Desval27/FormantKO/panels/COM/README.md

# COM

## Status

⚠️ Untested⚠️

<!--
## Documents
-->

## Gerber To Order

⚠️ Untested⚠️

- [Default](COM_71.0x132.5mm_for_Default.zip)
- [Elecrow](COM_71.0x132.5mm_for_Elecrow.zip)
- [FusionPCB](COM_71.0x132.5mm_for_FusionPCB.zip)
- [JLCPCB](COM_71.0x132.5mm_for_JLCPCB.zip)
- [PCBWay](COM_71.0x132.5mm_for_PCBWay.zip)

## Images

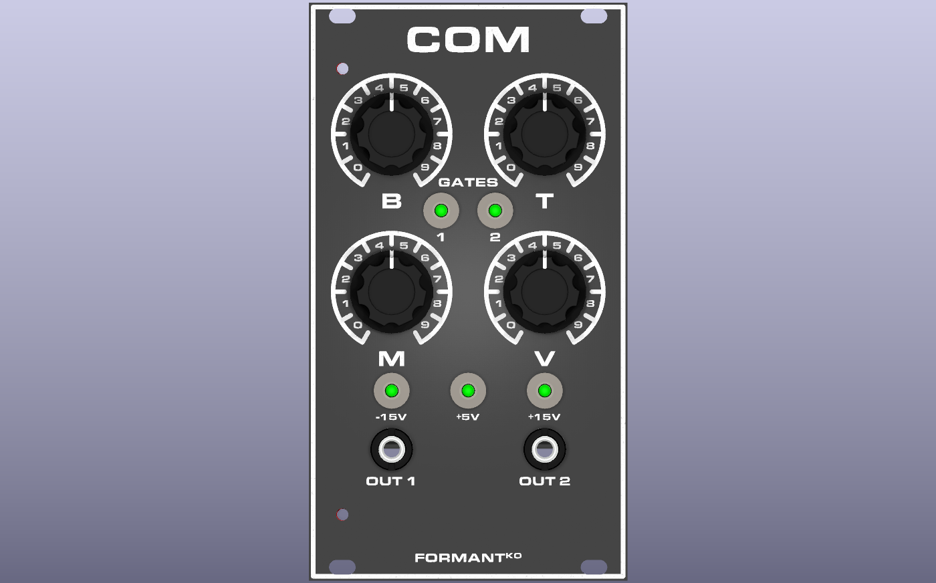
[picture p23: panels/COM/COM_front.png]
Rendered Panel Front


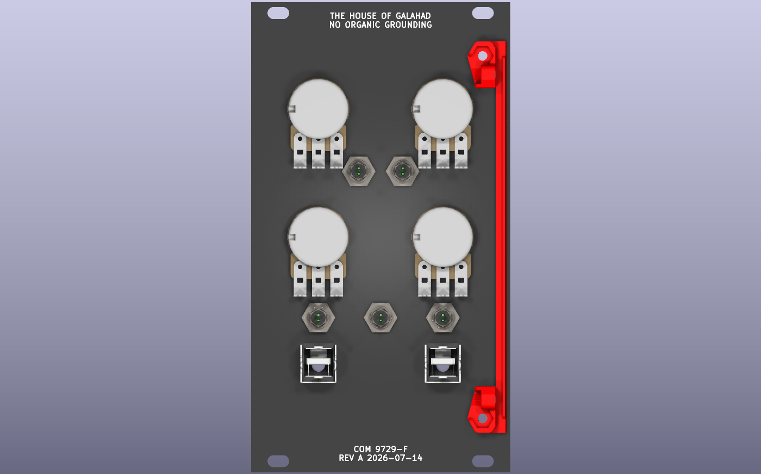
[picture p24: panels/COM/COM_back.png]
Rendered Panel Back
