Desval27/FormantKO/panels/DUAL_VCA/README.md

# DUAL-VCA

Format: 3U

## Status

⚠️ Untested⚠️

<!--
## Documents
-->

## Gerber To Order

⚠️ Untested⚠️

- [Default](gerber_to_order/DUAL_VCA_70.78x128.4mm_for_Default.zip)
- [Elecrow](gerber_to_order/DUAL_VCA_70.78x128.4mm_for_Elecrow.zip)
- [FusionPCB](gerber_to_order/DUAL_VCA_70.78x128.4mm_for_FusionPCB.zip)
- [JLCPCB](gerber_to_order/DUAL_VCA_70.78x128.4mm_for_JLCPCB.zip)
- [PCBWay](gerber_to_order/DUAL_VCA_70.78x128.4mm_for_PCBWay.zip)

## Images

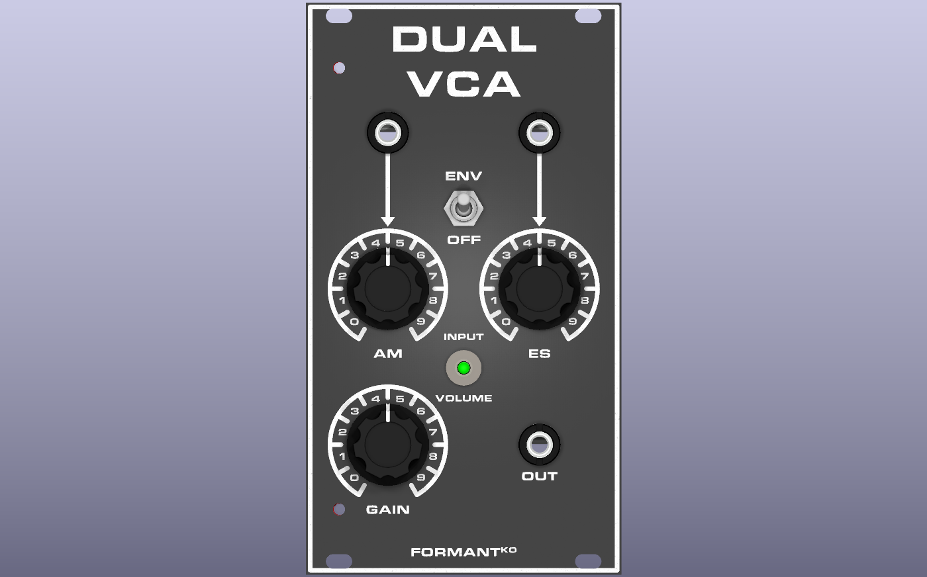
[picture p27: panels/DUAL_VCA/DUAL_VCA_front.png]
Rendered Panel Front


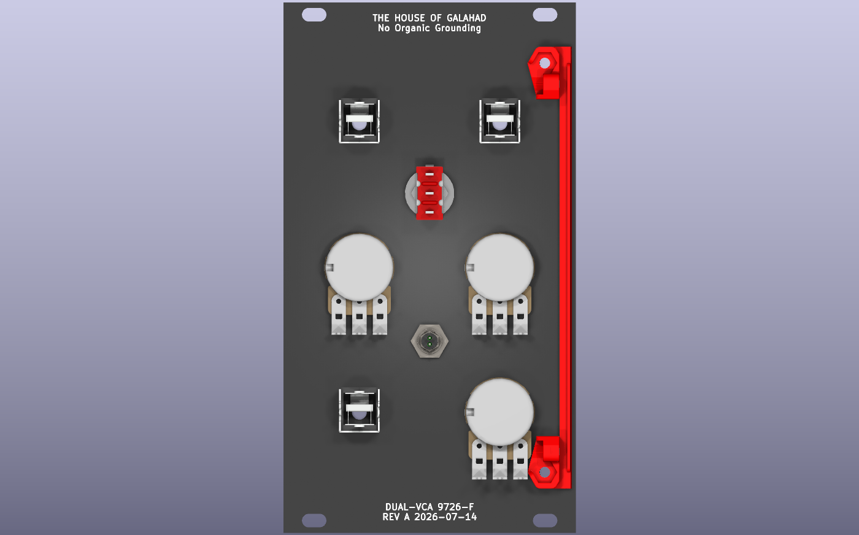
[picture p28: panels/DUAL_VCA/DUAL_VCA_back.png]
Rendered Panel Back
