Desval27/FormantKO/panels/ADSR/README.md

# ADSR

Formant: 3U

### Modifications

- Add external gate input.  This is normalized and will disconnect any existing internal gate bus assignment.

## Status

⚠️ Untested⚠️

## Gerber to Order

⚠️ Untested⚠️

- [Default](gerber_to_order/ADSR_70.78x128.4mm_for_Default.zip)
- [Elecrow](gerber_to_order/ADSR_70.78x128.4mm_for_Elecrow.zip)
- [FusionPCB](gerber_to_order/ADSR_70.78x128.4mm_for_FusionPCB.zip)
- [JLCPCB](gerber_to_order/ADSR_70.78x128.4mm_for_JLCPCB.zip)
- [PCBWay](gerber_to_order/ADSR_70.78x128.4mm_for_PCBWay.zip)

## Images

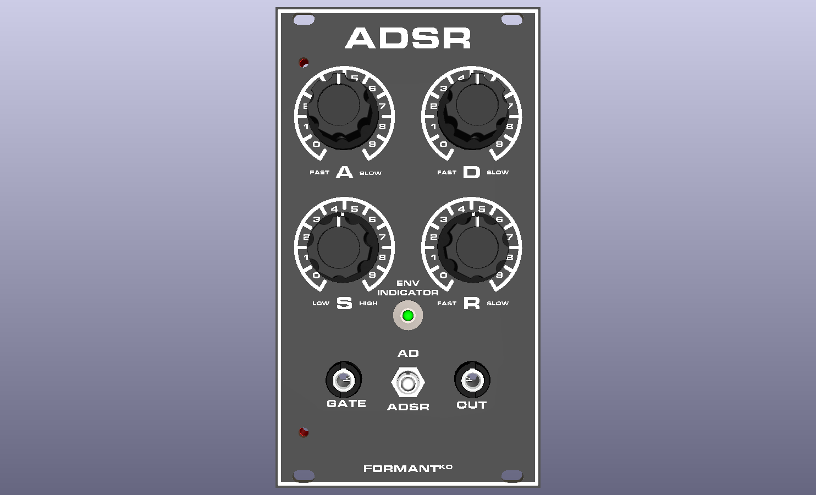
[picture p29: panels/ADSR/ADSR_front.png]
Rendered Panel Front


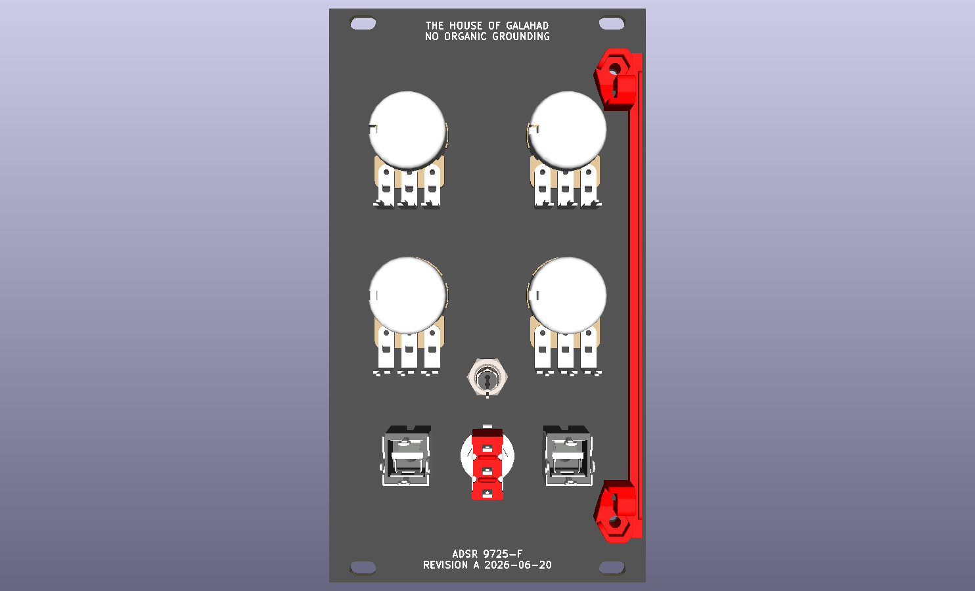
[picture p30: panels/ADSR/ADSR_back.png]
Rendered Panel Back
