Desval27/FormantKO/modules/SEQUENCER/README.md

# 256 Step Sequencer

A digital sequencer for voltage-controlled music synthesizers that can store and automatically play back up to 256 notes.

## Status

⚠️ Incomplete ⚠️

## Documents

- [English Translation](SEQUENCER_en.pdf)
- [Schematic](plots/SEQUENCER__schematic.pdf)
<!-- - [Assembly](plots/SEQUENCER__Assembly.pdf) -->
<!-- - [Interactive Bill of Materials](bom/ibom.html) -->

## Gerber to Order

⚠️ Untested ⚠️

## Images

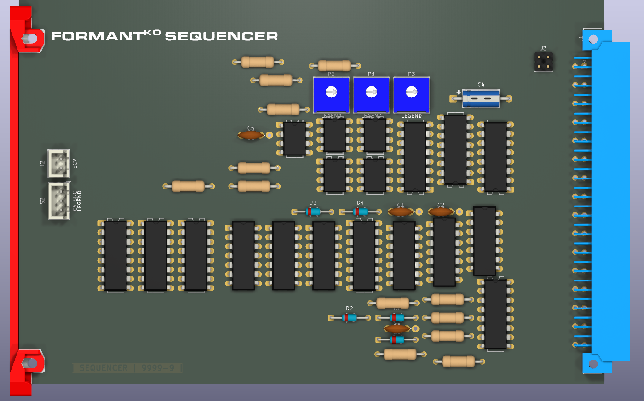
[picture p35: modules/SEQUENCER/SEQUENCER_top.png]
Rendered PCB Top


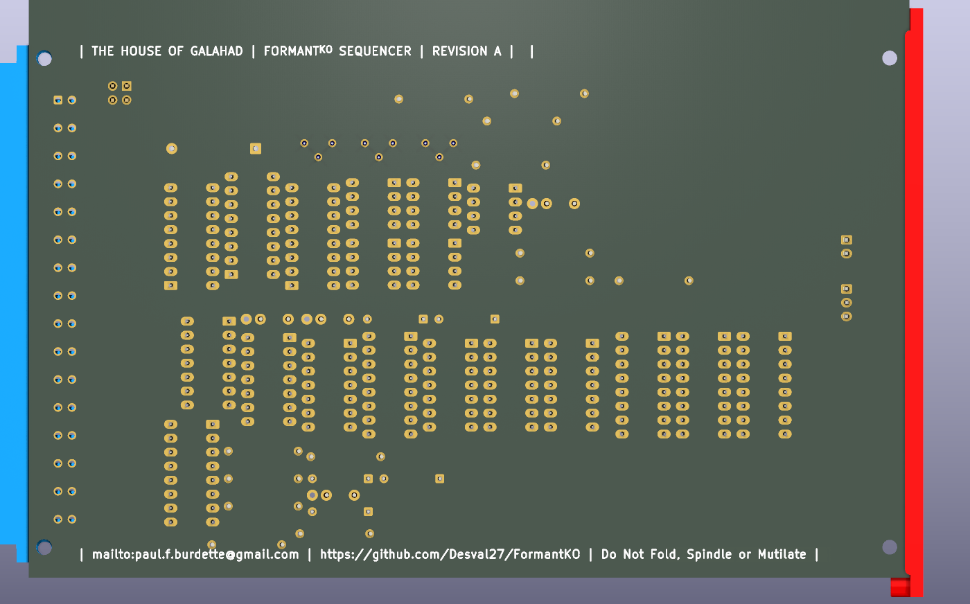
[picture p36: modules/SEQUENCER/SEQUENCER_bottom.png]
Rendered PCB Bottom
