Desval27/FormantKO/system/CARD_EXTENDER/README.md

# CARD-EXTENDER

A card extender is a simple debugging aid that plugs into the system backplane and provides a second connector into which a module is inserted. This moves the module outside of the card cage, allowing it to operate normally while all of its components and test points remain fully accessible.

For synthesizer systems such as the Formant, a card extender is invaluable during development, calibration, and troubleshooting. It allows oscilloscopes, multimeters, and logic analyzers to be connected without the module being buried inside the rack. Components can be adjusted, voltages measured, and signals traced while the module is running under normal operating conditions.

Although not required for everyday use, a card extender is one of the most useful service tools for anyone building, repairing, or modifying Formant modules.

## STATUS

⚠️ Untested⚠️

But possibly ready to get first samples...

## Documents

- [Schematic](plots/CARD_EXTENDER__schematic.pdf)
- [Assembly](plots/CARD_EXTENDER__Assembly.pdf)
- [Interactive Bill of Materials](bom/ibom.html)

## Gerber to Order

- [Default](gerber_to_order/CARD_EXTENDER_160.0x100.0mm_for_Default.zip)
- [Elecrow](gerber_to_order/CARD_EXTENDER_160.0x100.0mm_for_Elecrow.zip)
- [FusionPCB](gerber_to_order/CARD_EXTENDER_160.0x100.0mm_for_FusionPCB.zip)
- [JLCPCB](gerber_to_order/CARD_EXTENDER_160.0x100.0mm_for_JLCPCB.zip)
- [PCBWay](gerber_to_order/CARD_EXTENDER_160.0x100.0mm_for_PCBWay.zip)

## Images

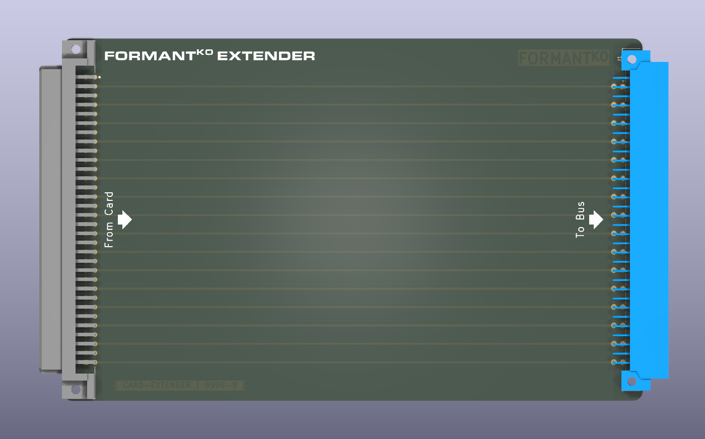
[picture p37: system/CARD_EXTENDER/CARD_EXTENDER_top.png]
Rendered PCB Top


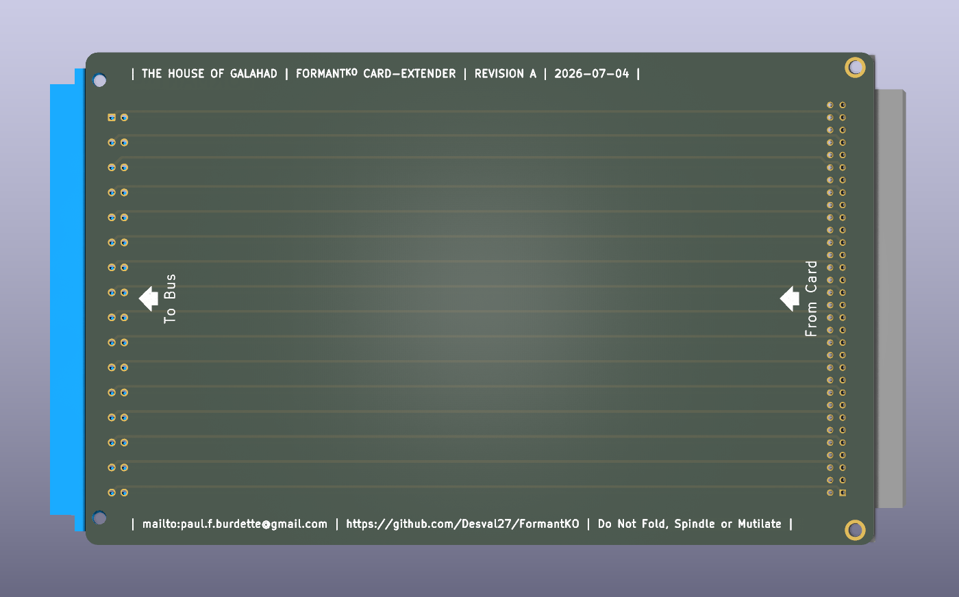
[picture p38: system/CARD_EXTENDER/CARD_EXTENDER_bottom.png]
Rendered PCB Bottom
