Desval27/FormantKO/modules/NOISE_DNG/README.md

# NOISE-DNG

## Status

⚠️ Untested ⚠️

## Documents

- [Translated Document](NOISE_DNG_translated.pdf)
- [Schematic](NOISE_DNG_schematic.pdf)
- [Assembly](plots/NOISE_DNG__Assembly.pdf)
- [Interactive Bill of Materials](bom/ibom.html)

## Gerber to Order

⚠️ Untested ⚠️

- [Default](gerber_to_order/NOISE_DNG_100.0x40.0mm_for_Default.zip)
- [Elecrow](gerber_to_order/NOISE_DNG_100.0x40.0mm_for_Elecrow.zip)
- [FusionPCB](gerber_to_order/NOISE_DNG_100.0x40.0mm_for_FusionPCB.zip)
- [JLCPCB](gerber_to_order/NOISE_DNG_100.0x40.0mm_for_JLCPCB.zip)
- [PCBWay](gerber_to_order/NOISE_DNG_100.0x40.0mm_for_PCBWay.zip)

## Images

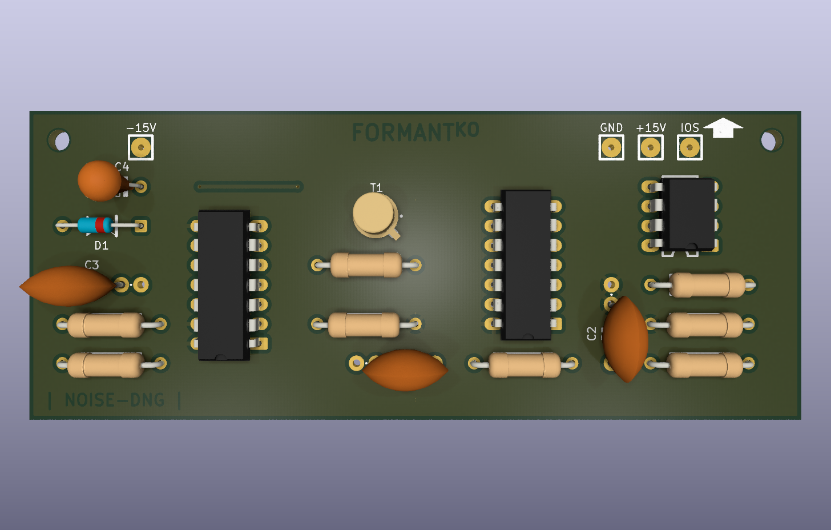
[picture p41: modules/NOISE_DNG/NOISE_DNG_top.png]
Rendered PCB Top


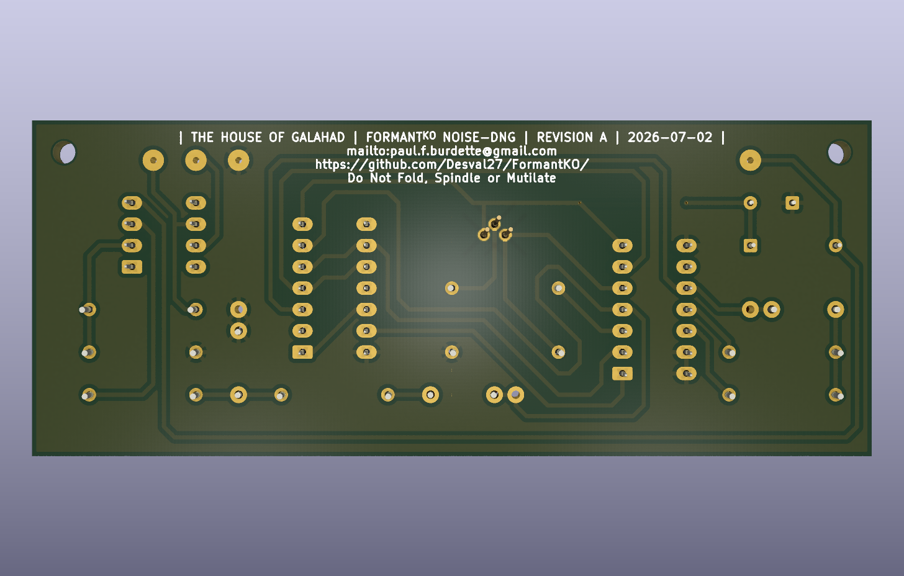
[picture p42: modules/NOISE_DNG/NOISE_DNG_bottom.png]
Rendered PCB Bottom
