Desval27/FormantKO/modules/VCF_24/README.md

# VCF 24dB

## Status

⚠️ Incomplete ⚠️

## Documents

<!--
- [Schematic](schematic.pdf)
- [Assembly](plots/VCF_24__Assembly.pdf)
- [Interactive Bill of Materials](bom/ibom.html)
-->

## Gerber to Order

⚠️ Untested ⚠️

## Images

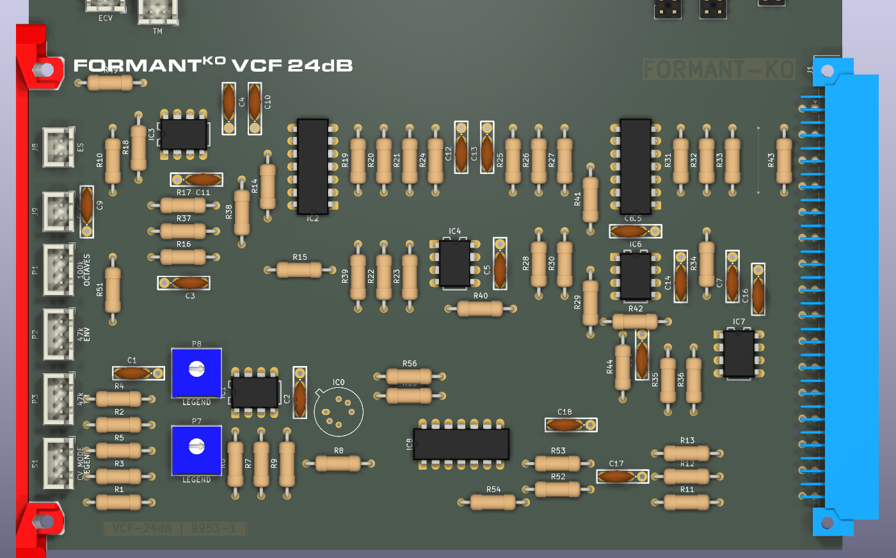
[picture p43: modules/VCF_24/VCF_24_top.png]
Rendered PCB Top


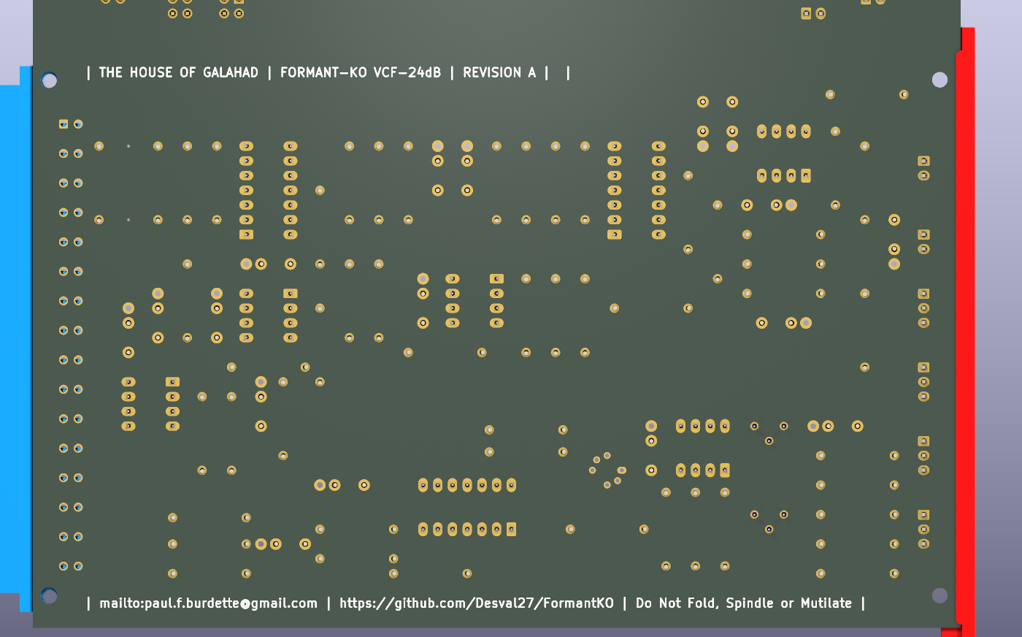
[picture p44: modules/VCF_24/VCF_24_bottom.png]
Rendered PCB Bottom
