Desval27/FormantKO/modules/VCF_12/README.md

# VCF 12dB

## Status

⚠️ Untested ⚠️

## Documents

- [Schematic](schematic.pdf)
- [Assembly](plots/VCF_12__Assembly.pdf)
- [Interactive Bill of Materials](bom/ibom.html)

## Gerber to Order

⚠️ Untested ⚠️

- [Default](gerber_to_order/VCF_12_160.0x233.35mm_for_Default.zip)
- [Elecrow](gerber_to_order/VCF_12_160.0x233.35mm_for_Elecrow.zip)
- [FusionPCB](gerber_to_order/VCF_12_160.0x233.35mm_for_FusionPCB.zip)
- [JLCPCB](gerber_to_order/VCF_12_160.0x233.35mm_for_JLCPCB.zip)
- [PCBWay](gerber_to_order/VCF_12_160.0x233.35mm_for_PCBWay.zip)

## Images

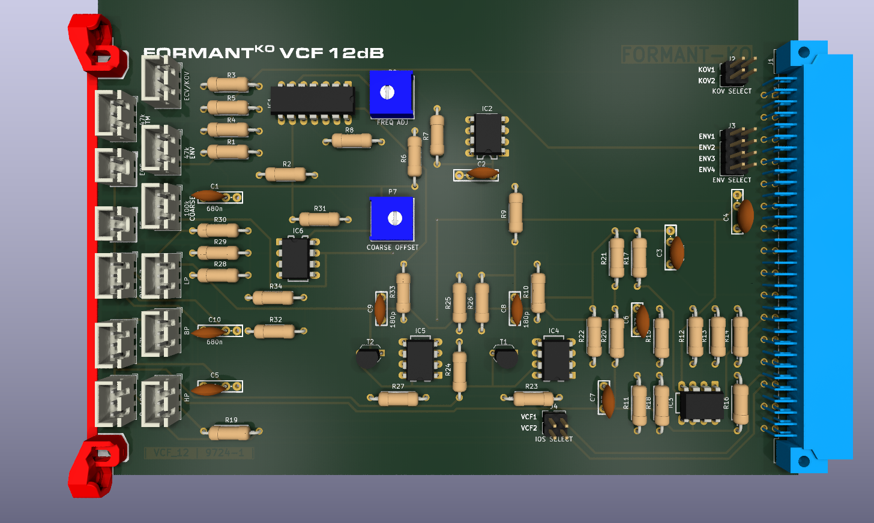
[picture p45: modules/VCF_12/VCF_12_top.png]
Rendered PCB Top


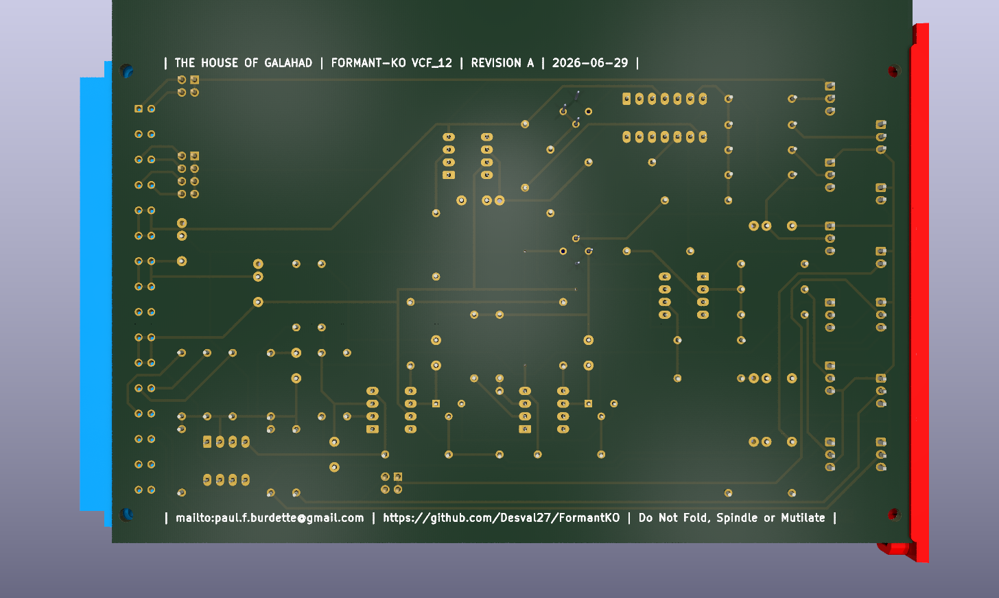
[picture p46: modules/VCF_12/VCF_12_bottom.png]
Rendered PCB Bottom
