Desval27/FormantKO/panels/MULTIPLE_JACKS_3U/README.md

# MULTIPLE-JACKS 3U

## Status

⚠️ Untested⚠️

## Documents

- [Assembly](plots/MULTIPLE_JACKS_3U__Assembly.pdf)

## Gerber To Order

- [Default](gerber_to_order/MULTIPLE_JACKS_3U_70.78x128.4mm_for_Default.zip)
- [Elecrow](gerber_to_order/MULTIPLE_JACKS_3U_70.78x128.4mm_for_Elecrow.zip)
- [FusionPCB](gerber_to_order/MULTIPLE_JACKS_3U_70.78x128.4mm_for_FusionPCB.zip)
- [JLCPCB](gerber_to_order/MULTIPLE_JACKS_3U_70.78x128.4mm_for_JLCPCB.zip)
- [PCBWay](gerber_to_order/MULTIPLE_JACKS_3U_70.78x128.4mm_for_PCBWay.zip)

## Images

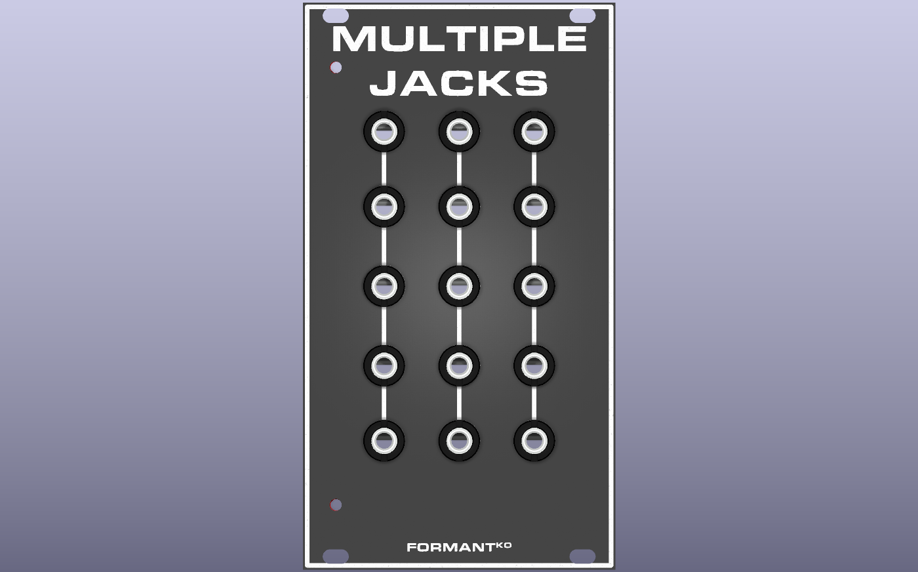
[picture p51: panels/MULTIPLE_JACKS_3U/MULTIPLE_JACKS_3U_front.png]
Rendered Front Panel

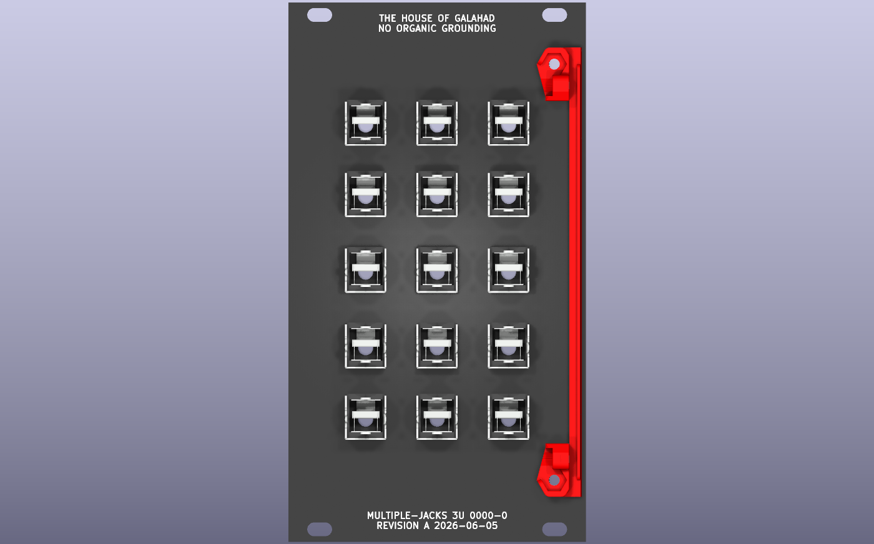
[picture p52: panels/MULTIPLE_JACKS_3U/MULTIPLE_JACKS_3U_back.png]
Rendered Back Panel
