Desval27/FormantKO/panels/MULTIPLE_JACKS_6U/README.md

# MULTIPLE-JACKS 6U

## Status

⚠️ Untested⚠️

## Documents

- [Assembly](plots/MULTIPLE_JACKS_6U__Assembly.pdf)

## Gerber To Order

- [Default](gerber_to_order/MULTIPLE_JACKS_6U_70.78x261.75mm_for_Default.zip)
- [Elecrow](gerber_to_order/MULTIPLE_JACKS_6U_70.78x261.75mm_for_Elecrow.zip)
- [FusionPCB](gerber_to_order/MULTIPLE_JACKS_6U_70.78x261.75mm_for_FusionPCB.zip)
- [JLCPCB](gerber_to_order/MULTIPLE_JACKS_6U_70.78x261.75mm_for_JLCPCB.zip)
- [PCBWay](gerber_to_order/MULTIPLE_JACKS_6U_70.78x261.75mm_for_PCBWay.zip)

## Images

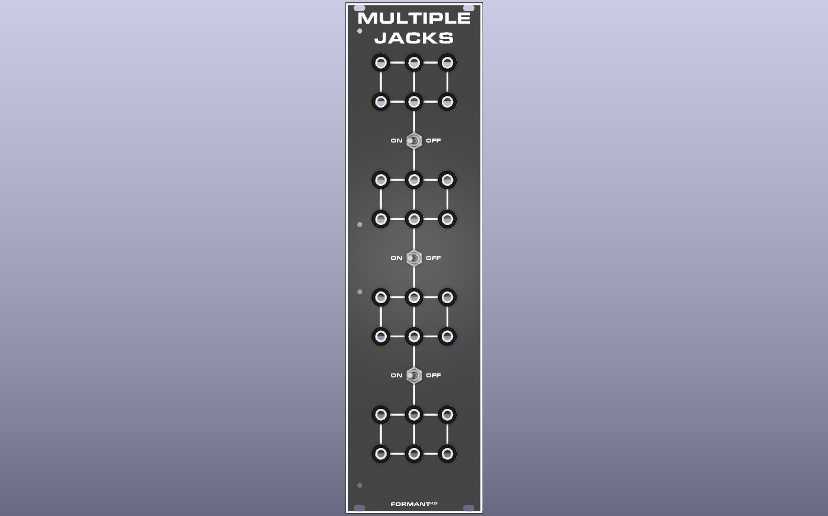
[picture p53: panels/MULTIPLE_JACKS_6U/MULTIPLE_JACKS_6U_front.png]
Rendered Front Panel

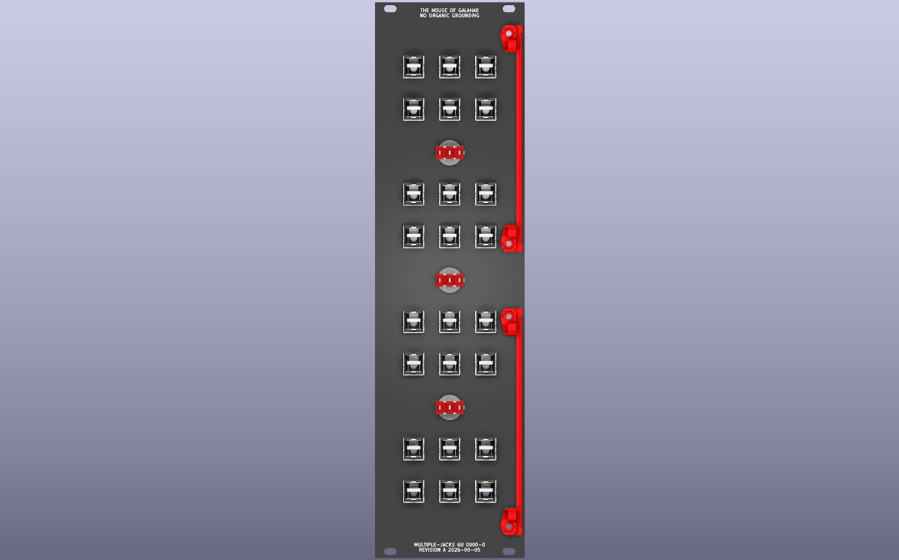
[picture p54: panels/MULTIPLE_JACKS_6U/MULTIPLE_JACKS_6U_back.png]
Rendered Back Panel
