Desval27/FormantKO/panels/PHASE_SHIFTER/README.md

# PHASE-SHIFTER

## Status

⚠️ Untested⚠️

## Documents

- [Assembly](plots/PHASE_SHIFTER__Assembly.pdf)

## Gerber To Order

- [Default](gerber_to_order/PHASE_SHIFTER_70.78x128.4mm_for_Default.zip)
- [Elecrow](gerber_to_order/PHASE_SHIFTER_70.78x128.4mm_for_Elecrow.zip)
- [FusionPCB](gerber_to_order/PHASE_SHIFTER_70.78x128.4mm_for_FusionPCB.zip)
- [JLCPCB](gerber_to_order/PHASE_SHIFTER_70.78x128.4mm_for_JLCPCB.zip)
- [PCBWay](gerber_to_order/PHASE_SHIFTER_70.78x128.4mm_for_PCBWay.zip)

## Images

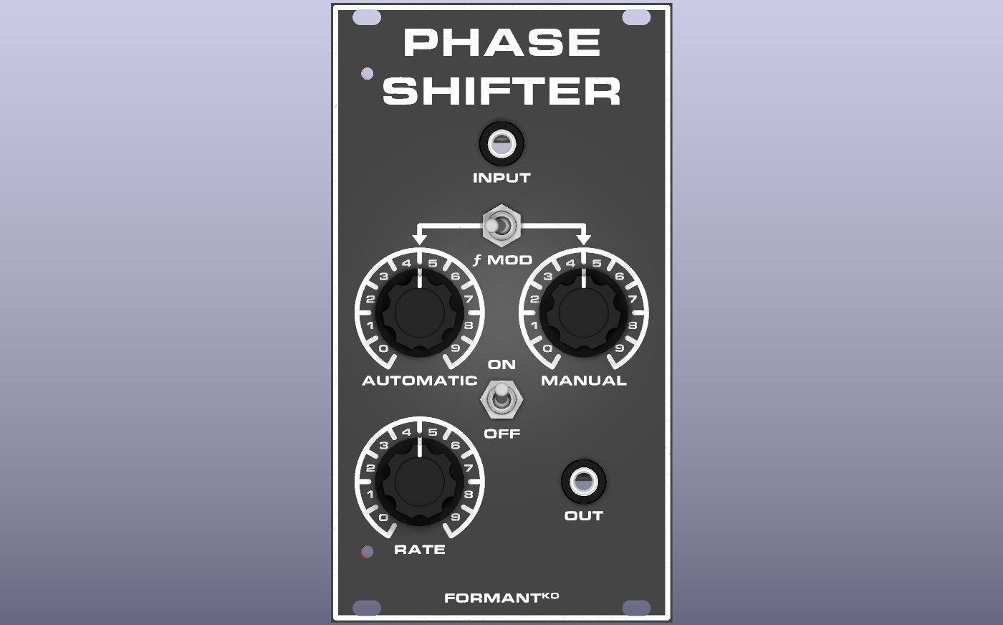
[picture p55: panels/PHASE_SHIFTER/PHASE_SHIFTER_front.png]
Rendered Front Panel

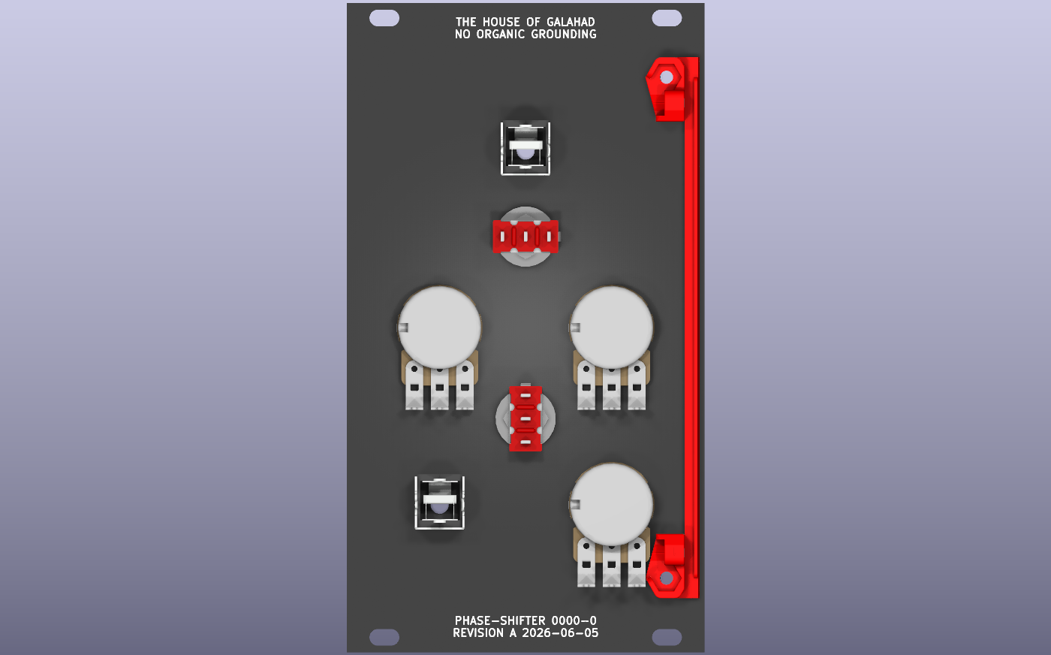
[picture p56: panels/PHASE_SHIFTER/PHASE_SHIFTER_back.png]
Rendered Back Panel
