Desval27/FormantKO/modules/RING_MODULATOR/README.md

# RING-MODULATOR

## STATUS

⚠️ Incomplete⚠️

## Documents

- [Translated Source](RING_MODULATOR_translated.pdf)
- [Schematic](RING_MODULATOR.pdf)
- [Assembly](plots/RING_MODULATOR__Assembly.pdf)
- [Interactive Bill of Materials](bom/ibom.html)

## Gerber to Order

⚠️ Untested⚠️

- [Default](gerber_to_order/RING_MODULATOR_160.0x100.0mm_for_Default.zip)
- [Elecrow](gerber_to_order/RING_MODULATOR_160.0x100.0mm_for_Elecrow.zip)
- [FusionPCB](gerber_to_order/RING_MODULATOR_160.0x100.0mm_for_FusionPCB.zip)
- [JLCPCB](gerber_to_order/RING_MODULATOR_160.0x100.0mm_for_JLCPCB.zip)
- [PCBWay](gerber_to_order/RING_MODULATOR_160.0x100.0mm_for_PCBWay.zip)

## Images

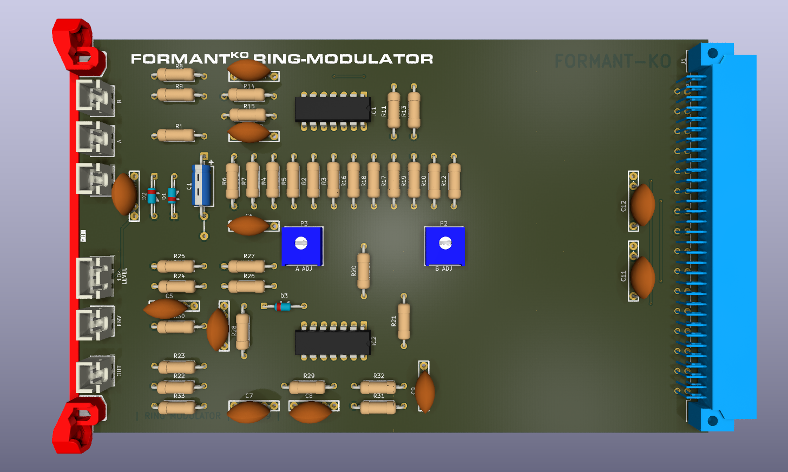
[picture p57: modules/RING_MODULATOR/RING_MODULATOR_top.png]
Rendered PCB Top

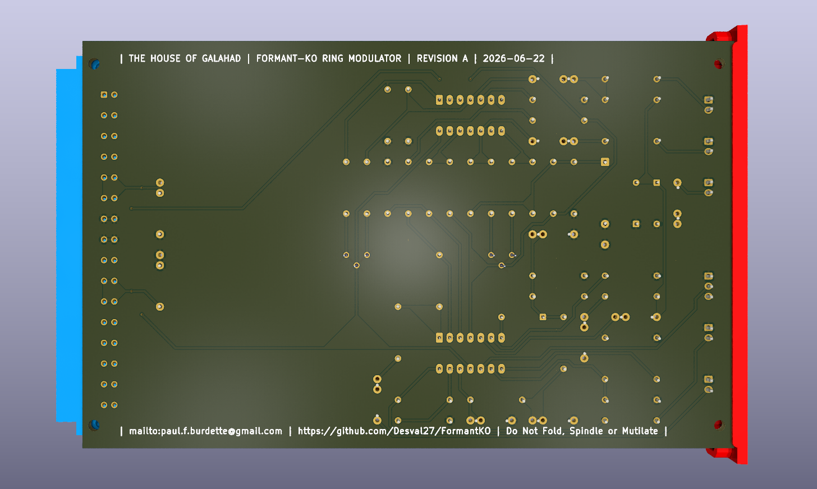
[picture p58: modules/RING_MODULATOR/RING_MODULATOR_bottom.png]
Rendered PCB Bottom
