Desval27/FormantKO/panels/RING_MODULATOR/README.md

# RING-MODULATOR

## Status

⚠️Incomplete⚠️

## Documents

- [Assembly](plots/RING_MODULATOR__Assembly.pdf)

## Gerber To Order

- [Default](gerber_to_order/RING_MODULATOR_70.78x128.4mm_for_Default.zip)
- [Elecrow](gerber_to_order/RING_MODULATOR_70.78x128.4mm_for_Elecrow.zip)
- [FusionPCB](gerber_to_order/RING_MODULATOR_70.78x128.4mm_for_FusionPCB.zip)
- [JLCPCB](gerber_to_order/RING_MODULATOR_70.78x128.4mm_for_JLCPCB.zip)
- [PCBWay](gerber_to_order/RING_MODULATOR_70.78x128.4mm_for_PCBWay.zip)

⚠️Untested⚠️

## Images

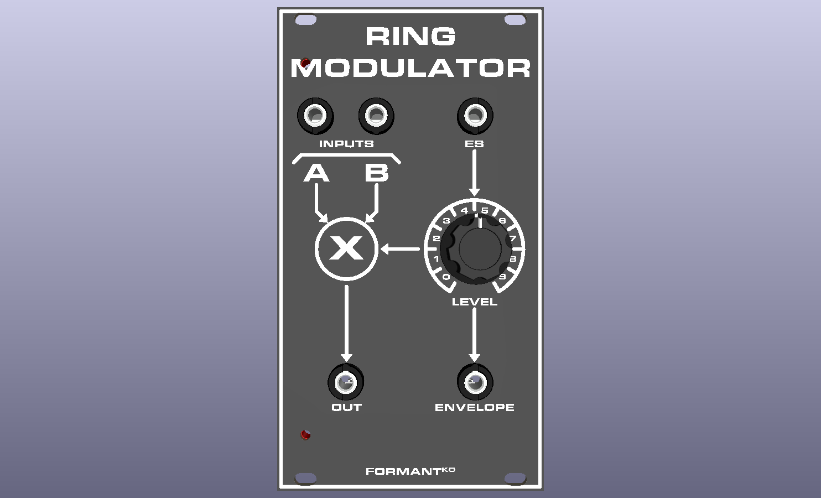
[picture p59: panels/RING_MODULATOR/RING_MODULATOR_front.png]
Rendered Front Panel

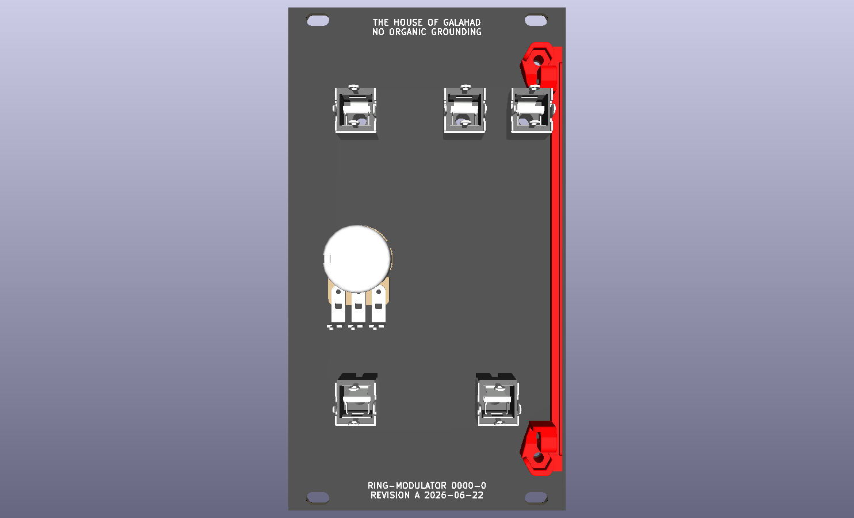
[picture p60: panels/RING_MODULATOR/RING_MODULATOR_back.png]
Rendered Back Panel
