Desval27/FormantKO/modules/NOISE_CNC/README.md

# NOISE EXTENSION - COLOURED NOISE CONTROL

## Status

⚠️ Incomplete⚠️

## Documents

- [Translated Source](NOISE_CNC_translated.pdf)
- [Schematic](NOISE_CNC.pdf)
- [Assembly](plots/NOISE_CNC__Assembly.pdf)
- [Interactive Bill of Materials](bom/ibom.html)

## Gerber to Order

⚠️ Untested⚠️

- [Default](gerber_to_order/NOISE_CNC_100.0x38.0mm_for_Default.zip)
- [Elecrow](gerber_to_order/NOISE_CNC_100.0x38.0mm_for_Elecrow.zip)
- [FusionPCB](gerber_to_order/NOISE_CNC_100.0x38.0mm_for_FusionPCB.zip)
- [JLCPCB](gerber_to_order/NOISE_CNC_100.0x38.0mm_for_JLCPCB.zip)
- [PCBWay](gerber_to_order/NOISE_CNC_100.0x38.0mm_for_PCBWay.zip)

## Images

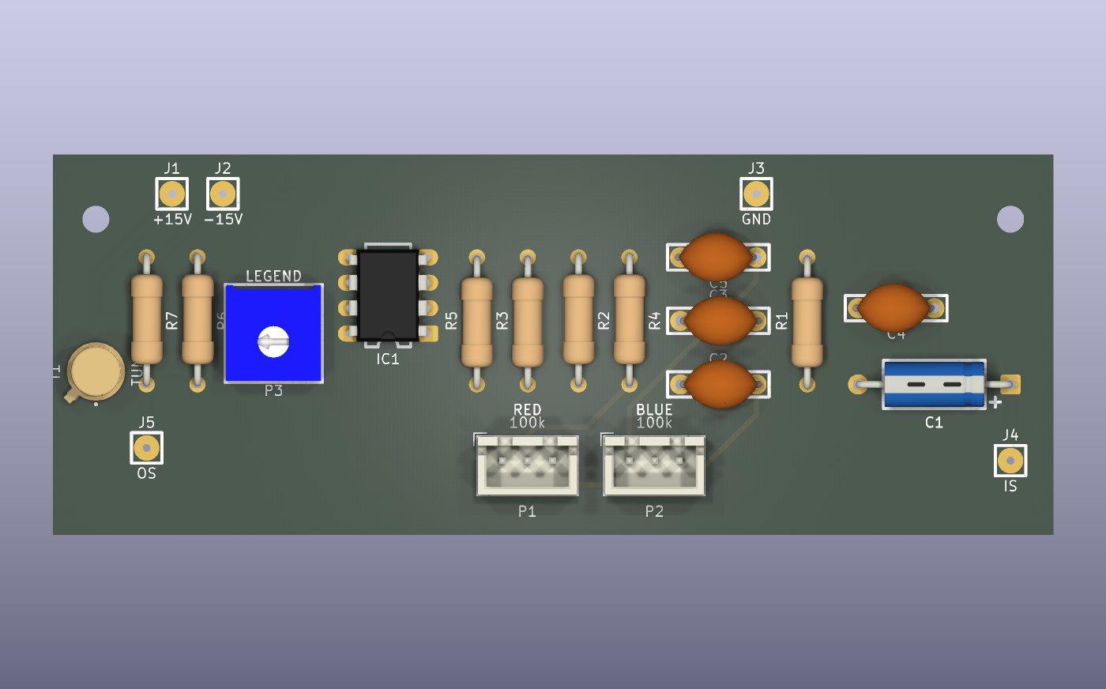
[picture p61: modules/NOISE_CNC/NOISE_CNC_top.png]
Rendered PCB Top


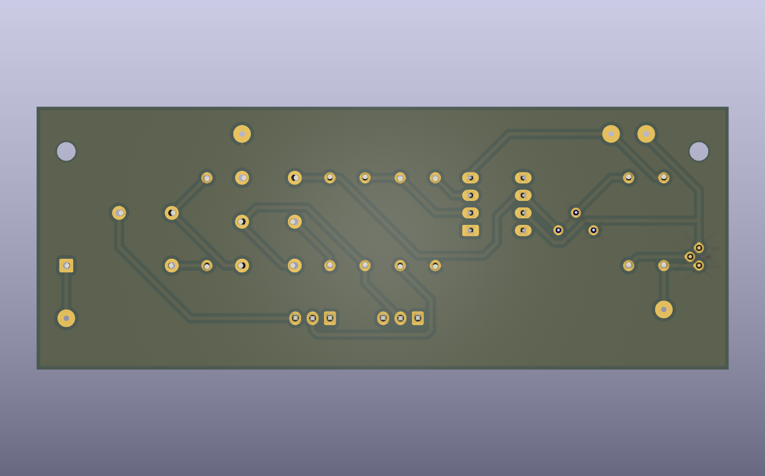
[picture p62: modules/NOISE_CNC/NOISE_CNC_bottom.png]
Rendered PCB Bottom
