Desval27/FormantKO/system/KB_DIV/README.md

# KEYBOARD DIVIDER

## Status

⚠️ Incomplete⚠️

## Documents

- [Schematic](KB_DIV.pdf)
- [Assembly](plots/KB_DIV__Assembly.pdf)
- [Interactive Bill of Materials](bom/ibom.html)

## Gerber to Order

⚠️ Untested⚠️

- [Default](gerber_to_order/KB_DIV_171.45x33.02mm_for_Default.zip)
- [Elecrow](gerber_to_order/KB_DIV_171.45x33.02mm_for_Elecrow.zip)
- [FusionPCB](gerber_to_order/KB_DIV_171.45x33.02mm_for_FusionPCB.zip)
- [JLCPCB](gerber_to_order/KB_DIV_171.45x33.02mm_for_JLCPCB.zip)
- [PCBWay](gerber_to_order/KB_DIV_171.45x33.02mm_for_PCBWay.zip)

## Images

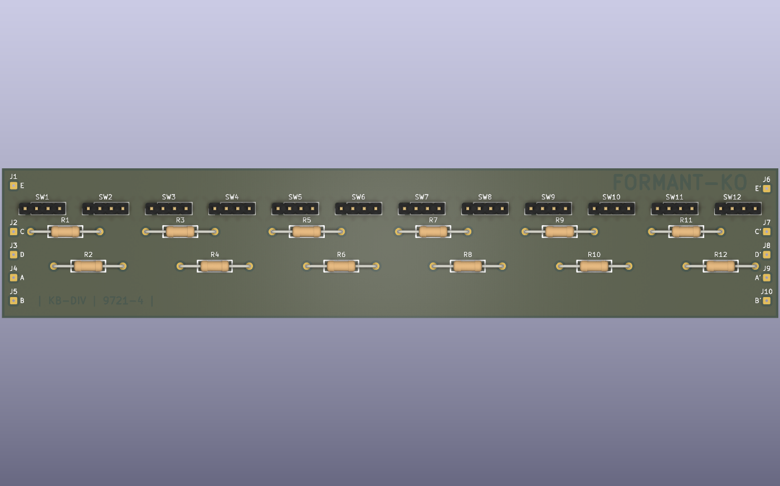
[picture p63: system/KB_DIV/KB_DIV_top.png]
Rendered PCB Top


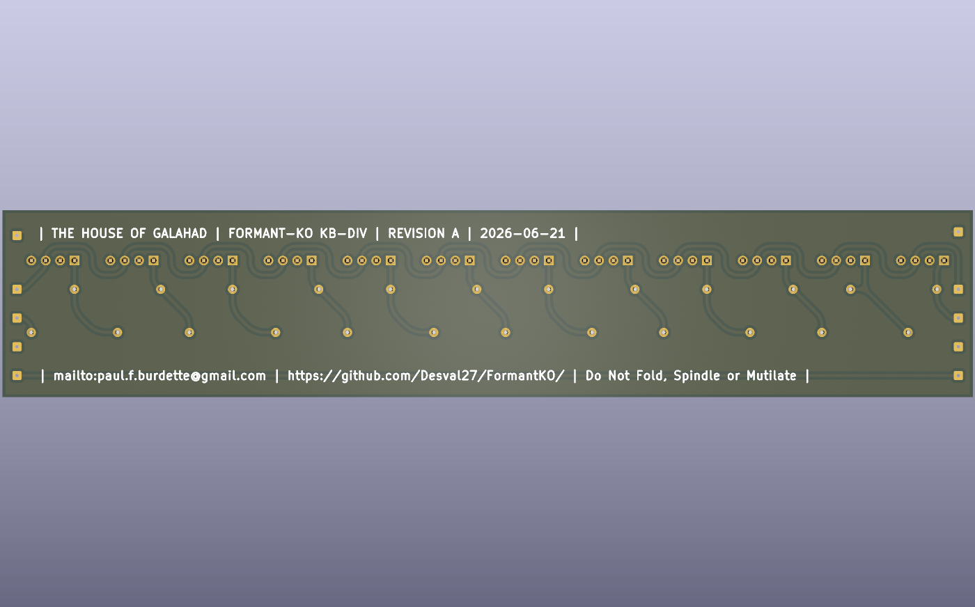
[picture p64: system/KB_DIV/KB_DIV_bottom.png]
Rendered PCB Bottom
