Desval27/FormantKO/modules/COM_EXT/README.md

# COM EXTENSIONS

## Status

0% Complete

- [ ] Schematic
- [ ] Schematic Additions
- [ ] Schematic Review
- [ ] PCB Placement
- [ ] PCB Routing
- [ ] PCB Review
- [ ] Sample
- [ ] Build
- [ ] Calibrated
- [ ] Tested

## Documents

[Translated Source](COM_EXT.pdf)

## Interactive Bill of Materials

## Gerber to Order

## Images

<!-- ![Rendered PCB](TEMPLATE.png "Rendered PCB") -->
<!-- ![Rendered PCB](TEMPLATE.png "Rendered PCB") -->
