Desval27/FormantKO/modules/01_KBI/README.md

# KBI

Keyboard Interface

## Status

⚠️ Incomplete⚠️

## Documents

## Interactive Bill of Materials

## Gerber to Order

## Images
