Desval27/FormantKO/modules/02_KB_DIV/README.md

# KEYBOARD DIVIDER

## Status

⚠️ Incomplete⚠️

## Documents

## Interactive Bill of Materials

## Gerber to Order

## Images
