Desval27/FormantKO/modules/03_INTF_RCVR/README.md

# INTERFACE RECEIVER

## Status

⚠️ Incomplete⚠️

50% Complete

- [x] Schematic
- [ ] Schematic Additions
- [x] Schematic Review
- [x] PCB Placement
- [x] PCB Routing
- [x] PCB Review
- [ ] Sample
- [ ] Build
- [ ] Calibrated
- [ ] Tested

## Documents

## Interactive Bill of Materials

## Gerber to Order

## Images

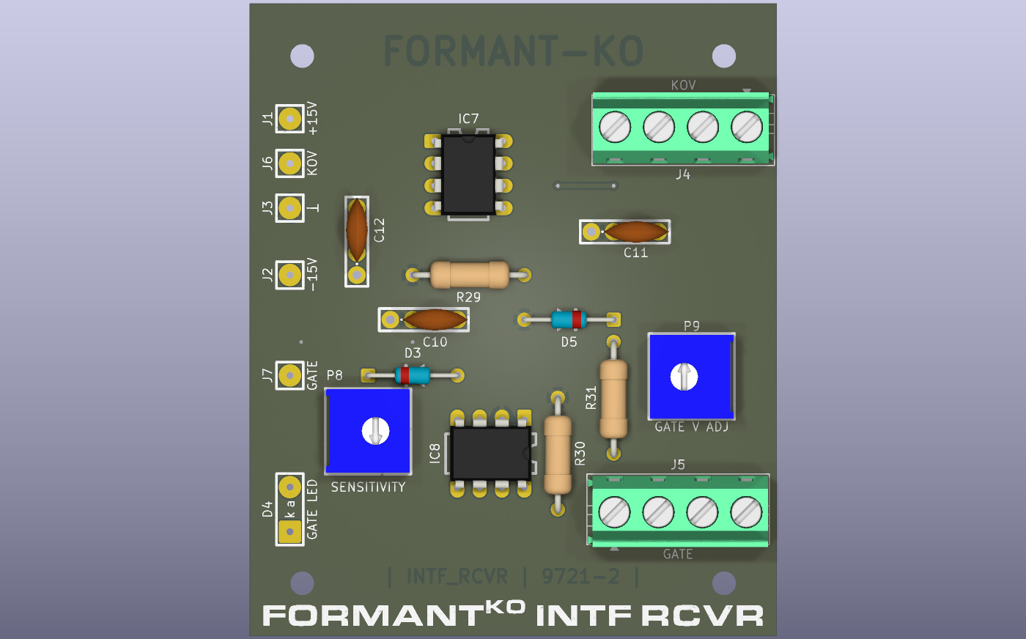
[picture p65: modules/03_INTF_RCVR/INTF_RCVR_top.png]
Rendered PCB Top


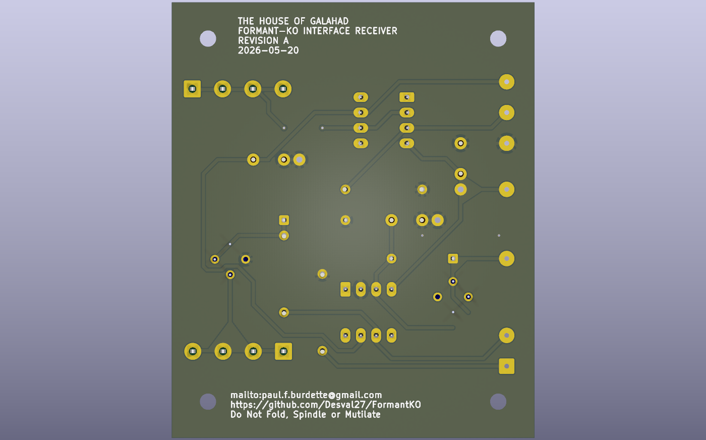
[picture p66: modules/03_INTF_RCVR/INTF_RCVR_bottom.png]
Rendered PCB Bottom
