Desval27/FormantKO/modules/05_VCO/README.md

# VCO

## Status

⚠️ Incomplete⚠️

0% Complete

- [ ] Schematic
- [ ] Schematic Additions
- [ ] Schematic Review
- [ ] PCB Placement
- [ ] PCB Routing
- [ ] PCB Review
- [ ] Sample
- [ ] Build
- [ ] Calibrated
- [ ] Tested

## Documents

## Interactive Bill of Materials

## Gerber to Order

## Images

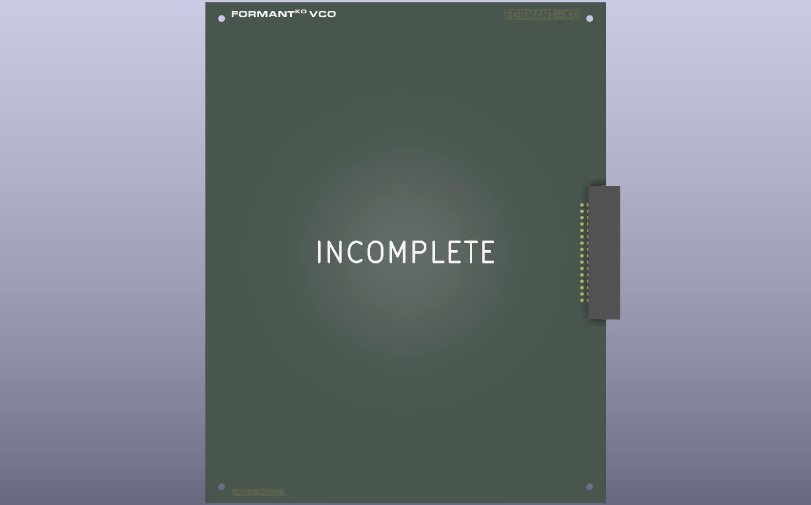
[picture p67: modules/05_VCO/VCO_top.png]
Rendered PCB Top


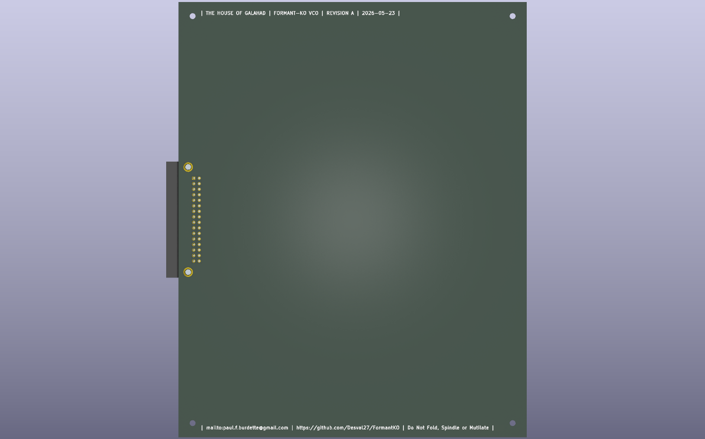
[picture p68: modules/05_VCO/VCO_bottom.png]
Rendered PCB Bottom
