Desval27/FormantKO/modules/06_VCF_12/README.md

# VCF 12dB

## Status

⚠️ Incomplete⚠️

0% Complete

- [ ] Schematic
- [ ] Schematic Additions
- [ ] Schematic Review
- [ ] PCB Placement
- [ ] PCB Routing
- [ ] PCB Review
- [ ] Sample
- [ ] Build
- [ ] Calibrated
- [ ] Tested

## Documents

## Interactive Bill of Materials

## Gerber to Order

## Images

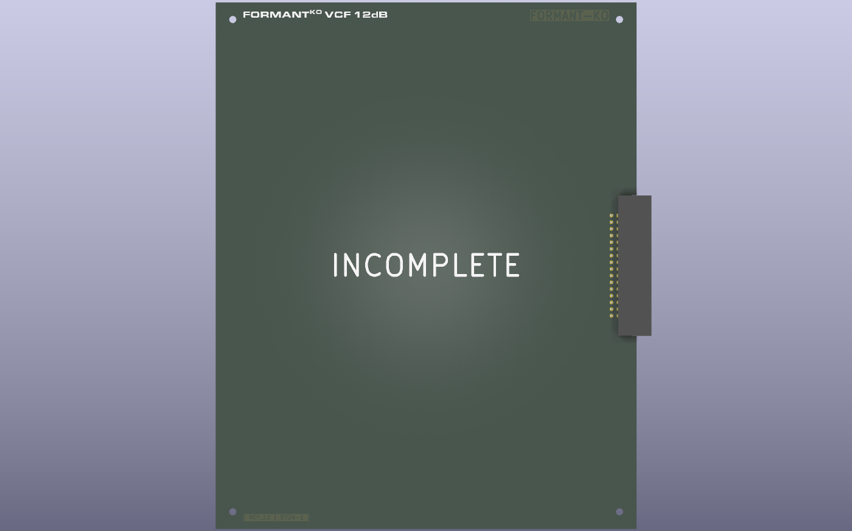
[picture p69: modules/06_VCF_12/VCF_12_top.png]
Rendered PCB Top


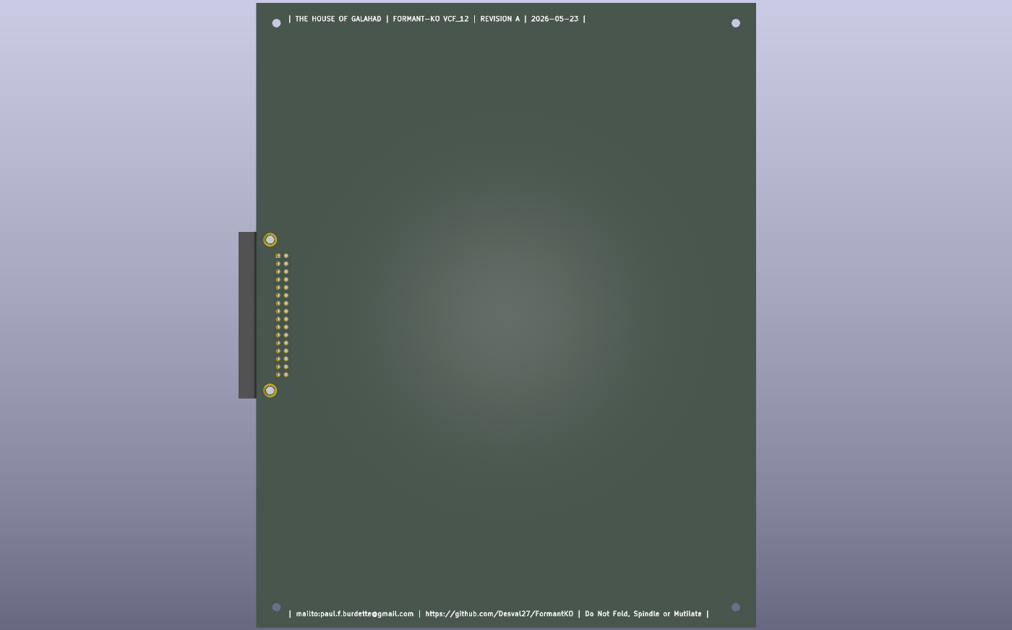
[picture p70: modules/06_VCF_12/VCF_12_bottom.png]
Rendered PCB Bottom
