Desval27/FormantKO/panels/PSU_B/README.md

# PSU-B

## Status

Incomplete

## Documents

- [Assembly](plots/PSU_B__Assembly.pdf)

## Gerber To Order

⚠️ Untested⚠️

- [Default](PSU_B_71.0x132.5mm_for_Default.zip)
- [Elecrow](PSU_B_71.0x132.5mm_for_Elecrow.zip)
- [FusionPCB](PSU_B_71.0x132.5mm_for_FusionPCB.zip)
- [JLCPCB](PSU_B_71.0x132.5mm_for_JLCPCB.zip)
- [PCBWay](PSU_B_71.0x132.5mm_for_PCBWay.zip)

## Images

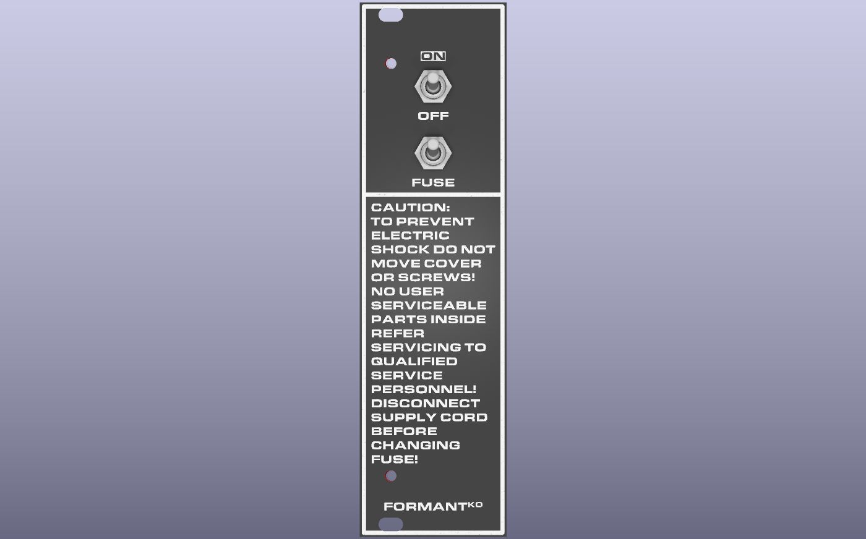
[picture p71: panels/PSU_B/PSU_B_front.png]
Rendered Panel Front


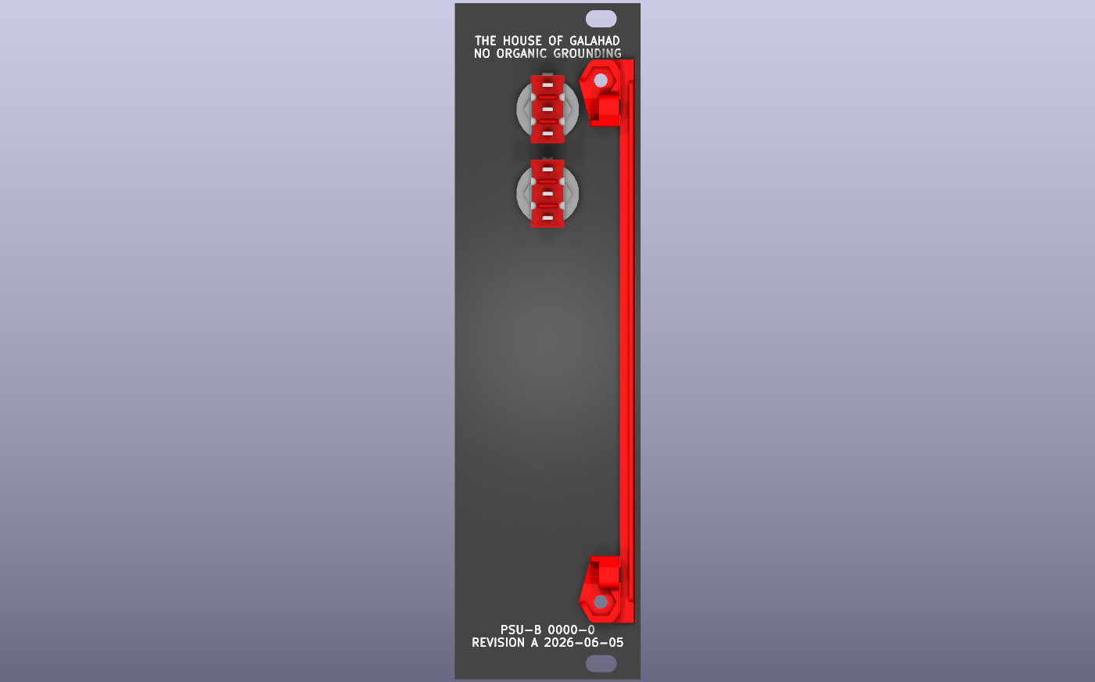
[picture p72: panels/PSU_B/PSU_B_back.png]
Rendered Panel Back
