Desval27/FormantKO/panels/KBI/README.md

# KEYBOARD-INTERFACE

## Status

Incomplete

## Documents

- [Assembly](plots/KBI__Assembly.pdf)

## Gerber To Order

⚠️ Untested⚠️

- [Default](KBI_71.0x132.5mm_for_Default.zip)
- [Elecrow](KBI_71.0x132.5mm_for_Elecrow.zip)
- [FusionPCB](KBI_71.0x132.5mm_for_FusionPCB.zip)
- [JLCPCB](KBI_71.0x132.5mm_for_JLCPCB.zip)
- [PCBWay](KBI_71.0x132.5mm_for_PCBWay.zip)

## Images

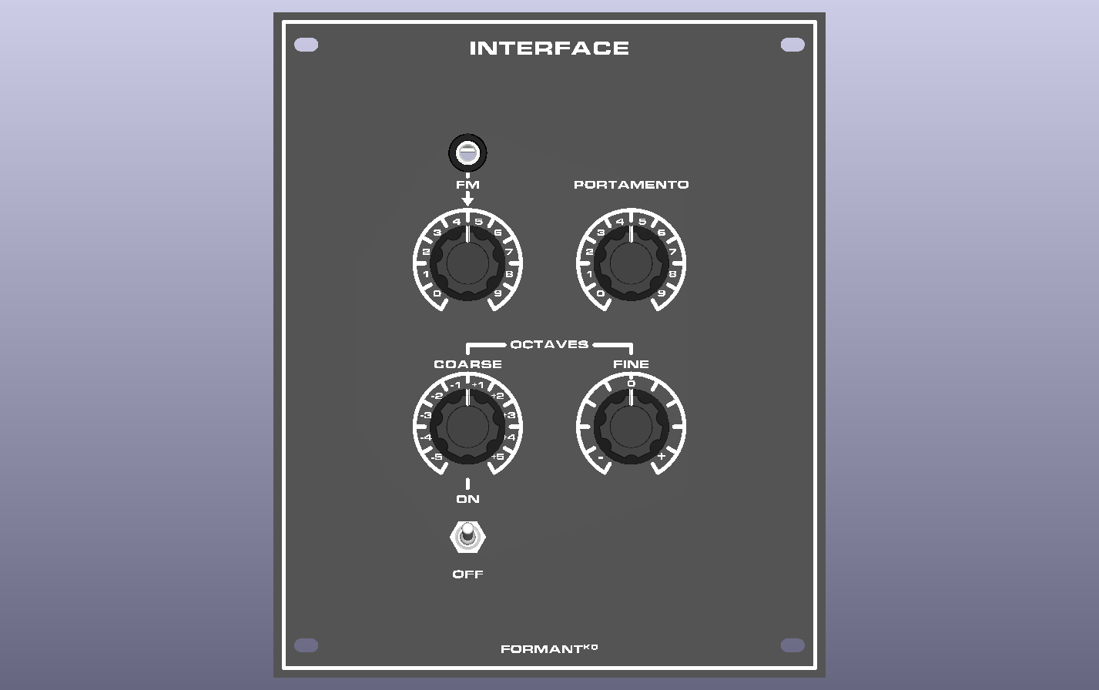
[picture p73: panels/KBI/KBI_front.png]
Rendered Panel Front


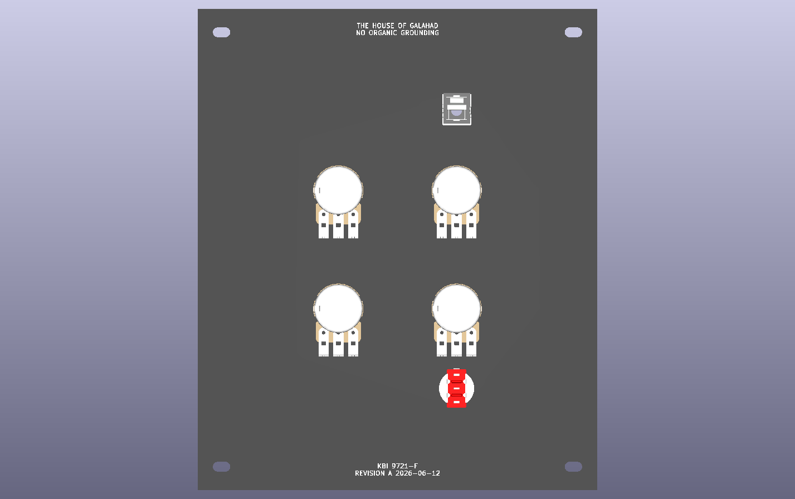
[picture p74: panels/KBI/KBI_back.png]
Rendered Panel Back
