Desval27/FormantKO/panels/KBI_EXT/README.md

# EXTENDED KEYBOARD INTERFACE

## Status

Incomplete

## Documents

- [Assembly](plots/KBI_EXT__Assembly.pdf)

## Gerber To Order

⚠️ Untested⚠️

- [Default](KBI_EXT_71.0x132.5mm_for_Default.zip)
- [Elecrow](KBI_EXT_71.0x132.5mm_for_Elecrow.zip)
- [FusionPCB](KBI_EXT_71.0x132.5mm_for_FusionPCB.zip)
- [JLCPCB](KBI_EXT_71.0x132.5mm_for_JLCPCB.zip)
- [PCBWay](KBI_EXT_71.0x132.5mm_for_PCBWay.zip)

## Images

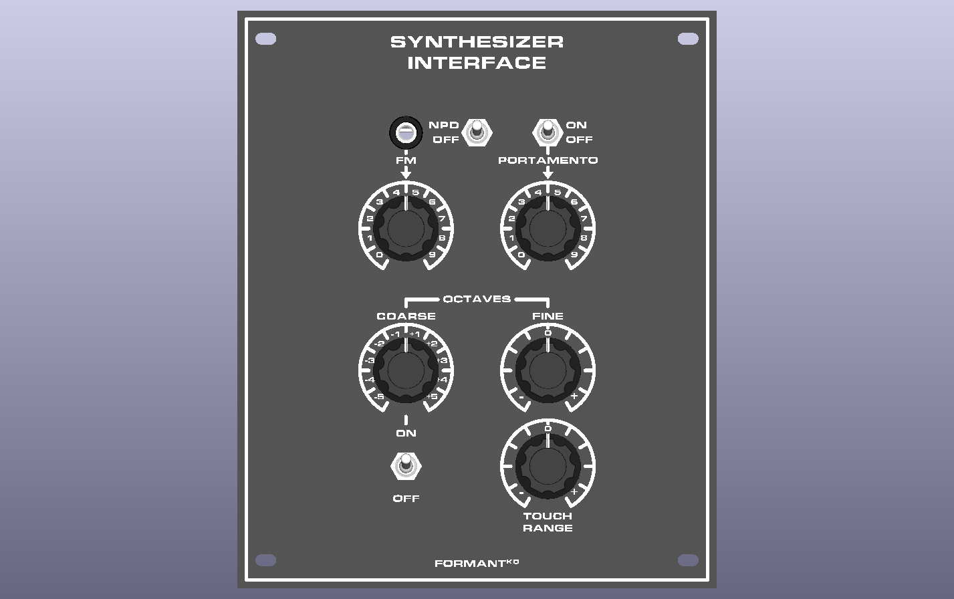
[picture p75: panels/KBI_EXT/KBI_EXT_front.png]
Rendered Panel Front


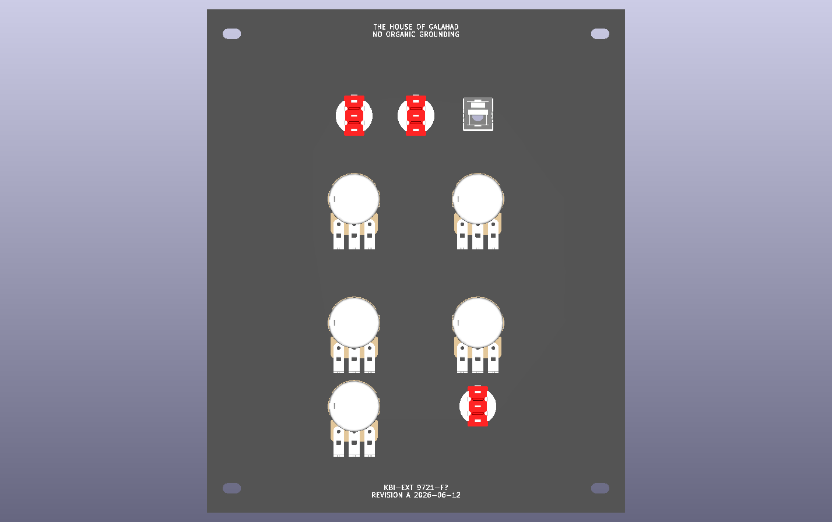
[picture p76: panels/KBI_EXT/KBI_EXT_back.png]
Rendered Panel Back
