Desval27/FormantKO/panels/LFOs/README.md

# LFOs

## Status

Incomplete

## Documents

- [Assembly](plots/LFOs__Assembly.pdf)

## Gerber To Order

⚠️ Untested⚠️

- [Default](LFOs_71.0x132.5mm_for_Default.zip)
- [Elecrow](LFOs_71.0x132.5mm_for_Elecrow.zip)
- [FusionPCB](LFOs_71.0x132.5mm_for_FusionPCB.zip)
- [JLCPCB](LFOs_71.0x132.5mm_for_JLCPCB.zip)
- [PCBWay](LFOs_71.0x132.5mm_for_PCBWay.zip)

## Images

Rendered Panel Front

Rendered Panel Back
