Desval27/FormantKO/panels/VCF_12/README.md

# VCF-12

## Status

Incomplete

## Documents

- [Assembly](plots/VCF_12__Assembly.pdf)

## Gerber To Order

⚠️ Untested⚠️

- [Default](VCF_12_71.0x132.5mm_for_Default.zip)
- [Elecrow](VCF_12_71.0x132.5mm_for_Elecrow.zip)
- [FusionPCB](VCF_12_71.0x132.5mm_for_FusionPCB.zip)
- [JLCPCB](VCF_12_71.0x132.5mm_for_JLCPCB.zip)
- [PCBWay](VCF_12_71.0x132.5mm_for_PCBWay.zip)

## Images

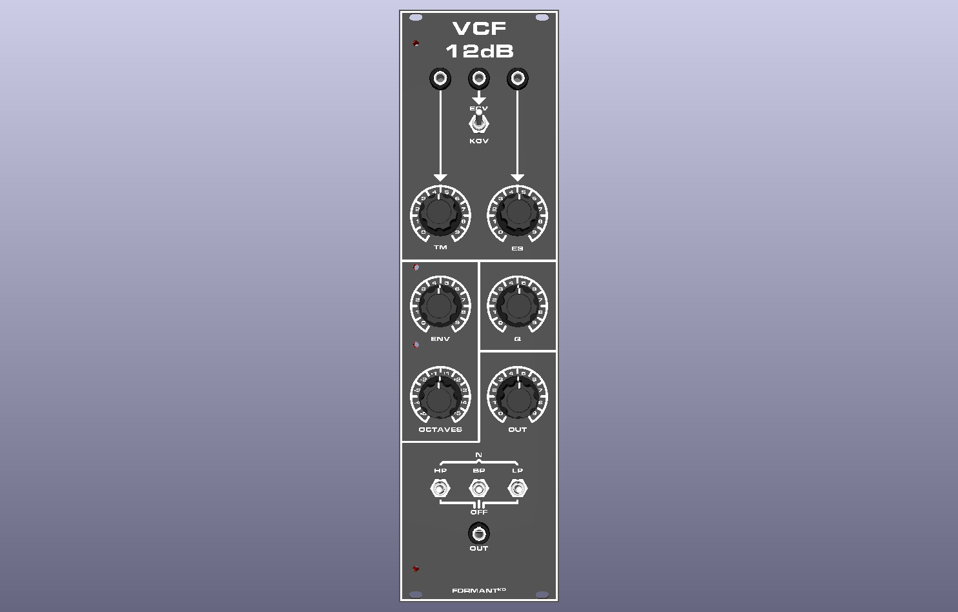
[picture p79: panels/VCF_12/VCF_12_front.png]
Rendered Panel Front


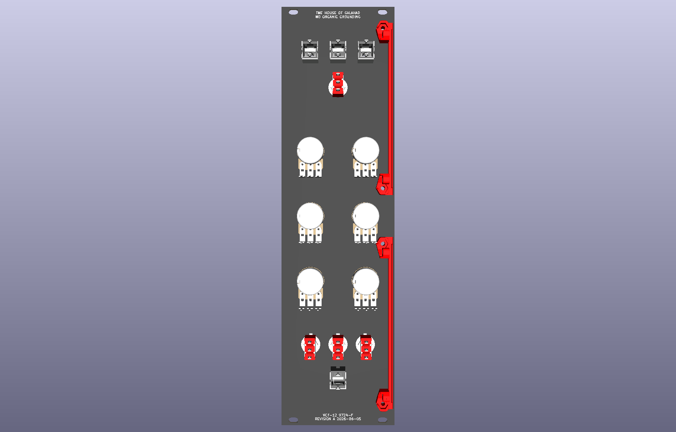
[picture p80: panels/VCF_12/VCF_12_back.png]
Rendered Panel Back
