Desval27/FormantKO/panels/VCF_24/README.md

# VCF-24

## Status

Incomplete

## Documents

- [Assembly](plots/VCF_24__Assembly.pdf)

## Gerber To Order

⚠️ Untested⚠️

- [Default](VCF_24_71.0x132.5mm_for_Default.zip)
- [Elecrow](VCF_24_71.0x132.5mm_for_Elecrow.zip)
- [FusionPCB](VCF_24_71.0x132.5mm_for_FusionPCB.zip)
- [JLCPCB](VCF_24_71.0x132.5mm_for_JLCPCB.zip)
- [PCBWay](VCF_24_71.0x132.5mm_for_PCBWay.zip)

## Images

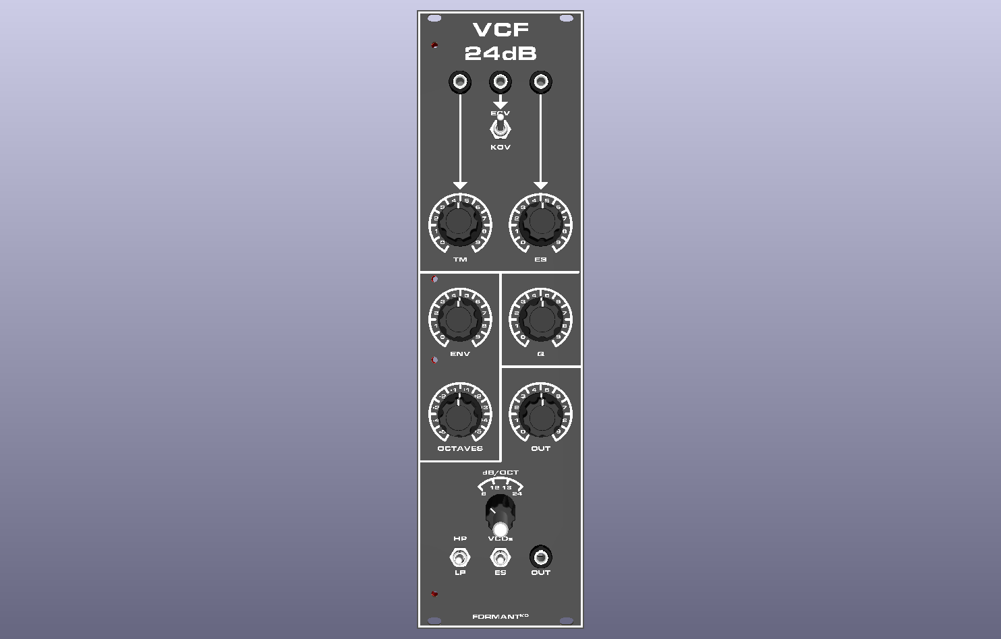
[picture p81: panels/VCF_24/VCF_24_front.png]
Rendered Panel Front


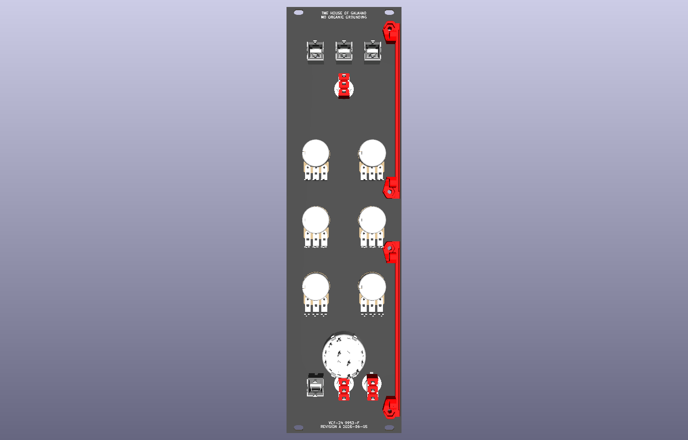
[picture p82: panels/VCF_24/VCF_24_back.png]
Rendered Panel Back
