Desval27/FormantKO/panels/RFM/README.md

# RFM

## Status

Incomplete

## Documents

- [Assembly](plots/RFM__Assembly.pdf)

## Gerber To Order

⚠️ Untested⚠️

- [Default](RFM_71.0x132.5mm_for_Default.zip)
- [Elecrow](RFM_71.0x132.5mm_for_Elecrow.zip)
- [FusionPCB](RFM_71.0x132.5mm_for_FusionPCB.zip)
- [JLCPCB](RFM_71.0x132.5mm_for_JLCPCB.zip)
- [PCBWay](RFM_71.0x132.5mm_for_PCBWay.zip)

## Images

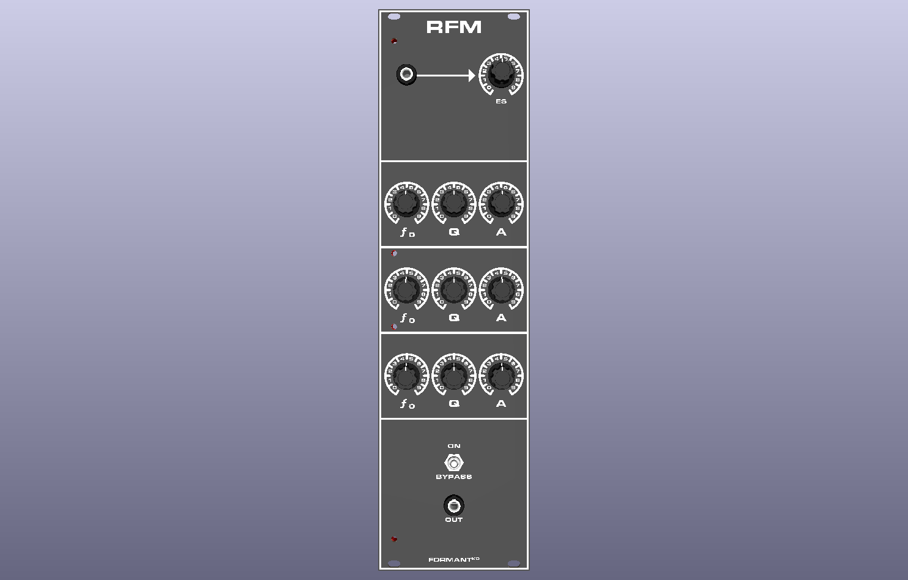
[picture p83: panels/RFM/RFM_front.png]
Rendered Panel Front


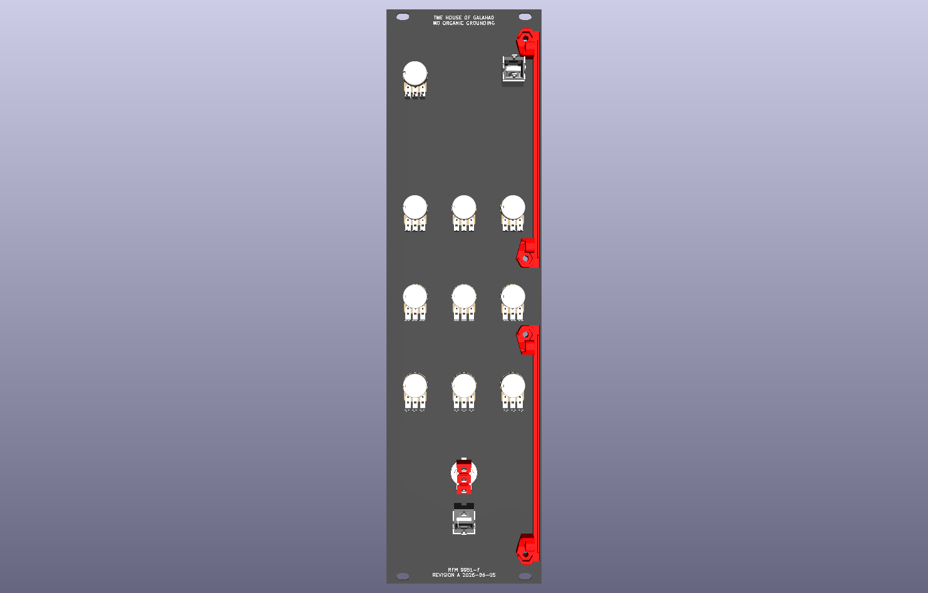
[picture p84: panels/RFM/RFM_back.png]
Rendered Panel Back
