Desval27/FormantKO/panels/VCO/README.md

# VCO

## Status

Incomplete

## Documents

- [Assembly](plots/VCO__Assembly.pdf)

## Gerber To Order

⚠️ Untested⚠️

- [Default](VCO_71.0x132.5mm_for_Default.zip)
- [Elecrow](VCO_71.0x132.5mm_for_Elecrow.zip)
- [FusionPCB](VCO_71.0x132.5mm_for_FusionPCB.zip)
- [JLCPCB](VCO_71.0x132.5mm_for_JLCPCB.zip)
- [PCBWay](VCO_71.0x132.5mm_for_PCBWay.zip)

## Images

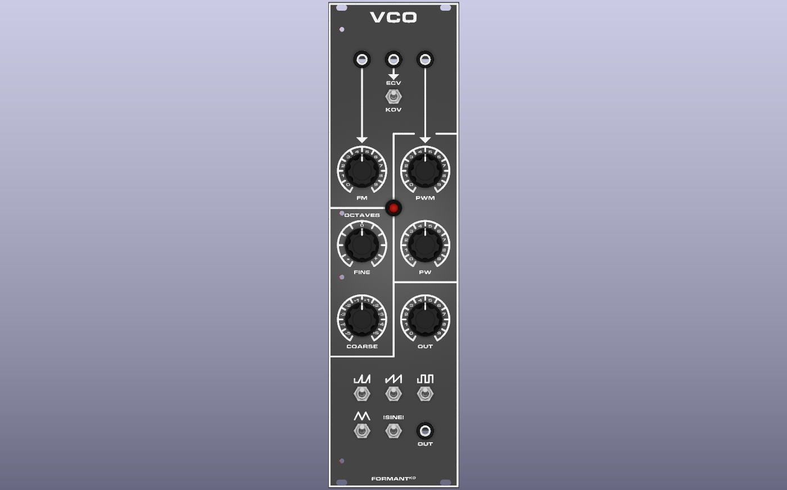
[picture p85: panels/VCO/VCO_front.png]
Rendered Panel Front


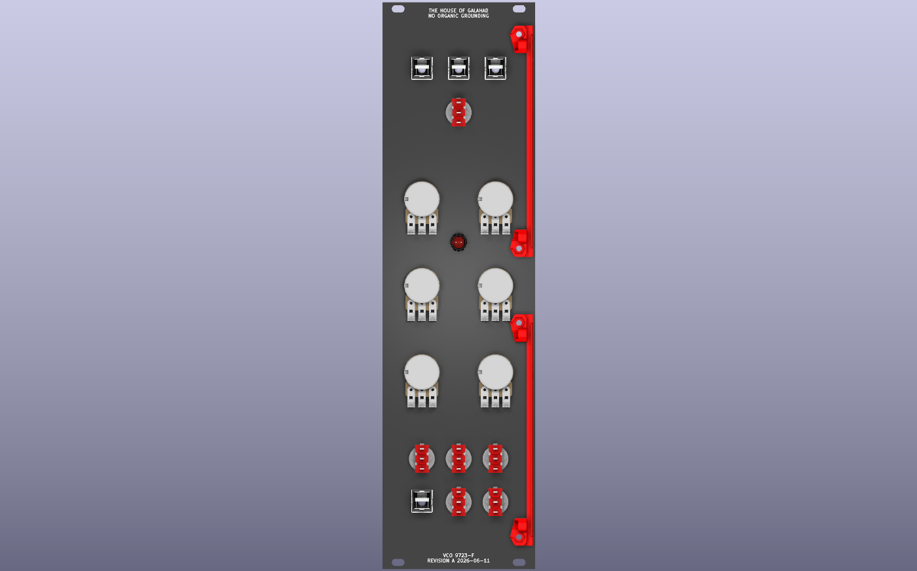
[picture p86: panels/VCO/VCO_back.png]
Rendered Panel Back
