Desval27/FormantKO/modules/35_WAVEFORM_PROCESSOR/README.md

# WAVEFORM-PROCESSOR

## Status

60% Complete

- [x] Schematic
- [x] Schematic Additions
- [x] Schematic Review
- [x] PCB Placement
- [x] PCB Routing
- [x] PCB Review
- [ ] Sample
- [ ] Build
- [ ] Calibrated
- [ ] Tested

## Documents

- [Translated Document](WAVEFORM_PROCESSOR.pdf)
- [Assembly](plots/WAVEFORM_PROCESSOR__Assembly.pdf)
- [Interactive Bill of Materials](bom/ibom.html)

## Gerber to Order

!Untested!

- [Default](gerber_to_order/WAVEFORM_PROCESSOR_160.0x100.0mm_for_Default.zip)
- [Elecrow](gerber_to_order/WAVEFORM_PROCESSOR_160.0x100.0mm_for_Elecrow.zip)
- [FusionPCB](gerber_to_order/WAVEFORM_PROCESSOR_160.0x100.0mm_for_FusionPCB.zip)
- [JLCPCB](gerber_to_order/WAVEFORM_PROCESSOR_160.0x100.0mm_for_JLCPCB.zip)
- [PCBWay](gerber_to_order/WAVEFORM_PROCESSOR_160.0x100.0mm_for_PCBWay.zip)

## Images

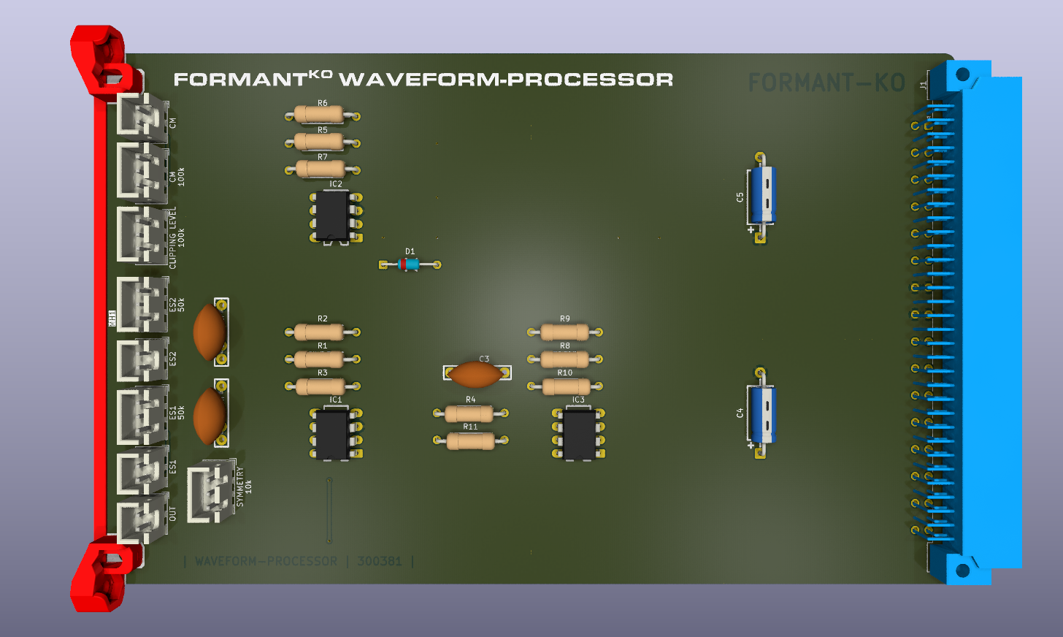
[picture p89: modules/35_WAVEFORM_PROCESSOR/WAVEFORM_PROCESSOR_top.png]
Rendered PCB Top


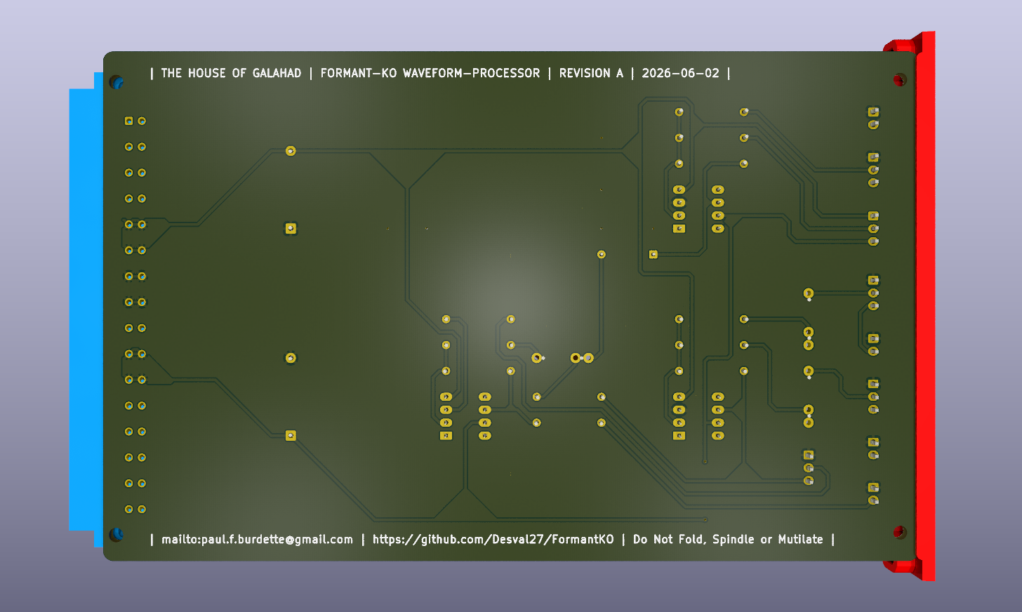
[picture p90: modules/35_WAVEFORM_PROCESSOR/WAVEFORM_PROCESSOR_bottom.png]
Rendered PCB Bottom
