Desval27/FormantKO/modules/07_VCF_24/README.md

# VCF 24dB

## Status

0% Complete

- [ ] Schematic
- [ ] Schematic Additions
- [ ] Schematic Review
- [ ] PCB Placement
- [ ] PCB Routing
- [ ] PCB Review
- [ ] Sample
- [ ] Build
- [ ] Calibrated
- [ ] Tested

## Documents

## Interactive Bill of Materials

## Gerber to Order

## Images

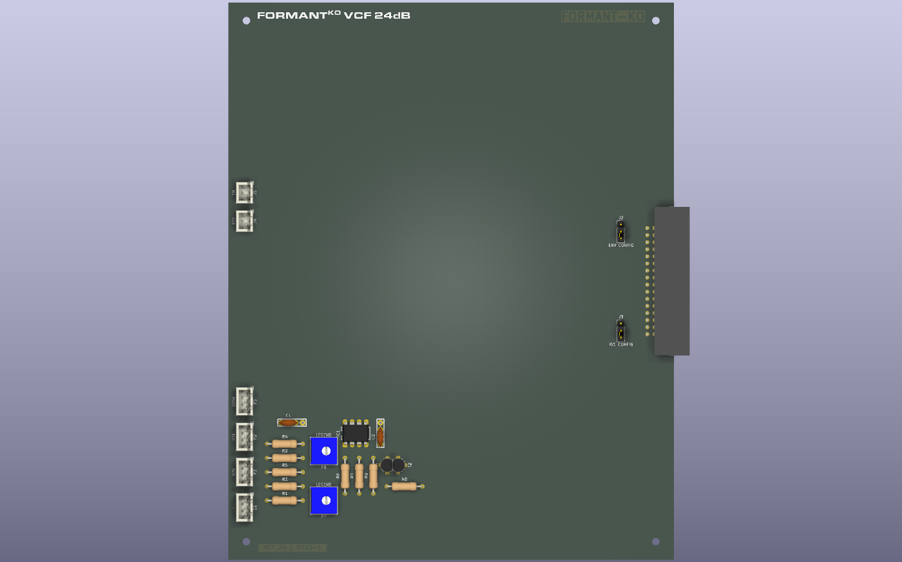
[picture p91: modules/07_VCF_24/VCF_24_top.png]
Rendered PCB Top


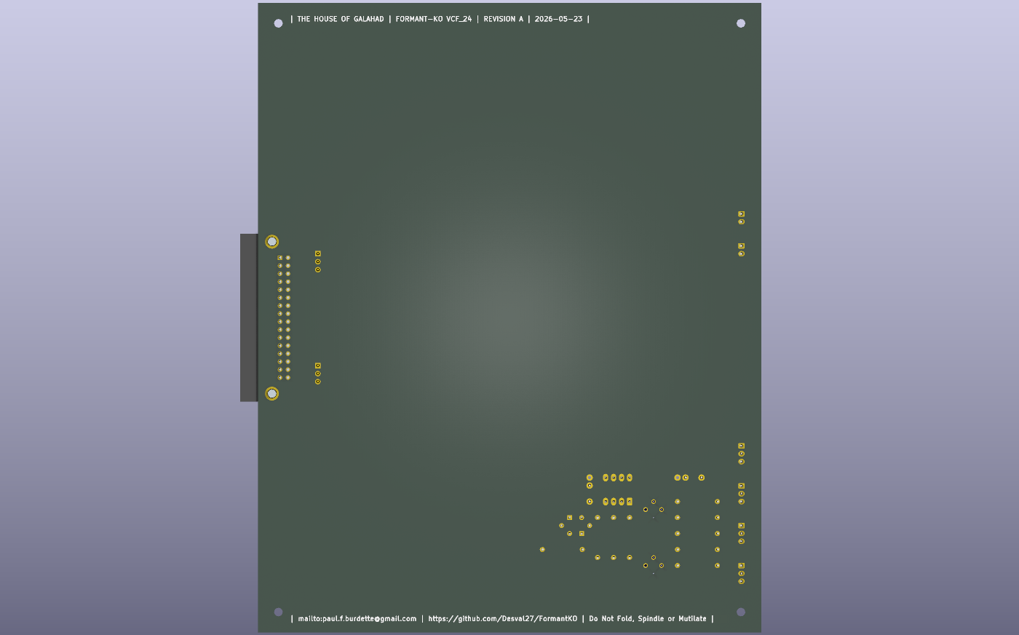
[picture p92: modules/07_VCF_24/VCF_24_bottom.png]
Rendered PCB Bottom
