Desval27/FormantKO/modules/08_RFM/README.md

# RFM

## Status

0% Complete

- [ ] Schematic
- [ ] Schematic Additions
- [ ] Schematic Review
- [ ] PCB Placement
- [ ] PCB Routing
- [ ] PCB Review
- [ ] Sample
- [ ] Build
- [ ] Calibrated
- [ ] Tested

## Documents

## Interactive Bill of Materials

## Gerber to Order

## Images

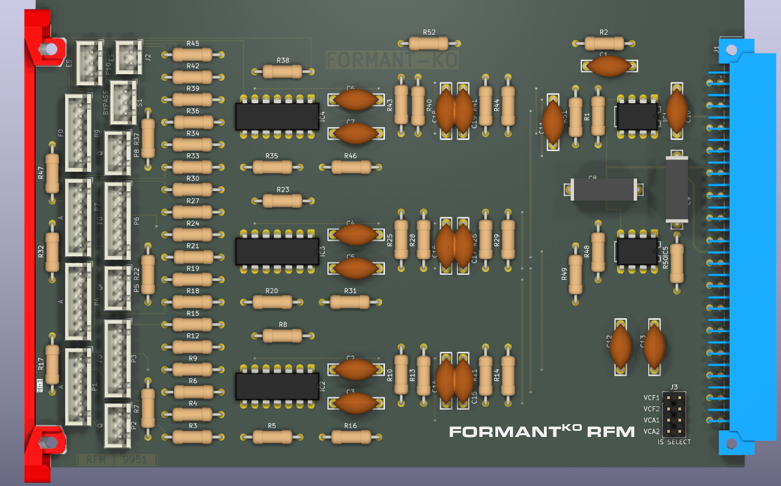
[picture p93: modules/08_RFM/RFM_top.png]
Rendered PCB Top


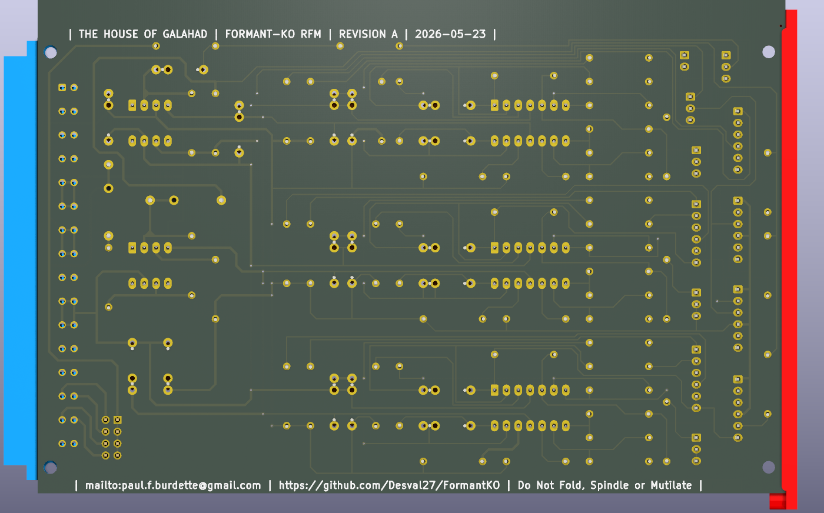
[picture p94: modules/08_RFM/RFM_bottom.png]
Rendered PCB Bottom
