Desval27/FormantKO/modules/11_LFOs/README.md

# LFOs

## Status

20% Complete

- [x] Schematic
- [x] Schematic Additions
- [ ] Schematic Review
- [ ] PCB Placement
- [ ] PCB Routing
- [ ] PCB Review
- [ ] Sample
- [ ] Build
- [ ] Calibrated
- [ ] Tested

## Documents

## Interactive Bill of Materials

## Gerber to Order

## Images

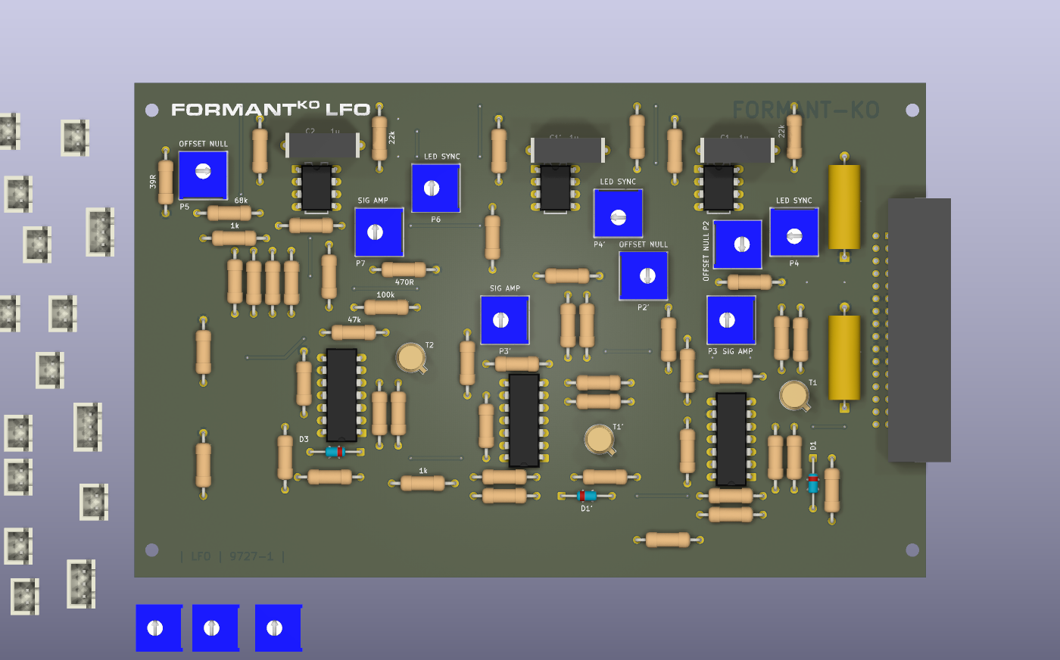
[picture p95: modules/11_LFOs/LFOs_top.png]
Rendered PCB Top
