Desval27/FormantKO/modules/12_NOISE/README.md

# NOISE

## Status

20% Complete

- [x] Schematic
- [ ] Schematic Additions
- [ ] Schematic Review
- [x] PCB Placement
- [ ] PCB Routing
- [ ] PCB Review
- [ ] Sample
- [ ] Build
- [ ] Calibrated
- [ ] Tested

## Documents

## Interactive Bill of Materials

## Gerber to Order

## Images

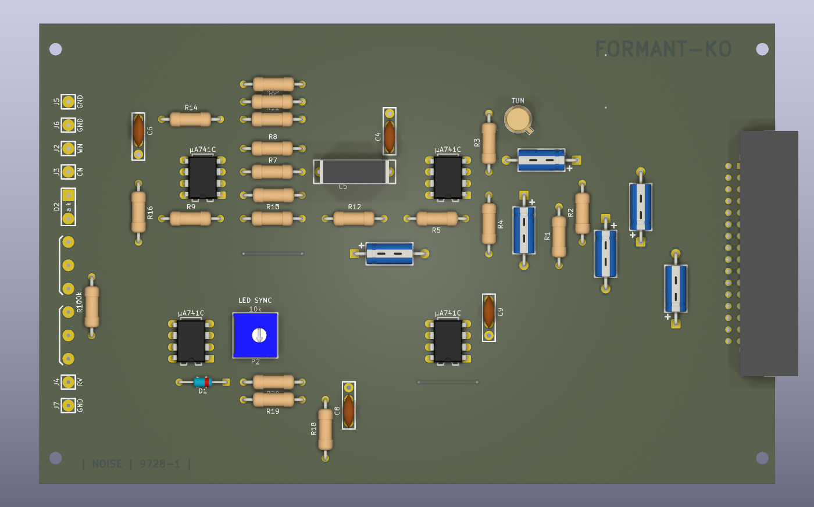
[picture p96: modules/12_NOISE/NOISE_top.png]
Rendered PCB Top
