Desval27/FormantKO/system/KBI/README.md

# STATUS

0% Complete

- [ ] Schematic
- [ ] Schematic Additions
- [ ] Schematic Review
- [ ] PCB Placement
- [ ] PCB Routing
- [ ] PCB Review
- [ ] Sample
- [ ] Build
- [ ] Calibrated
- [ ] Tested

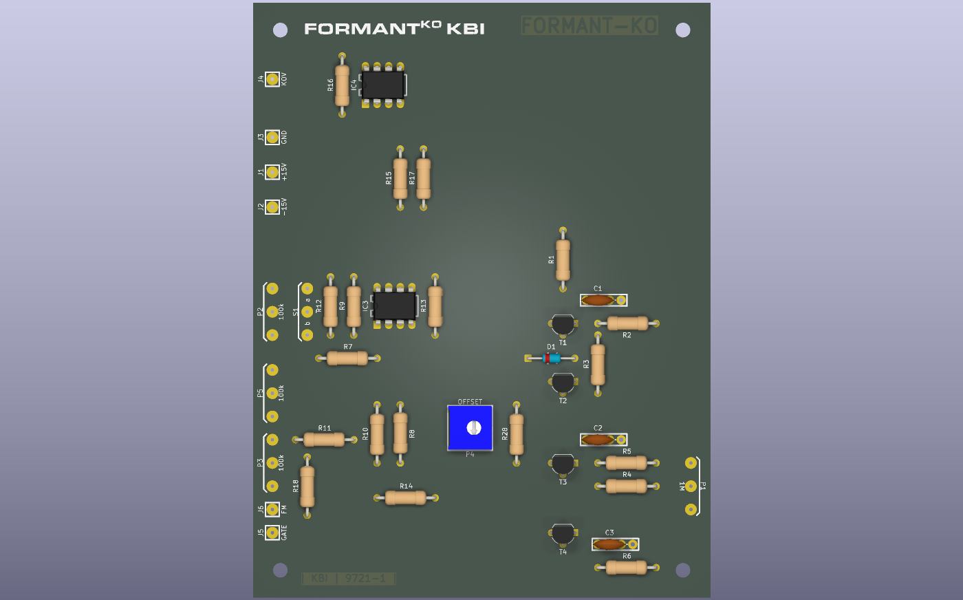
[picture p97: system/KBI/KBI_top.png]
Rendered PCB Top


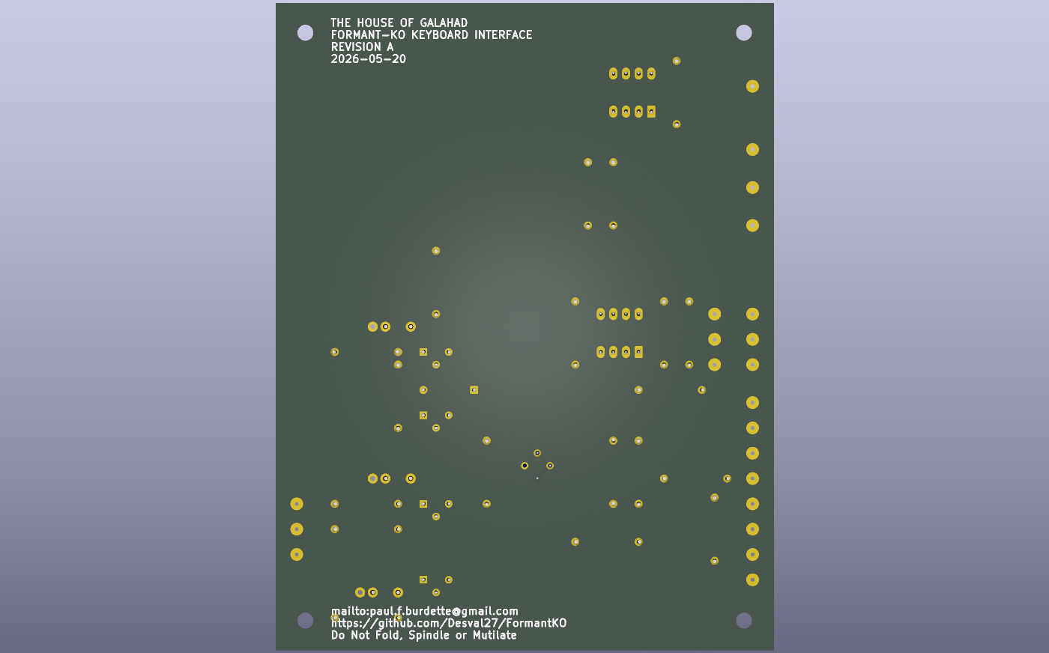
[picture p98: system/KBI/KBI_bottom.png]
Rendered PCB Bottom
