Desval27/FormantKO/MFOS/modules/GATE/README.md

# TEMPLATE-3U

Format: 3U

## Status

⚠️ Incomplete⚠️

## Documents

<!--
- [Schematic](plots/TEMPLATE__Schematic.pdf)
- [Assembly](plots/TEMPLATE__Assembly.pdf)
-->

## Gerber to Order

⚠️ Untested⚠️

## Images

Rendered Panel Front

Rendered Panel Back
