Desval27/FormantKO/MFOS/panels/GATE/README.md

# GATE

GATE-16

Format: 6U

## Status

⚠️ Incomplete⚠️

## Documents

## Gerber to Order

⚠️ Untested⚠️

## Images

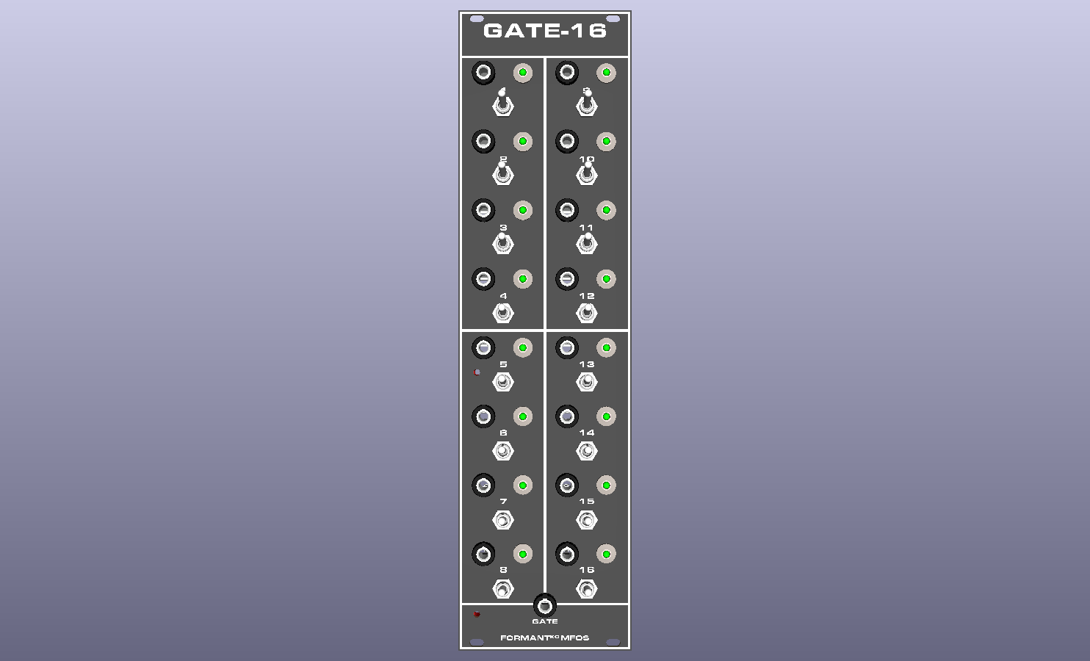
[picture p99: MFOS/panels/GATE/GATE_front.png]
Rendered Panel Front


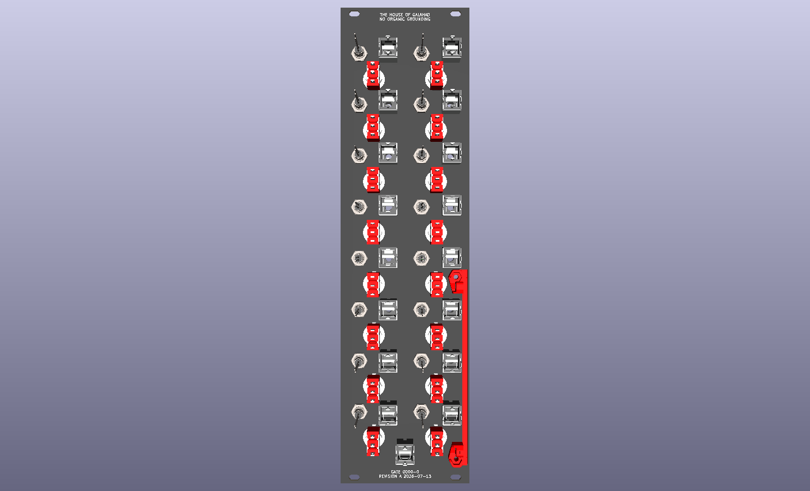
[picture p100: MFOS/panels/GATE/GATE_back.png]
Rendered Panel Back
