Desval27/FormantKO/MFOS/modules/ANALOG/README.md

# ANALOG

Format: Single Height 160mm x 100mm

## Status

⚠️ Incomplete⚠️

## Documents

- [Schematic](plots/ANALOG__schematic.pdf)
<!--
- [Assembly](plots/CLOCK__Assembly.pdf)
- [Interactive Bill of Materials](bom/ibom.html)
-->

## Gerber to Order

⚠️ Untested⚠️

## Images

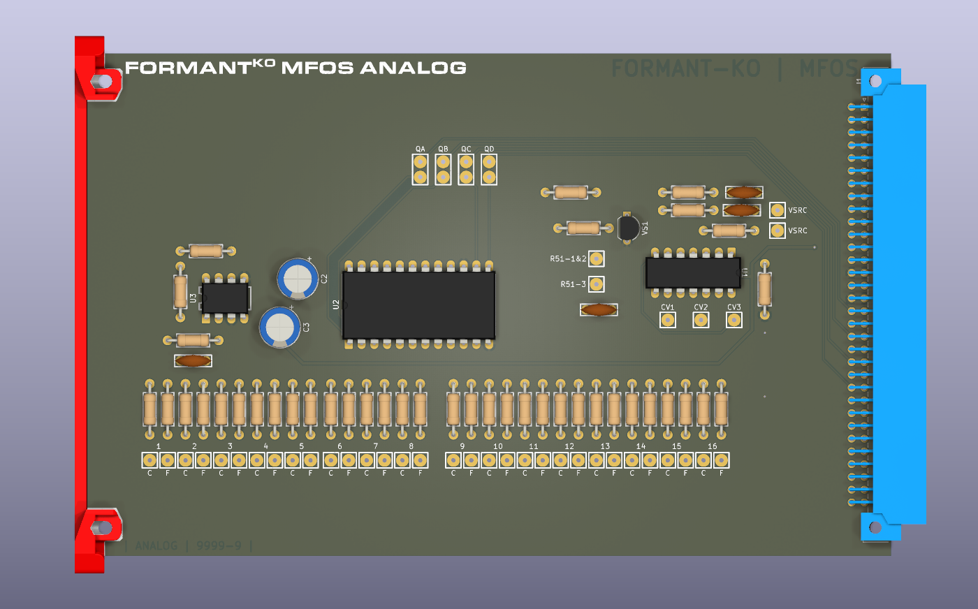
[picture p103: MFOS/modules/ANALOG/ANALOG_top.png]
Rendered PCB Top


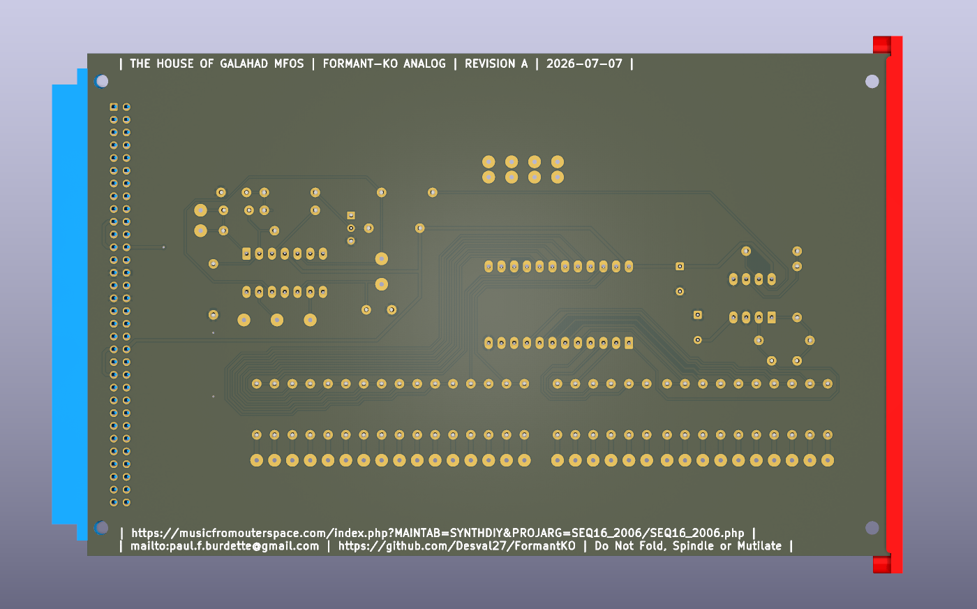
[picture p104: MFOS/modules/ANALOG/ANALOG_bottom.png]
Rendered PCB Bottom
