Desval27/FormantKO/MFOS/modules/CLOCK/README.md

# CLOCK

Format: Single Height 160mm x 100mm

## Status

⚠️ Incomplete⚠️

## Documents

<!--
- [Schematic](CLOCK.pdf)
- [Assembly](plots/CLOCK__Assembly.pdf)
- [Interactive Bill of Materials](bom/ibom.html)
-->

## Gerber to Order

⚠️ Untested⚠️

## Images

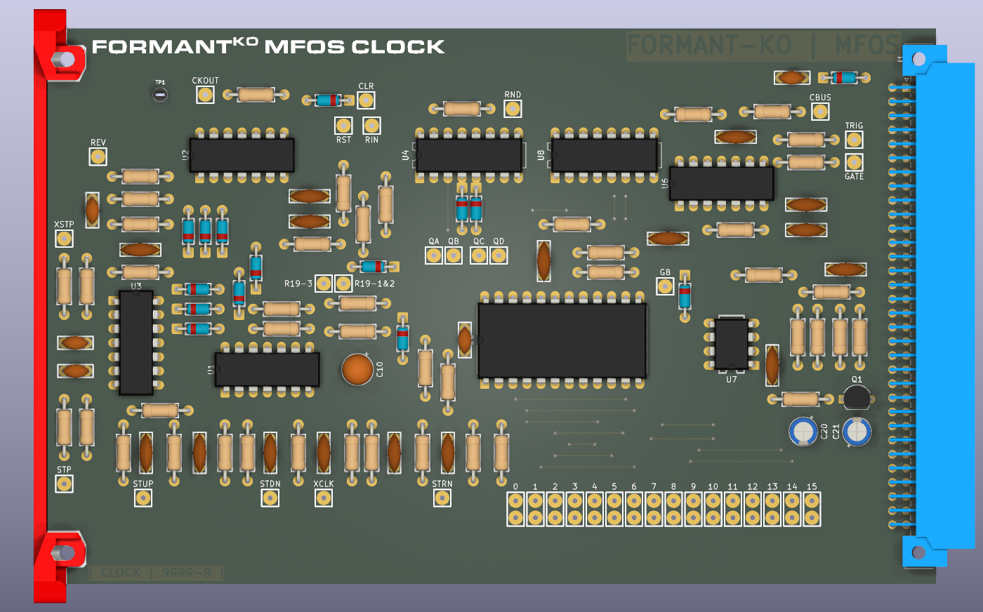
[picture p105: MFOS/modules/CLOCK/CLOCK_top.png]
Rendered PCB Top


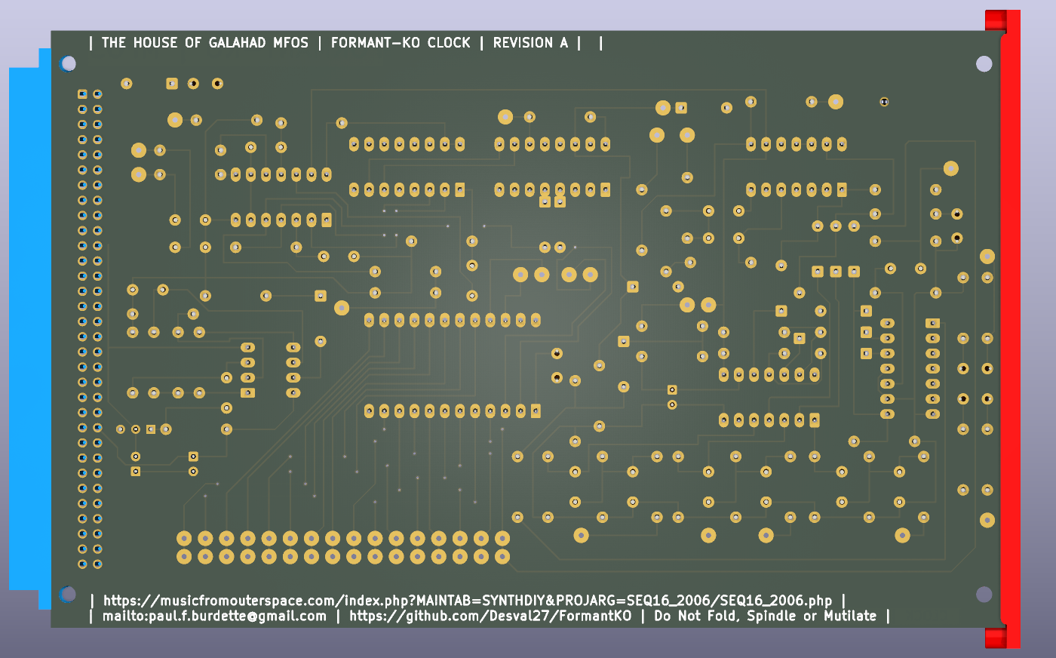
[picture p106: MFOS/modules/CLOCK/CLOCK_bottom.png]
Rendered PCB Bottom
