Desval27/FormantKO/MFOS/panels/CLOCK/README.md

# CLOCK

Format 3U

## Status

⚠️ Incomplete⚠️

## Documents

## Gerber to Order

⚠️ Untested⚠️

## Images

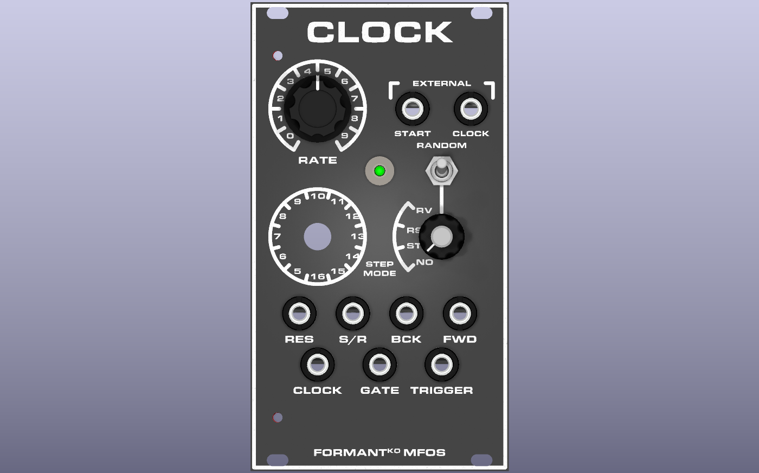
[picture p107: MFOS/panels/CLOCK/CLOCK_front.png]
Rendered Panel Front


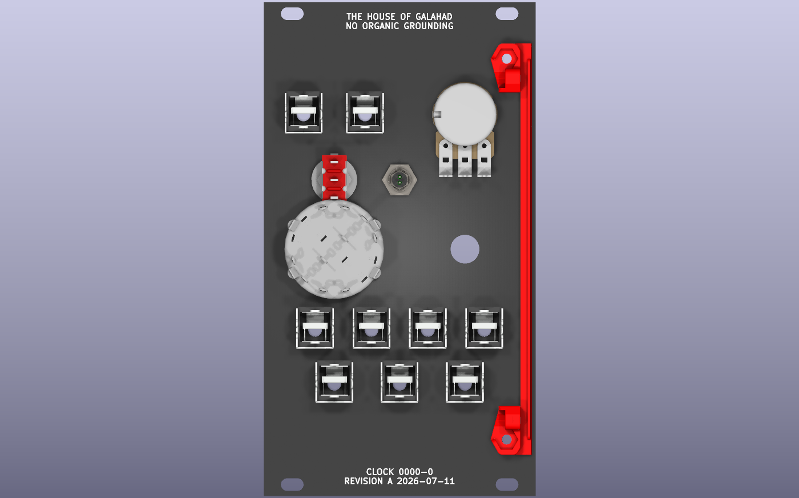
[picture p108: MFOS/panels/CLOCK/CLOCK_back.png]
Rendered Panel Back
