Desval27/FormantKO/system/PSU/PSU_PT/README.md

# POWER SUPPLY - POWER TRANSISTORS

## Status

⚠️ Incomplete⚠️

0% Complete

- [x] Schematic
- [ ] Schematic Additions
- [x] Schematic Review
- [x] PCB Placement
- [x] PCB Routing
- [ ] PCB Review
- [ ] Sample
- [ ] Build
- [ ] Calibrated
- [ ] Tested

## Documents

## Interactive Bill of Materials

## Gerber to Order

## Images

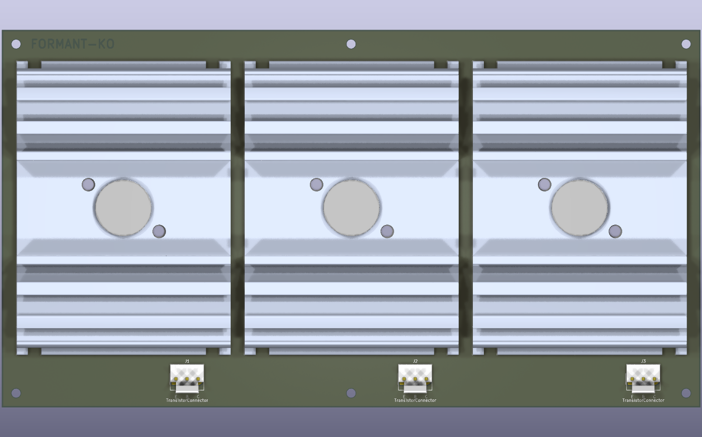
[picture p109: system/PSU/PSU_PT/PSU_PT_top.png]
Rendered PCB Top


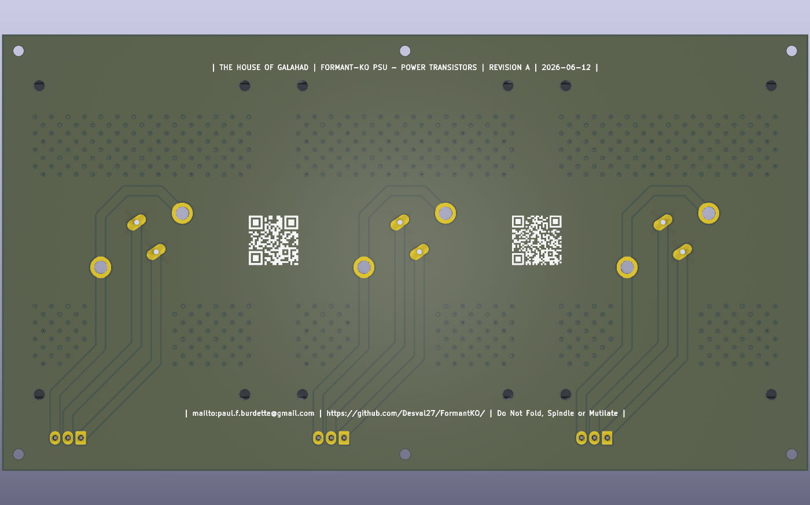
[picture p110: system/PSU/PSU_PT/PSU_PT_bottom.png]
Rendered PCB Bottom
