Desval27/FormantKO/MFOS/panels/EXPANDER/README.md

# TEMPLATE 3U

## Status

0% Complete

- [ ] PCB Placement
- [ ] PCB Review
- [ ] Sample
- [ ] Build
- [ ] Tested

## Documents

<!-- 
- [Assembly](plots/TEMPLATE_3U__Assembly.pdf)
-->

## Gerber To Order

⚠️ Untested⚠️

<!--
- [Default](TEMPLATE_3U_71.0x132.5mm_for_Default.zip)
- [Elecrow](TEMPLATE_3U_71.0x132.5mm_for_Elecrow.zip)
- [FusionPCB](TEMPLATE_3U_71.0x132.5mm_for_FusionPCB.zip)
- [JLCPCB](TEMPLATE_3U_71.0x132.5mm_for_JLCPCB.zip)
- [PCBWay](TEMPLATE_3U_71.0x132.5mm_for_PCBWay.zip)
-->

## Images

<!--
![Rendered Panel](TEMPLATE_3U.png "Rendered Panel")
-->
