Desval27/FormantKO/modules/09_ADSR/ADSR.png

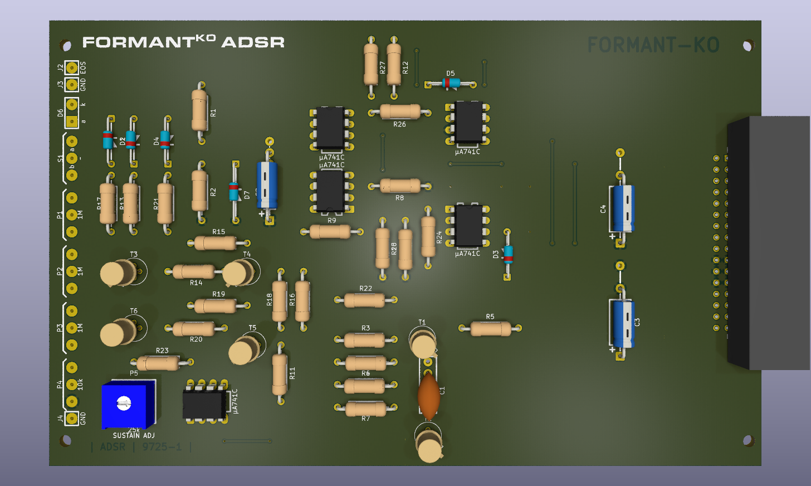
modules/09_ADSR/ADSR.png
