Desval27/FormantKO/system/BACKPLANE_A/BACKPLANE_A_bottom.png

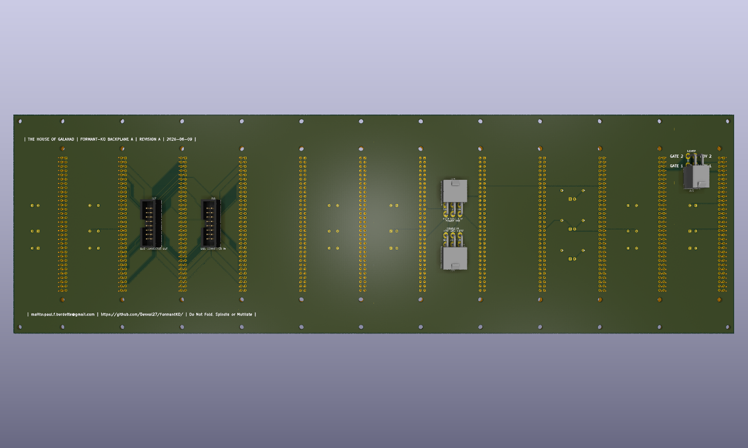
system/BACKPLANE_A/BACKPLANE_A_bottom.png
