Desval27/FormantKO/system/BACKPLANE_A/BACKPLANE_A_top.png

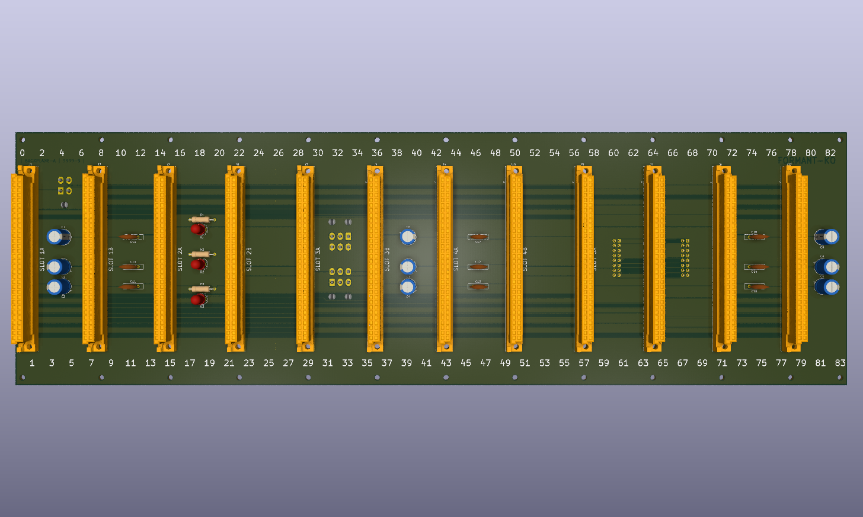
system/BACKPLANE_A/BACKPLANE_A_top.png
