Desval27/FormantKO/modules/COM/plots/COM__Schematic.pdf

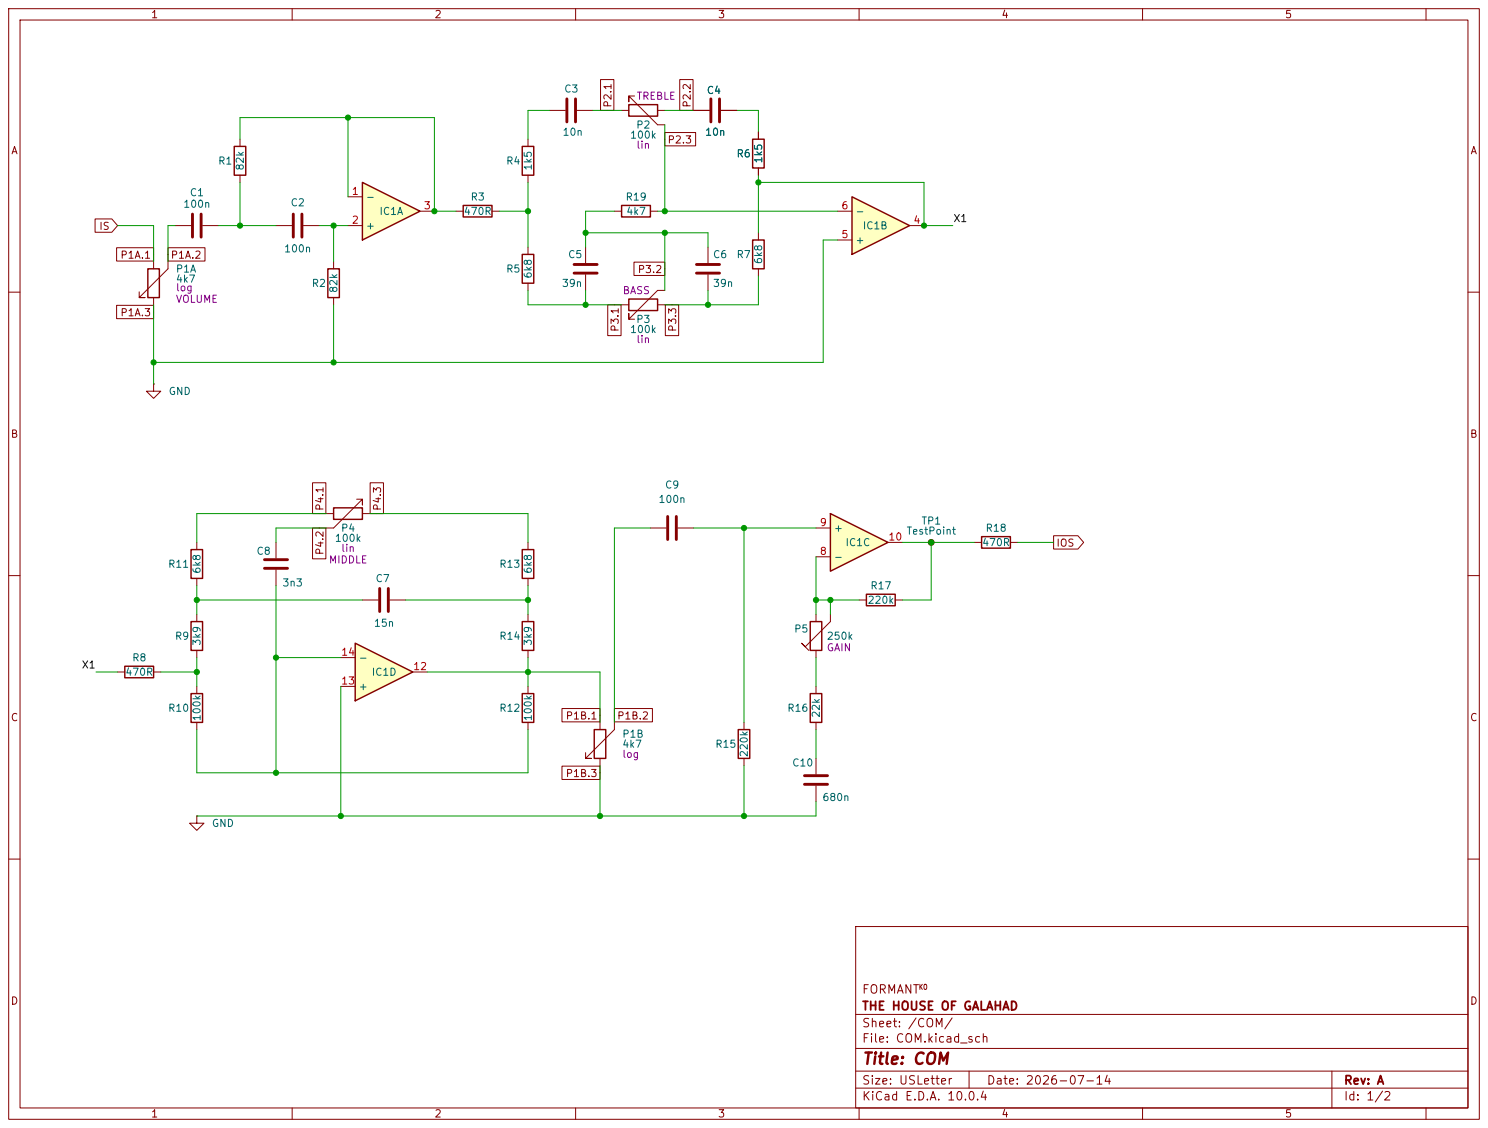
[picture p227: page 1]

THE HOUSE OF GALAHAD
Sheet: /COM/
File: COM.kicad_sch
Title: COM

Size: USLetter | Rev: A
KiCad E.D.A. 10.0.4 | Id: 1/2

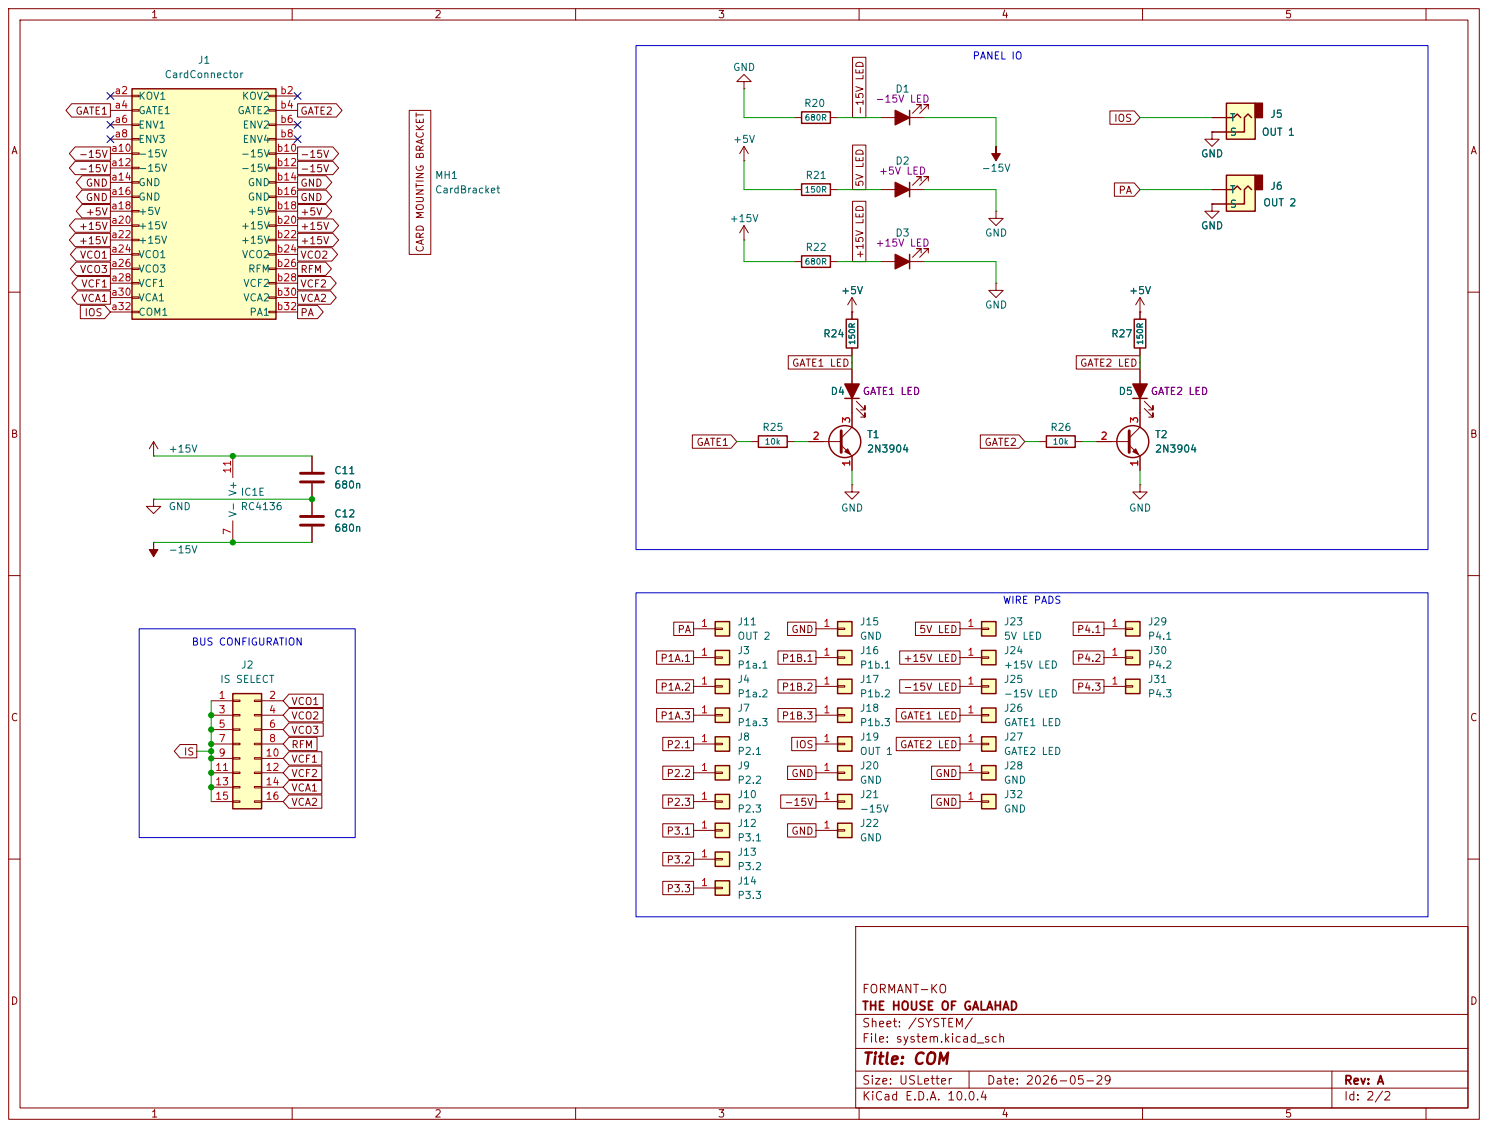
[picture p228: page 2]

FORMANT-KO
THE HOUSE OF GALAHAD
Sheet: /SYSTEM/
File: system.kicad_sch
Title: COM

Size: USLetter | Rev: A
KiCad E.D.A. 10.0.4 | Id: 2/2
