Desval27/FormantKO/modules/ADSR_CONTROLLER/plots/ADSR_CONTROLLER__Assembly.pdf

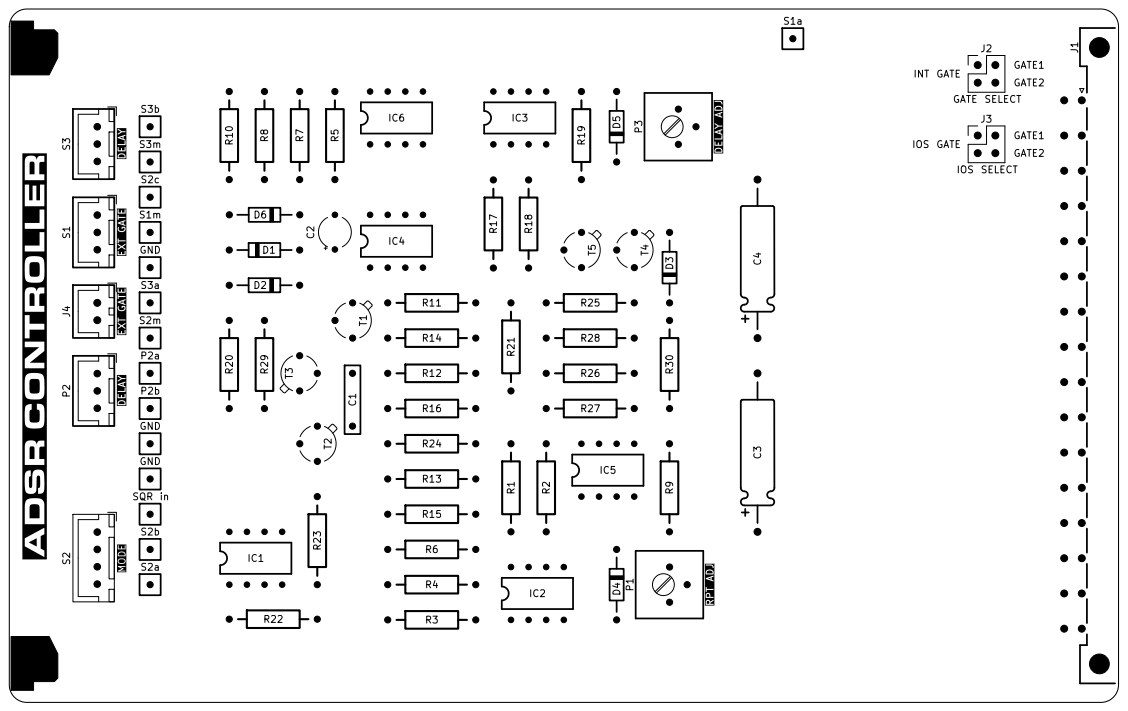
[picture p229: page 1]

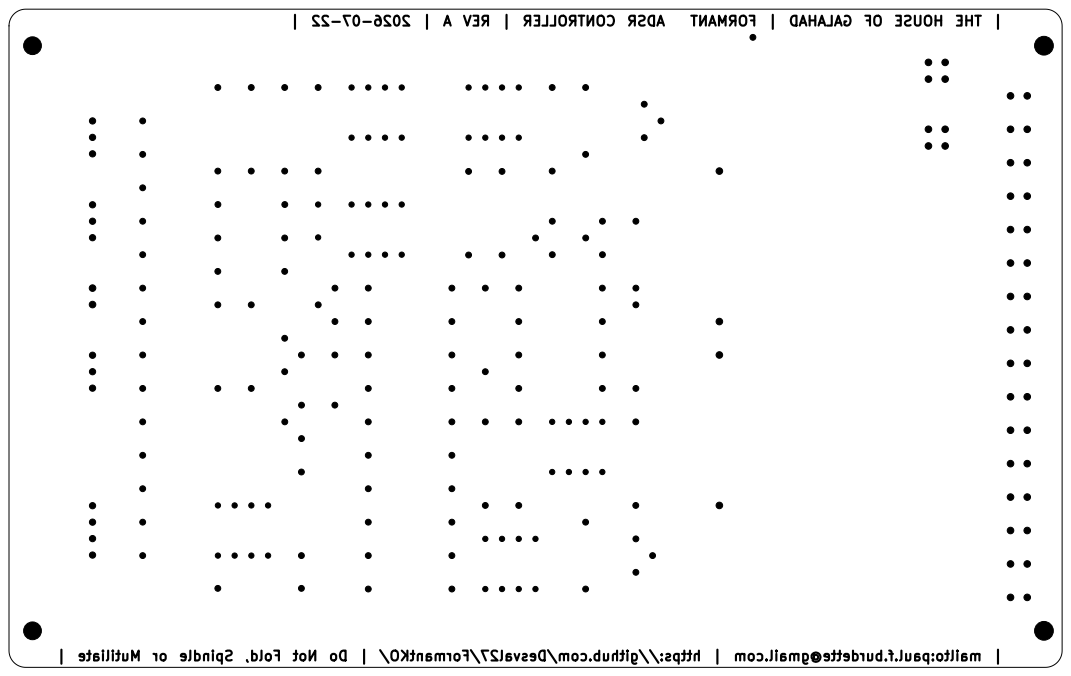
[picture p230: page 2]

KO | 2026-07-22 | A REV | CONTROLLER ADSR

FORMANT | GALAHAD OF HOUSE THE

Mutiliate or Spindle Fold, Not Do | https://github.com/Desval27/FormantKO/ | mailto:paul.f.burdette@gmail.com

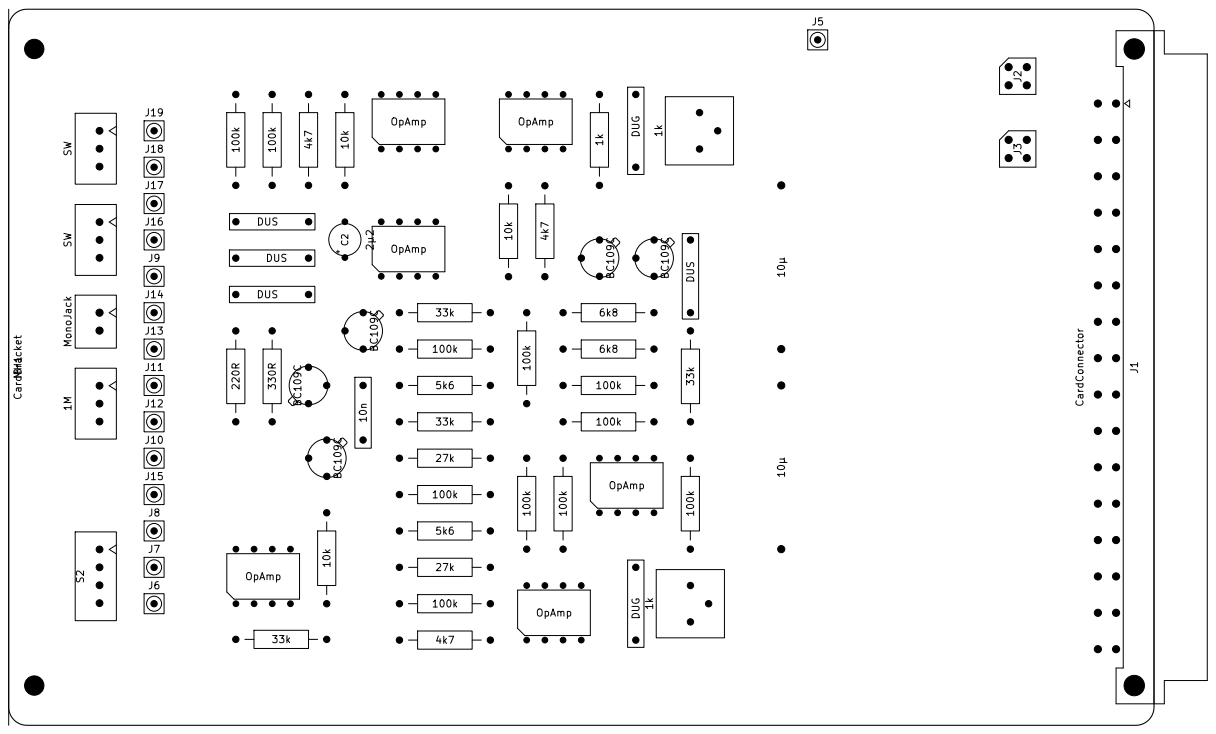
[picture p231: page 3]

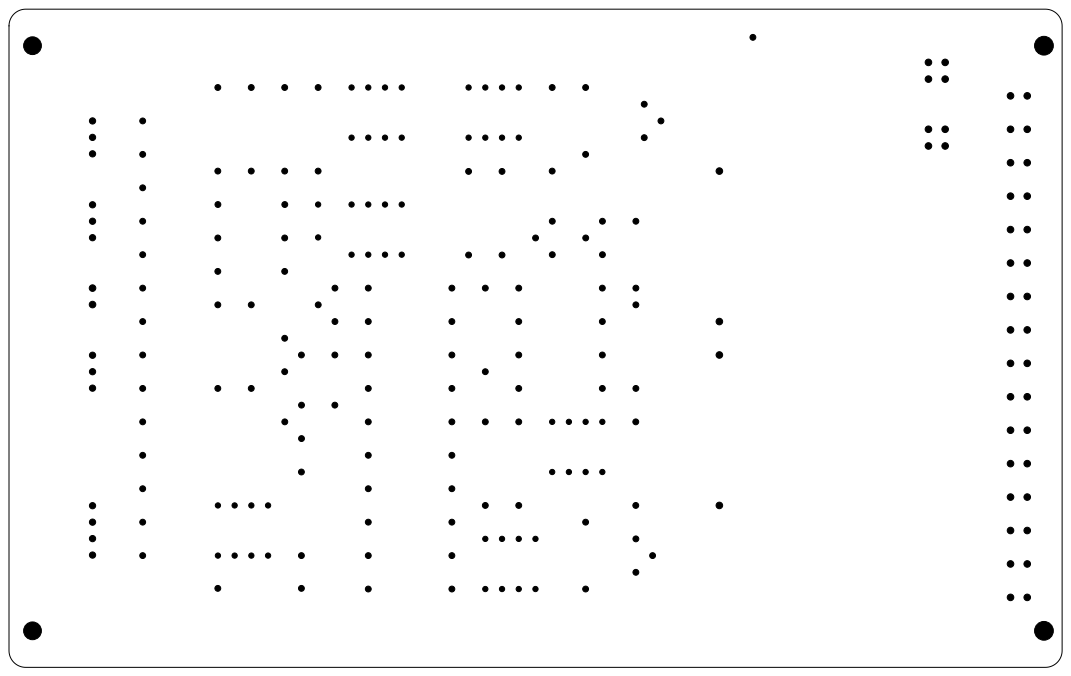
[picture p232: page 4]
