Desval27/FormantKO/modules/ADSR_CONTROLLER/plots/ADSR_CONTROLLER__Schematic.pdf

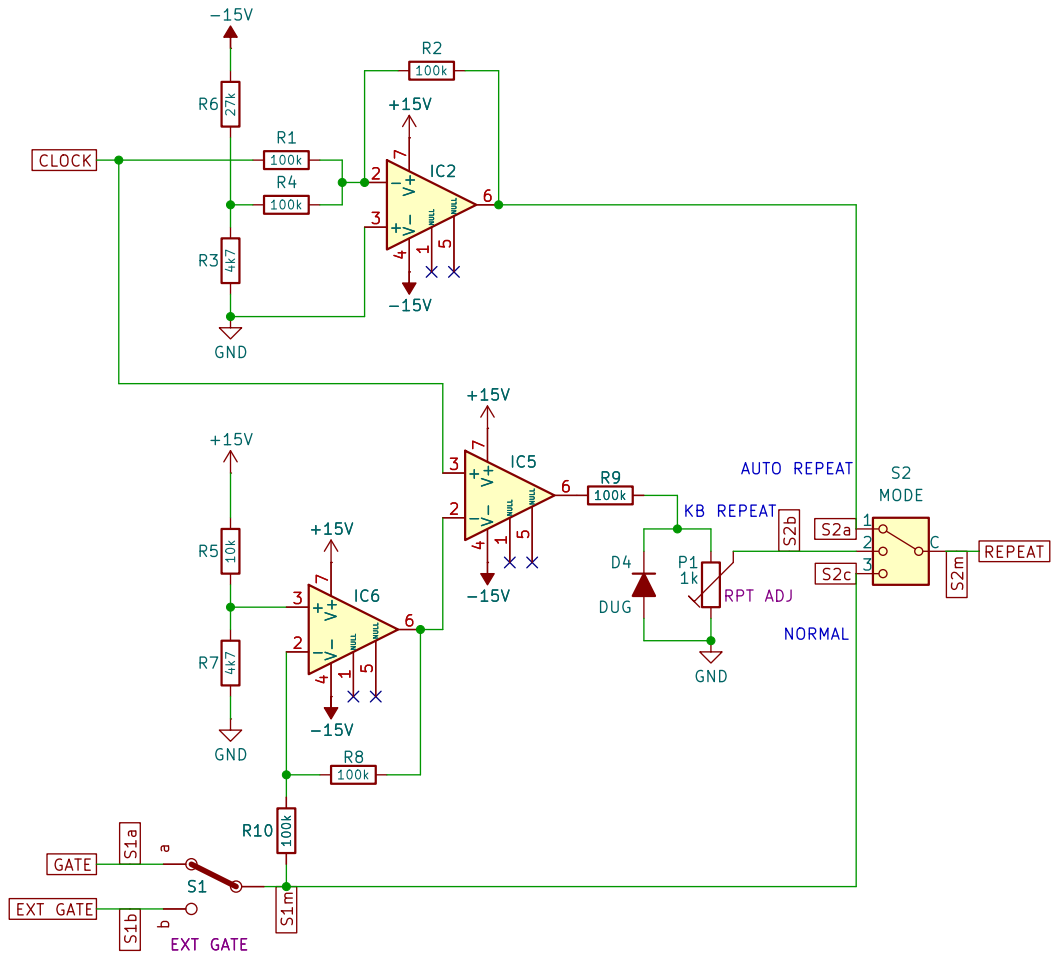
[picture p233: page 1]

AUTO REPEAT KB REPEAT NORMAL

FORMANT KO
THE HOUSE OF GALAHAD
Sheet: /ADSR_CONTROLLER/
File: ADSR_CONTROLLER.kicad_sch
Title: ADSR CONTROLLER

Size: USLetter | Rev: A
KiCad E.D.A. 10.0.3 | Id: 1/3

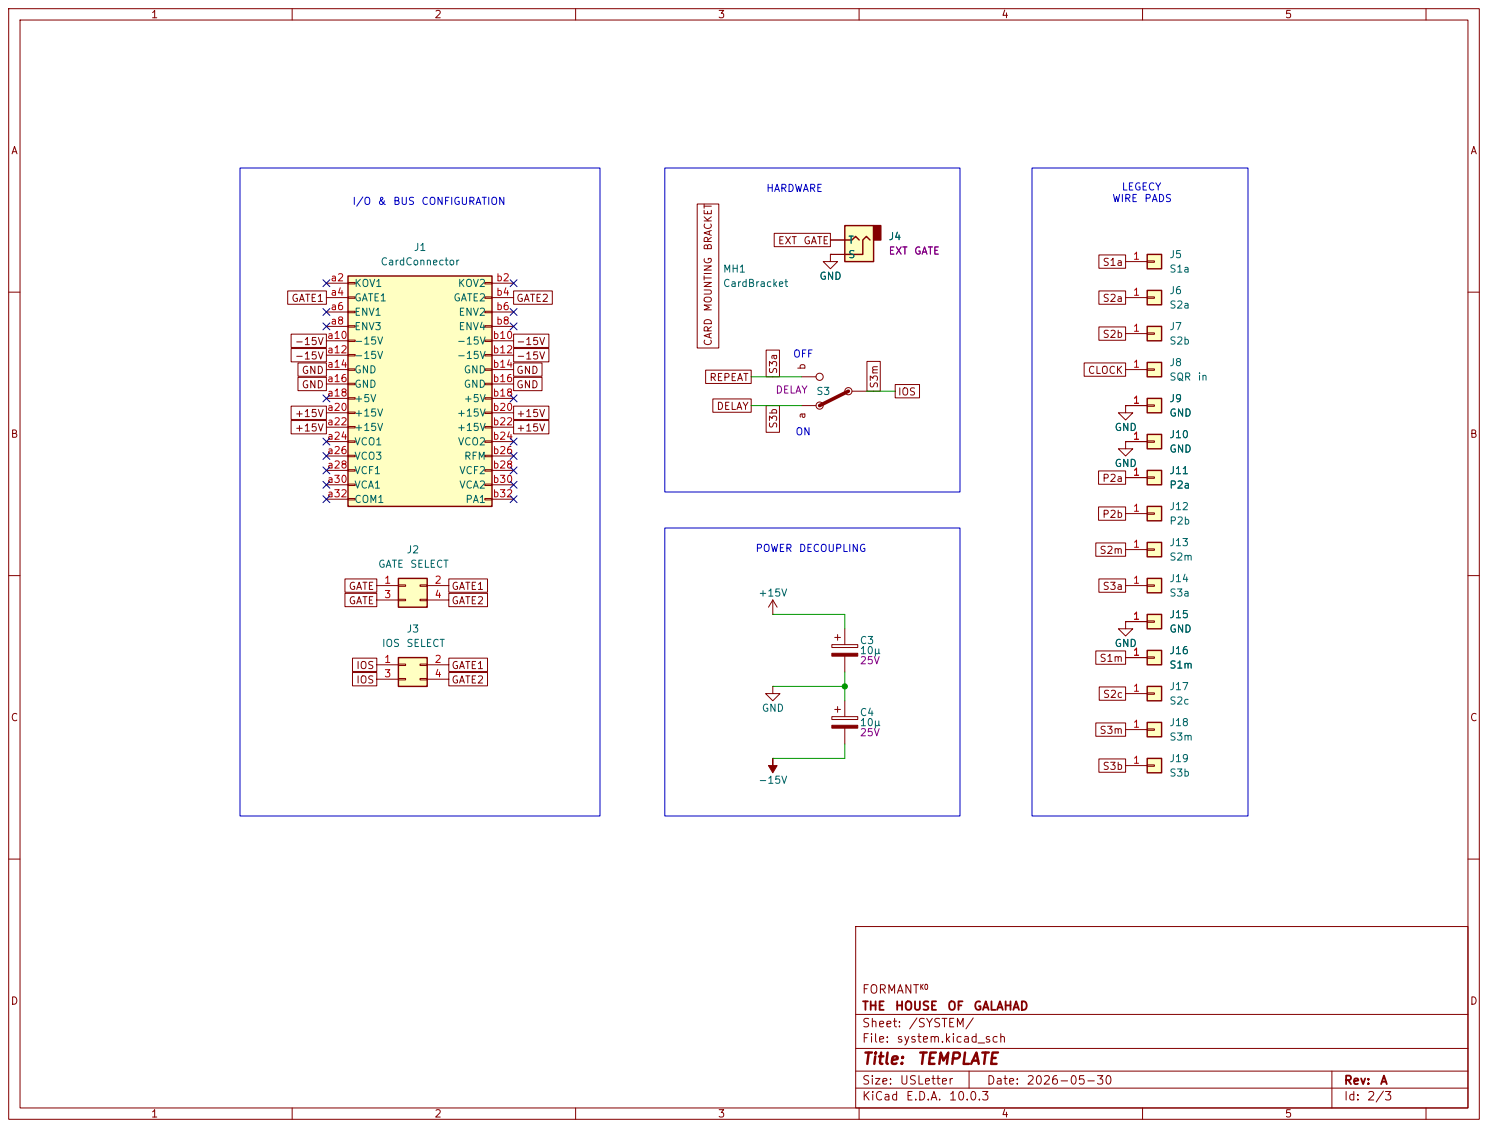
[picture p234: page 2]

LEGECY WIRE PADS ON
HARDWARE

EXT GATE ST GND

THE HOUSE OF GALAHAD
Sheet: /SYSTEM/
File: system.kicad_sch
Title: TEMPLATE

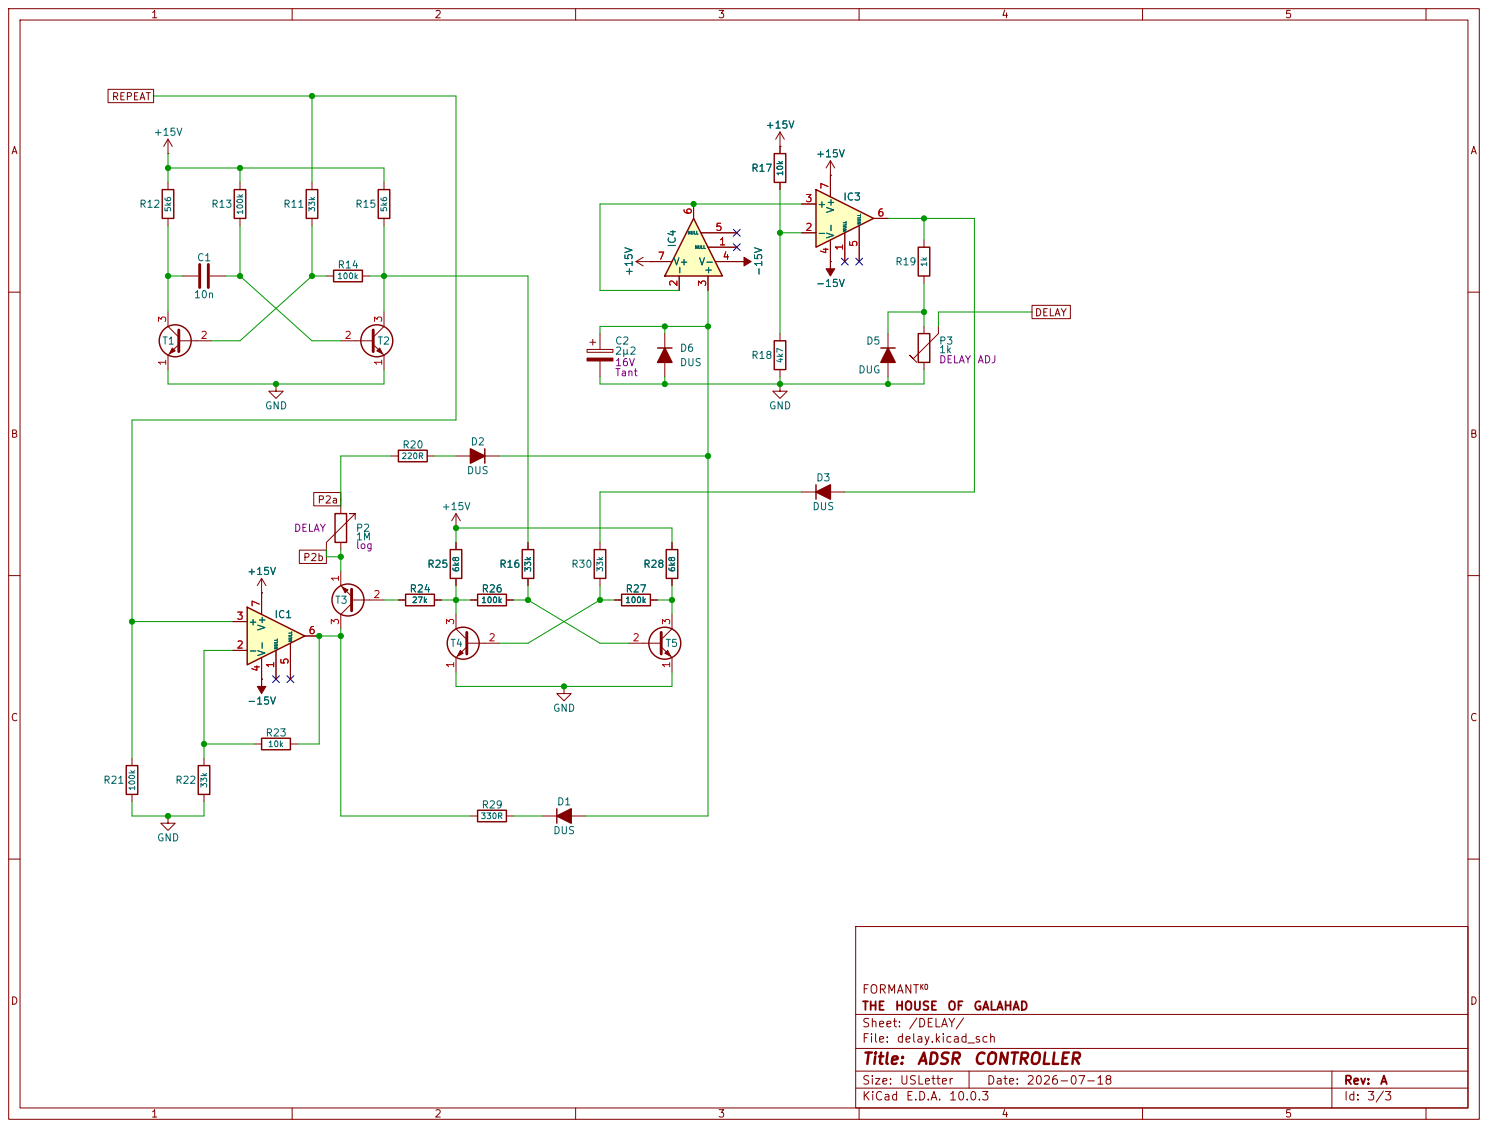
[picture p235: page 3]

FORMANT KO
THE HOUSE OF GALAHAD
Sheet: /DELAY/
File: delay.kicad_sch
Title: ADSR CONTROLLER
