Desval27/FormantKO/modules/ENVELOPE_FOLLOWER/plots/ENVELOPE_FOLLOWER__Assembly.pdf

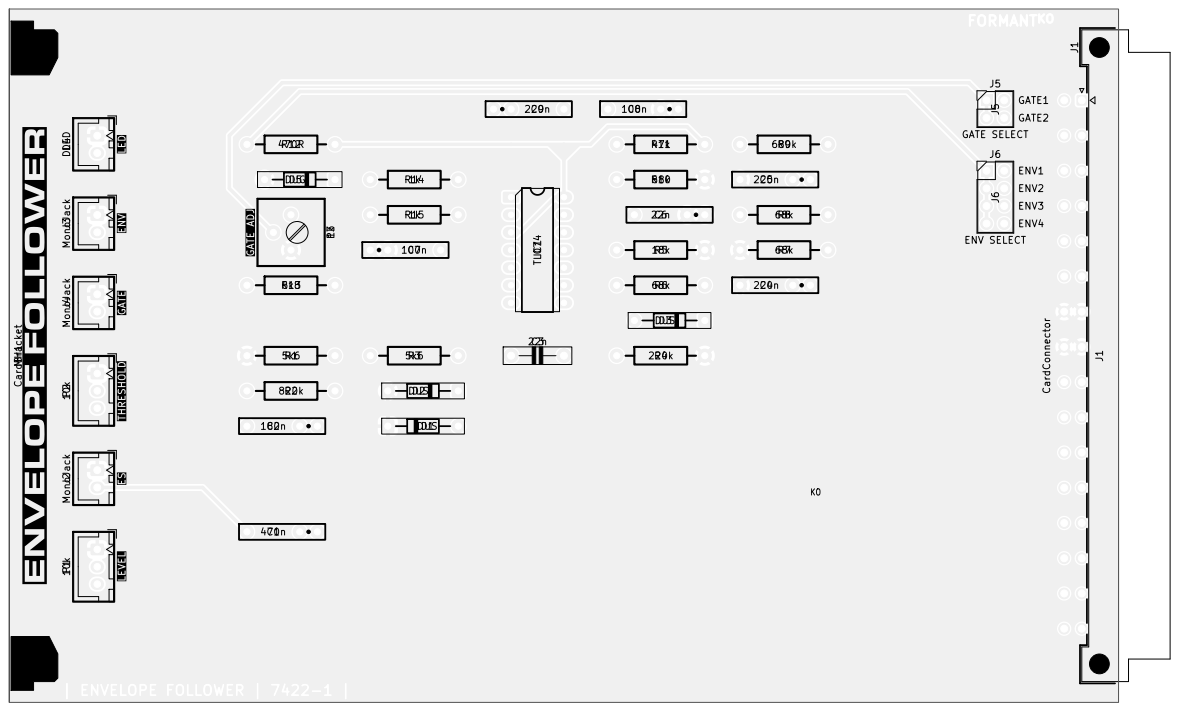
[picture p236: page 1]

Board2Pdf: Black And White TOP - Page 1/2 J6 J5

KO mailto:paul.f.burdette@gmail.com

https://github.com/Desval27/FormantKO/

FORMANT
THE HOUSE OF GALAHAD
Sheet: Black And White TOP
File: ENVELOPE_FOLLOWER.kicad_pcb
Title: ENVELOPE FOLLOWER
KiCad E.D.A. 10.0.4

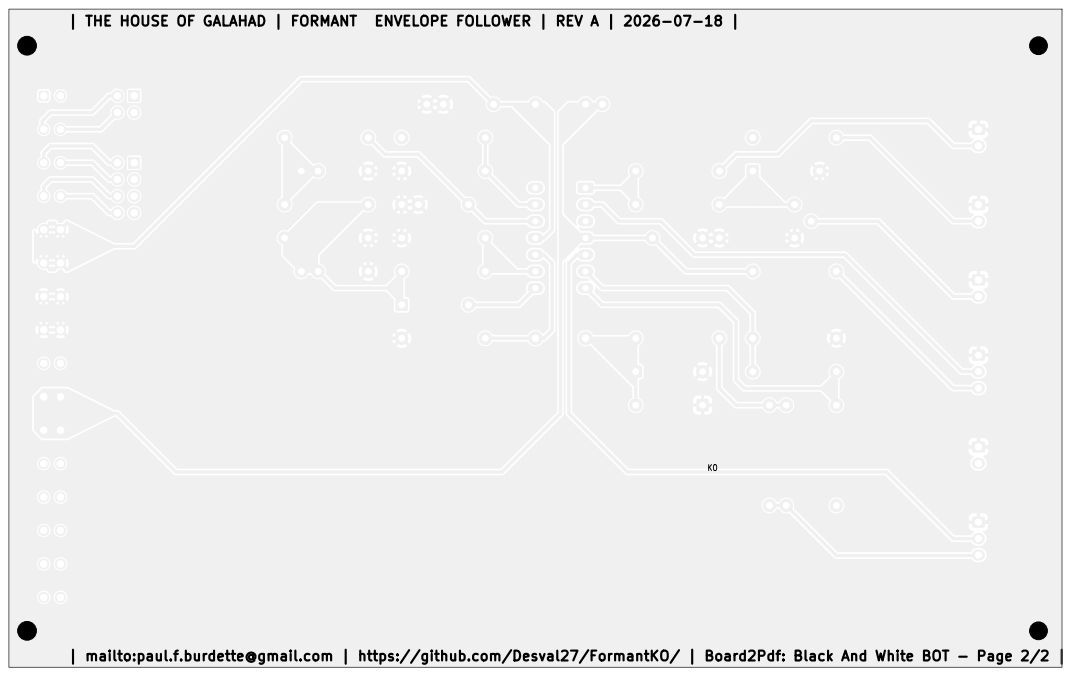
[picture p237: page 2]
D Date: 2026-07-18; Size: USLetter; Rev: A

KO ENVELOPE FOLLOWER | REV A | 2026-07-18

THE HOUSE OF GALAHAD | FORMANT

KO mailto:paul.f.burdette@gmail.com

mailto:paul.f.burdette@gmail.com | https://github.com/Desval27/FormantKO/ | Board2Pdf: Black And White BOT - Page 2/2

Board2Pdf: Black And White BOT - Page 2/2
https://github.com/Desval27/FormantKO/

FORMANT
THE HOUSE OF GALAHAD
Sheet: Black And White BOT
File: ENVELOPE_FOLLOWER.kicad_pcb
Title: ENVELOPE FOLLOWER
KiCad E.D.A. 10.0.4
