Desval27/FormantKO/modules/ENVELOPE_FOLLOWER/plots/ENVELOPE_FOLLOWER__Schematic.pdf

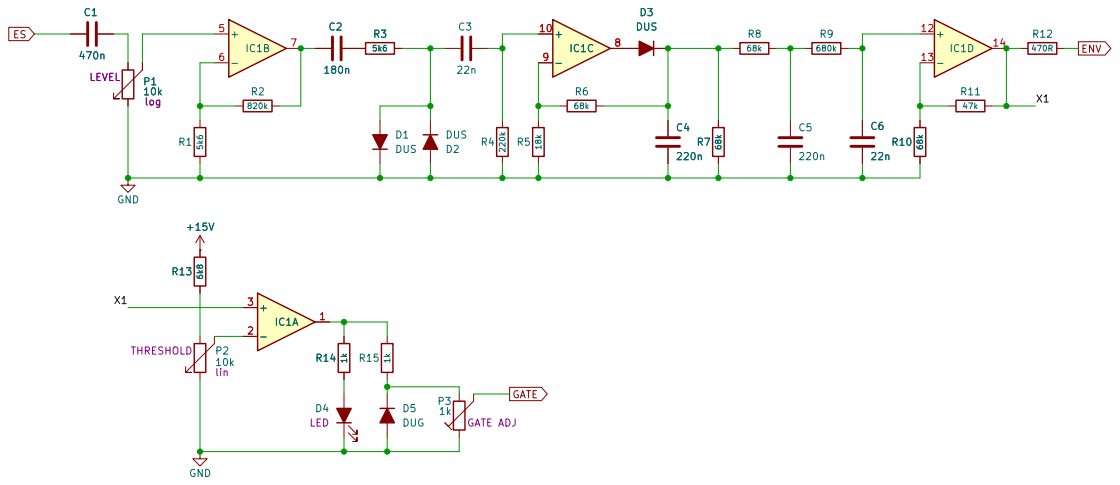
[picture p238: page 1]

FORMANTKO
THE HOUSE OF GALAHAD
Sheet: /ENVELOPE_FOLLOWER/
File: ENVELOPE_FOLLOWER.kicad_sch
Title: ENVELOPE FOLLOWER

Size: USLetter | Rev: A
KiCad E.D.A. 10.0.4 | Id: 1/2

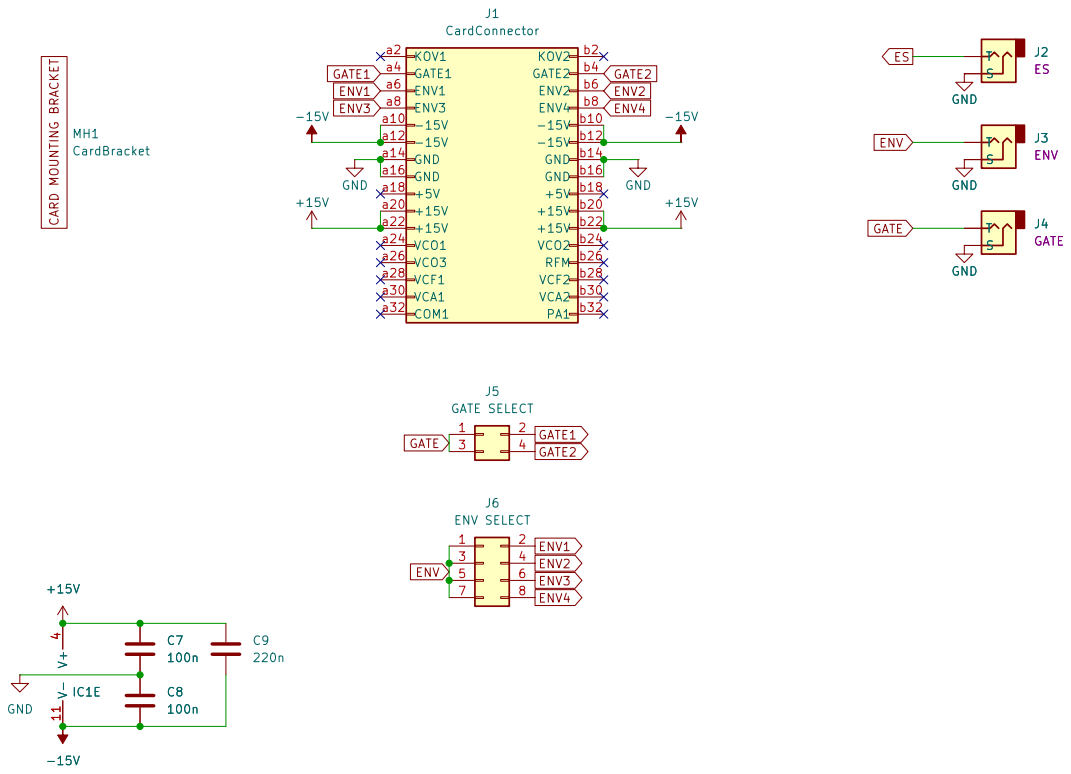
[picture p239: page 2]

THE HOUSE OF GALAHAD
Sheet: /SYSTEM/
File: system.kicad_sch
Title: TEMPLATE

Size: USLetter | Rev: A
KiCad E.D.A. 10.0.4 | Id: 2/2
