Desval27/FormantKO/modules/VC_LFOs/plots/VC_LFOs__Assembly.pdf

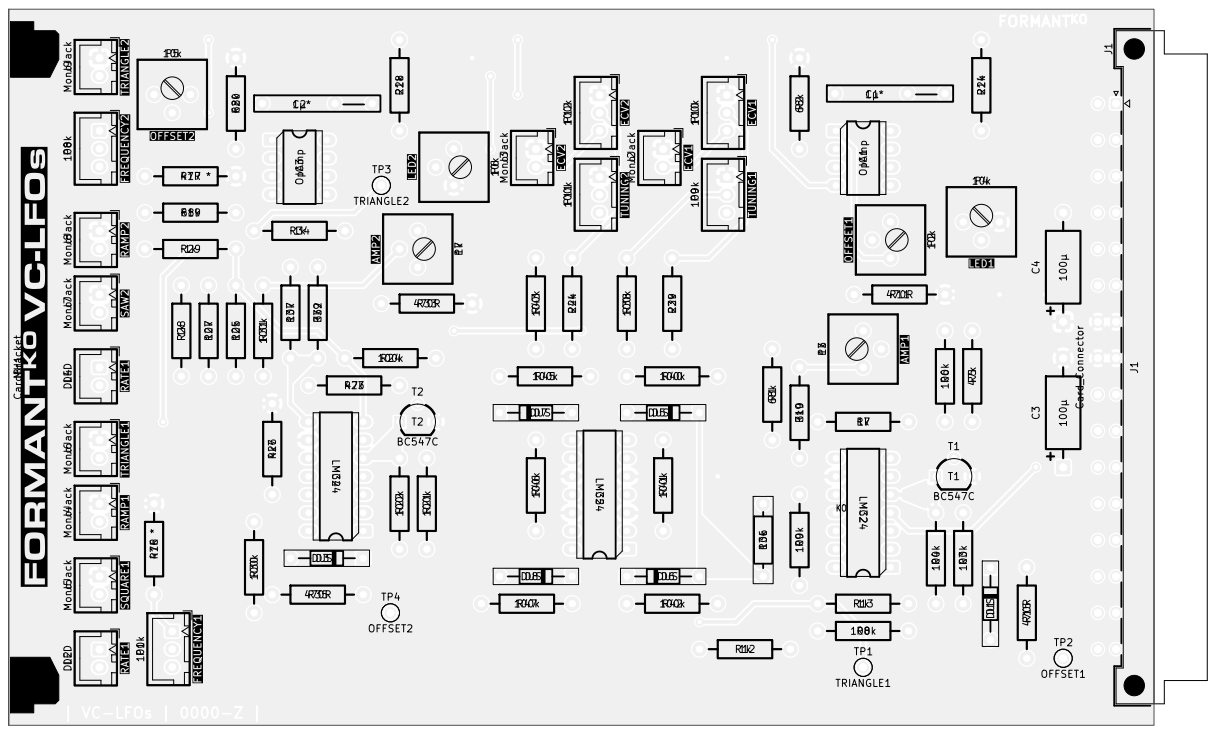
[picture p240: page 1]

KO mailto:paul.f.burdette@gmail.com

https://github.com/Desval27/FormantKO/

FORMANT
THE HOUSE OF GALAHAD
Sheet: Black And White TOP
File: VC_LFOs.kicad_pcb
Title: VC-LFOs
KiCad E.D.A. 10.0.4

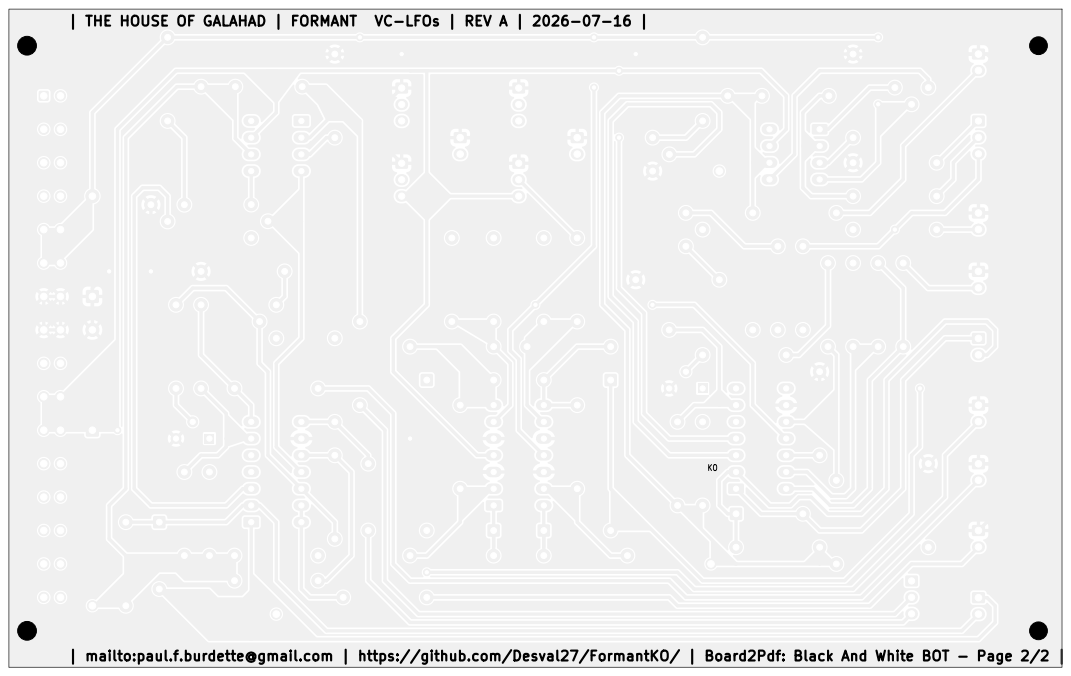
[picture p241: page 2]
D Date: 2026-07-16; Size: USLetter; Rev: A

KO VC-LFOs | REV A | 2026-07-16

THE HOUSE OF GALAHAD | FORMANT

KO mailto:paul.f.burdette@gmail.com

mailto:paul.f.burdette@gmail.com | https://github.com/Desval27/FormantKO/ | Board2Pdf: Black And White BOT - Page 2/2

Board2Pdf: Black And White BOT - Page 2/2
https://github.com/Desval27/FormantKO/

FORMANT
THE HOUSE OF GALAHAD
Sheet: Black And White BOT
File: VC_LFOs.kicad_pcb
Title: VC-LFOs
KiCad E.D.A. 10.0.4
