Desval27/FormantKO/modules/VC_LFOs/plots/VC_LFOs__Schematic.pdf

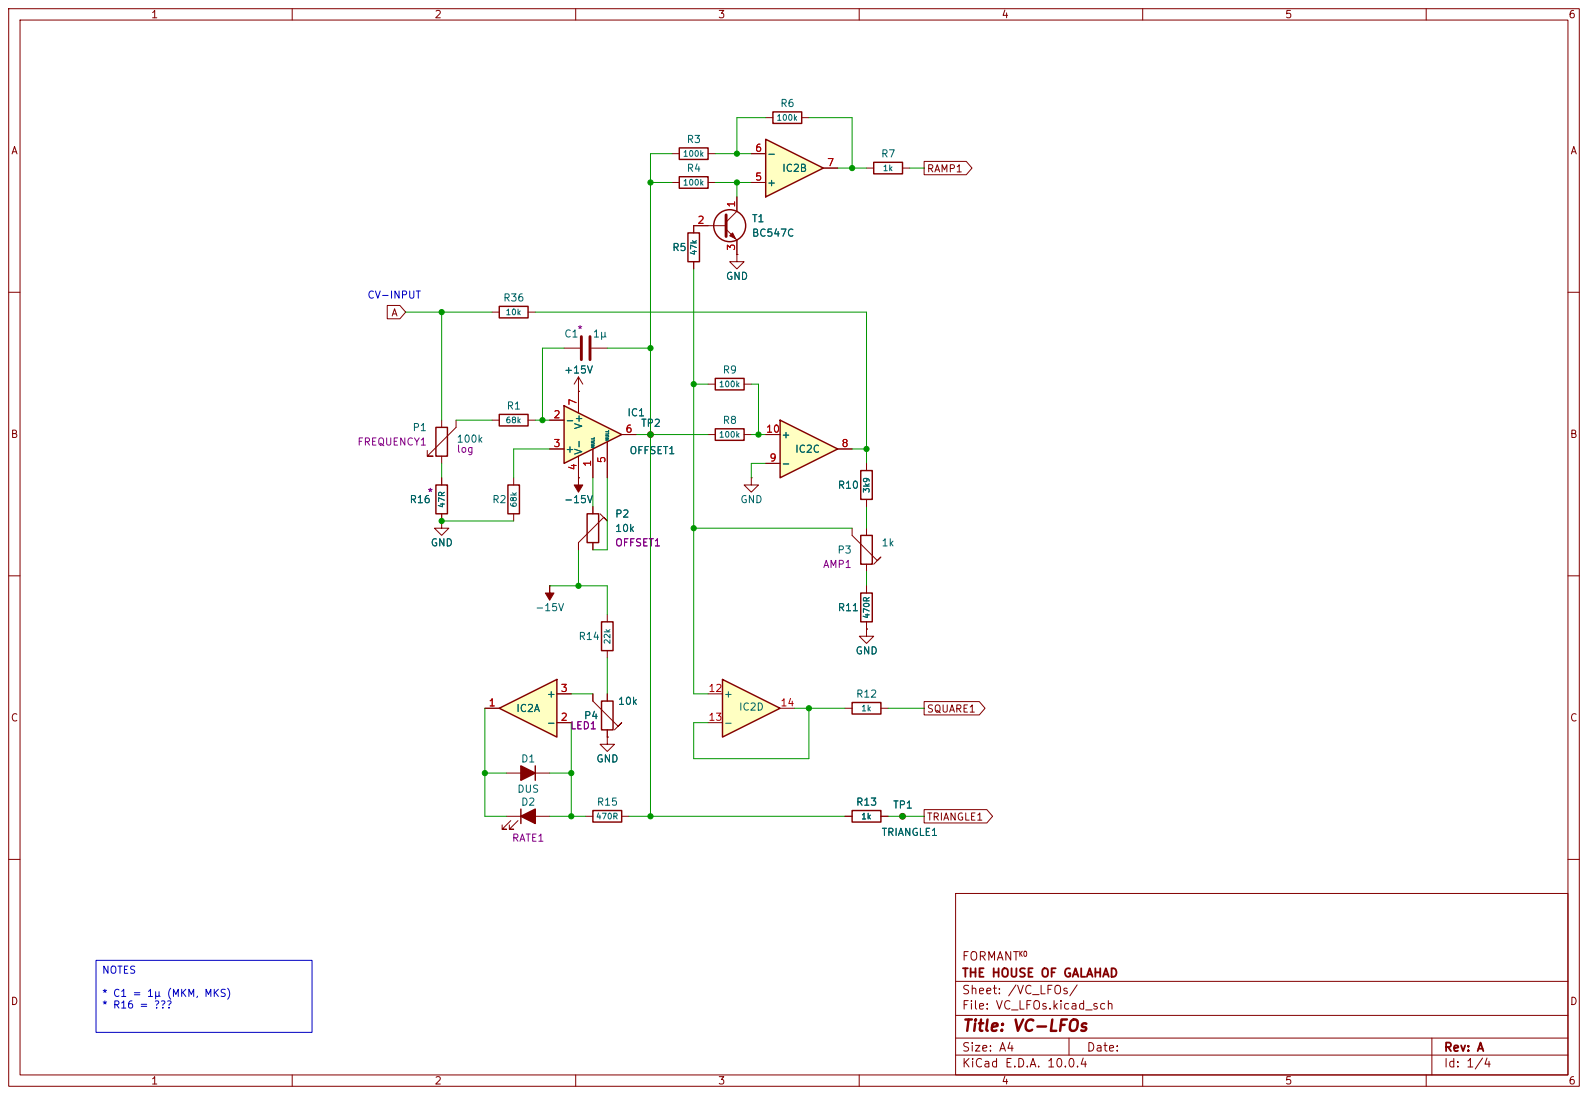
[picture p242: page 1]

FORMANTKO
THE HOUSE OF GALAHAD
Sheet: /VC_LFOs/
File: VC_LFOs.kicad_sch
Title: VC-LFOs

Size: A4 | Rev: A
KiCad E.D.A. 10.0.4 | Id: 1/4

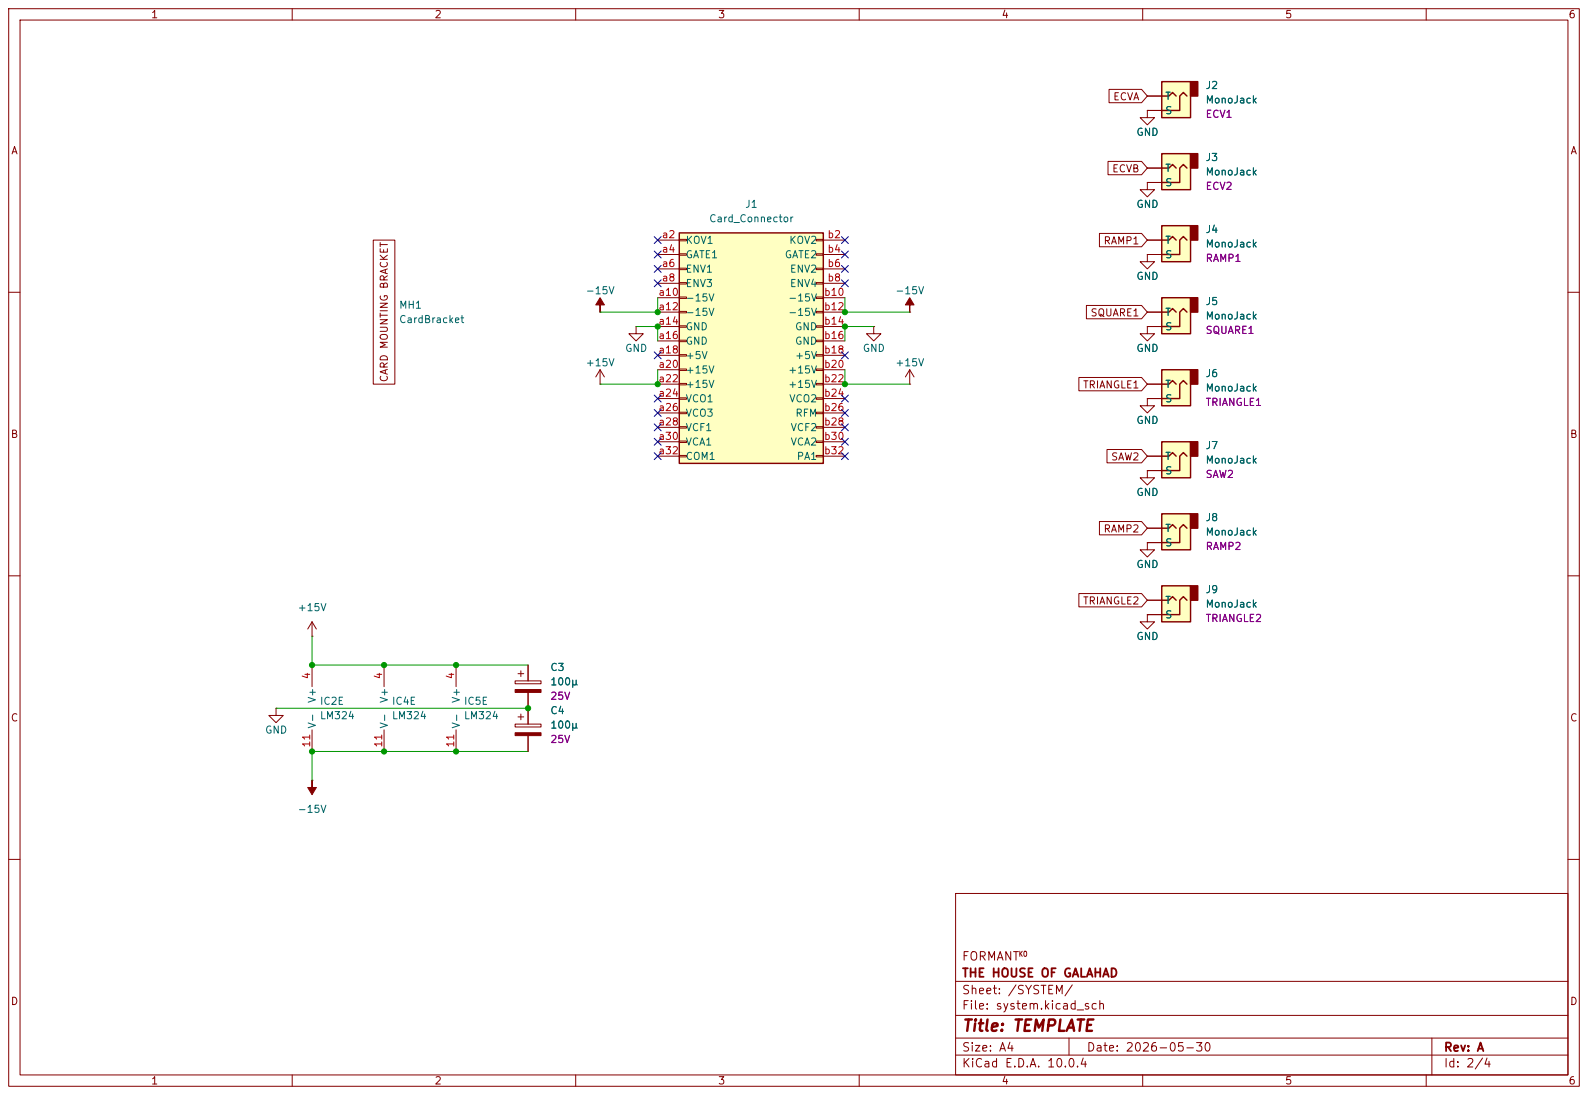
[picture p243: page 2]

THE HOUSE OF GALAHAD
Sheet: /SYSTEM/
File: system.kicad_sch
Title: TEMPLATE

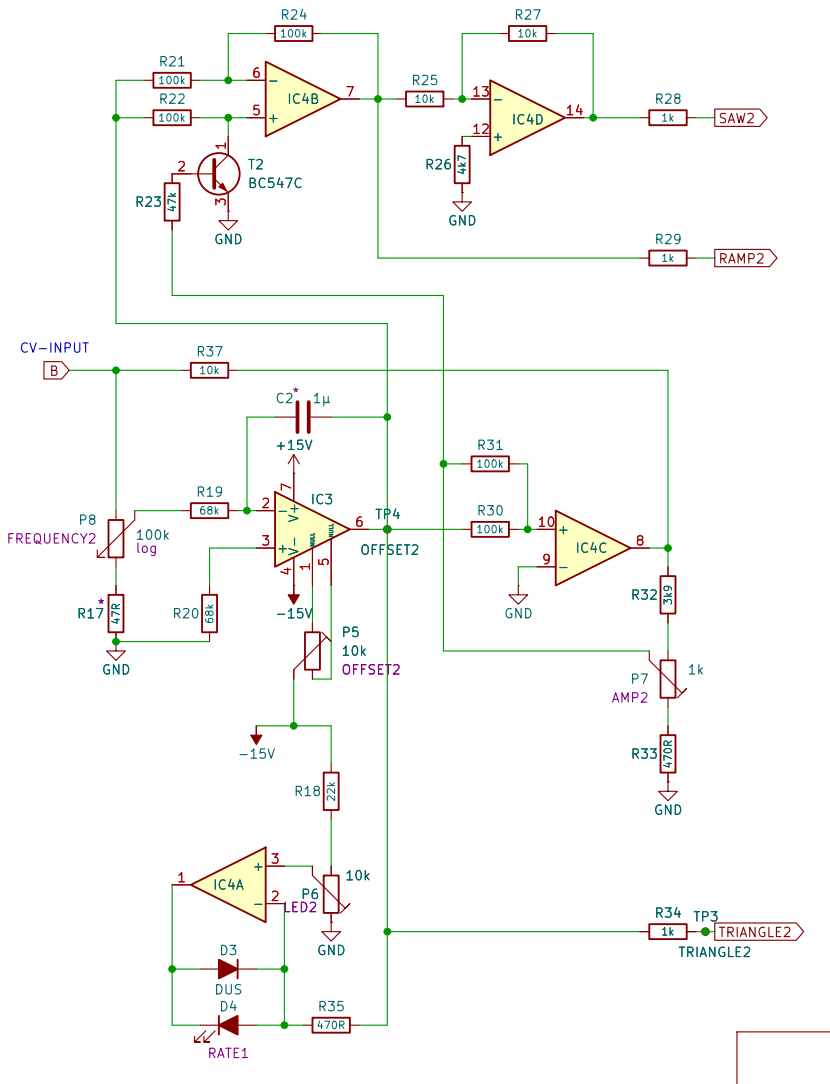
[picture p244: page 3]

THE HOUSE OF GALAHAD
Sheet: /B/
File: b.kicad_sch
Title: VC-LFOs

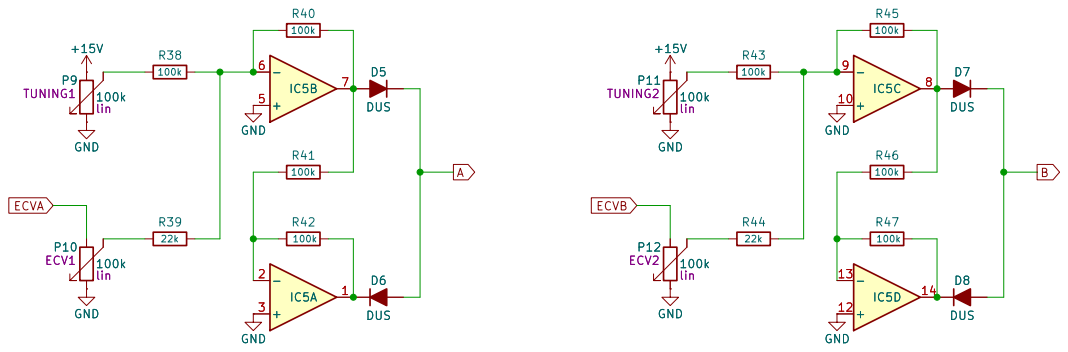
[picture p245: page 4]

THE HOUSE OF GALAHAD
Sheet: /C/
File: c.kicad_sch
Title: VC-LFOs
