Desval27/FormantKO/modules/DUAL_VCA/plots/DUAL_VCA__Assembly.pdf

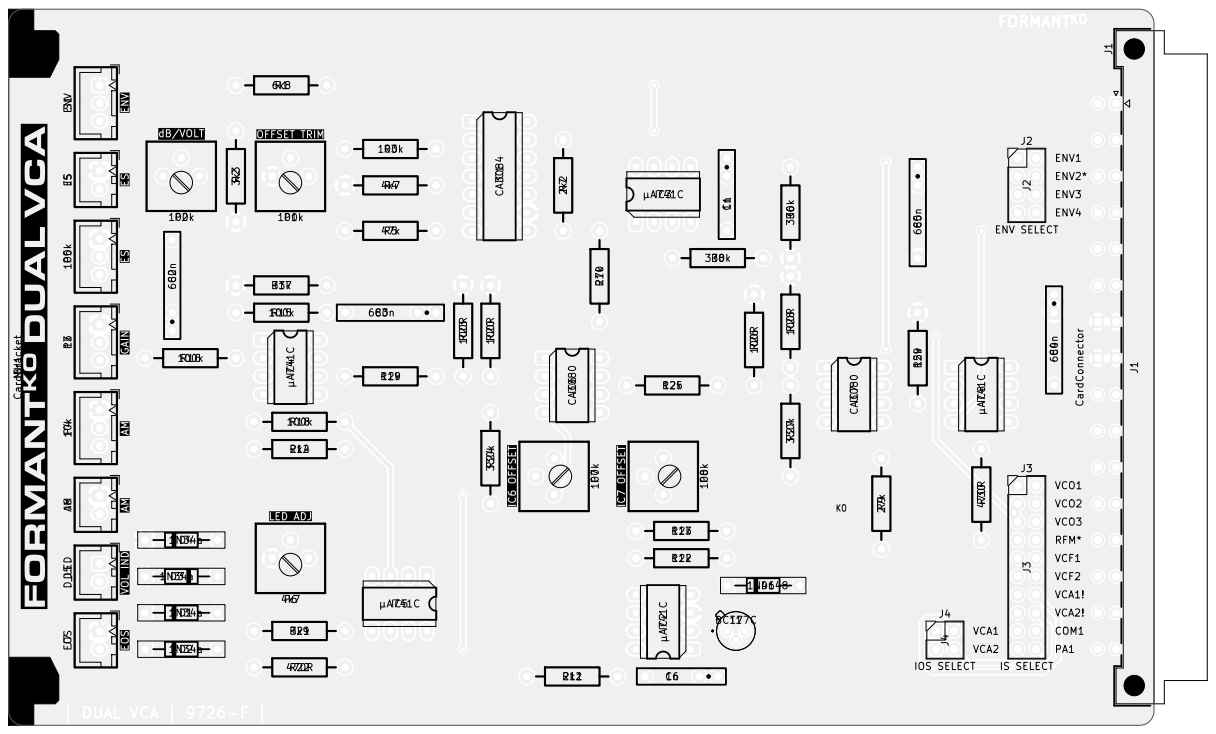
[picture p246: page 1]

KO mailto:paul.f.burdette@gmail.com

https://github.com/Desval27/FormantKO/

FORMANT
THE HOUSE OF GALAHAD
Sheet: Black And White TOP
File: DUAL_VCA.kicad_pcb
Title: DUAL VCA
KiCad E.D.A. 10.0.4

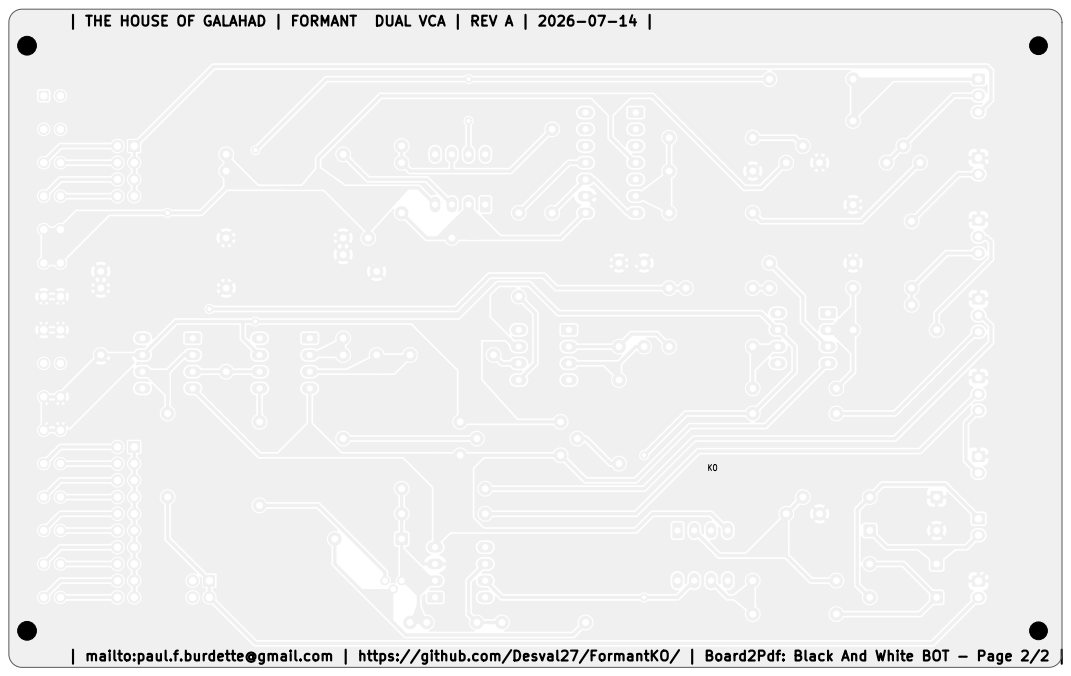
[picture p247: page 2]
D Date: 2026-07-14; Size: USLetter; Rev: A

KO DUAL VCA | REV A | 2026-07-14

THE HOUSE OF GALAHAD | FORMANT

KO mailto:paul.f.burdette@gmail.com

mailto:paul.f.burdette@gmail.com | https://github.com/Desval27/FormantKO/ | Board2Pdf: Black And White BOT - Page 2/2

Board2Pdf: Black And White BOT - Page 2/2
https://github.com/Desval27/FormantKO/

FORMANT
THE HOUSE OF GALAHAD
Sheet: Black And White BOT
File: DUAL_VCA.kicad_pcb
Title: DUAL VCA
KiCad E.D.A. 10.0.4
