Desval27/FormantKO/modules/DUAL_VCA/plots/DUAL_VCA__Schematic.pdf

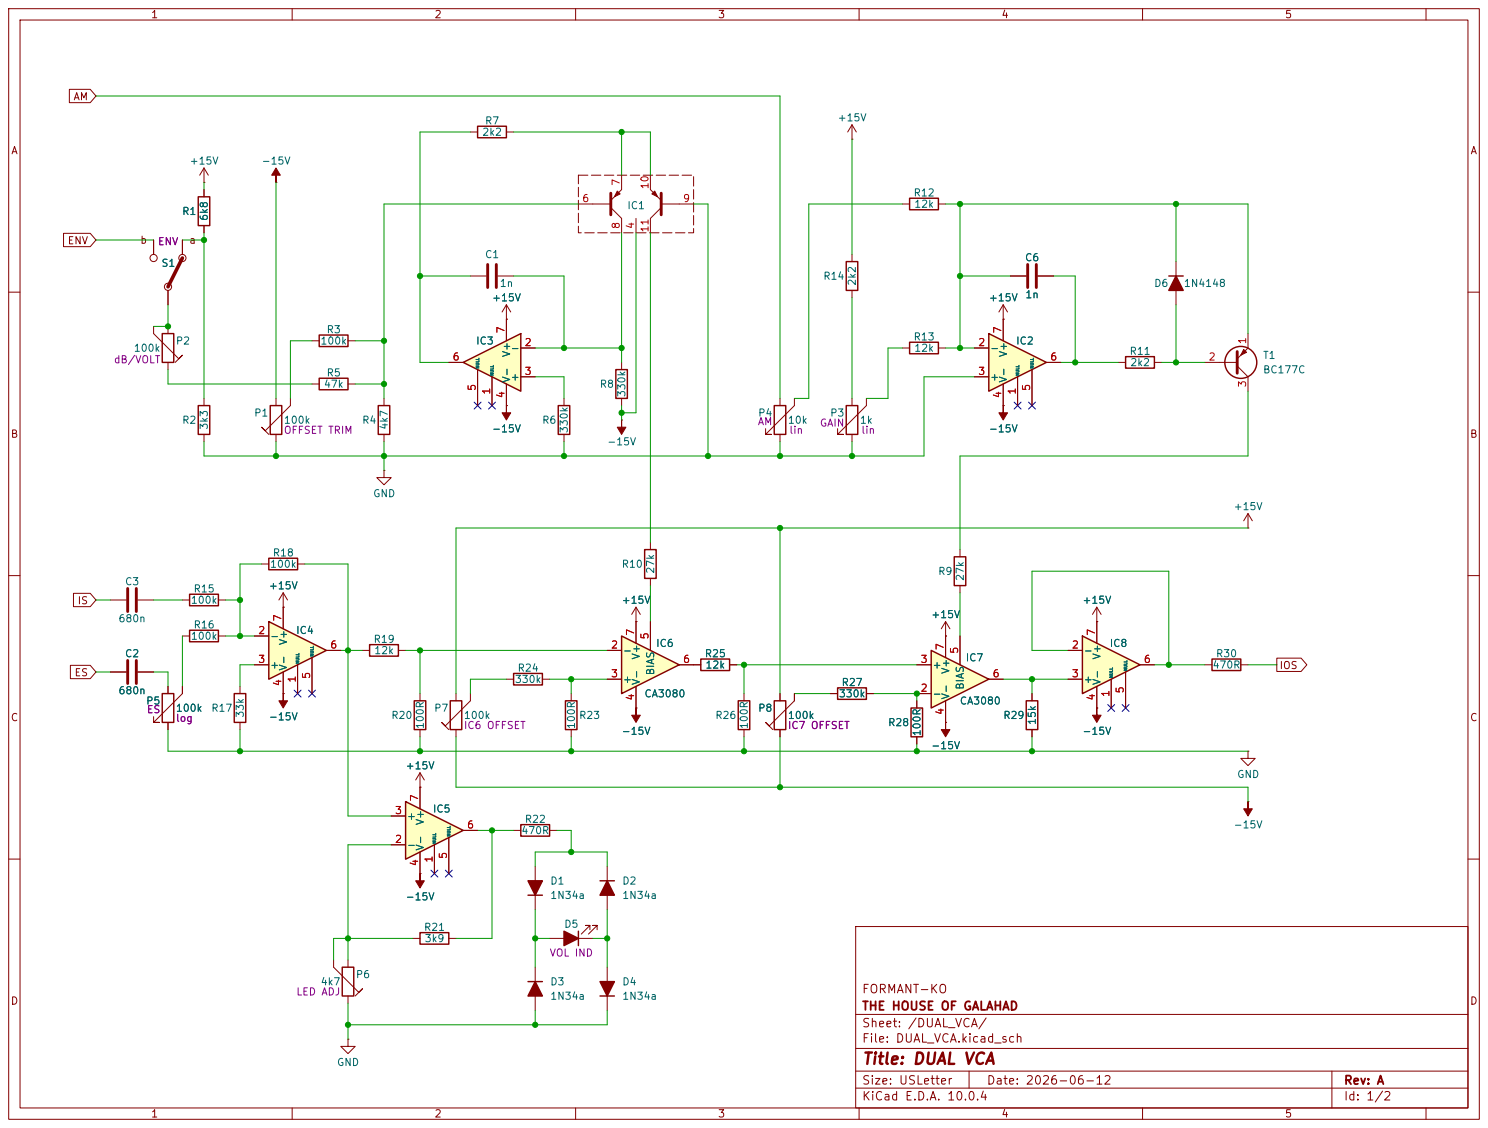
[picture p248: page 1]

FORMANT-KO
THE HOUSE OF GALAHAD
Sheet: /DUAL_VCA/
File: DUAL_VCA.kicad_sch
Title: DUAL VCA

Size: USLetter | Rev: A
KiCad E.D.A. 10.0.4 | Id: 1/2

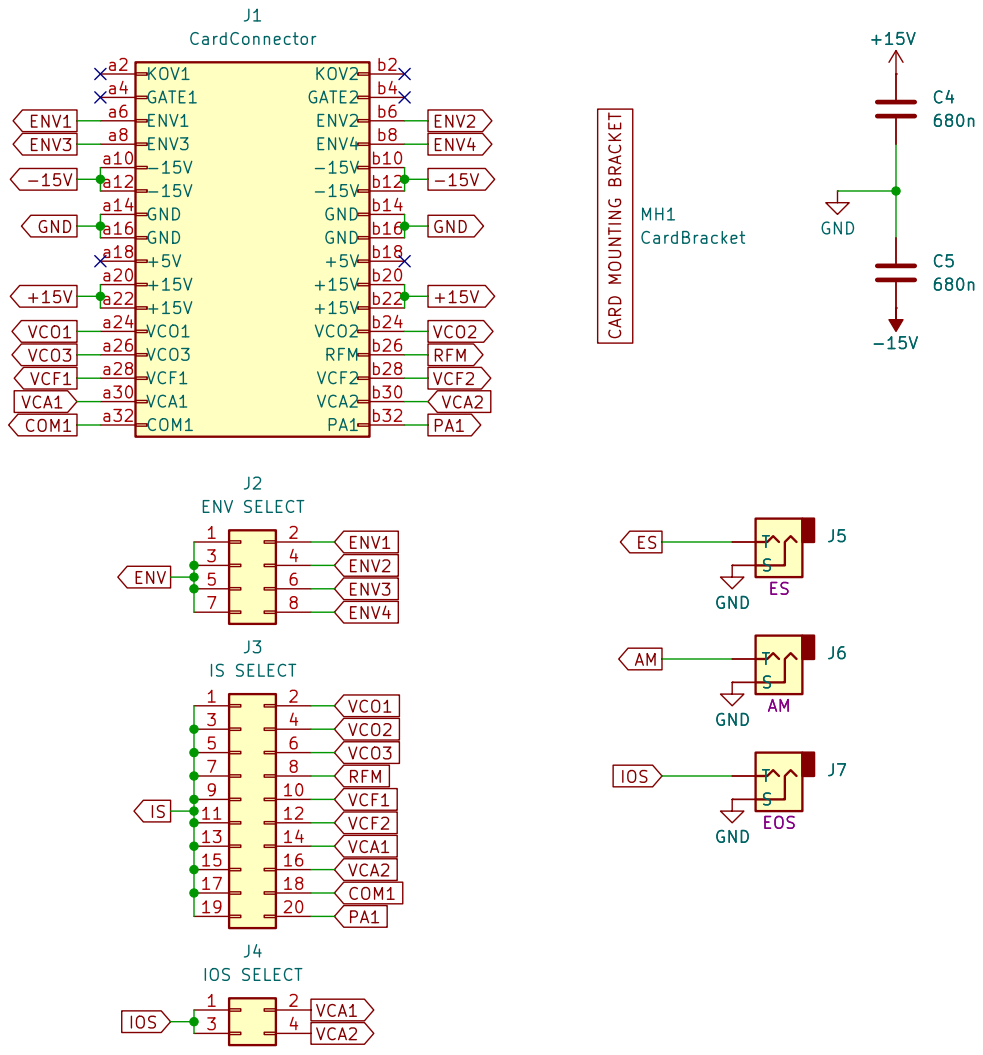
[picture p249: page 2]

FORMANT-KO
THE HOUSE OF GALAHAD
Sheet: /SYSTEM/
File: system.kicad_sch
Title: DUAL VCA

Size: USLetter | Rev: A
KiCad E.D.A. 10.0.4 | Id: 2/2
