Desval27/FormantKO/system/PSU/plots/PSU__Schematic.pdf

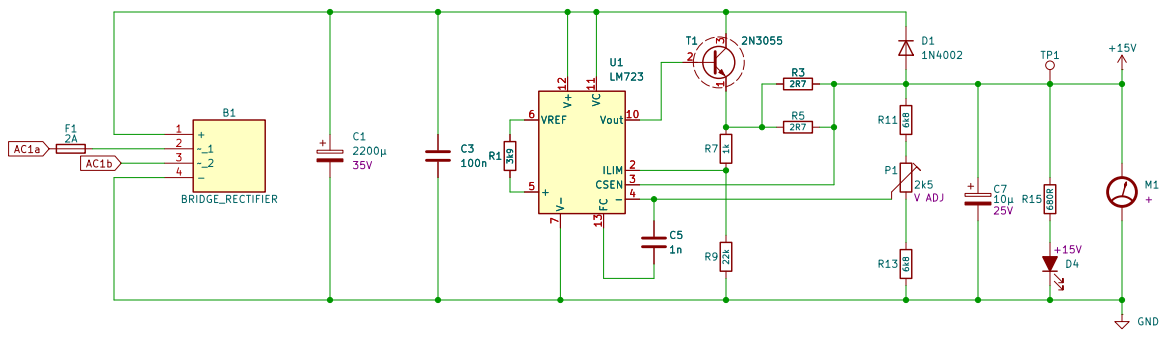
[picture p250: page 1]

FORMANT-KO
THE HOUSE OF GALAHAD
Sheet: /+15V/
File: PSU.kicad_sch
Title: PSU

Size: USLetter | Rev: A
KiCad E.D.A. 10.0.4 | Id: 1/4

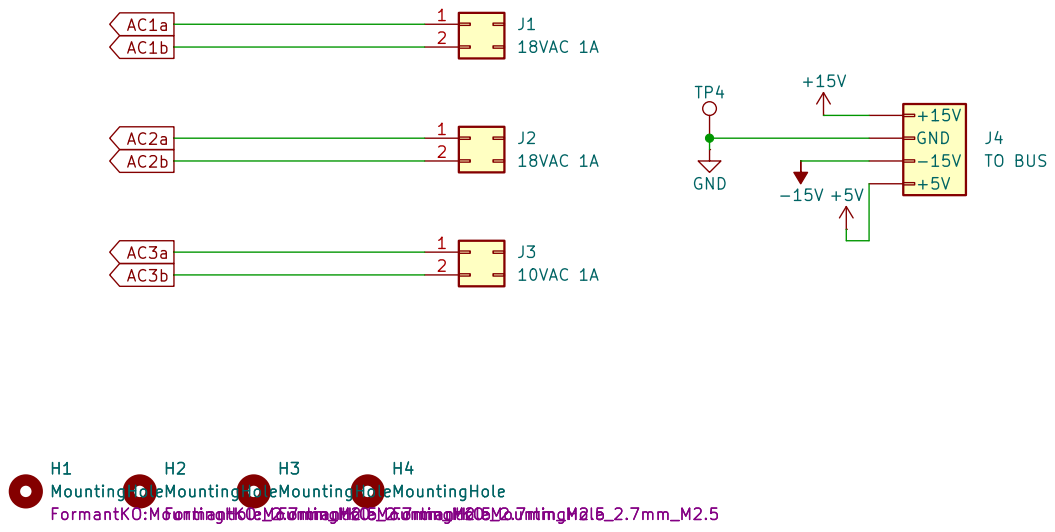
[picture p251: page 2]

THE HOUSE OF GALAHAD
Sheet: /SYSTEM/
File: system.kicad_sch
Title: PSU

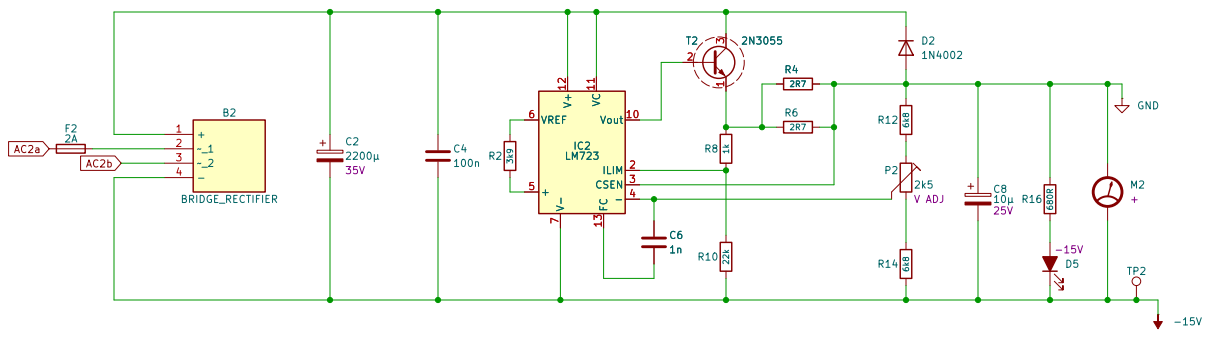
[picture p252: page 3]

FORMANT-KO
THE HOUSE OF GALAHAD
Sheet: /-15V/
File: -15v.kicad_sch
Title: PSU

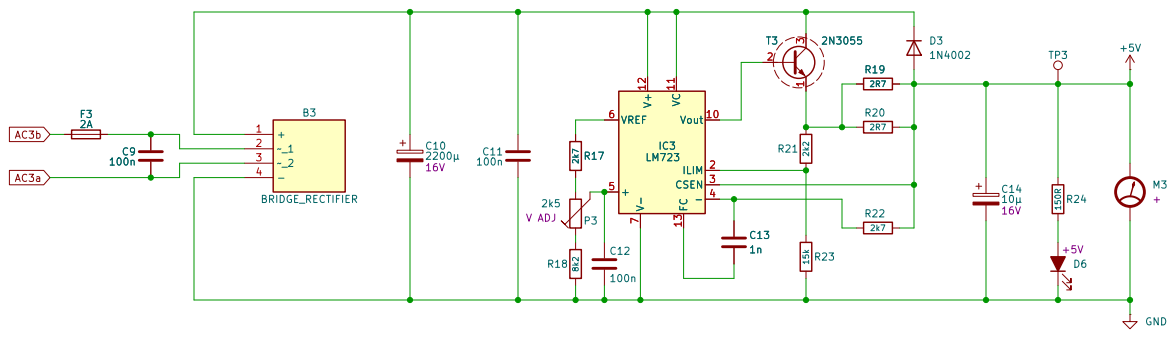
[picture p253: page 4]
