Desval27/FormantKO/modules/SAMPLE_AND_HOLD/plots/SAMPLE_AND_HOLD__Assembly.pdf

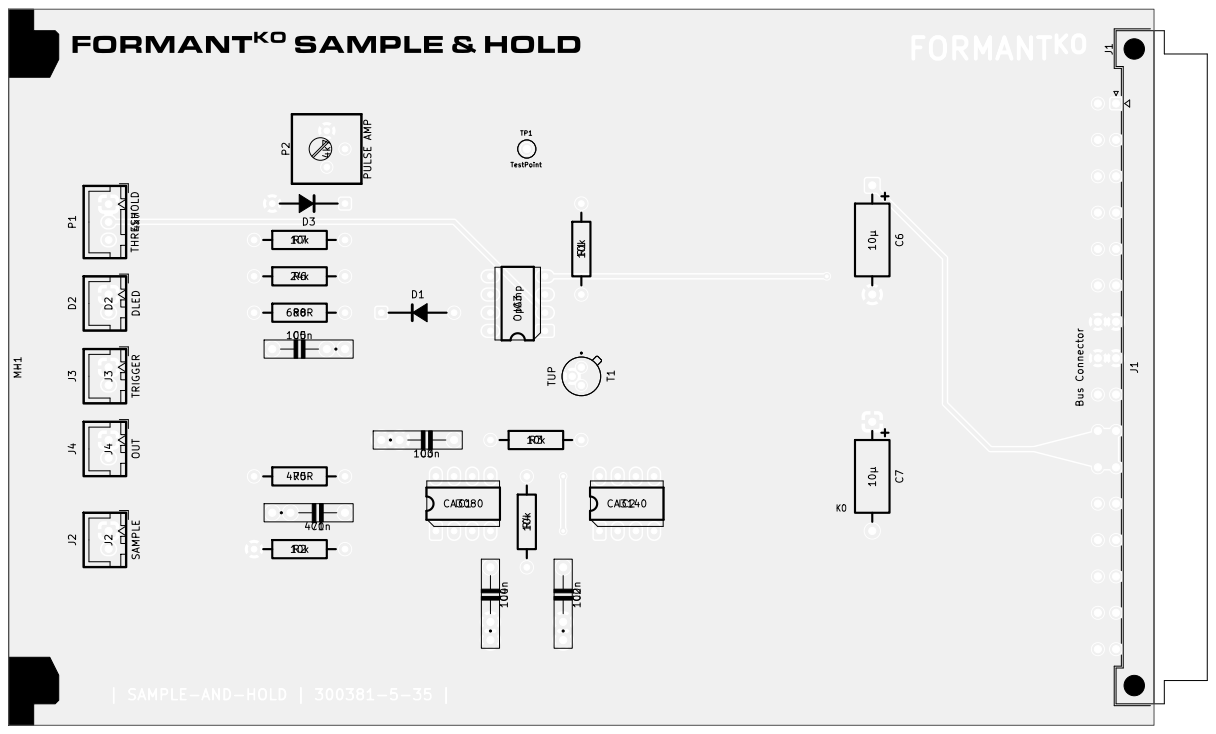
[picture p254: page 1]

P1 THRESHOLD P2 PULSE AMP IC3 J3 TRIGGER

FORMANT
THE HOUSE OF GALAHAD
Sheet: Black And White TOP
File: SAMPLE_AND_HOLD.kicad_pcb
Title: SAMPLE-AND-HOLD
KiCad E.D.A. 10.0.4

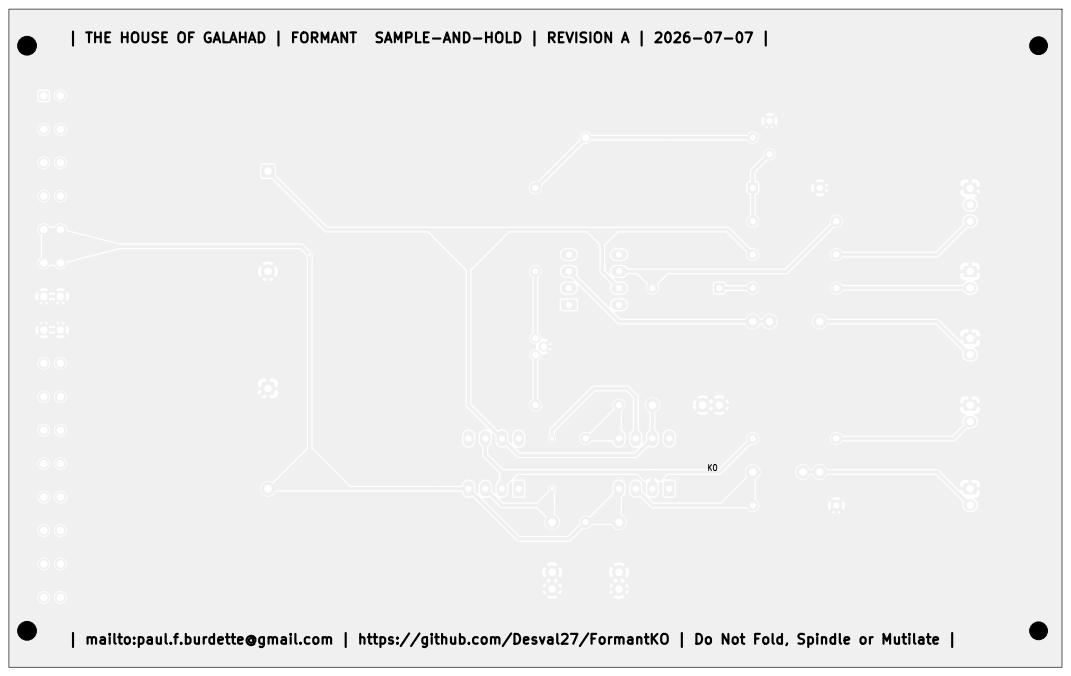
[picture p255: page 2]
D Date: 2026-07-07; Size: USLetter; Rev: A

KO SAMPLE-AND-HOLD | REVISION A | 2026-07-07

THE HOUSE OF GALAHAD | FORMANT

KO Board2Pdf: Black And White BOT - Page 2/2

mailto:paul.f.burdette@gmail.com | https://github.com/Desval27/FormantKO | Do Not Fold, Spindle or Mutilate

FORMANT
THE HOUSE OF GALAHAD
Sheet: Black And White BOT
File: SAMPLE_AND_HOLD.kicad_pcb
Title: SAMPLE-AND-HOLD
KiCad E.D.A. 10.0.4
