Desval27/FormantKO/modules/SAMPLE_AND_HOLD/plots/SAMPLE_AND_HOLD__schematic.pdf

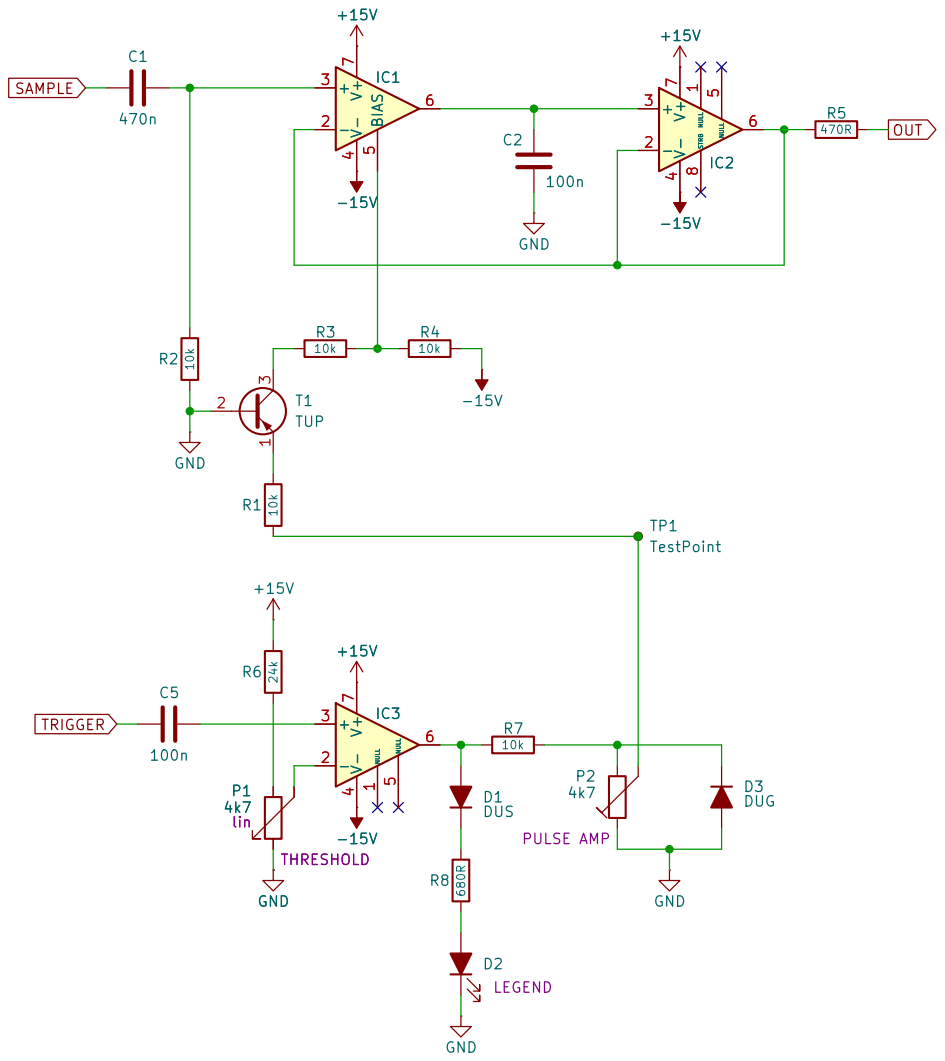
[picture p256: page 1]

THE HOUSE OF GALAHAD
Sheet: /SAMPLE_AND_HOLD/
File: SAMPLE_AND_HOLD.kicad_sch
Title: SAMPLE-AND-HOLD

Size: USLetter | Rev: A
KiCad E.D.A. 10.0.4 | Id: 1/2

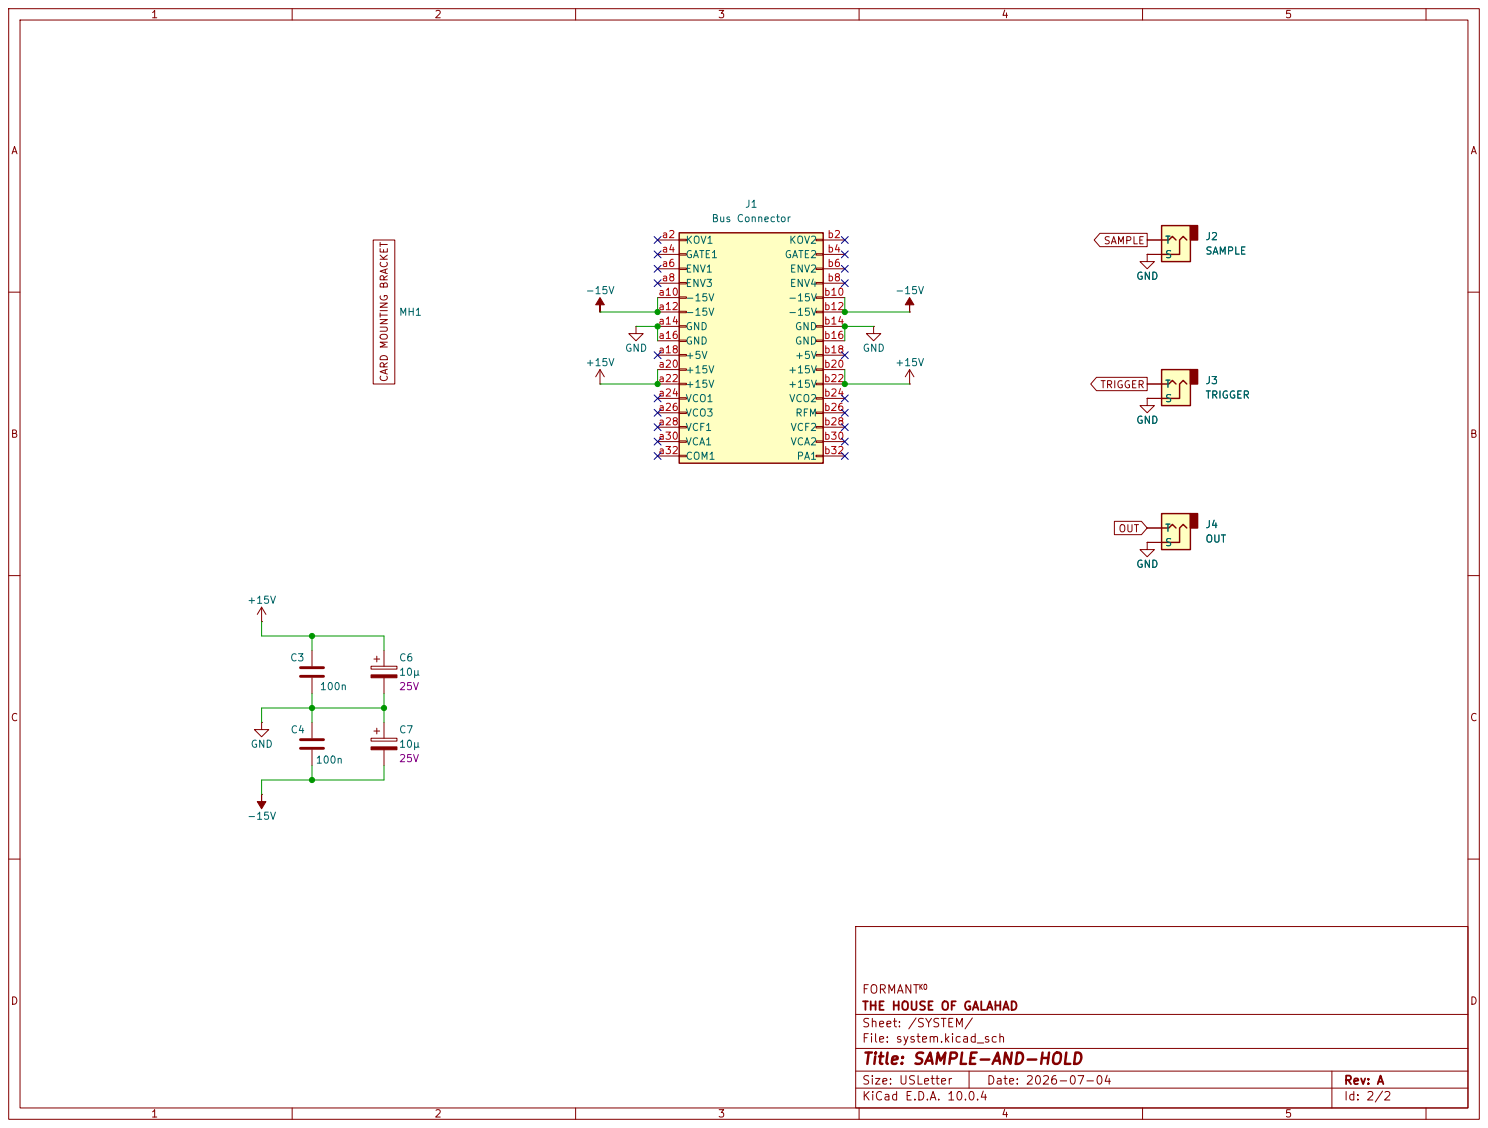
[picture p257: page 2]

FORMANTKO
THE HOUSE OF GALAHAD
Sheet: /SYSTEM/
File: system.kicad_sch
Title: SAMPLE-AND-HOLD

Size: USLetter | Rev: A
KiCad E.D.A. 10.0.4 | Id: 2/2
