Desval27/FormantKO/modules/SEQUENCER/plots/SEQUENCER__schematic.pdf

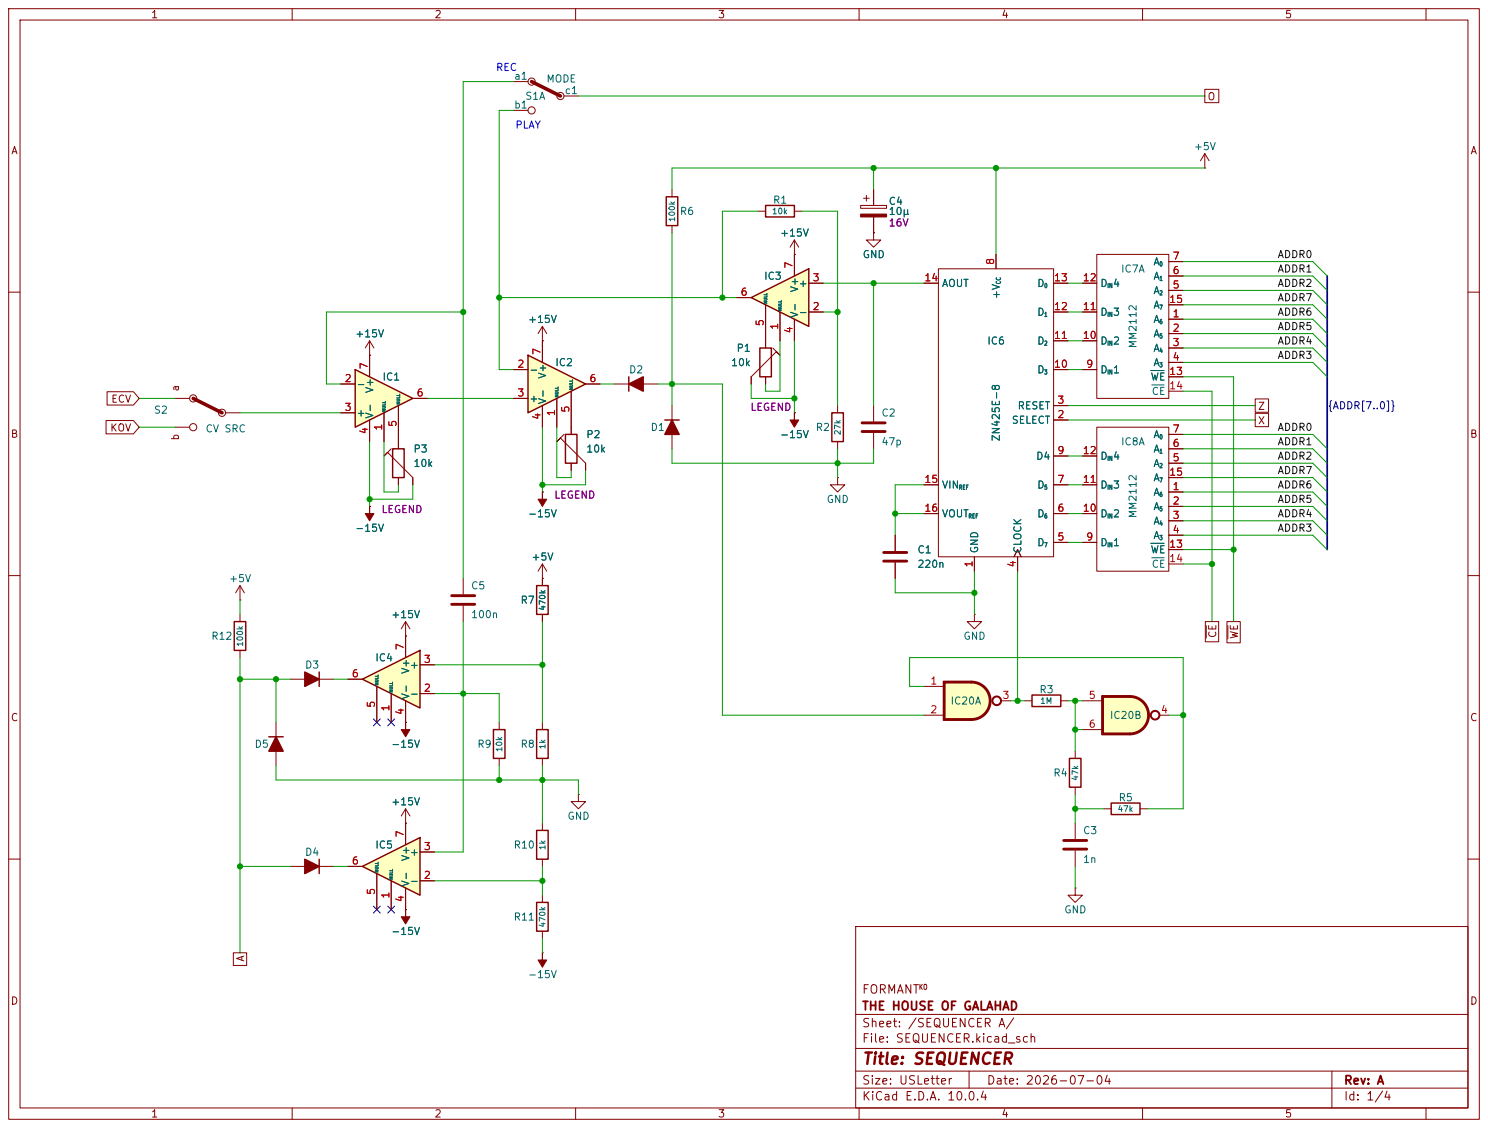
[picture p258: page 1]

THE HOUSE OF GALAHAD
Sheet: /SEQUENCER A/
File: SEQUENCER.kicad_sch
Title: SEQUENCER

Size: USLetter | Rev: A
KiCad E.D.A. 10.0.4 | Id: 1/4

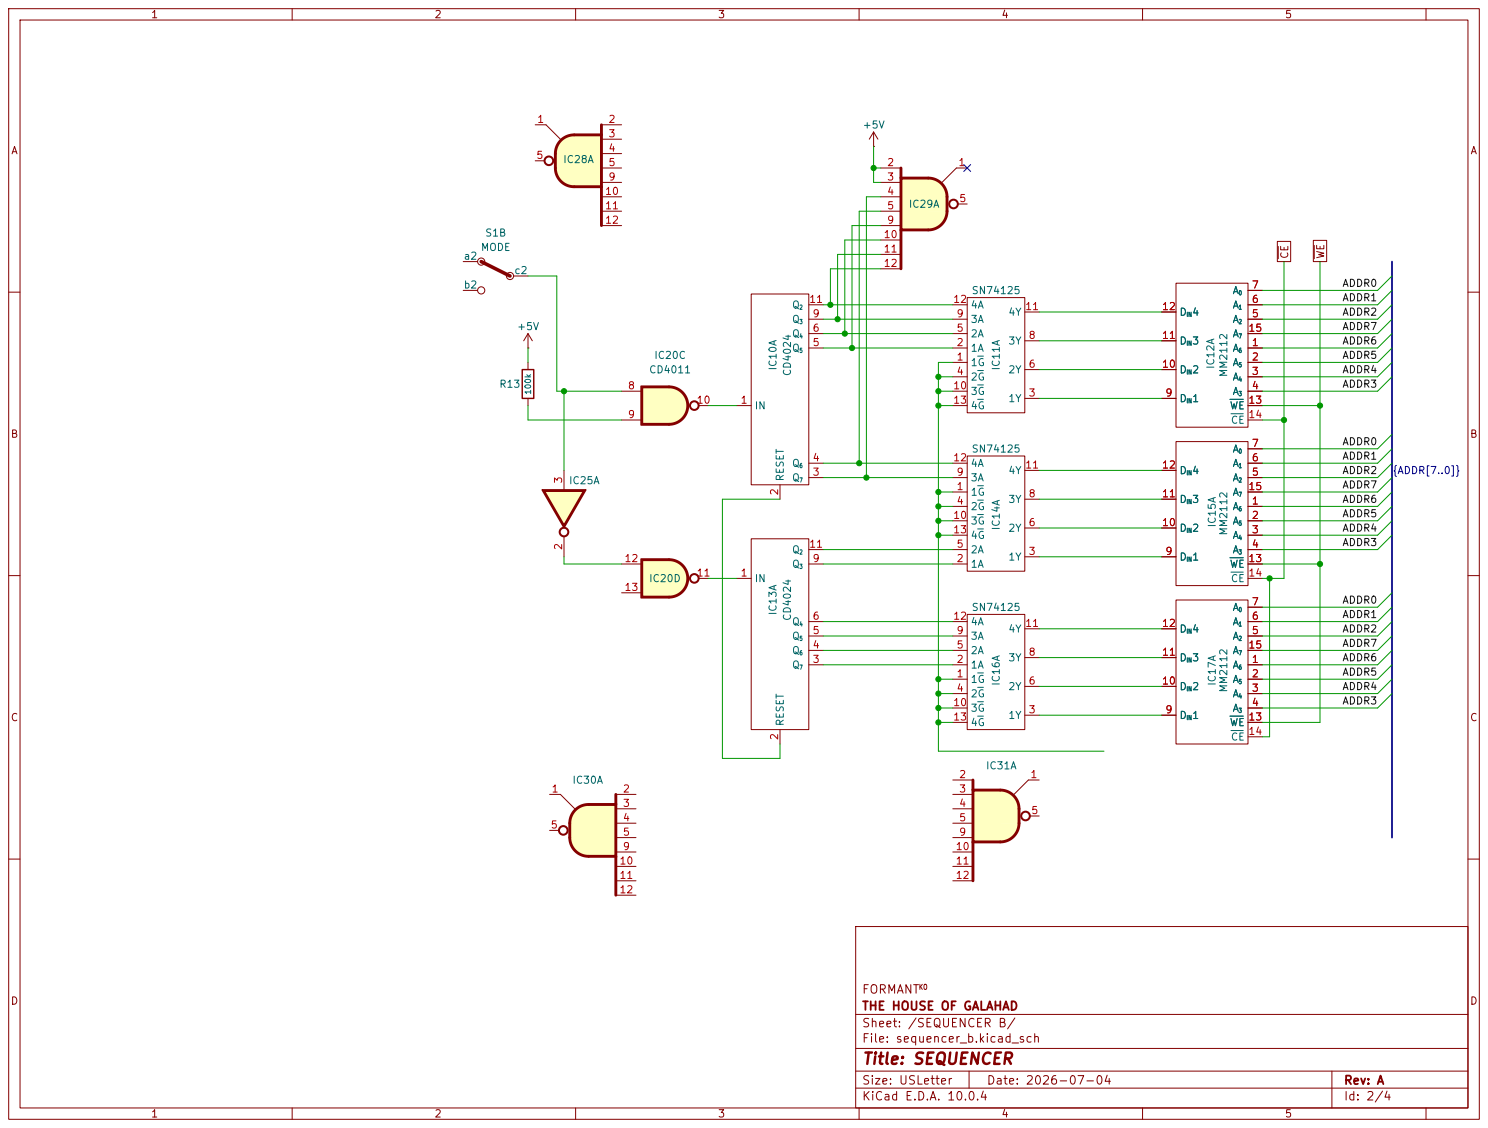
[picture p259: page 2]

FORMANTKO
THE HOUSE OF GALAHAD
Sheet: /SEQUENCER B/
File: sequencer_b.kicad_sch
Title: SEQUENCER

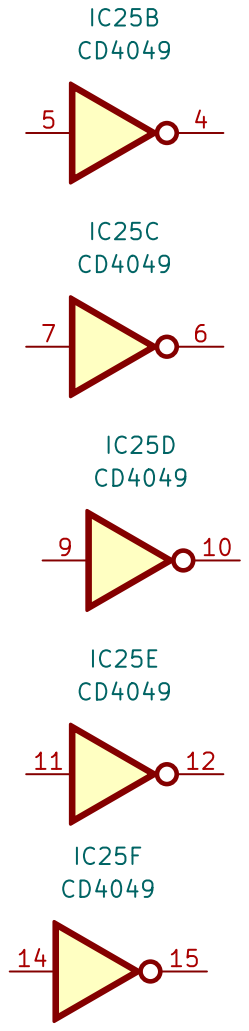
[picture p260: page 3]

THE HOUSE OF GALAHAD
Sheet: /SEQUENCER C/
File: sequencer_c.kicad_sch
Title: SEQUENCER

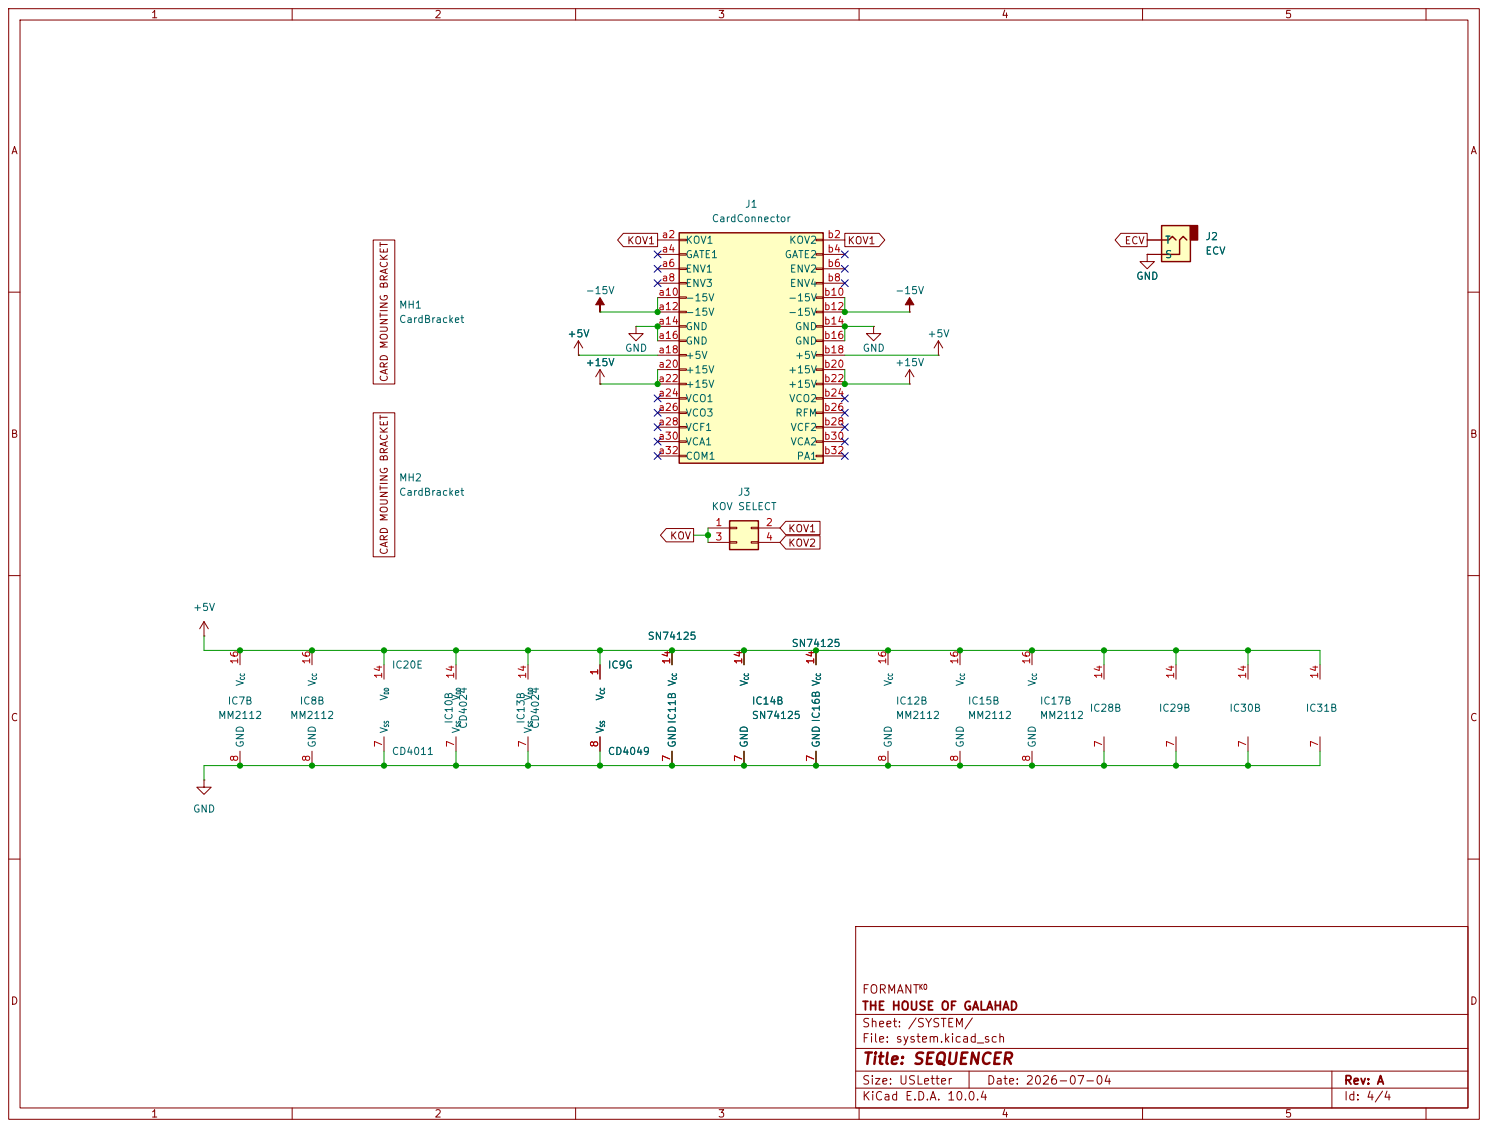
[picture p261: page 4]

THE HOUSE OF GALAHAD
Sheet: /SYSTEM/
File: system.kicad_sch
Title: SEQUENCER
