Desval27/FormantKO/system/CARD_EXTENDER/plots/CARD_EXTENDER__Assembly.pdf

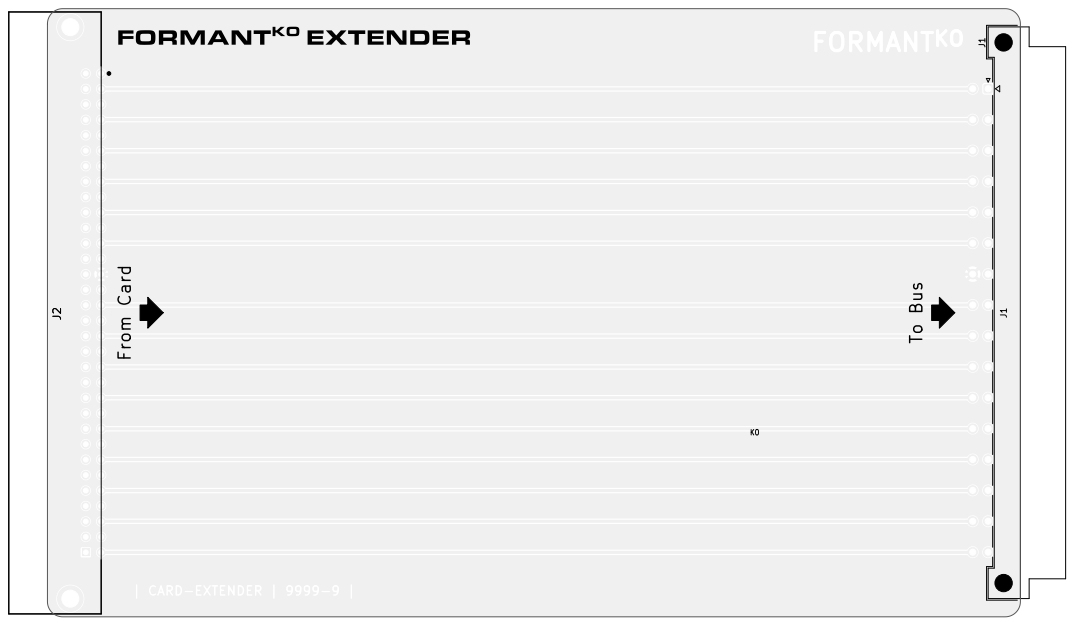
[picture p262: page 1]
D Date: 2026-07-04; Size: USLetter; Rev: A; KO Board2Pdf: Black And White TOP - Page 1/2 J2

J2 From Card J1 To Bus

FORMANT
THE HOUSE OF GALAHAD
Sheet: Black And White TOP
File: CARD_EXTENDER.kicad_pcb
Title: CARD-EXTENDER
KiCad E.D.A. 10.0.4

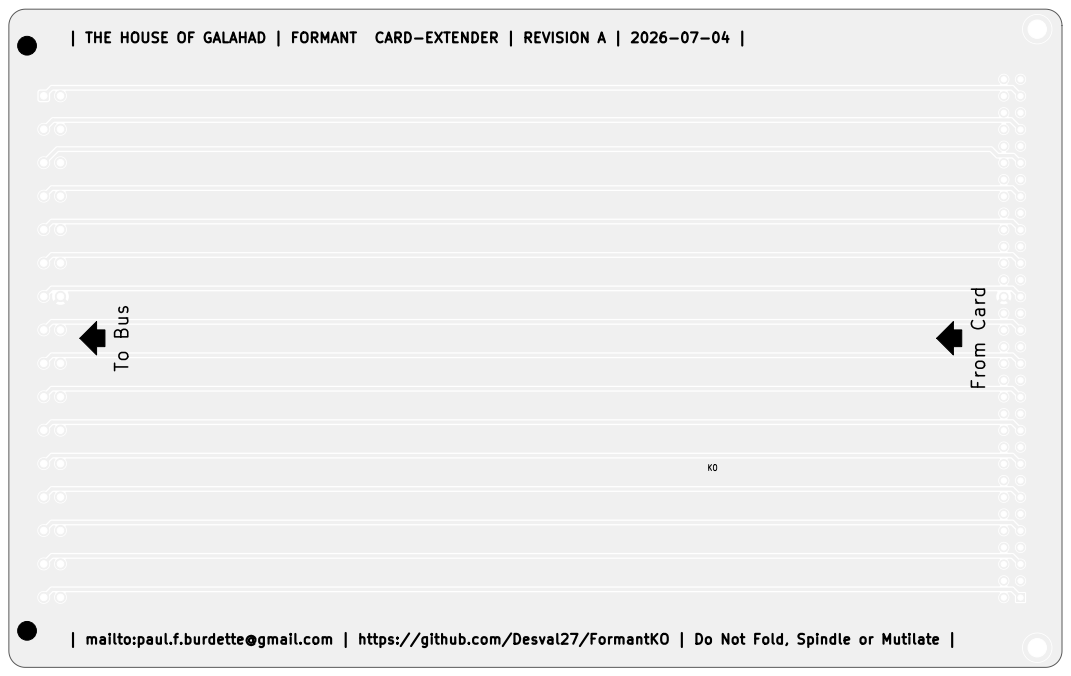
[picture p263: page 2]
D Date: 2026-07-04; Size: USLetter; Rev: A

KO CARD-EXTENDER | REVISION A | 2026-07-04

THE HOUSE OF GALAHAD | FORMANT

From Card To Bus

KO Board2Pdf: Black And White BOT - Page 2/2

mailto:paul.f.burdette@gmail.com | https://github.com/Desval27/FormantKO | Do Not Fold, Spindle or Mutilate

FORMANT
THE HOUSE OF GALAHAD
Sheet: Black And White BOT
File: CARD_EXTENDER.kicad_pcb
Title: CARD-EXTENDER
KiCad E.D.A. 10.0.4
