Desval27/FormantKO/system/CARD_EXTENDER/plots/CARD_EXTENDER__schematic.pdf

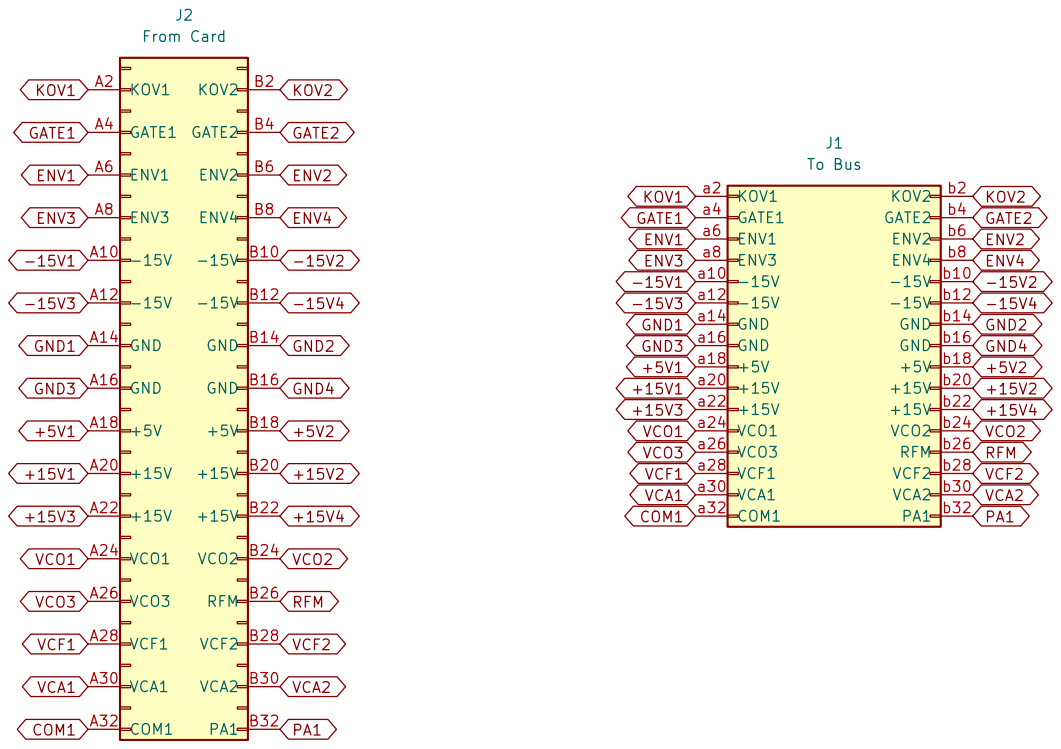
[picture p264: page 1]

FORMANTKO
THE HOUSE OF GALAHAD
Sheet: /
File: system.kicad_sch
Title: CARD-EXTENDER

Size: USLetter | Rev: A
KiCad E.D.A. 10.0.4 | Id: 2/1
