Desval27/FormantKO/modules/LFO_SINE/plots/LFO_SINE__Assembly.pdf

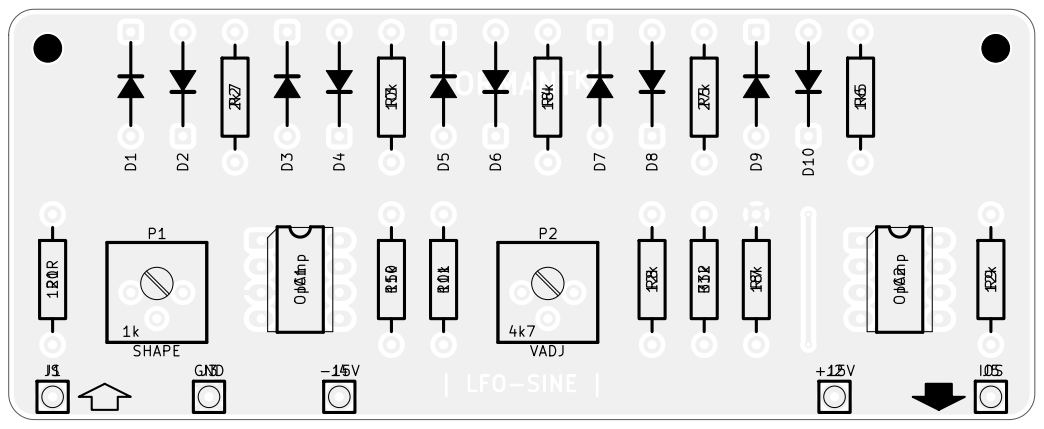
[picture p265: page 1]

FORMANT-KO
THE HOUSE OF GALAHAD
Sheet: Black And White TOP
File: LFO_SINE.kicad_pcb
Title: LFO-SINE
KiCad E.D.A. 10.0.3

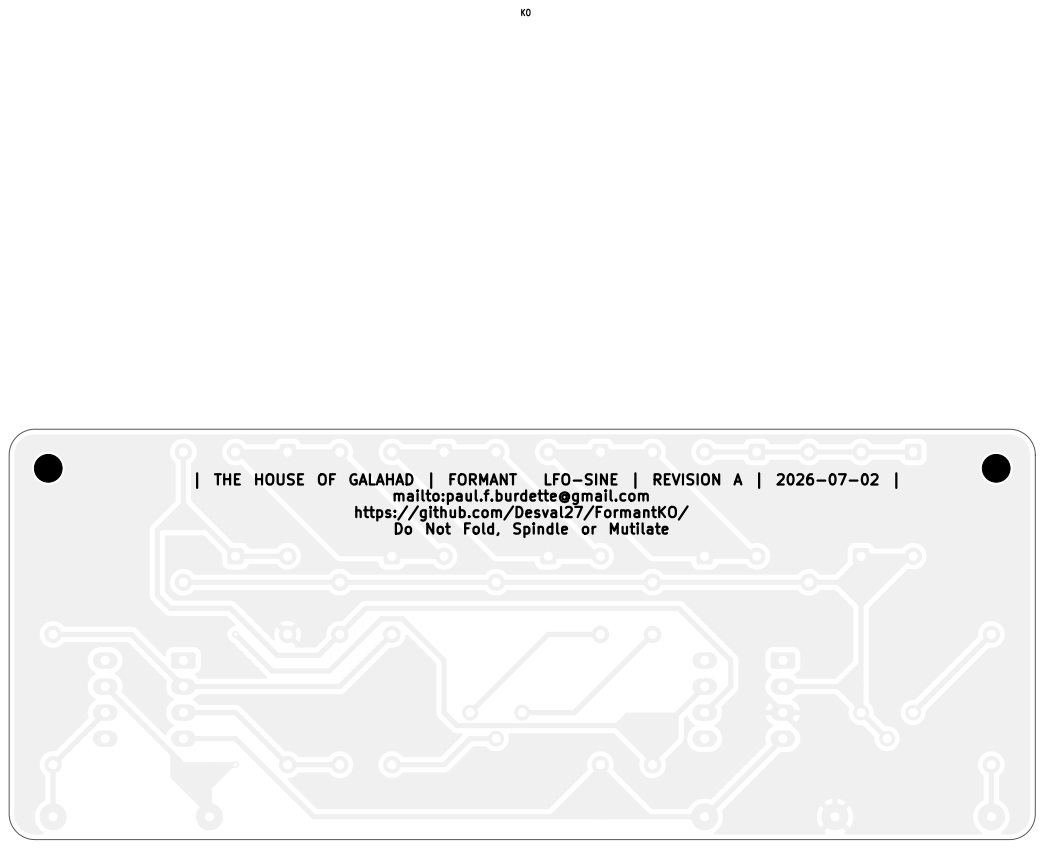
[picture p266: page 2]
| THE HOUSE OF; GALAHAD | FORMANT; KO LFO-SINE |; REVISION A | 2026-07-02 | mailto:paul.f.burdette@gmail.com; Do Not Fold, Spindle or Mutilate 1; D Date: 2026-07-02; Size: USLetter; Rev: A

https://github.com/Desval27/FormantKO/

Board2Pdf: Black And White BOT - Page 2/2

FORMANT-KO
THE HOUSE OF GALAHAD
Sheet: Black And White BOT
File: LFO_SINE.kicad_pcb
Title: LFO-SINE
KiCad E.D.A. 10.0.3
