Desval27/FormantKO/modules/NOISE_DNG/plots/NOISE_DNG__Assembly.pdf

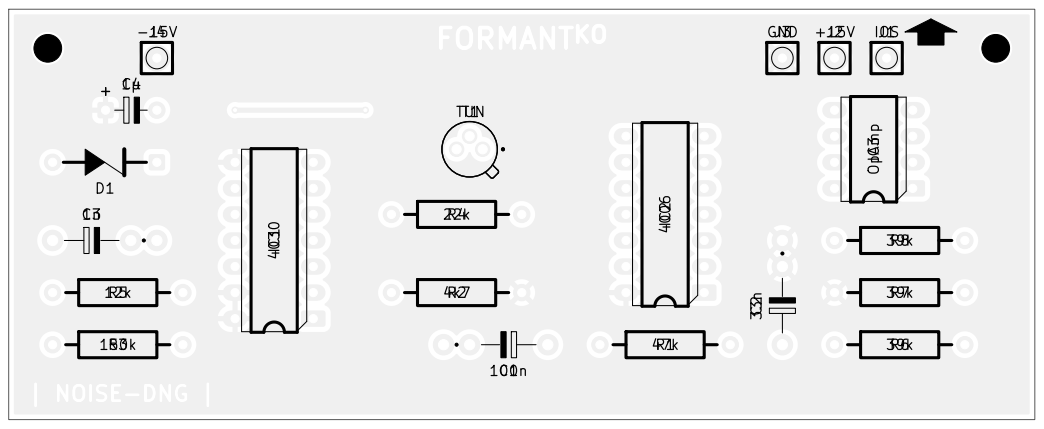
[picture p267: page 1]

Board2Pdf: Black And White TOP - Page 1/2

FORMANT-KO
THE HOUSE OF GALAHAD
Sheet: Black And White TOP
File: NOISE_DNG.kicad_pcb
Title: NOISE-DNG
KiCad E.D.A. 10.0.3

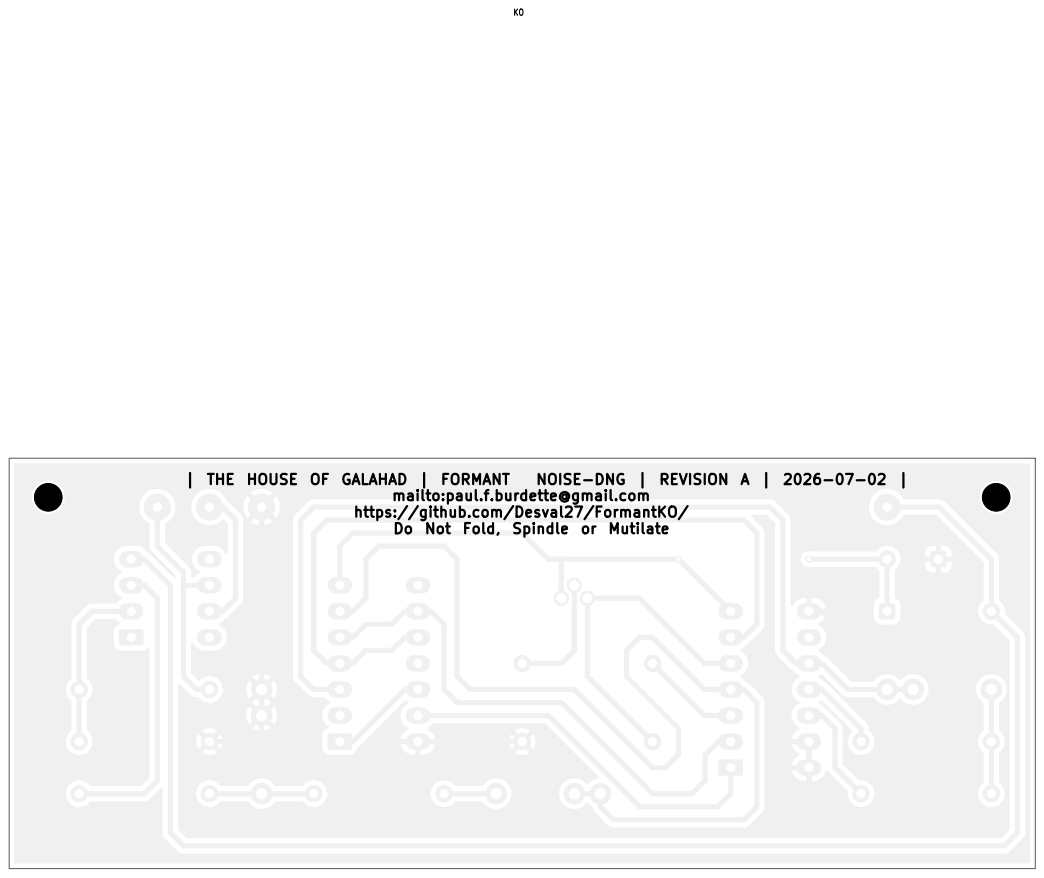
[picture p268: page 2]
Do Not Fold, Spindle or Mutilate 1; D Date: 2026-07-02; Size: USLetter; Rev: A

KO NOISE-DNG | REVISION A | 2026-07-02 | mailto:paul.f.burdette@gmail.com

THE HOUSE OF GALAHAD | FORMANT

https://github.com/Desval27/FormantKO/

Board2Pdf: Black And White BOT - Page 2/2

FORMANT-KO
THE HOUSE OF GALAHAD
Sheet: Black And White BOT
File: NOISE_DNG.kicad_pcb
Title: NOISE-DNG
KiCad E.D.A. 10.0.3
