Desval27/FormantKO/modules/VCF_12/plots/VCF_12__Assembly.pdf

1 | 2 | 3 | 4

AB

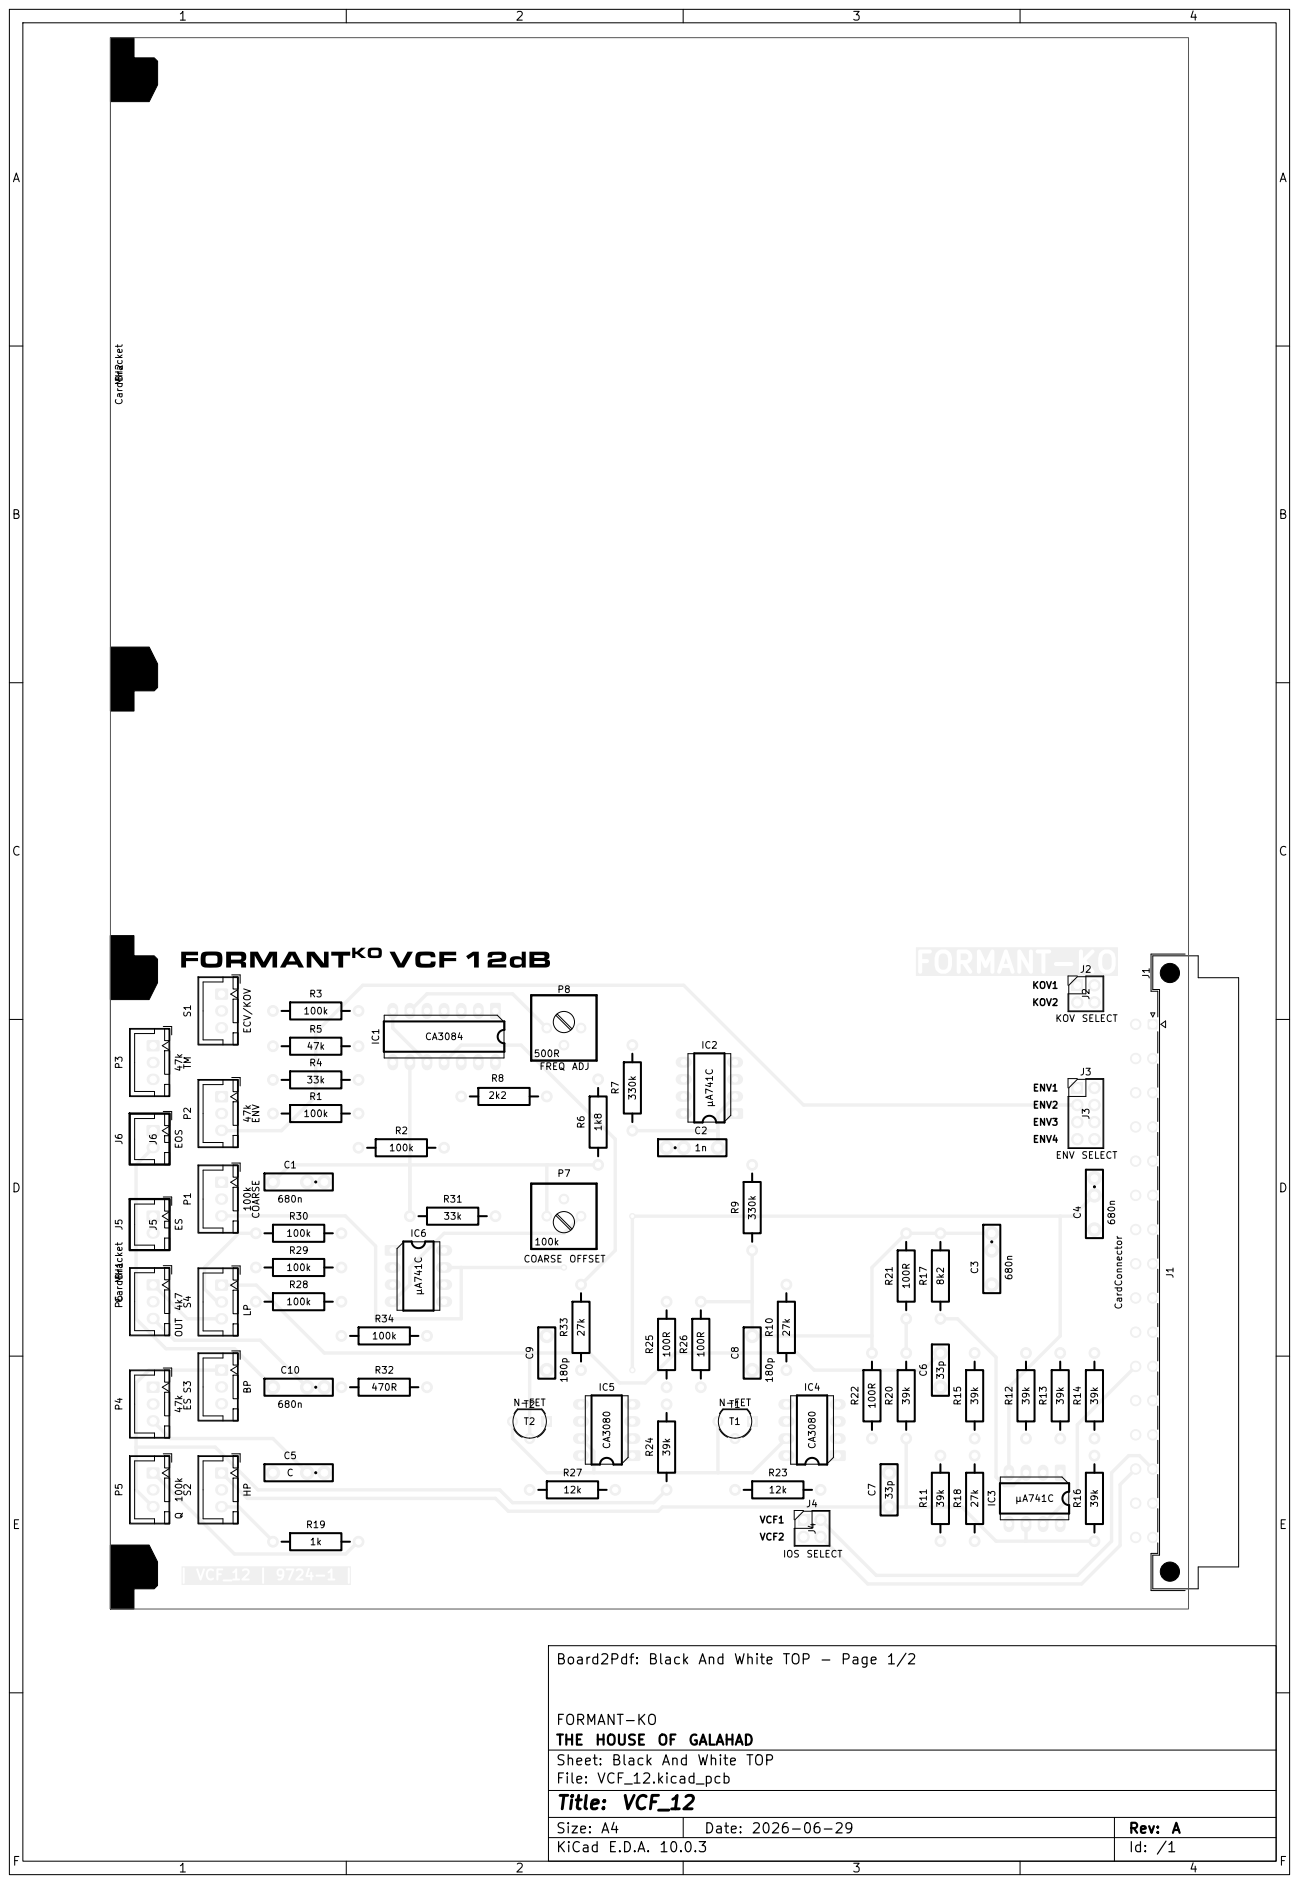
[picture p269: page 1]

FORMANT-KO
THE HOUSE OF GALAHAD
Sheet: Black And White TOP
File: VCF_12.kicad_pcb
Title: VCF_12
KiCad E.D.A. 10.0.3

1 | 2 | 3 | 4

AB

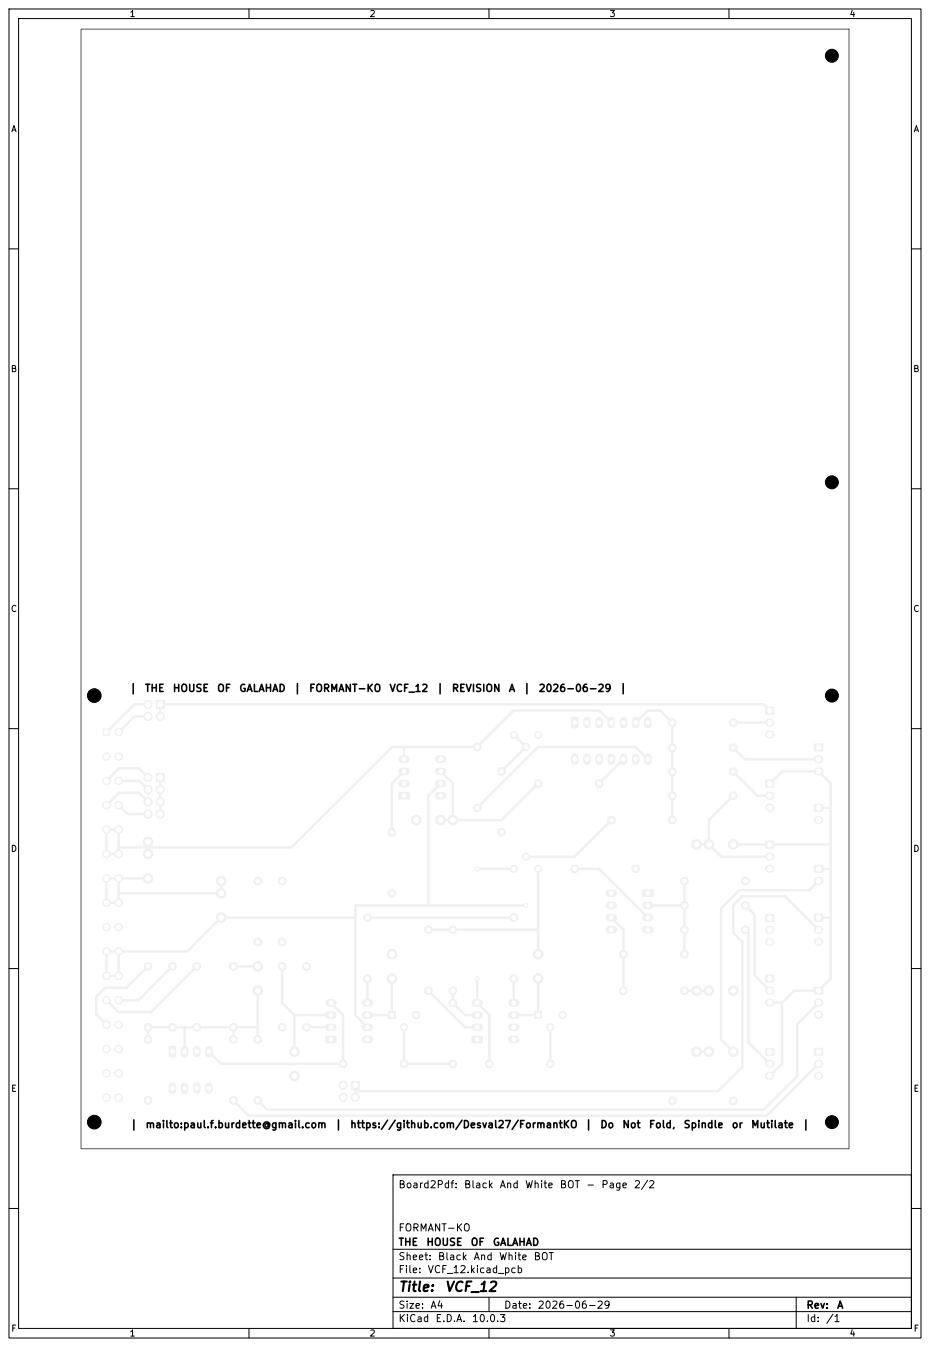
[picture p270: page 2]
F Date: 2026-06-29; Size: A4; Rev: A

THE HOUSE OF GALAHAD | FORMANT-KO VCF_12 | REVISION A | 2026-06-29

mailto:paul.f.burdette@gmail.com | https://github.com/Desval27/FormantKO | Do Not Fold, Spindle or Mutilate

Board2Pdf: Black And White BOT - Page 2/2

FORMANT-KO
THE HOUSE OF GALAHAD
Sheet: Black And White BOT
File: VCF_12.kicad_pcb
Title: VCF_12
KiCad E.D.A. 10.0.3
