Desval27/FormantKO/system/VALIDATOR_JIG/plots/VALIDATOR_JIG__Assembly.pdf

+15V | GND | -15V

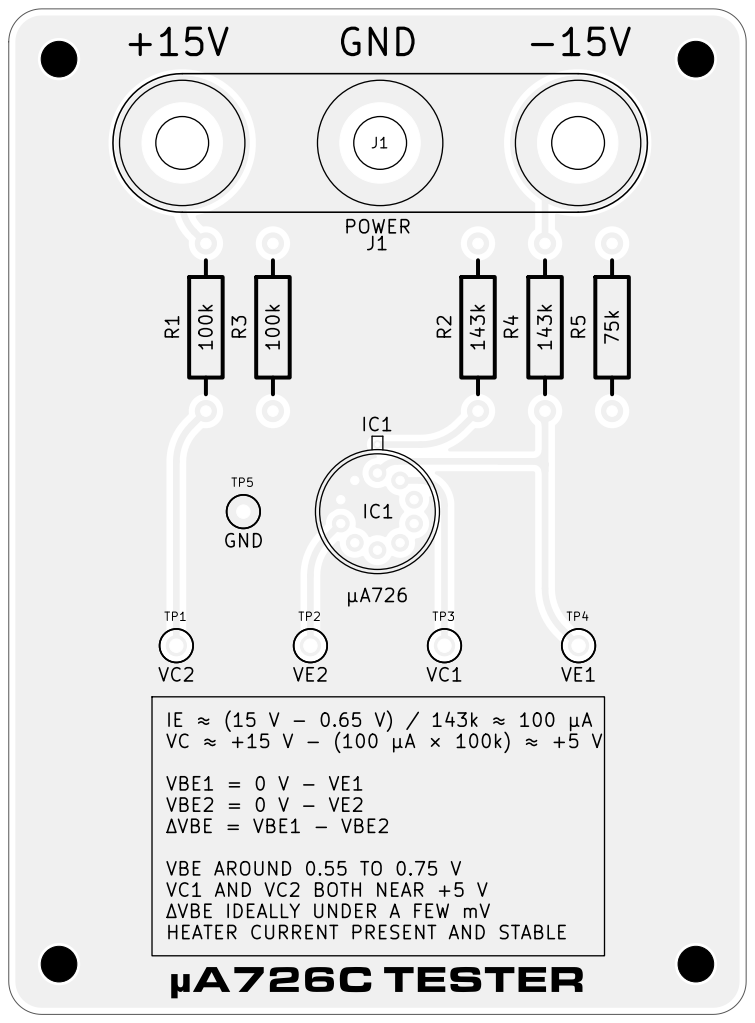
[picture p271: page 1]

VBE AROUND 0.55 TO 0.75 V
VC1 AND VC2 BOTH NEAR +5 V
ΔVBE IDEALLY UNDER A FEW mV HEATER CURRENT PRESENT AND STABLE

Board2Pdf: Black And White TOP - Page 1/2
https://github.com/Desval27/FormantKO/
mailto:paul.f.burdette@gmail.com
FORMANT-KO
THE HOUSE OF GALAHAD
Sheet: Black And White TOP
File: VALIDATOR_JIG.kicad_pcb
Title: µA726C TESTER
KiCad E.D.A. 10.0.3

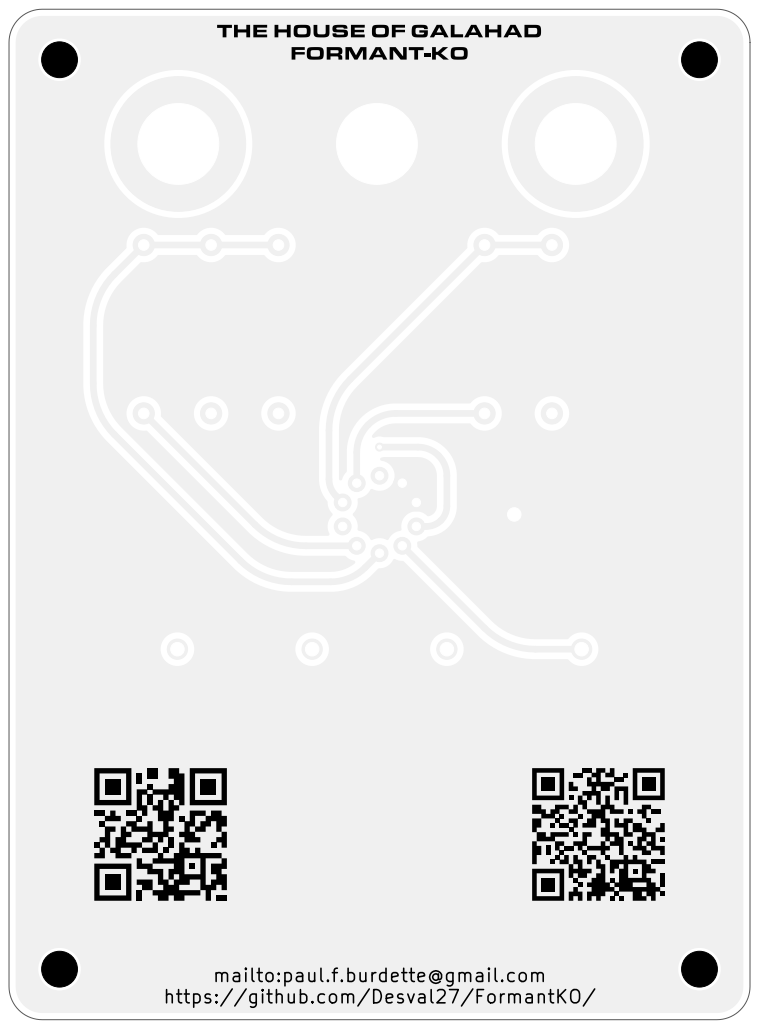
[picture p272: page 2]
D Date: 2026-06-29; Size: USLetter; Rev: A

mailto:paul.f.burdette@gmail.com
https://github.com/Desval27/FormantKO/

Board2Pdf: Black And White BOT - Page 2/2
FORMANT-KO
THE HOUSE OF GALAHAD
Sheet: Black And White BOT
File: VALIDATOR_JIG.kicad_pcb
Title: µA726C TESTER
KiCad E.D.A. 10.0.3
