Desval27/FormantKO/modules/VCO/plots/VCO__Assembly.pdf

T5 | IC1 | 7413
1k | R21 | 33k R19

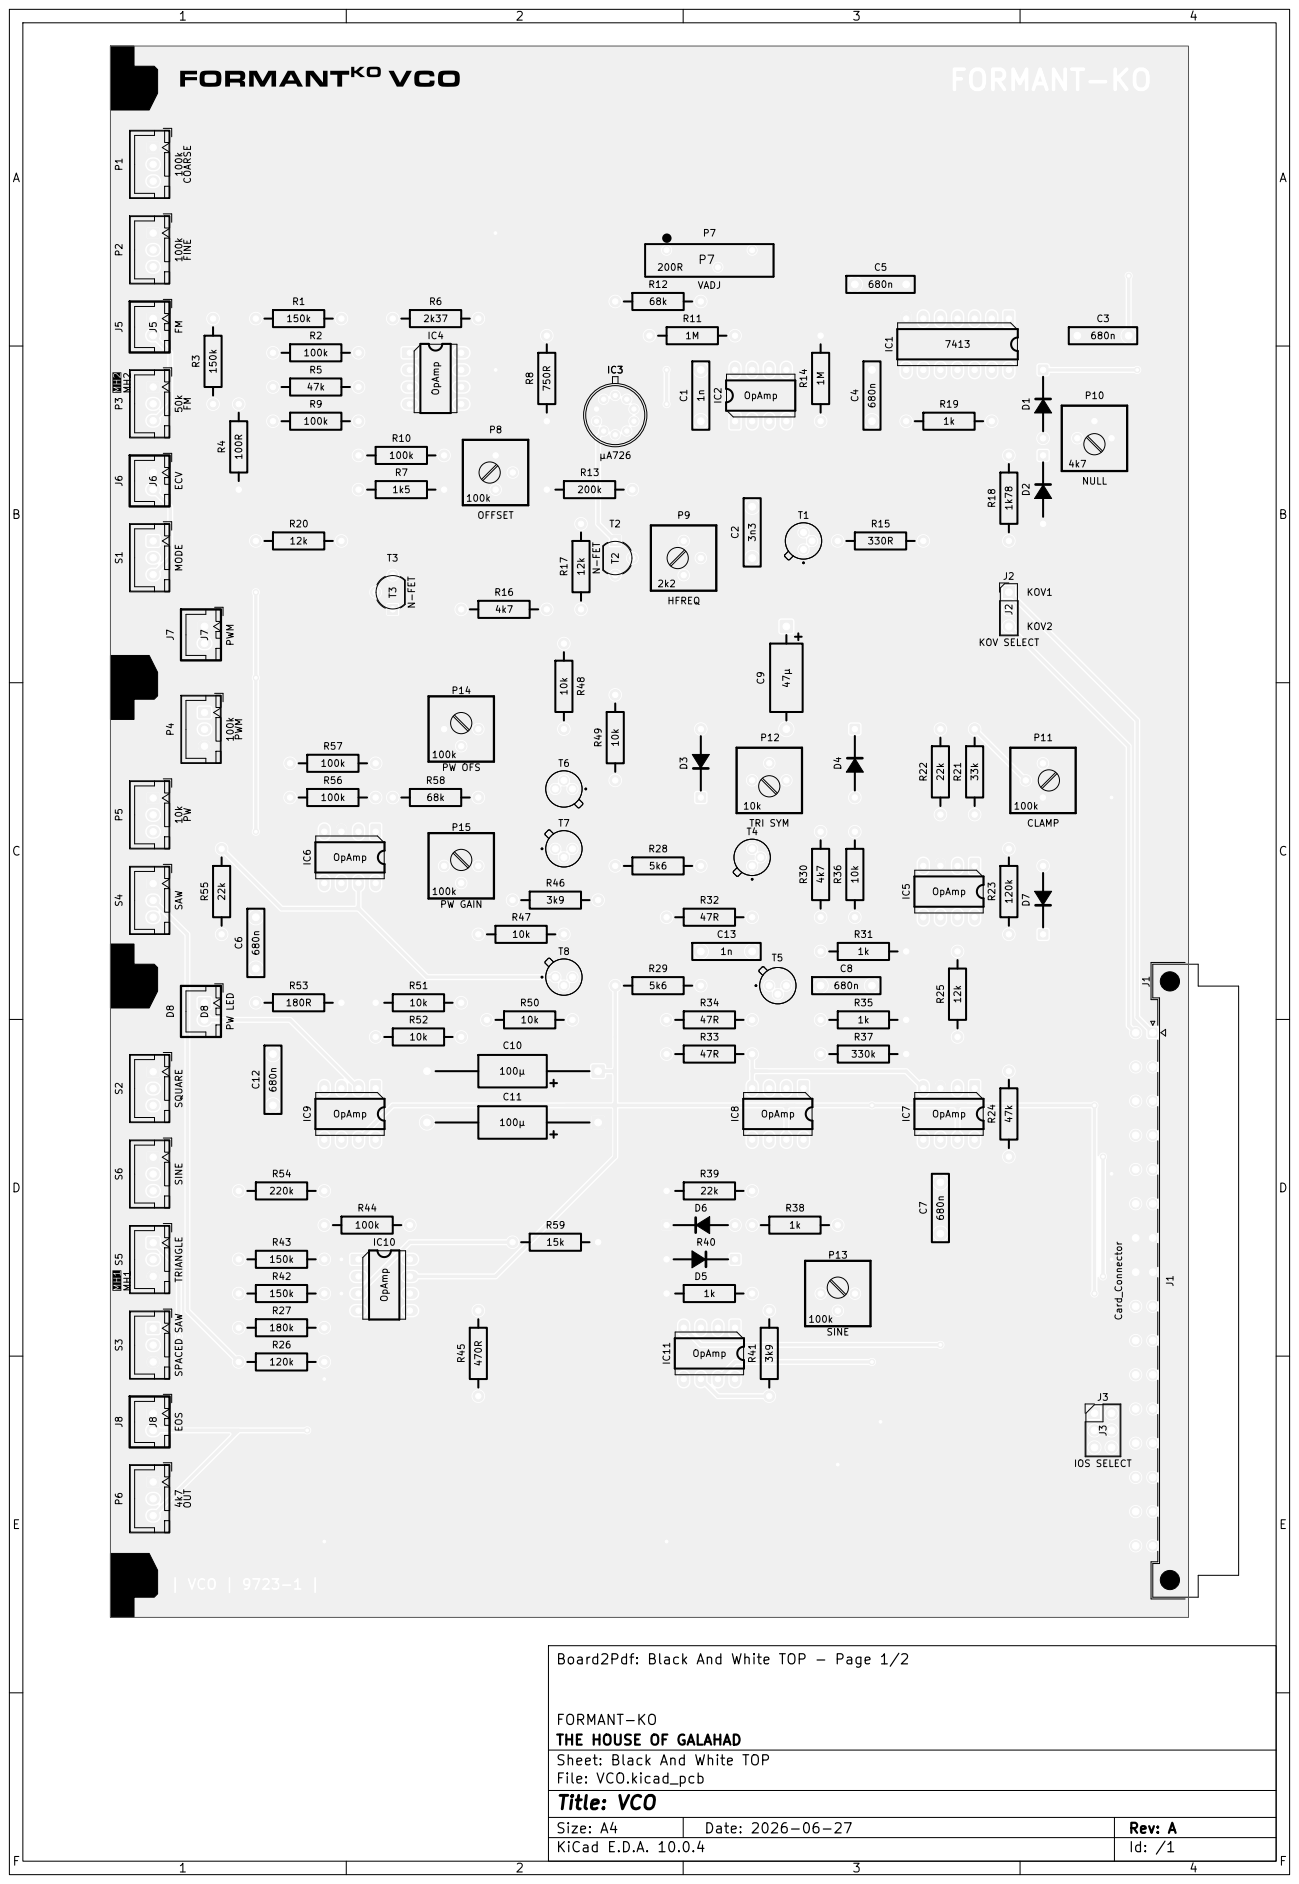
[picture p273: page 1]

Board2Pdf: Black And White TOP - Page 1/2 D8 J8

FORMANT-KO
THE HOUSE OF GALAHAD
Sheet: Black And White TOP
File: VCO.kicad_pcb
Title: VCO
KiCad E.D.A. 10.0.4

## | THE HOUSE OF GALAHAD | FORMANT-KO VCO | REVISION A | 2026-06-27 |

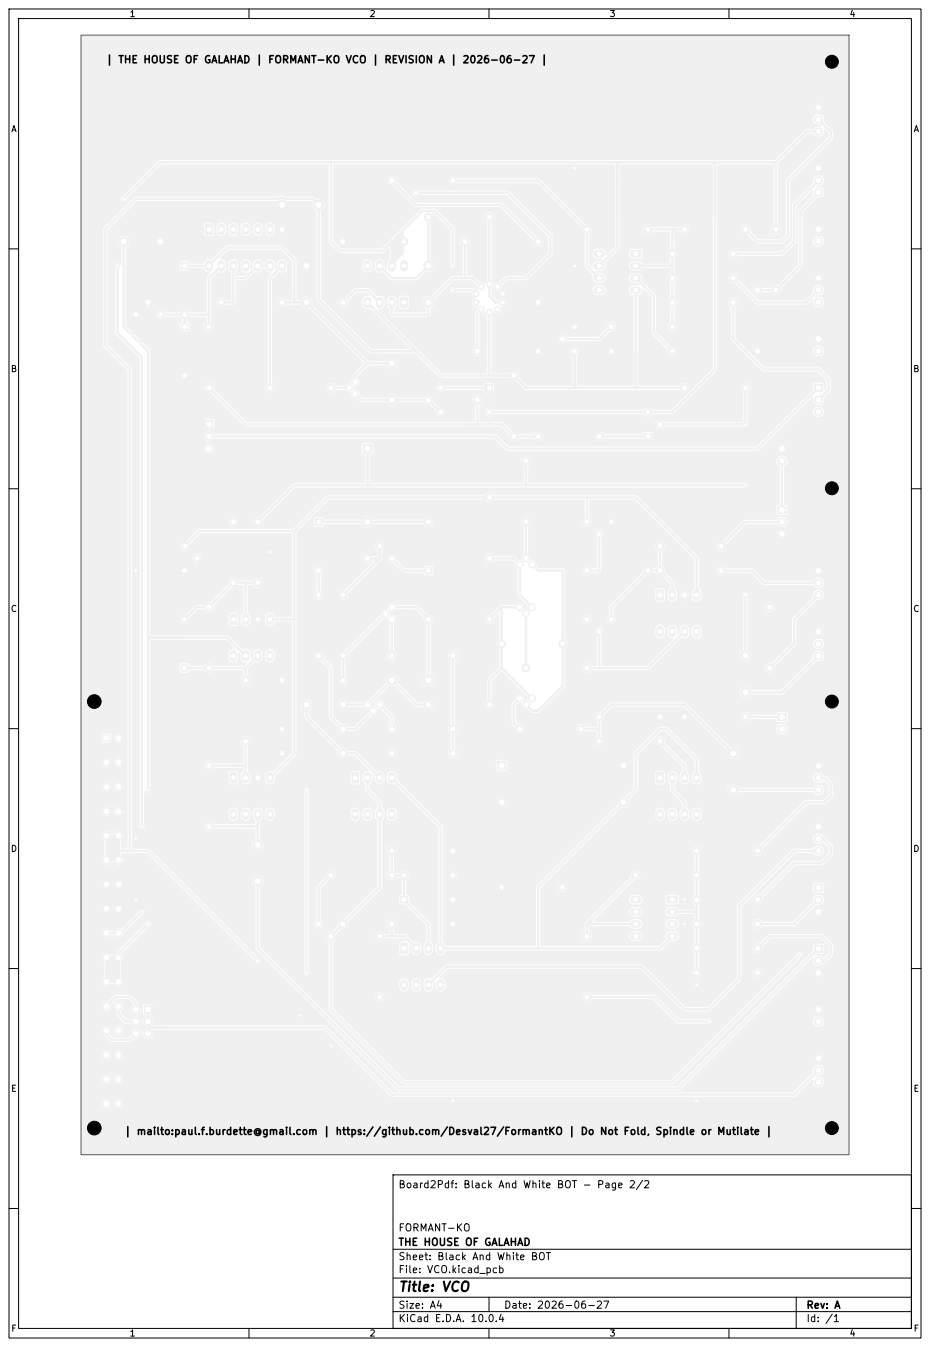
[picture p274: page 2]
F Date: 2026-06-27; Size: A4; Rev: A

mailto:paul.f.burdette@gmail.com | https://github.com/Desval27/FormantKO | Do Not Fold, Spindle or Mutilate

Board2Pdf: Black And White BOT - Page 2/2

FORMANT-KO
THE HOUSE OF GALAHAD
Sheet: Black And White BOT
File: VCO.kicad_pcb
Title: VCO
KiCad E.D.A. 10.0.4
