Desval27/FormantKO/modules/PHASE_SHIFTER/plots/PHASE_SHIFTER__Assembly.pdf

470n R26

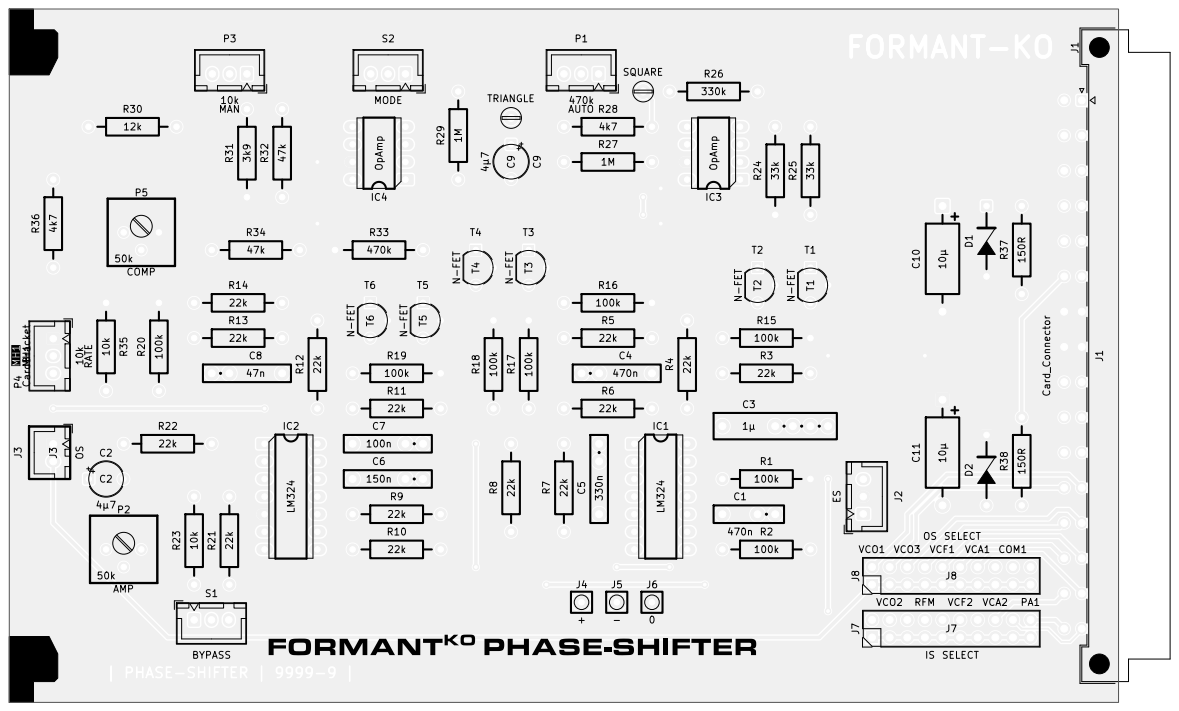
[picture p275: page 1]

FORMANT-KO
THE HOUSE OF GALAHAD
Sheet: Black And White TOP
File: PHASE_SHIFTER.kicad_pcb
Title: PHASE-SHIFTER
KiCad E.D.A. 10.0.3

## | THE HOUSE OF GALAHAD | FORMANT-KO PHASE-SHIFTER | REVISION A | 2026-06-25 |

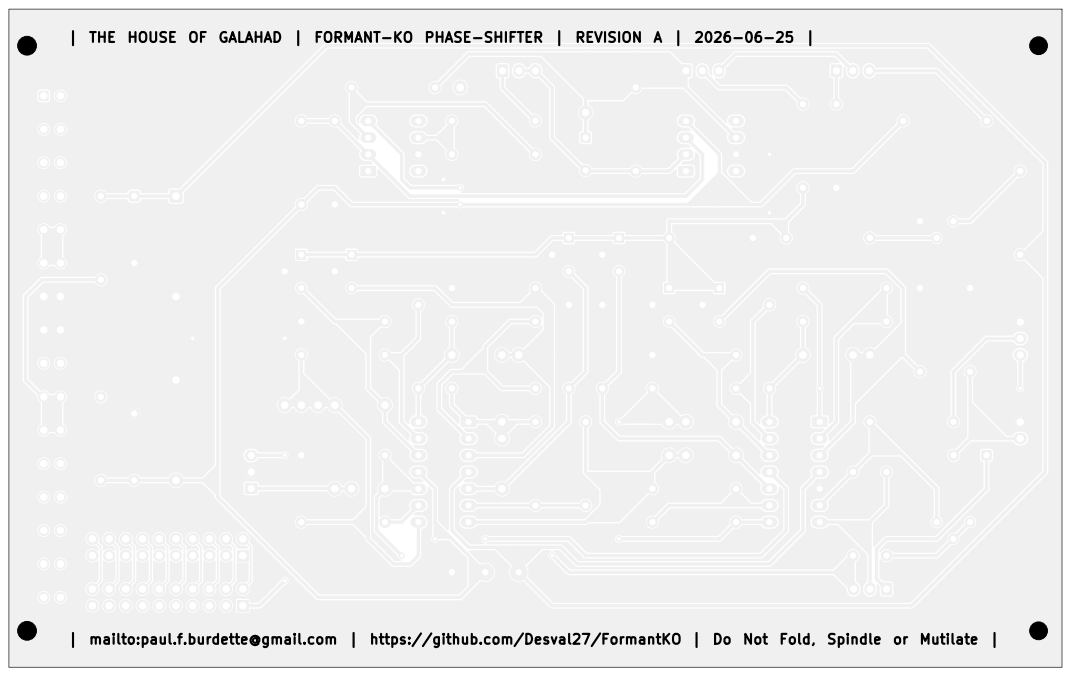
[picture p276: page 2]
D Date: 2026-06-25; Size: USLetter; Rev: A

mailto:paul.f.burdette@gmail.com | https://github.com/Desval27/FormantKO | Do Not Fold, Spindle or Mutilate

Board2Pdf: Black And White BOT - Page 2/2

FORMANT-KO
THE HOUSE OF GALAHAD
Sheet: Black And White BOT
File: PHASE_SHIFTER.kicad_pcb
Title: PHASE-SHIFTER
KiCad E.D.A. 10.0.3
