Desval27/FormantKO/panels/TUNING/plots/TUNING__Assembly.pdf

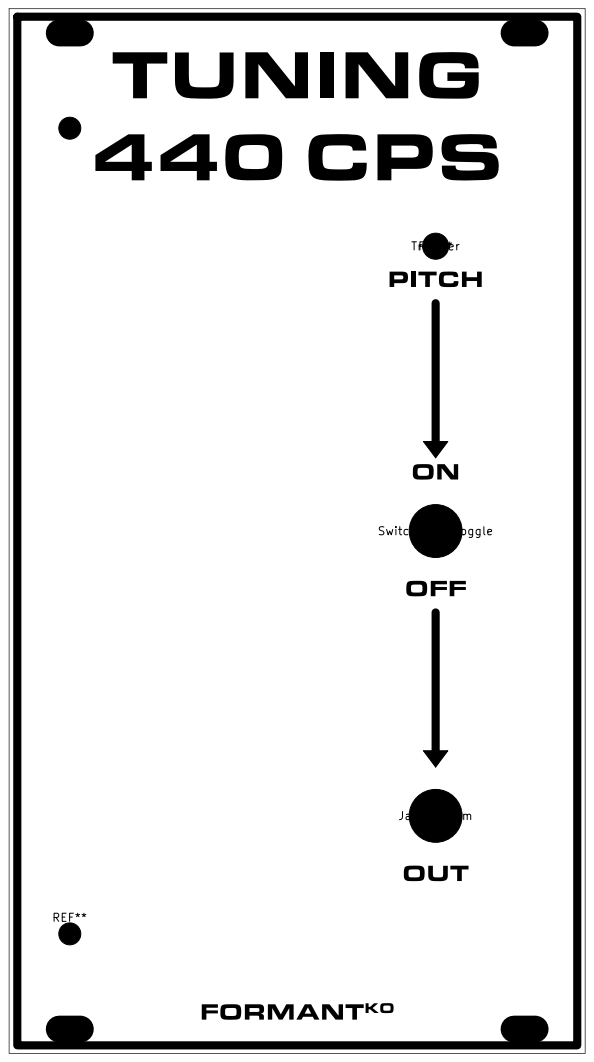
[picture p277: page 1]
D Date: 2026-06-23; Size: USLetter; Rev: A; Jack_3.5mm REF** Switch_Mini_Toggle REF**; Trimmer REF** H3; H4 REF**

Board2Pdf: Black And White TOP - Page 1/2

FORMANT-KO
THE HOUSE OF GALAHAD
Sheet: Black And White TOP
File: TUNING.kicad_pcb
Title: TUNING
KiCad E.D.A. 10.0.3

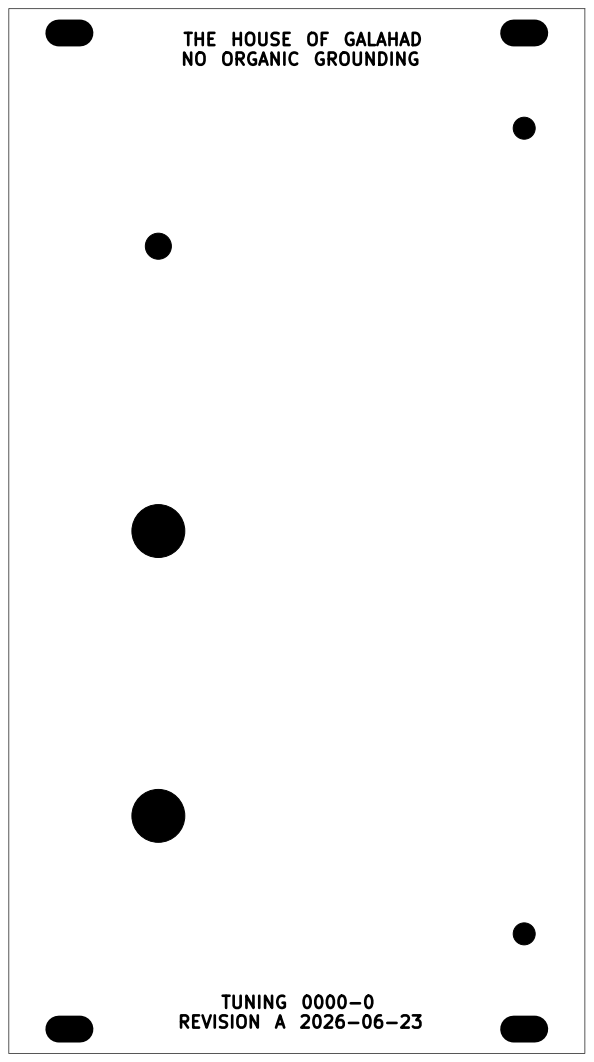
[picture p278: page 2]
TUNING 0000-0 REVISION A 2026-06-23; D Date: 2026-06-23; Size: USLetter; Rev: A

THE HOUSE OF GALAHAD
NO ORGANIC GROUNDING

Board2Pdf: Black And White BOT - Page 2/2

FORMANT-KO
Sheet: Black And White BOT
File: TUNING.kicad_pcb
Title: TUNING
KiCad E.D.A. 10.0.3
