Desval27/FormantKO/panels/MULTIPLE_JACKS_3U/plots/MULTIPLE_JACKS_3U__Assembly.pdf

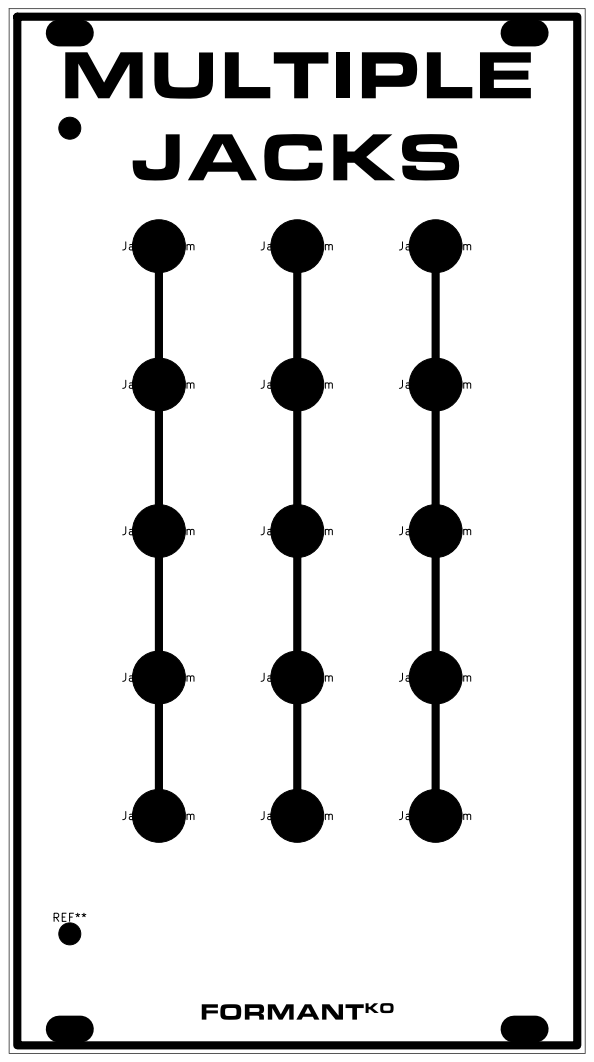
[picture p279: page 1]
D Date: 2026-06-05; Size: USLetter; Rev: A; Jack_3.5mm REF**; Jack_3.5mm REF** H3; H4 REF**

Board2Pdf: Black And White TOP - Page 1/2

FORMANT-KO
THE HOUSE OF GALAHAD
Sheet: Black And White TOP
File: MULTIPLE_JACKS_3U.kicad_pcb
Title: MULTIPLE-JACKS 3U
KiCad E.D.A. 10.0.3

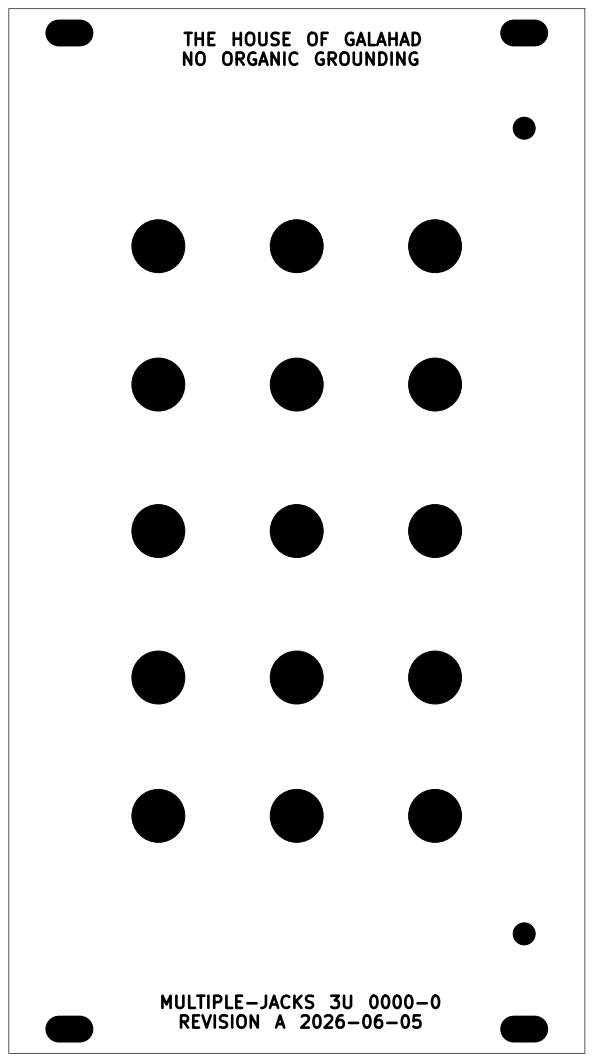
[picture p280: page 2]
MULTIPLE-JACKS 3U 0000-0 REVISION A 2026-06-05; D Date: 2026-06-05; Size: USLetter; Rev: A

THE HOUSE OF GALAHAD
NO ORGANIC GROUNDING

Board2Pdf: Black And White BOT - Page 2/2

FORMANT-KO
Sheet: Black And White BOT
File: MULTIPLE_JACKS_3U.kicad_pcb
Title: MULTIPLE-JACKS 3U
KiCad E.D.A. 10.0.3
