Desval27/FormantKO/panels/MULTIPLE_JACKS_6U/plots/MULTIPLE_JACKS_6U__Assembly.pdf

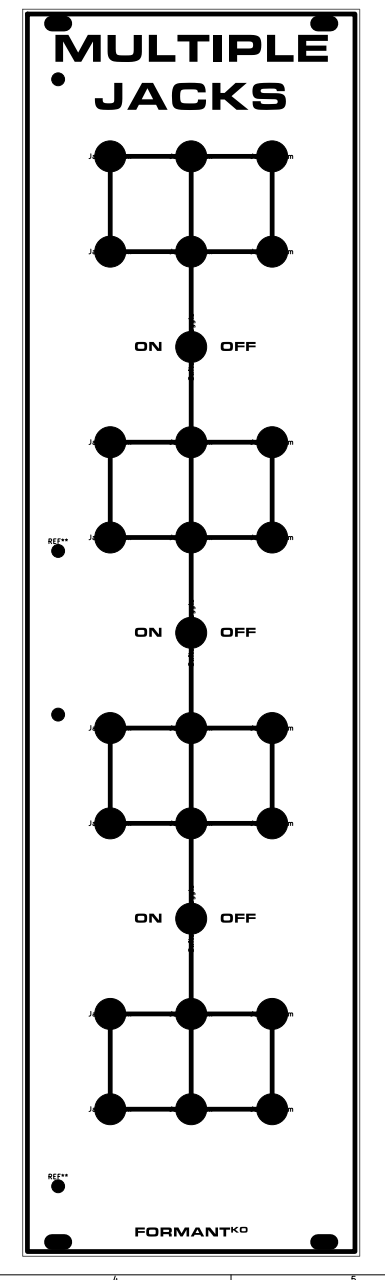
[picture p281: page 1]
8 ABCDEF; ABCDEF Date: 2026-06-05; Size: A3; Rev: A; Jack_3.5mm REF**; H3 REF**; REF**

Board2Pdf: Black And White TOP - Page 1/2 Switch_Mini_Toggle REF** Switch_Mini_Toggle REF** Switch_Mini_Toggle REF**

FORMANT-KO
THE HOUSE OF GALAHAD
Sheet: Black And White TOP
File: MULTIPLE_JACKS_6U.kicad_pcb
Title: MULTIPLE-JACKS 6U
KiCad E.D.A. 10.0.3

## THE HOUSE OF GALAHAD NO ORGANIC GROUNDING

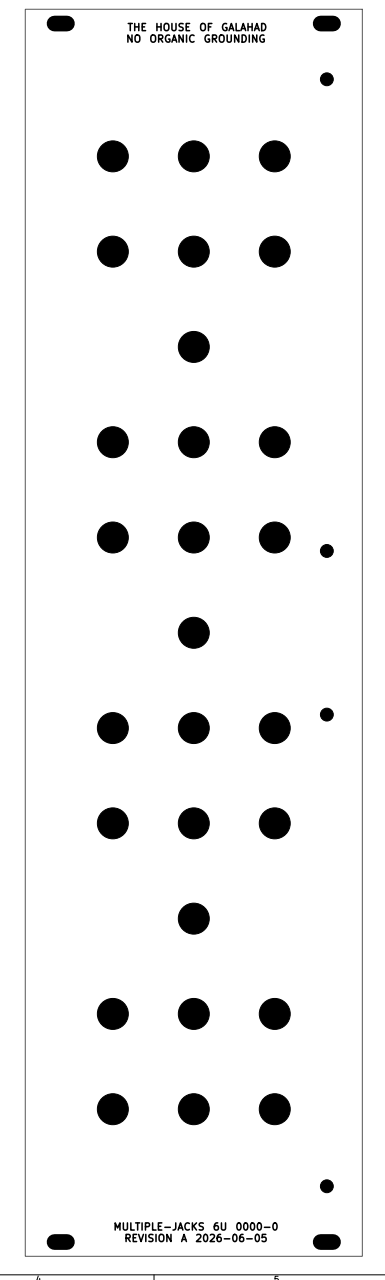
[picture p282: page 2]
MULTIPLE-JACKS 6U 0000-0 REVISION A 2026-06-05; F Date: 2026-06-05; Size: A3; Rev: A

Board2Pdf: Black And White BOT - Page 2/2

FORMANT-KO
THE HOUSE OF GALAHAD
Sheet: Black And White BOT
File: MULTIPLE_JACKS_6U.kicad_pcb
Title: MULTIPLE-JACKS 6U
KiCad E.D.A. 10.0.3
