Desval27/FormantKO/panels/PHASE_SHIFTER/plots/PHASE_SHIFTER__Assembly.pdf

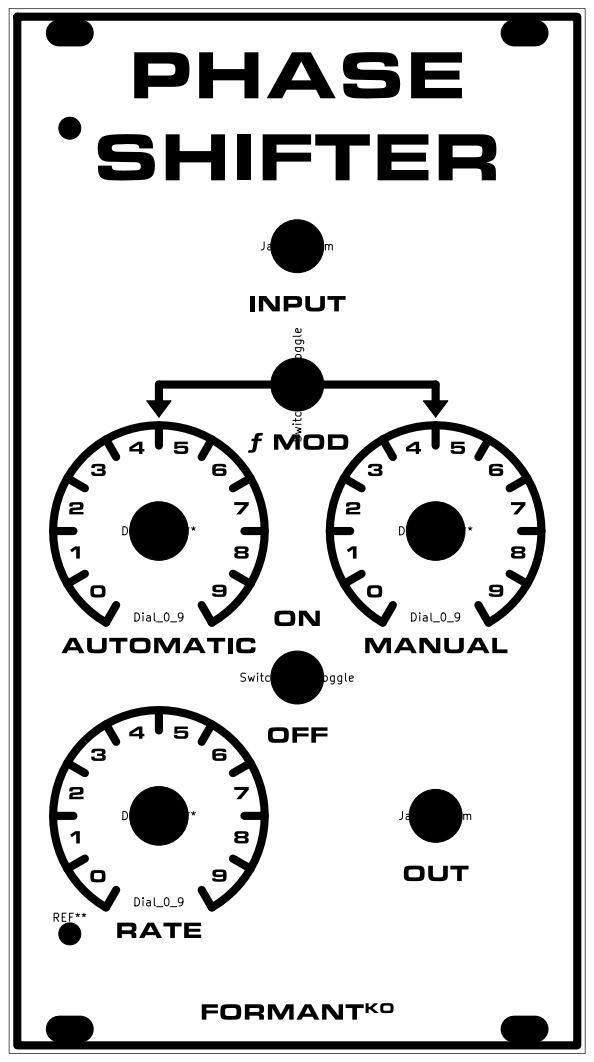
[picture p283: page 1]
D Date: 2026-06-05; Size: USLetter; Rev: A; Switch_Mini_Toggle REF**Switch_Mini_Toggle REF**; Jack_3.5mm REF** Dial_Scale**; Jack_3.5mm REF** Dial_0_9; Dial_Scale** Dial_0_9 Dial_Scale** Dial_0_9 H3; H4 REF**

Board2Pdf: Black And White TOP - Page 1/2

FORMANT-KO
THE HOUSE OF GALAHAD
Sheet: Black And White TOP
File: PHASE_SHIFTER.kicad_pcb
Title: PHASE-SHIFTER
KiCad E.D.A. 10.0.3

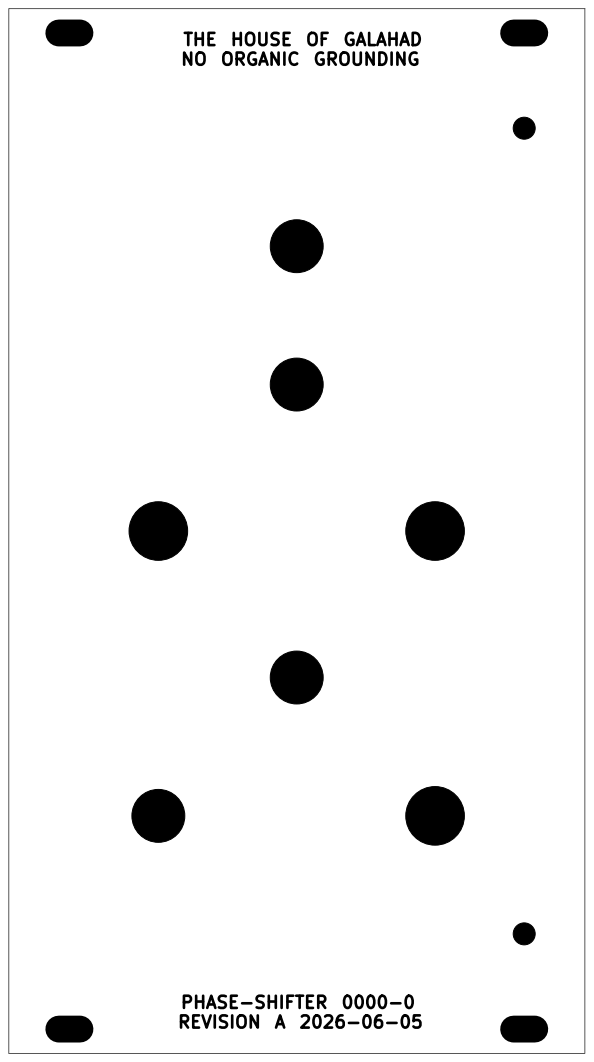
[picture p284: page 2]
PHASE-SHIFTER 0000-0 REVISION A 2026-06-05; D Date: 2026-06-05; Size: USLetter; Rev: A

THE HOUSE OF GALAHAD
NO ORGANIC GROUNDING

Board2Pdf: Black And White BOT - Page 2/2

FORMANT-KO
Sheet: Black And White BOT
File: PHASE_SHIFTER.kicad_pcb
Title: PHASE-SHIFTER
KiCad E.D.A. 10.0.3
