Desval27/FormantKO/modules/RING_MODULATOR/plots/RING_MODULATOR__Assembly.pdf

27k | C7
120n R7 | 1k5 | R31

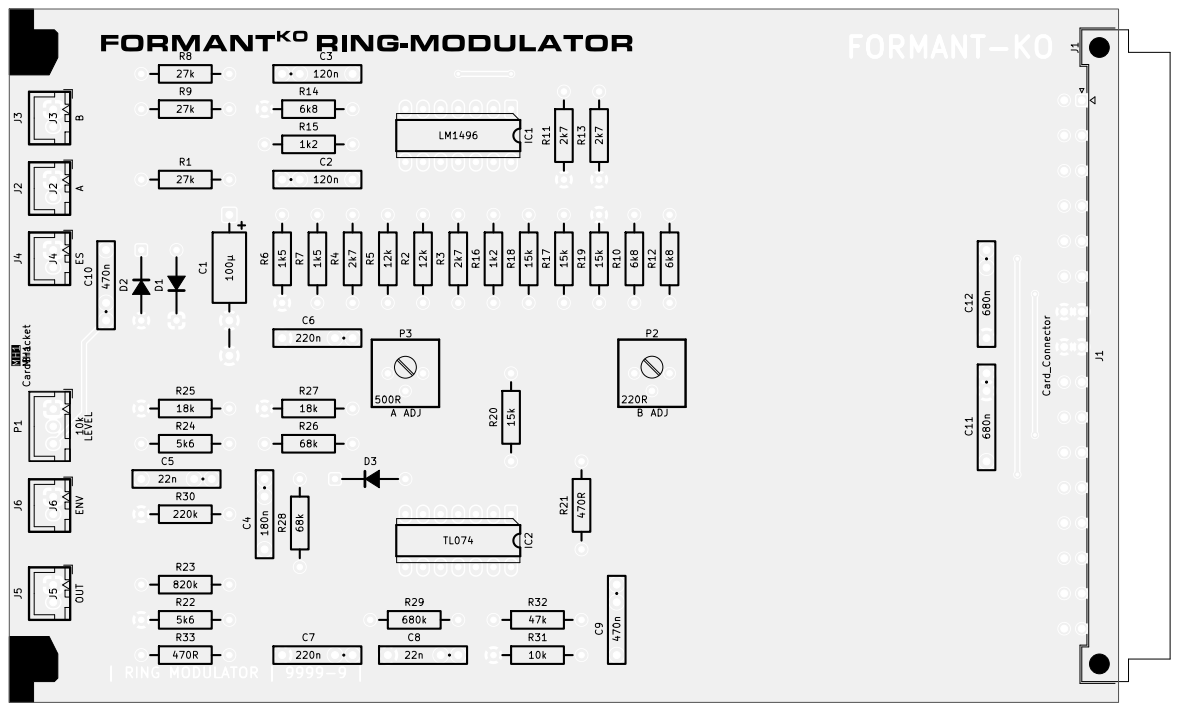
[picture p285: page 1]

FORMANT-KO
THE HOUSE OF GALAHAD
Sheet: Black And White TOP
File: RING_MODULATOR.kicad_pcb
Title: RING MODULATOR
KiCad E.D.A. 10.0.3

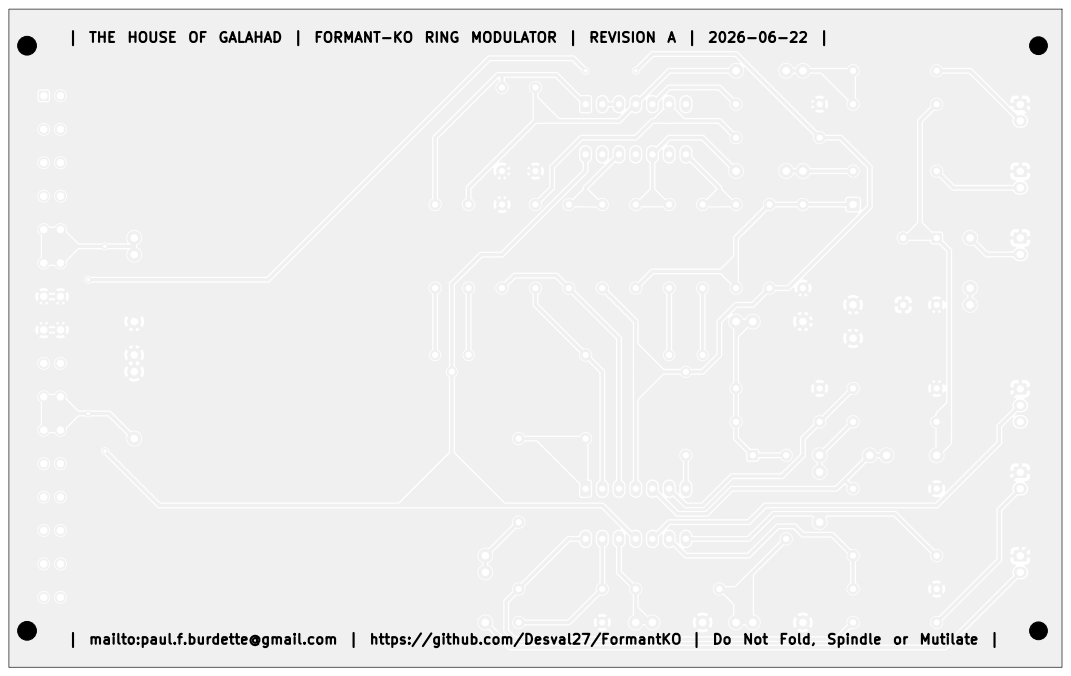
[picture p286: page 2]
D Date: 2026-06-22; Size: USLetter; Rev: A

THE HOUSE OF GALAHAD | FORMANT-KO RING MODULATOR | REVISION A | 2026-06-22

mailto:paul.f.burdette@gmail.com | https://github.com/Desval27/FormantKO | Do Not Fold, Spindle or Mutilate

Board2Pdf: Black And White BOT - Page 2/2

FORMANT-KO
THE HOUSE OF GALAHAD
Sheet: Black And White BOT
File: RING_MODULATOR.kicad_pcb
Title: RING MODULATOR
KiCad E.D.A. 10.0.3
