Desval27/FormantKO/panels/RING_MODULATOR/plots/RING_MODULATOR__Assembly.pdf

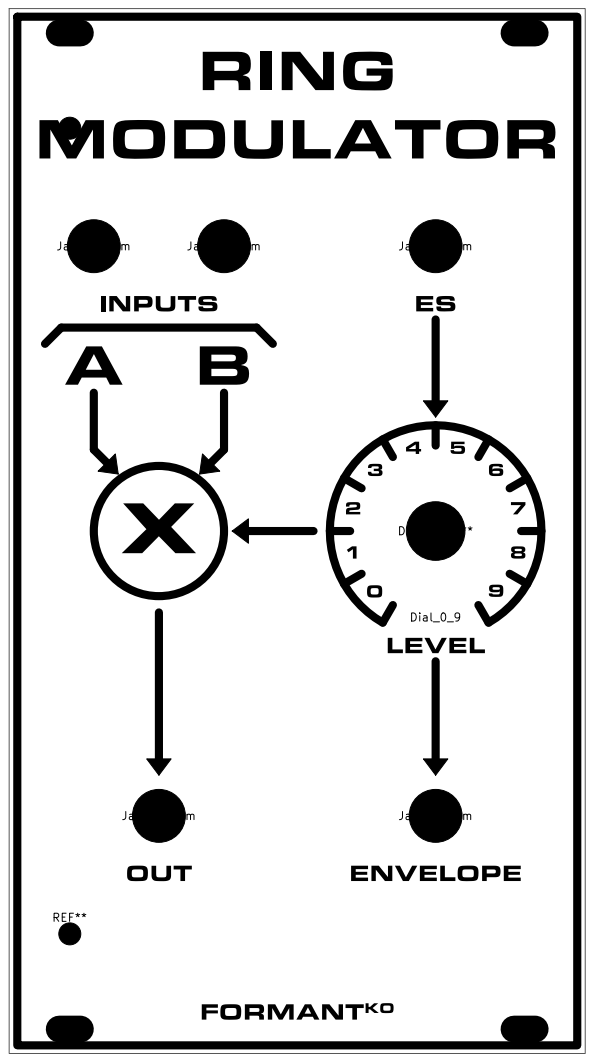
[picture p287: page 1]
D Date: 2026-06-22; Size: USLetter; Rev: A; Jack_3.5mm REF**; Jack_3.5mm REF** Dial_Scale** Dial_0_9; Jack_3.5mm REF** H3; H4 REF**

Board2Pdf: Black And White TOP - Page 1/2

FORMANT-KO
THE HOUSE OF GALAHAD
Sheet: Black And White TOP
File: RING_MODULATOR.kicad_pcb
Title: RING-MODULATOR
KiCad E.D.A. 10.0.3

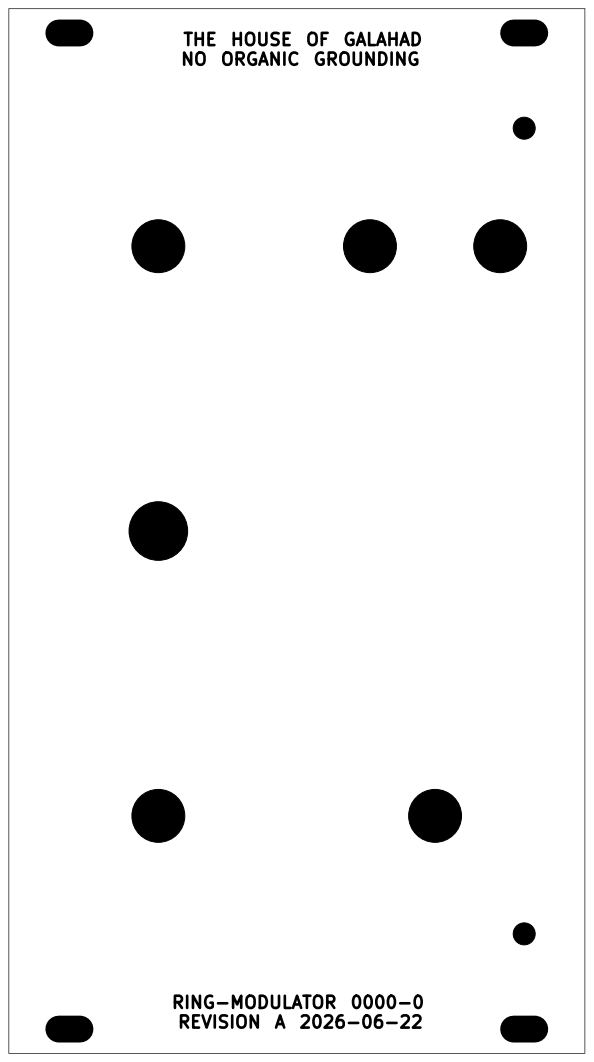
[picture p288: page 2]
RING-MODULATOR 0000-0 REVISION A 2026-06-22; D Date: 2026-06-22; Size: USLetter; Rev: A

THE HOUSE OF GALAHAD
NO ORGANIC GROUNDING

Board2Pdf: Black And White BOT - Page 2/2

FORMANT-KO
Sheet: Black And White BOT
File: RING_MODULATOR.kicad_pcb
Title: RING-MODULATOR
KiCad E.D.A. 10.0.3
