Desval27/FormantKO/modules/NOISE_CNC/plots/NOISE_CNC__Assembly.pdf

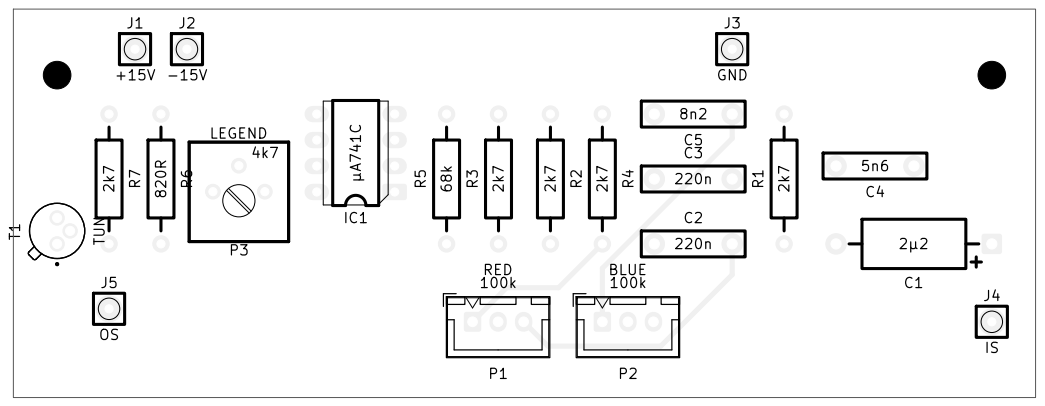
[picture p289: page 1]

Board2Pdf: Black And White TOP - Page 1/2

FORMANT-KO
THE HOUSE OF GALAHAD
Sheet: Black And White TOP
File: NOISE_CNC.kicad_pcb
Title: NOISE EXTENSION - COLOURED NOISE CONTROL
KiCad E.D.A. 10.0.3

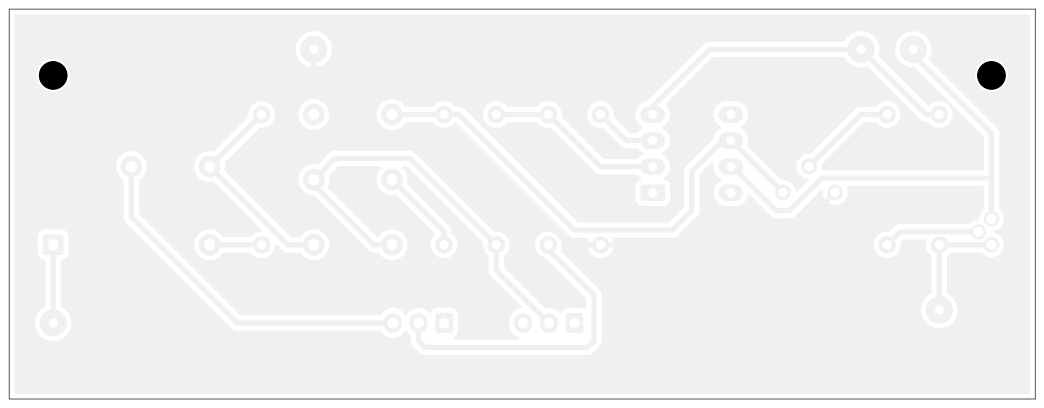
[picture p290: page 2]
D Date:; Size: USLetter; Rev: A

Board2Pdf: Black And White BOT - Page 2/2

FORMANT-KO
THE HOUSE OF GALAHAD
Sheet: Black And White BOT
File: NOISE_CNC.kicad_pcb
Title: NOISE EXTENSION - COLOURED NOISE CONTROL
KiCad E.D.A. 10.0.3
