Desval27/FormantKO/system/KB_DIV/plots/KB_DIV__Assembly.pdf

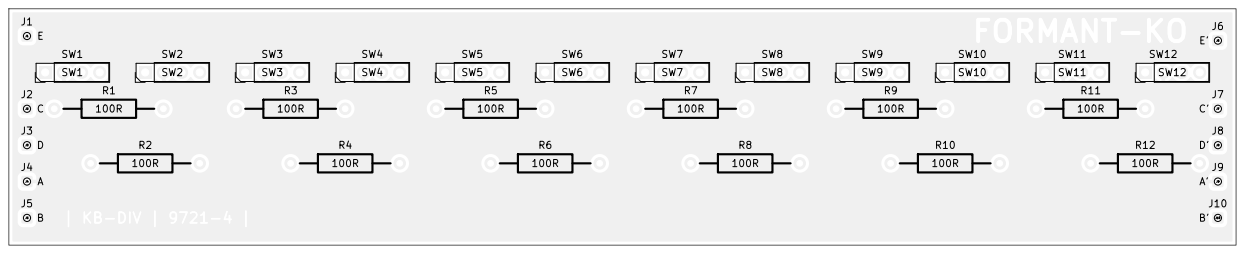
[picture p291: page 1]

Board2Pdf: Black And White TOP - Page 1/2

FORMANT-KO
THE HOUSE OF GALAHAD
Sheet: Black And White TOP
File: KB_DIV.kicad_pcb
Title: KB-DIV
KiCad E.D.A. 10.0.3

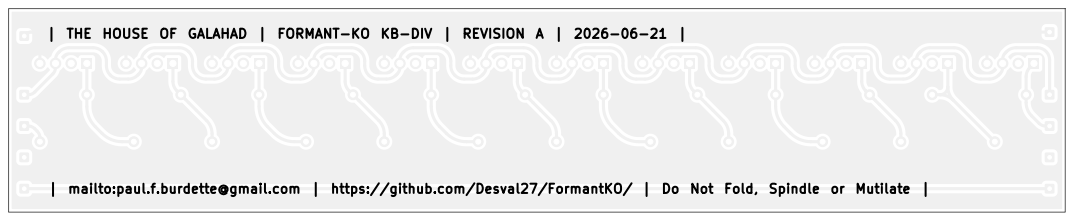
[picture p292: page 2]
D Date: 2026-06-21; Size: USLetter; Rev: A

THE HOUSE OF GALAHAD | FORMANT-KO KB-DIV | REVISION A | 2026-06-21

mailto:paul.f.burdette@gmail.com | https://github.com/Desval27/FormantKO/ | Do Not Fold, Spindle or Mutilate

Board2Pdf: Black And White BOT - Page 2/2

FORMANT-KO
THE HOUSE OF GALAHAD
Sheet: Black And White BOT
File: KB_DIV.kicad_pcb
Title: KB-DIV
KiCad E.D.A. 10.0.3
