Desval27/FormantKO/system/TEST_HARNESS/plots/TEST_HARNESS__Assembly.pdf

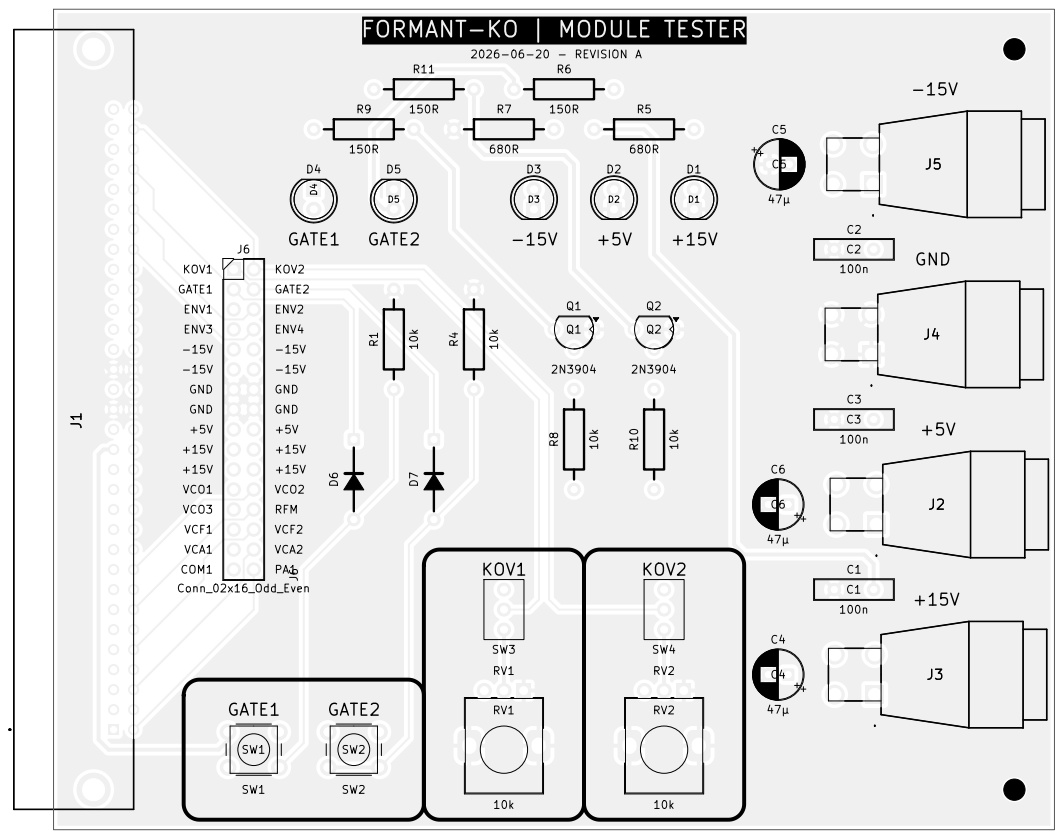
[picture p293: page 1]

Board2Pdf: Black And White TOP - Page 1/2

FORMANT-KO
THE HOUSE OF GALAHAD
Sheet: Black And White TOP
File: TEST_HARNESS.kicad_pcb
Title: MODULE TESTER
KiCad E.D.A. 10.0.3

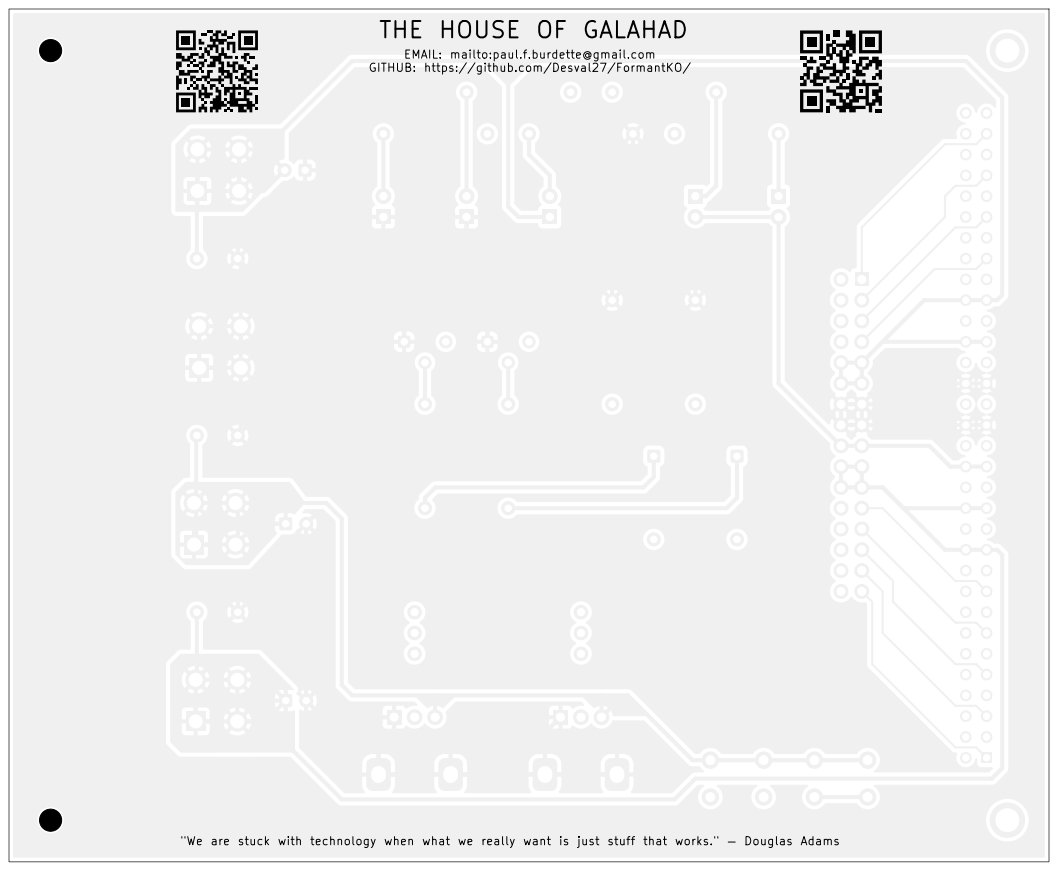
[picture p294: page 2]
D Date: 2026-06-20; Size: USLetter; Rev: A

"We are stuck with technology when what we really want is just stuff that works." — Douglas Adams THE HOUSE OF GALAHAD

EMAIL: mailto:paul.f.burdette@gmail.com
GITHUB: https://github.com/Desval27/FormantKO/

Board2Pdf: Black And White BOT - Page 2/2

FORMANT-KO
THE HOUSE OF GALAHAD
Sheet: Black And White BOT
File: TEST_HARNESS.kicad_pcb
Title: MODULE TESTER
KiCad E.D.A. 10.0.3
