Desval27/FormantKO/system/TEST_HARNESS/plots/TEST_HARNESS__Schematic.pdf

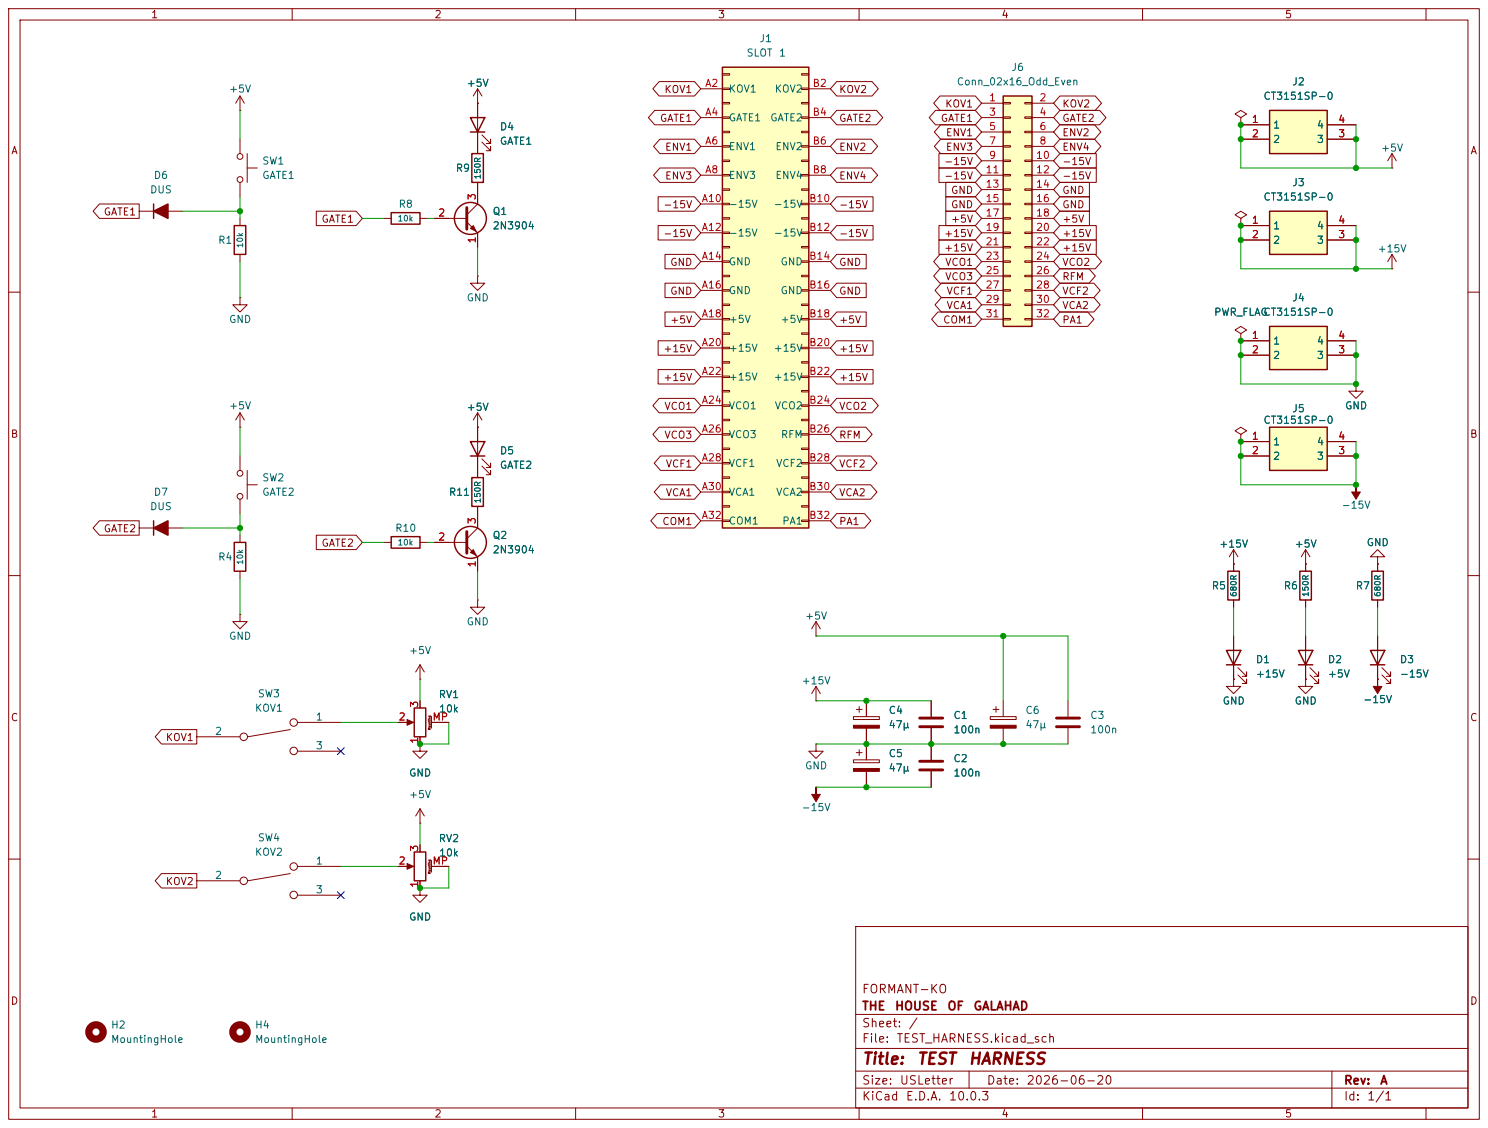
[picture p295: page 1]

FORMANT-KO
THE HOUSE OF GALAHAD
Sheet: /
File: TEST_HARNESS.kicad_sch
Title: TEST HARNESS

Size: USLetter | Rev: A
KiCad E.D.A. 10.0.3 | Id: 1/1
