Desval27/FormantKO/panels/KBI/plots/KBI__Assembly.pdf

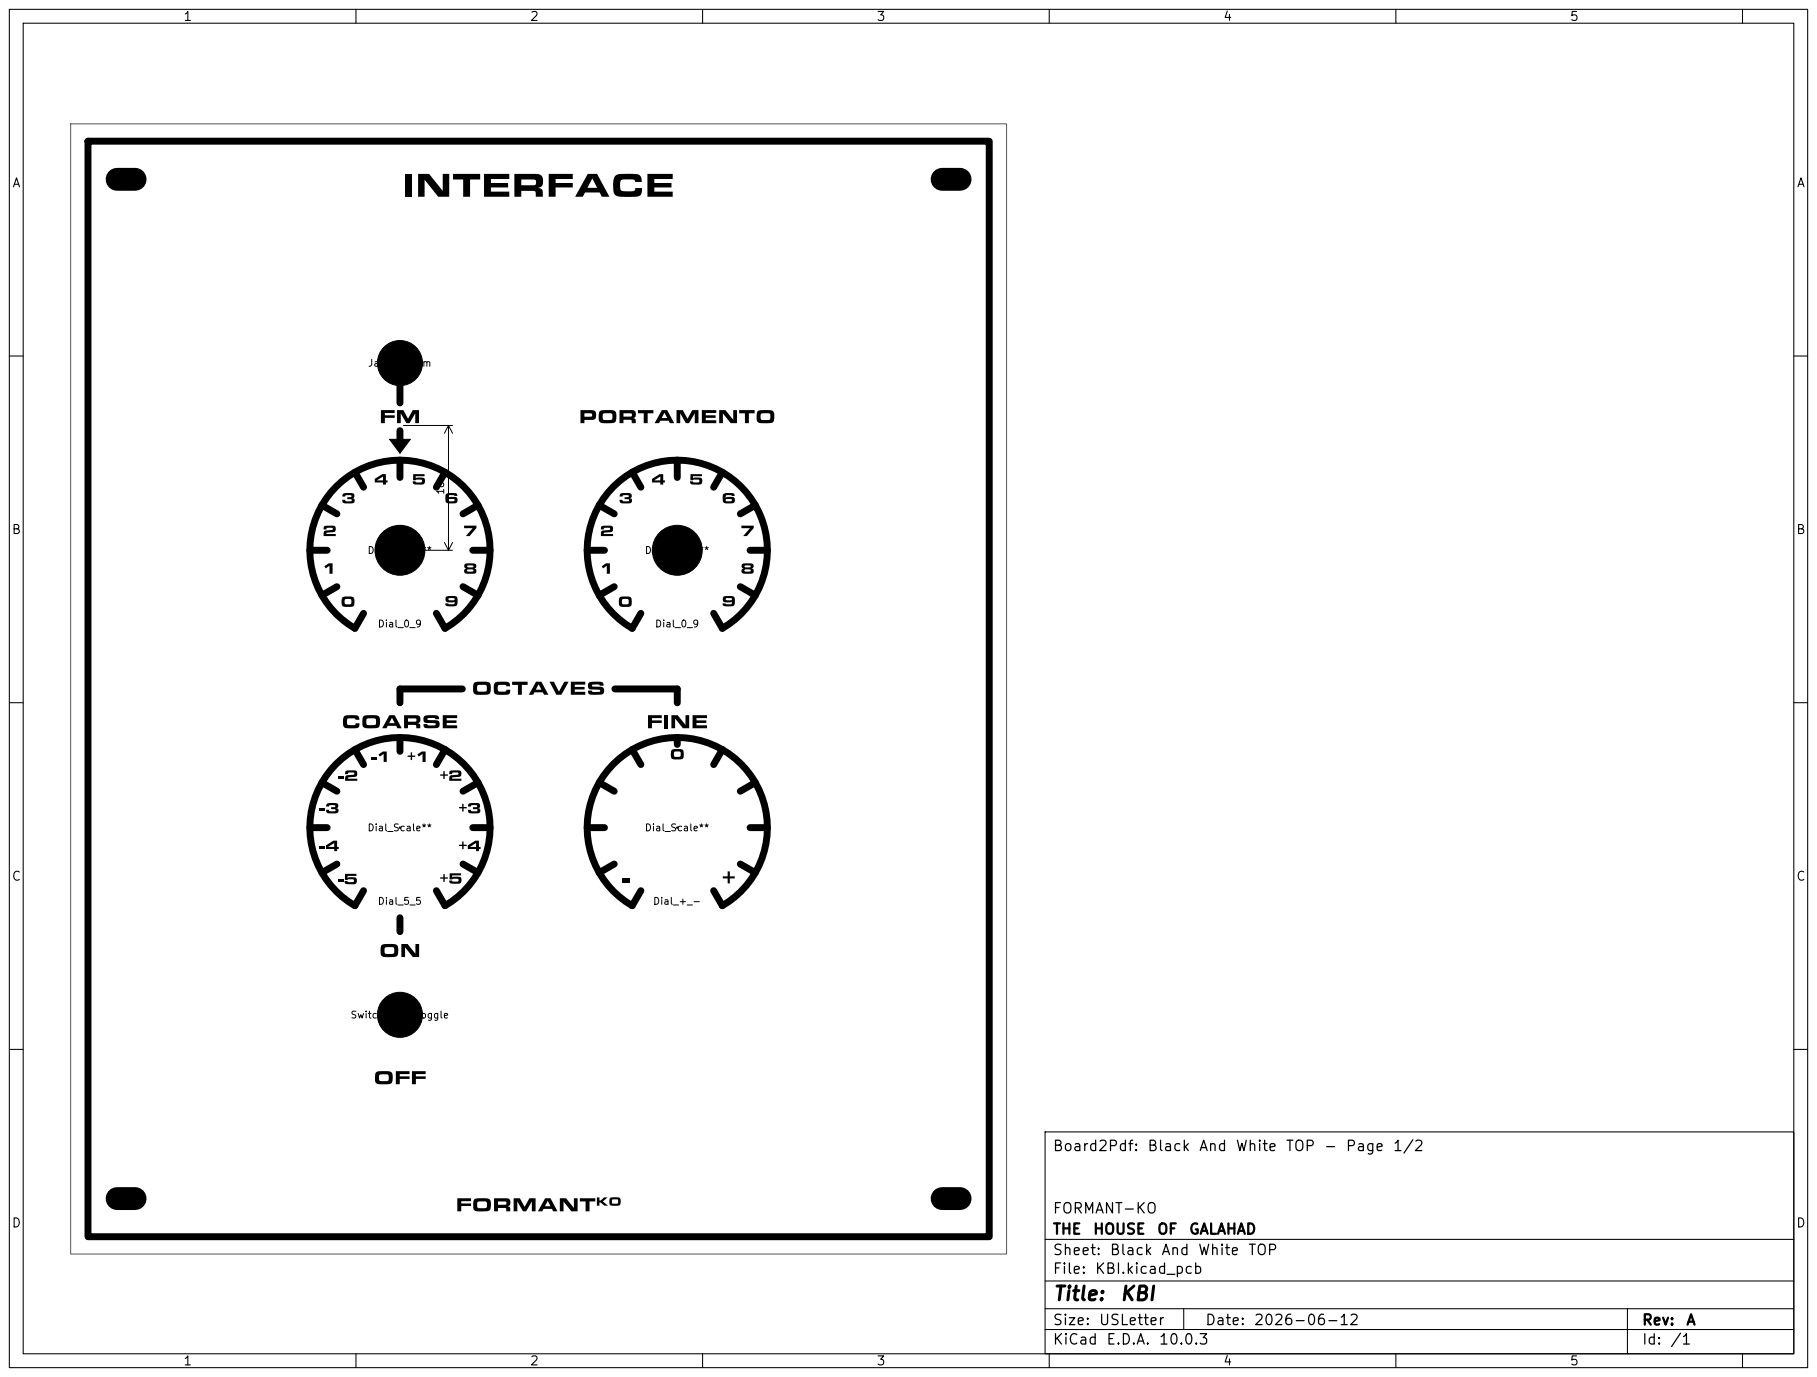
[picture p296: page 1]
D Date: 2026-06-12; Size: USLetter; Rev: A; Dial_Scale** Dial_+_-; Dial_Scale** Dial_5_5; Jack_3.5mm REF** Switch_Mini_Toggle REF**; Dial_Scale** Dial_0_9 Dial_Scale** Dial_0_9 H3

Board2Pdf: Black And White TOP - Page 1/2

FORMANT-KO
THE HOUSE OF GALAHAD
Sheet: Black And White TOP
File: KBI.kicad_pcb
Title: KBI
KiCad E.D.A. 10.0.3

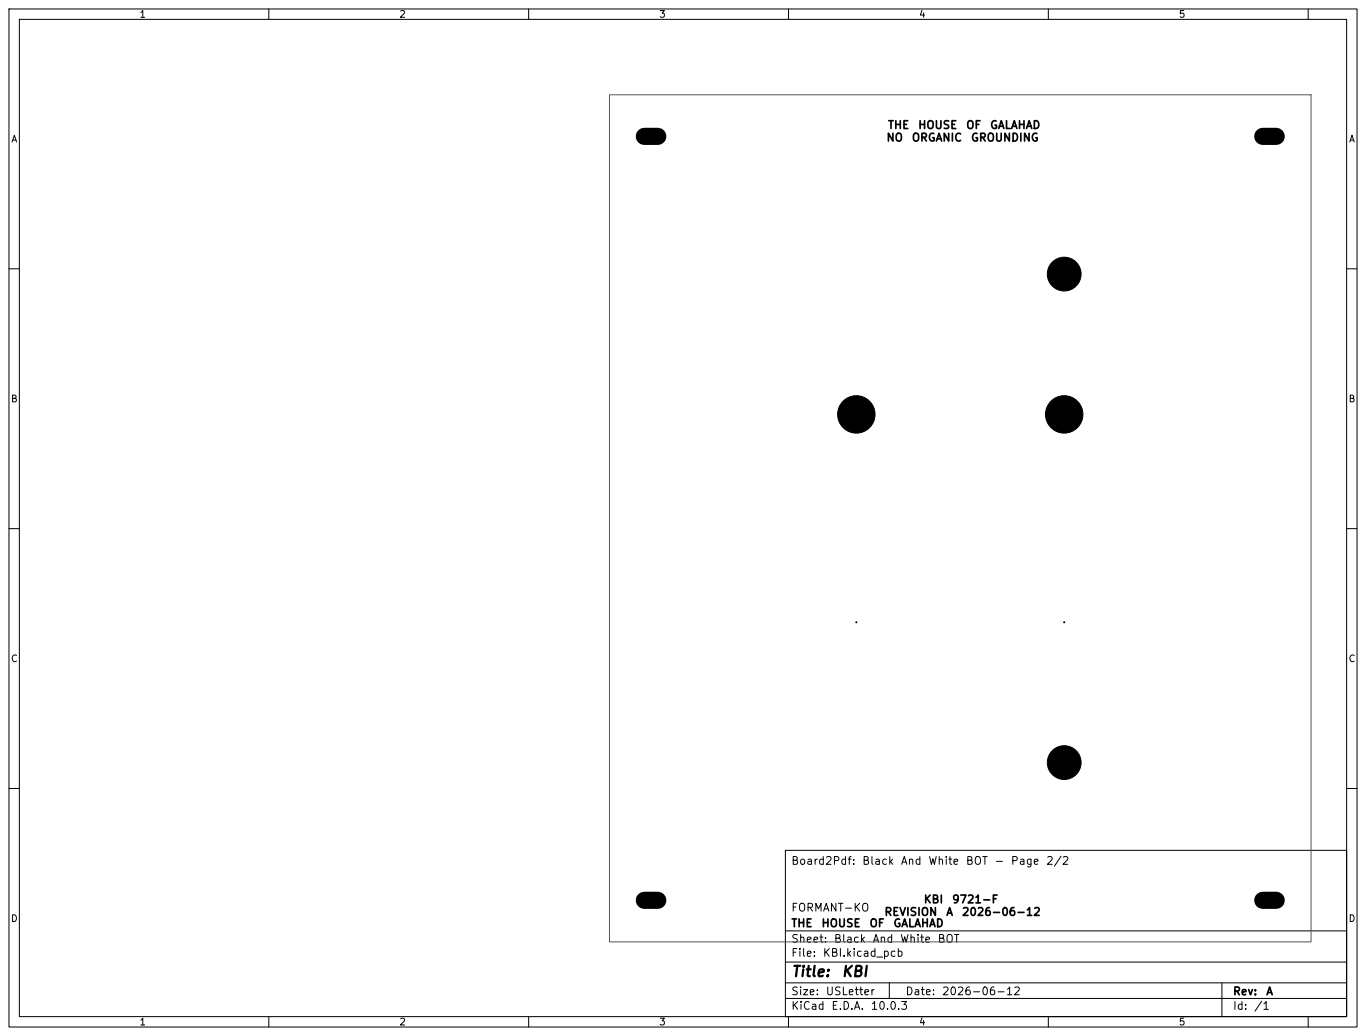
[picture p297: page 2]
KBI 9721-F REVISION A 2026-06-12; D Date: 2026-06-12; Size: USLetter; Rev: A

THE HOUSE OF GALAHAD
NO ORGANIC GROUNDING

Board2Pdf: Black And White BOT - Page 2/2

FORMANT-KO
Sheet: Black And White BOT
File: KBI.kicad_pcb
Title: KBI
KiCad E.D.A. 10.0.3
