Desval27/FormantKO/panels/NOISE/plots/NOISE__Assembly.pdf

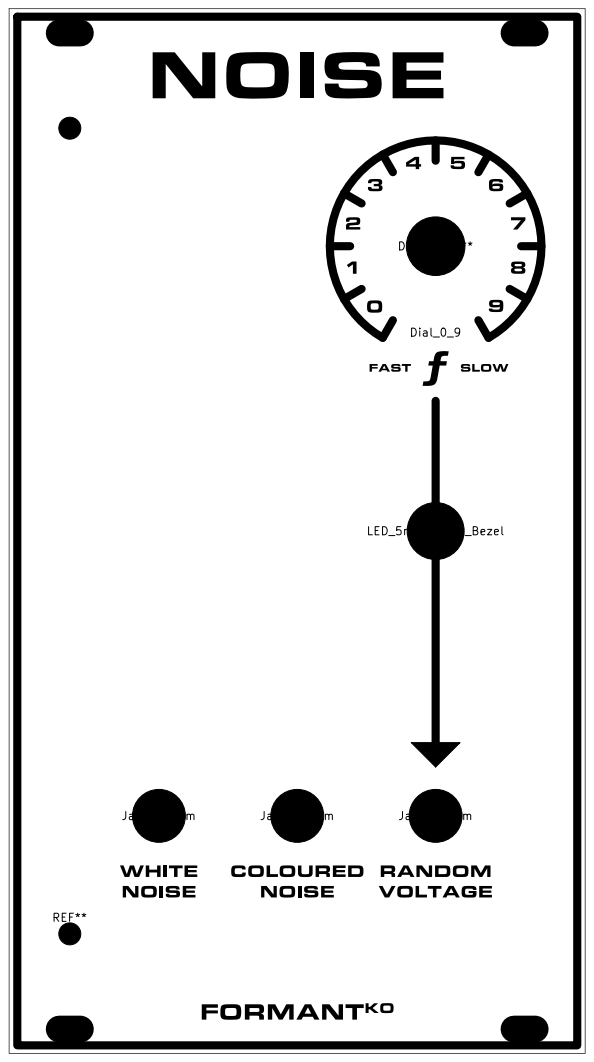
[picture p300: page 1]
D Date: 2026-06-05; Size: USLetter; Rev: A; Dial_Scale** Dial_0_9; LED_5mm_Small_Bezel REF** H3; Jack_3.5mm REF**; Jack_3.5mm REF** REF**

Board2Pdf: Black And White TOP - Page 1/2

FORMANT-KO
THE HOUSE OF GALAHAD
Sheet: Black And White TOP
File: NOISE.kicad_pcb
Title: NOISE
KiCad E.D.A. 10.0.3

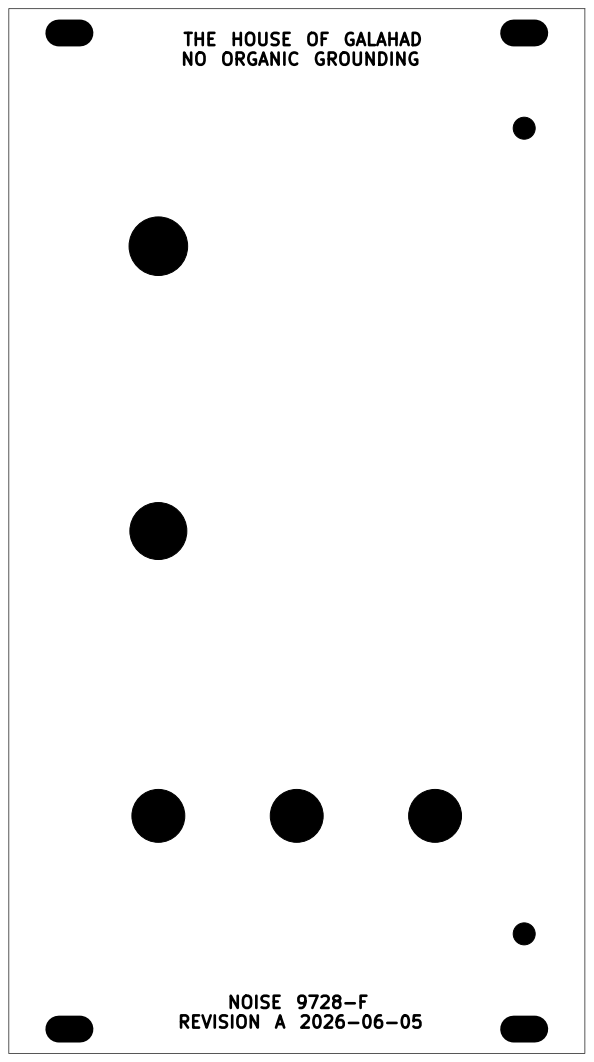
[picture p301: page 2]
NOISE 9728-F REVISION A 2026-06-05; D Date: 2026-06-05; Size: USLetter; Rev: A

THE HOUSE OF GALAHAD
NO ORGANIC GROUNDING

Board2Pdf: Black And White BOT - Page 2/2

FORMANT-KO
Sheet: Black And White BOT
File: NOISE.kicad_pcb
Title: NOISE
KiCad E.D.A. 10.0.3
