Desval27/FormantKO/panels/RFM/plots/RFM__Assembly.pdf

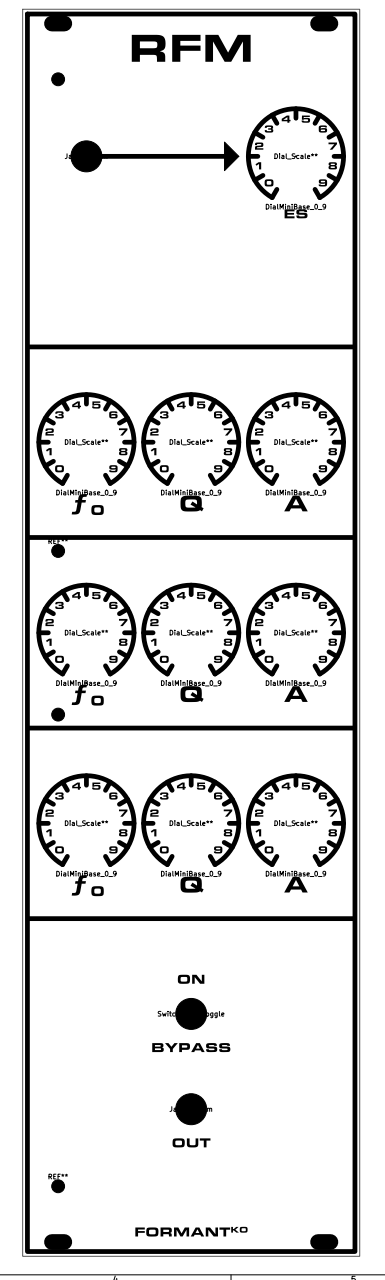
[picture p302: page 1]
F Date: 2026-06-05; Size: A3; Rev: A; Dial_Scale** DialMiniBase_0_9; Switch_Mini_Toggle REF** H3 REF**; Jack_3.5mm REF**; REF**; Dial_Scale** DialMiniBase_0_9 Dial_Scale** DialMiniBase_0_9; H2 Dial_Scale** DialMiniBase_0_9 Dial_Scale** DialMiniBase_0_9

Board2Pdf: Black And White TOP - Page 1/2

FORMANT-KO
THE HOUSE OF GALAHAD
Sheet: Black And White TOP
File: RFM.kicad_pcb
Title: RFM
KiCad E.D.A. 10.0.3

## THE HOUSE OF GALAHAD NO ORGANIC GROUNDING

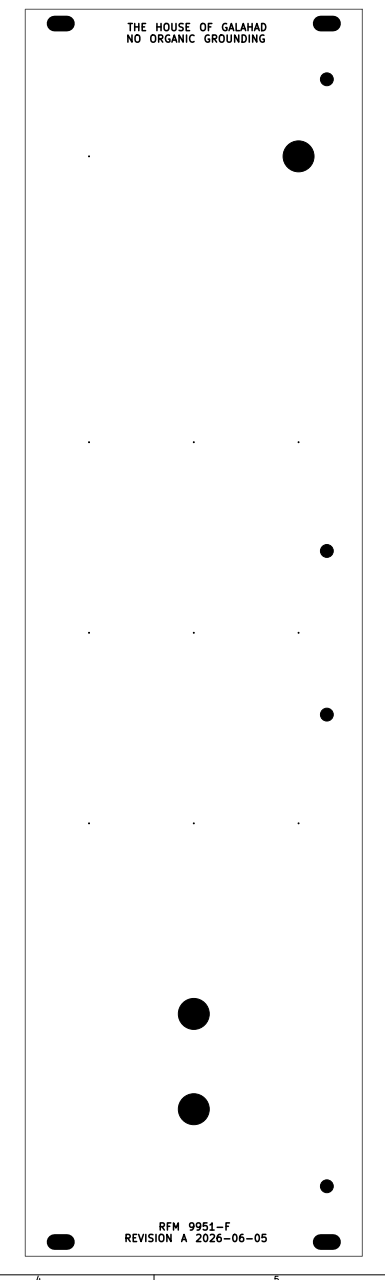
[picture p303: page 2]
RFM 9951-F REVISION A 2026-06-05; F Date: 2026-06-05; Size: A3; Rev: A

Board2Pdf: Black And White BOT - Page 2/2

FORMANT-KO
THE HOUSE OF GALAHAD
Sheet: Black And White BOT
File: RFM.kicad_pcb
Title: RFM
KiCad E.D.A. 10.0.3
