Desval27/FormantKO/panels/VCF_12/plots/VCF_12__Assembly.pdf

# Jack_3.5mm REF** Dial_Scale** Dial_0_9 Dial_Scale** Dial_0_9 H3

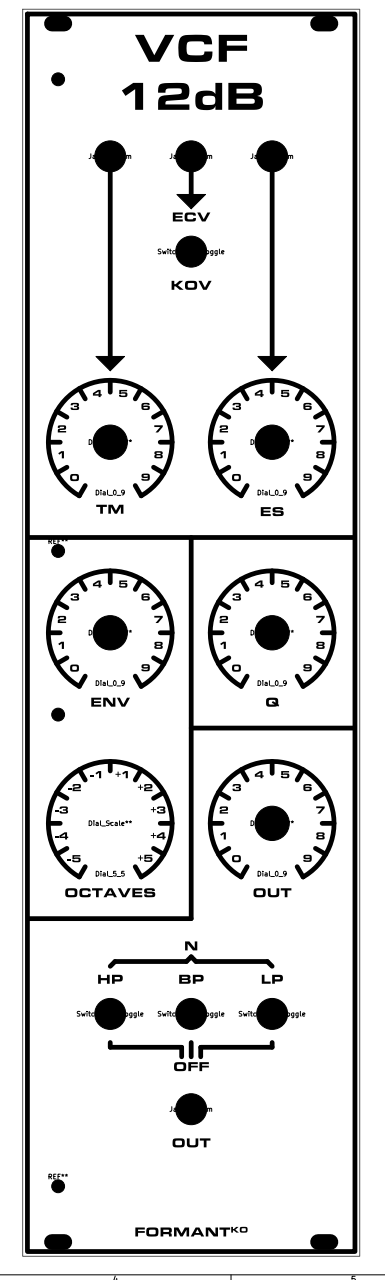
[picture p304: page 1]
F Date: 2026-06-05; Size: A3; Rev: A; Switch_Mini_Toggle REF** REF**; Dial_Scale** Dial_0_9; Jack_3.5mm REF**; Switch_Mini_Toggle REF**; Switch_Mini_Toggle REF** Dial_Scale** Dial_5_5 Dial_Scale** Dial_0_9 REF**

Board2Pdf: Black And White TOP - Page 1/2

FORMANT-KO
THE HOUSE OF GALAHAD
Sheet: Black And White TOP
File: VCF_12.kicad_pcb
Title: VCF-12
KiCad E.D.A. 10.0.3

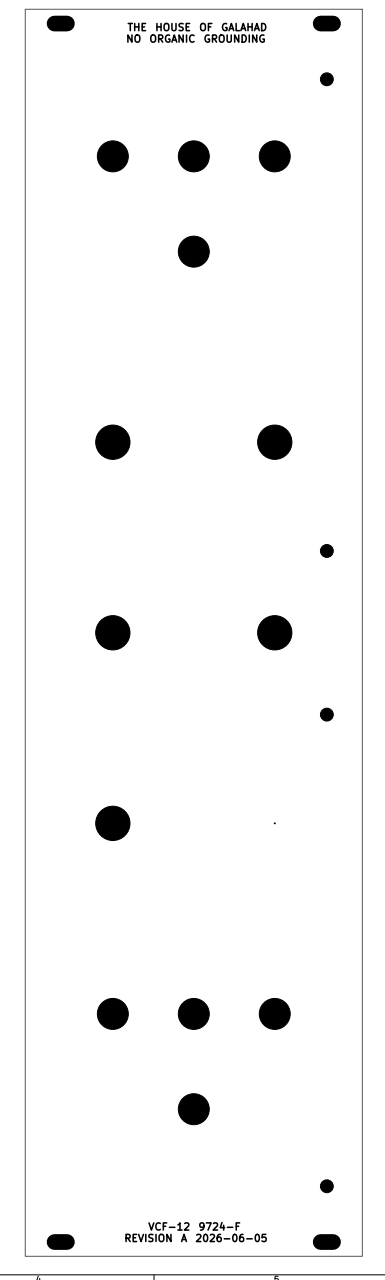
[picture p305: page 2]
VCF-12 9724-F REVISION A 2026-06-05; F Date: 2026-06-05; Size: A3; Rev: A

THE HOUSE OF GALAHAD
NO ORGANIC GROUNDING

Board2Pdf: Black And White BOT - Page 2/2

FORMANT-KO
Sheet: Black And White BOT
File: VCF_12.kicad_pcb
Title: VCF-12
KiCad E.D.A. 10.0.3
