Desval27/FormantKO/panels/VCF_24/plots/VCF_24__Assembly.pdf

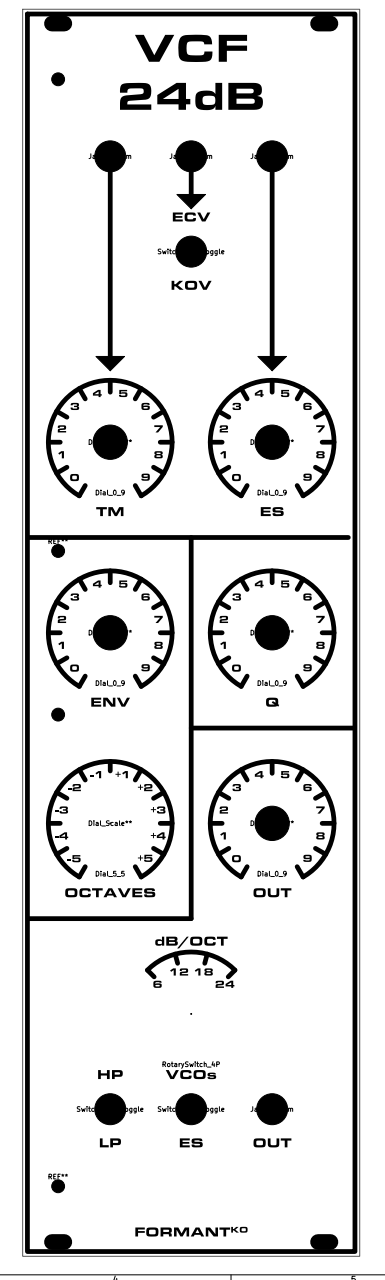
[picture p306: page 1]
F Date: 2026-06-05; Size: A3; Rev: A; Dial_Scale** Dial_0_9; Jack_3.5mm REF**; Switch_Mini_Toggle REF**; H3 REF**; Dial_Scale** Dial_5_5 Dial_Scale** Dial_0_9; REF**; RotarySwitch_4P

Board2Pdf: Black And White TOP - Page 1/2

FORMANT-KO
THE HOUSE OF GALAHAD
Sheet: Black And White TOP
File: VCF_24.kicad_pcb
Title: VCF-24
KiCad E.D.A. 10.0.3

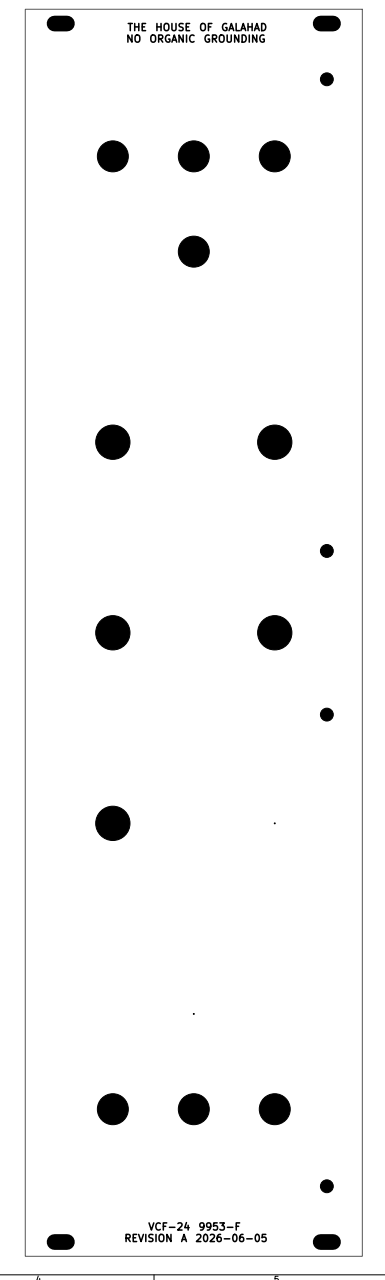
[picture p307: page 2]
VCF-24 9953-F REVISION A 2026-06-05; F Date: 2026-06-05; Size: A3; Rev: A

THE HOUSE OF GALAHAD
NO ORGANIC GROUNDING

Board2Pdf: Black And White BOT - Page 2/2

FORMANT-KO
Sheet: Black And White BOT
File: VCF_24.kicad_pcb
Title: VCF-24
KiCad E.D.A. 10.0.3
