Desval27/FormantKO/panels/VCO/plots/VCO__Assembly.pdf

Switch_Mini_Toggle REF** LED_5mm_Small_Bezel REF** Dial_Scale** Dial_0_9 Dial_Scale** Dial_+_-

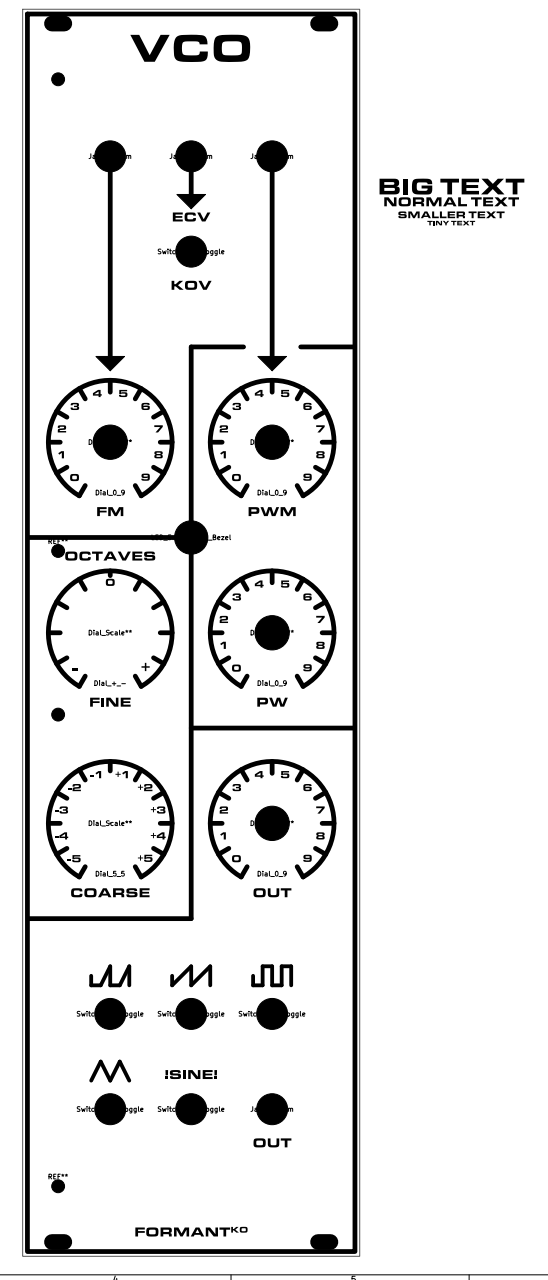
[picture p308: page 1]
F Date: 2026-06-11; Size: A3; Rev: A; Dial_Scale** Dial_0_9; Switch_Mini_Toggle REF**; Switch_Mini_Toggle REF** H3; REF**; Jack_3.5mm REF**; Switch_Mini_Toggle REF** Dial_Scale** Dial_5_5

Board2Pdf: Black And White TOP - Page 1/2

FORMANT-KO
THE HOUSE OF GALAHAD
Sheet: Black And White TOP
File: VCO.kicad_pcb
Title: VCO
KiCad E.D.A. 10.0.3

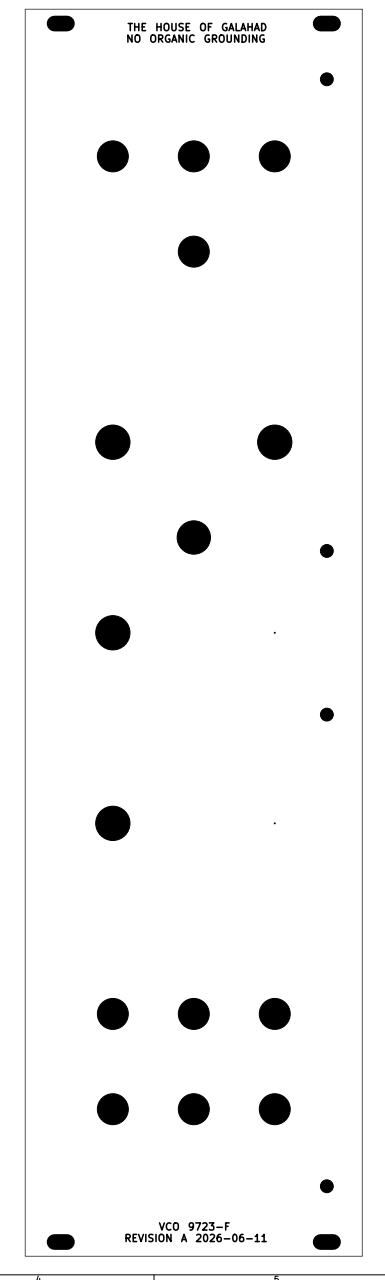
[picture p309: page 2]
VCO 9723-F REVISION A 2026-06-11; F Date: 2026-06-11; Size: A3; Rev: A

THE HOUSE OF GALAHAD
NO ORGANIC GROUNDING

Board2Pdf: Black And White BOT - Page 2/2

FORMANT-KO
Sheet: Black And White BOT
File: VCO.kicad_pcb
Title: VCO
KiCad E.D.A. 10.0.3
