Desval27/FormantKO/system/BACKPLANE_A/plots/BACKPLANE_A__Assembly.pdf

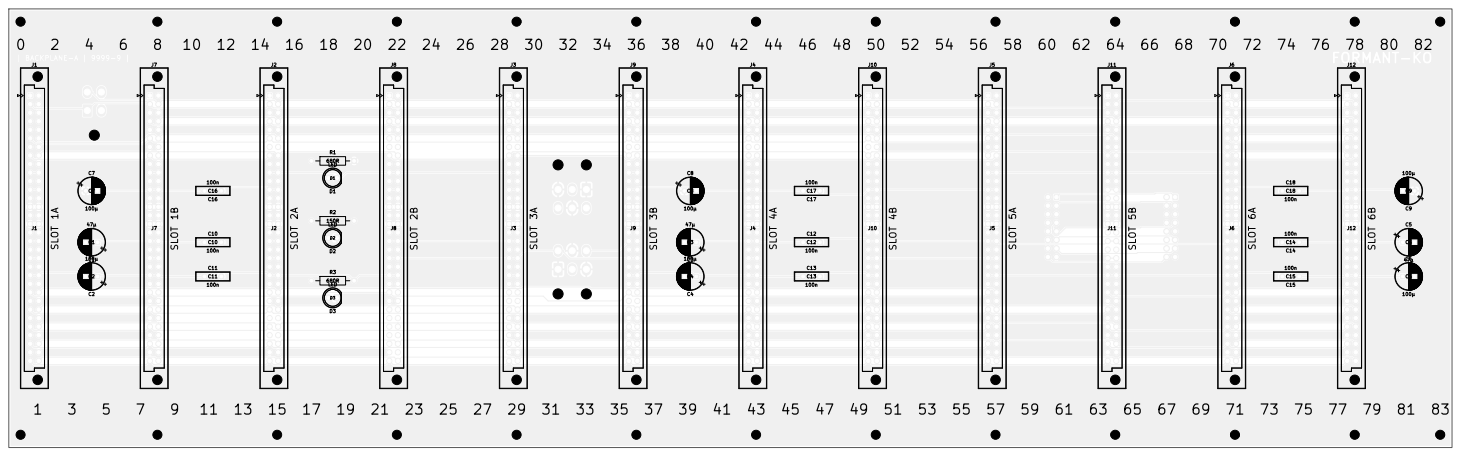
[picture p310: page 1]

Board2Pdf: Black And White TOP - Page 1/2

FORMANT-KO
THE HOUSE OF GALAHAD
Sheet: Black And White TOP
File: BACKPLANE_A.kicad_pcb
Title: BACKPLANE A
KiCad E.D.A. 10.0.3

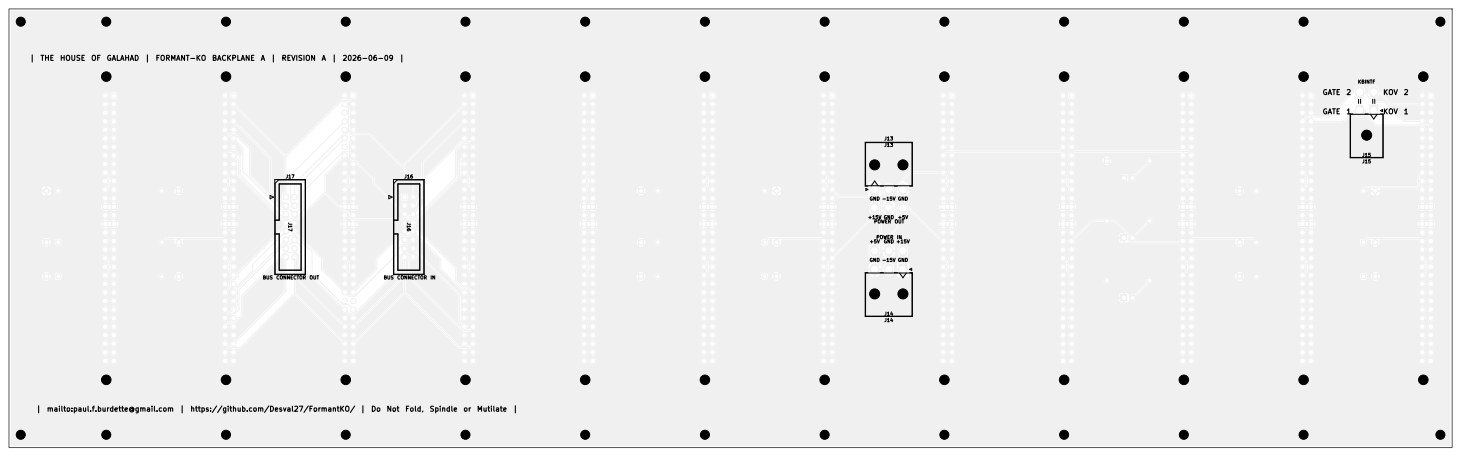
[picture p311: page 2]
KOV 2; KOV 1; GATE 2; GATE 1; J15 KBINTF; FGH; FGH Date: 2026-06-09; Size: A2; Rev: A

THE HOUSE OF GALAHAD | FORMANT-KO BACKPLANE A | REVISION A | 2026-06-09

J13 POWER OUT GND +5V -15V GND

J16 BUS CONNECTOR IN

J17 BUS CONNECTOR OUT

GND +15V
J14 POWER IN+15V GND
GND -15V +5V GND

Board2Pdf: Black And White BOT - Page 2/2 J16

mailto:paul.f.burdette@gmail.com | https://github.com/Desval27/FormantKO/ | Do Not Fold, Spindle or Mutilate

FORMANT-KO
THE HOUSE OF GALAHAD
Sheet: Black And White BOT
File: BACKPLANE_A.kicad_pcb
Title: BACKPLANE A
KiCad E.D.A. 10.0.3
