Desval27/FormantKO/MFOS/modules/CALIBRATOR/doc/assembly.pdf

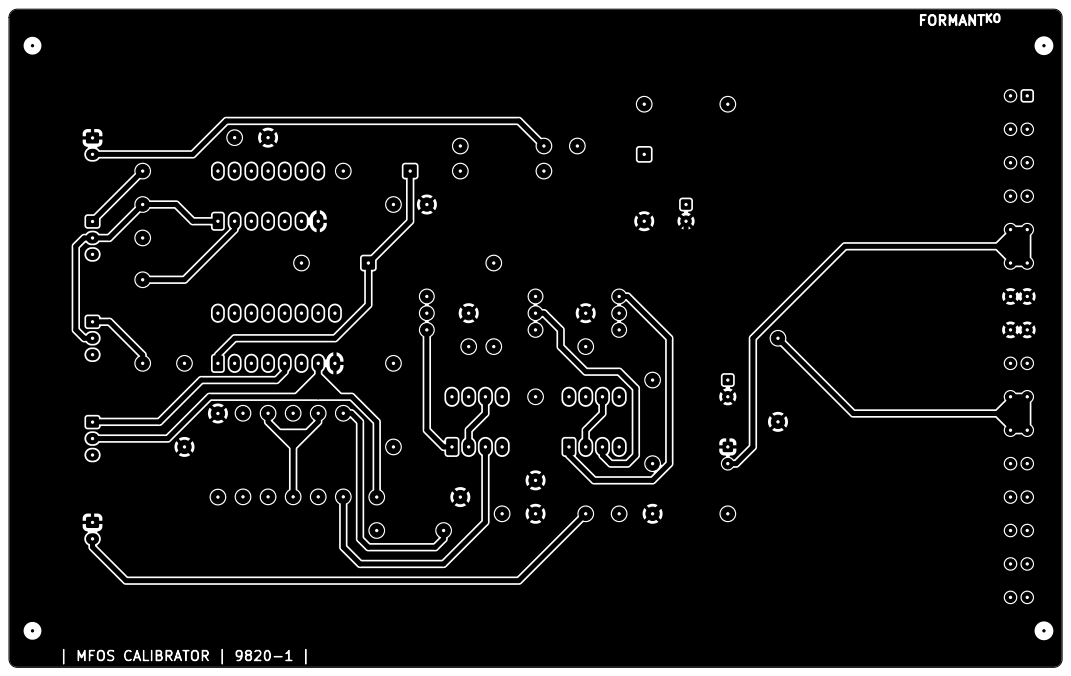
[picture p312: page 1]

KO mailto:paul.f.burdette@gmail.com

Do Not Fold, Spindle or Mutiliate
https://github.com/Desval27/FormantKO/

FORMANT
THE HOUSE OF GALAHAD
Sheet:
File: CALIBRATOR.kicad_pcb
Title: MFOS CALIBRATOR

Size: USLetter | Rev: A
KiCad E.D.A. 10.0.5 | Id: 1/6

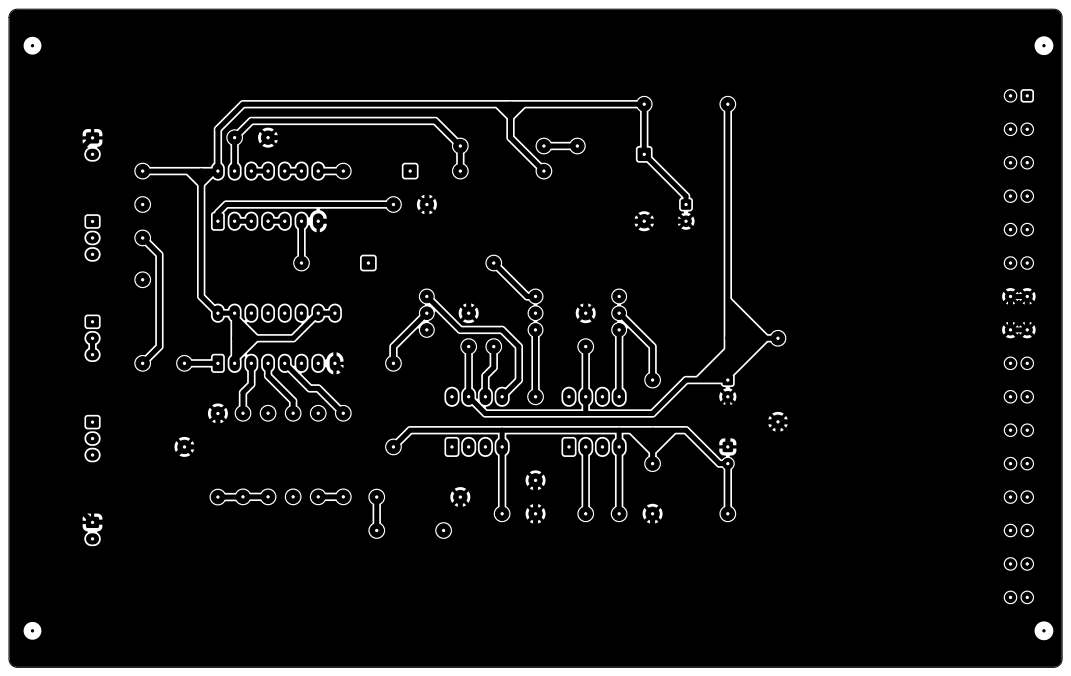
[picture p313: page 2]

KO mailto:paul.f.burdette@gmail.com

Do Not Fold, Spindle or Mutiliate
https://github.com/Desval27/FormantKO/

FORMANT
THE HOUSE OF GALAHAD
Sheet:
File: CALIBRATOR.kicad_pcb
Title: MFOS CALIBRATOR

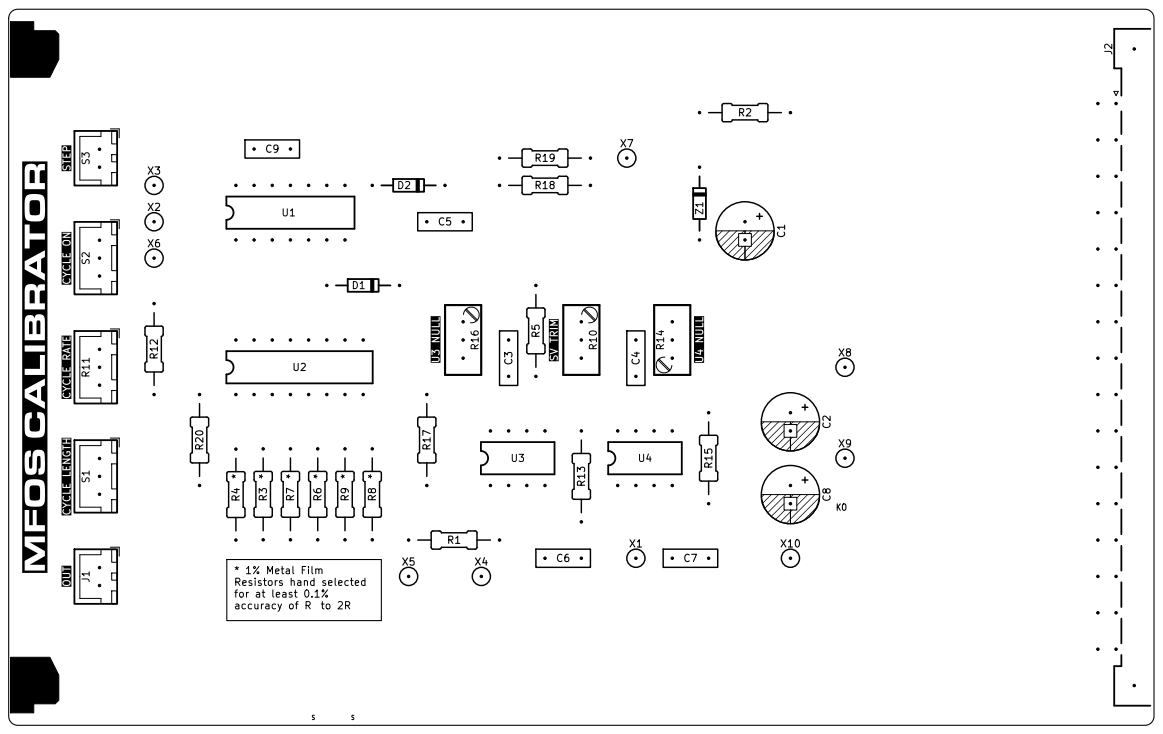
[picture p314: page 3]

KO mailto:paul.f.burdette@gmail.com

Do Not Fold, Spindle or Mutiliate
https://github.com/Desval27/FormantKO/

FORMANT
THE HOUSE OF GALAHAD
Sheet:
File: CALIBRATOR.kicad_pcb
Title: MFOS CALIBRATOR

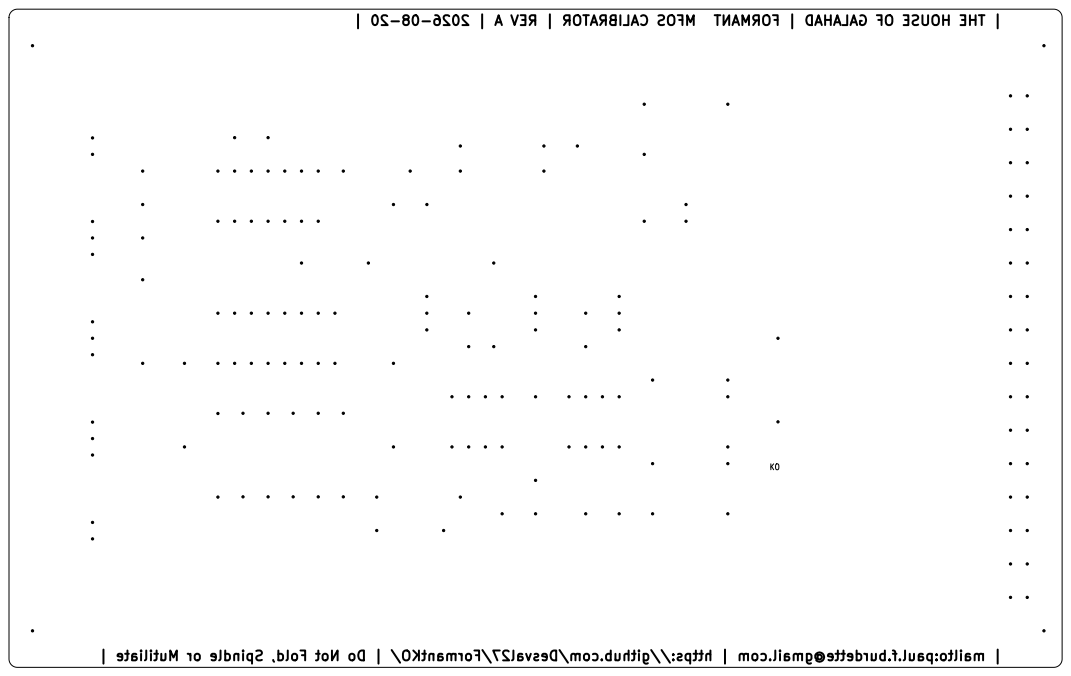
[picture p315: page 4]

KO mailto:paul.f.burdette@gmail.com

Do Not Fold, Spindle or Mutiliate
https://github.com/Desval27/FormantKO/

FORMANT
THE HOUSE OF GALAHAD
Sheet:
File: CALIBRATOR.kicad_pcb
Title: MFOS CALIBRATOR

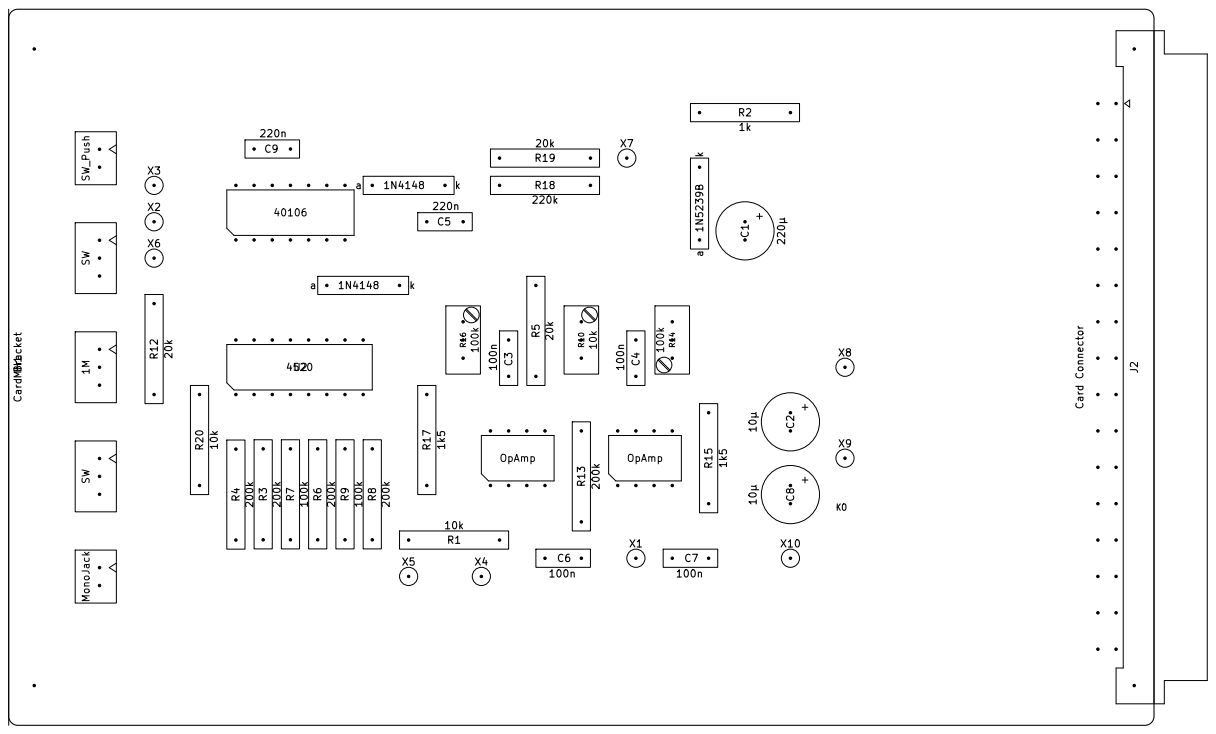
[picture p316: page 5]

KO mailto:paul.f.burdette@gmail.com

https://github.com/Desval27/FormantKO/

FORMANT
THE HOUSE OF GALAHAD
Sheet:
File: CALIBRATOR.kicad_pcb
Title: MFOS CALIBRATOR

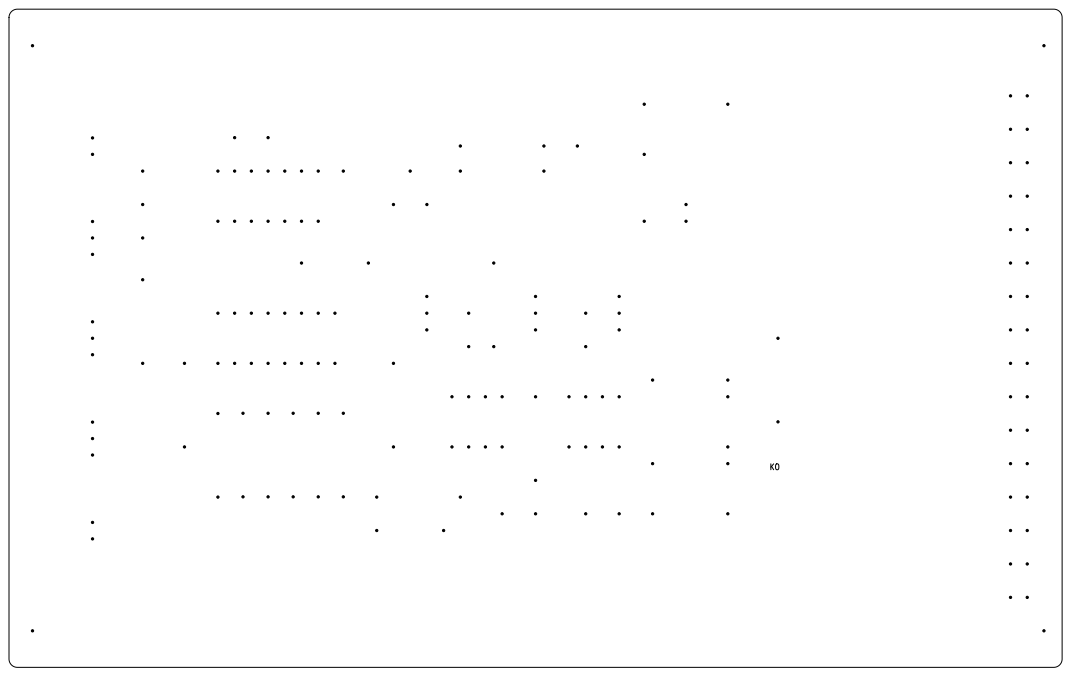
[picture p317: page 6]

KO mailto:paul.f.burdette@gmail.com

Do Not Fold, Spindle or Mutiliate
https://github.com/Desval27/FormantKO/

FORMANT
THE HOUSE OF GALAHAD
Sheet:
File: CALIBRATOR.kicad_pcb
Title: MFOS CALIBRATOR
