Desval27/FormantKO/MFOS/modules/CALIBRATOR/doc/schematic.pdf

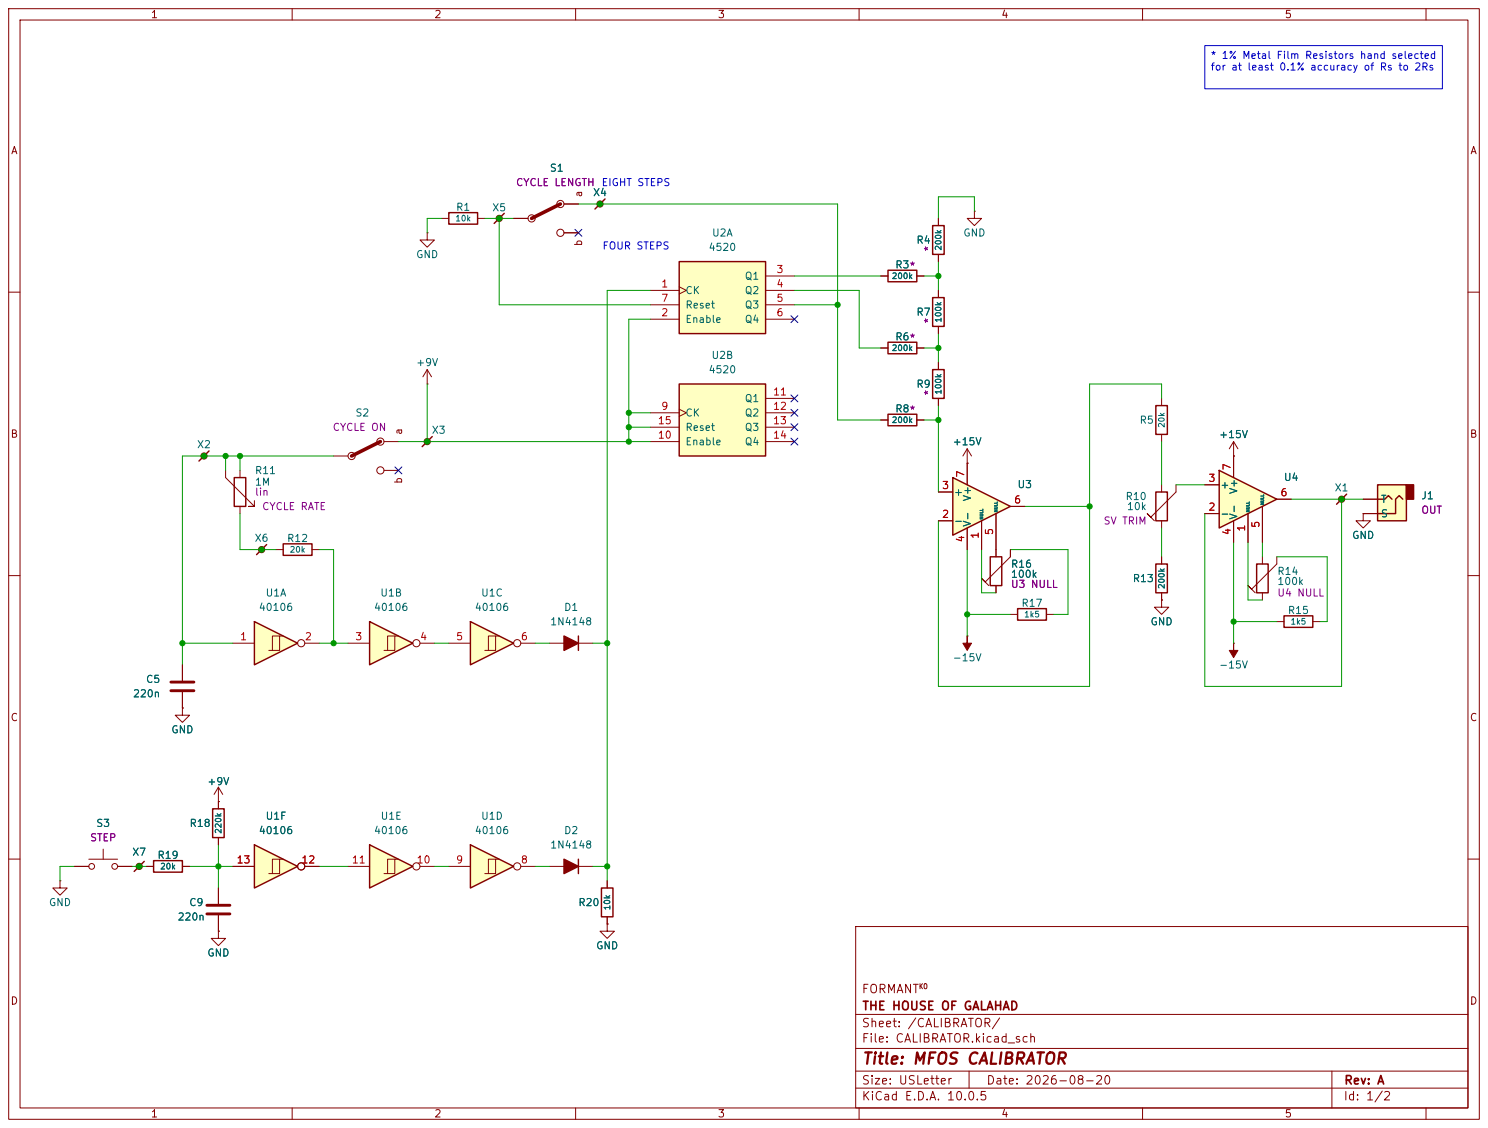
[picture p318: page 1]

for at least 0.1% accuracy of Rs to 2Rs FOUR STEPS

FORMANTKO
THE HOUSE OF GALAHAD
Sheet: /CALIBRATOR/
File: CALIBRATOR.kicad_sch
Title: MFOS CALIBRATOR

Size: USLetter | Rev: A
KiCad E.D.A. 10.0.5 | Id: 1/2

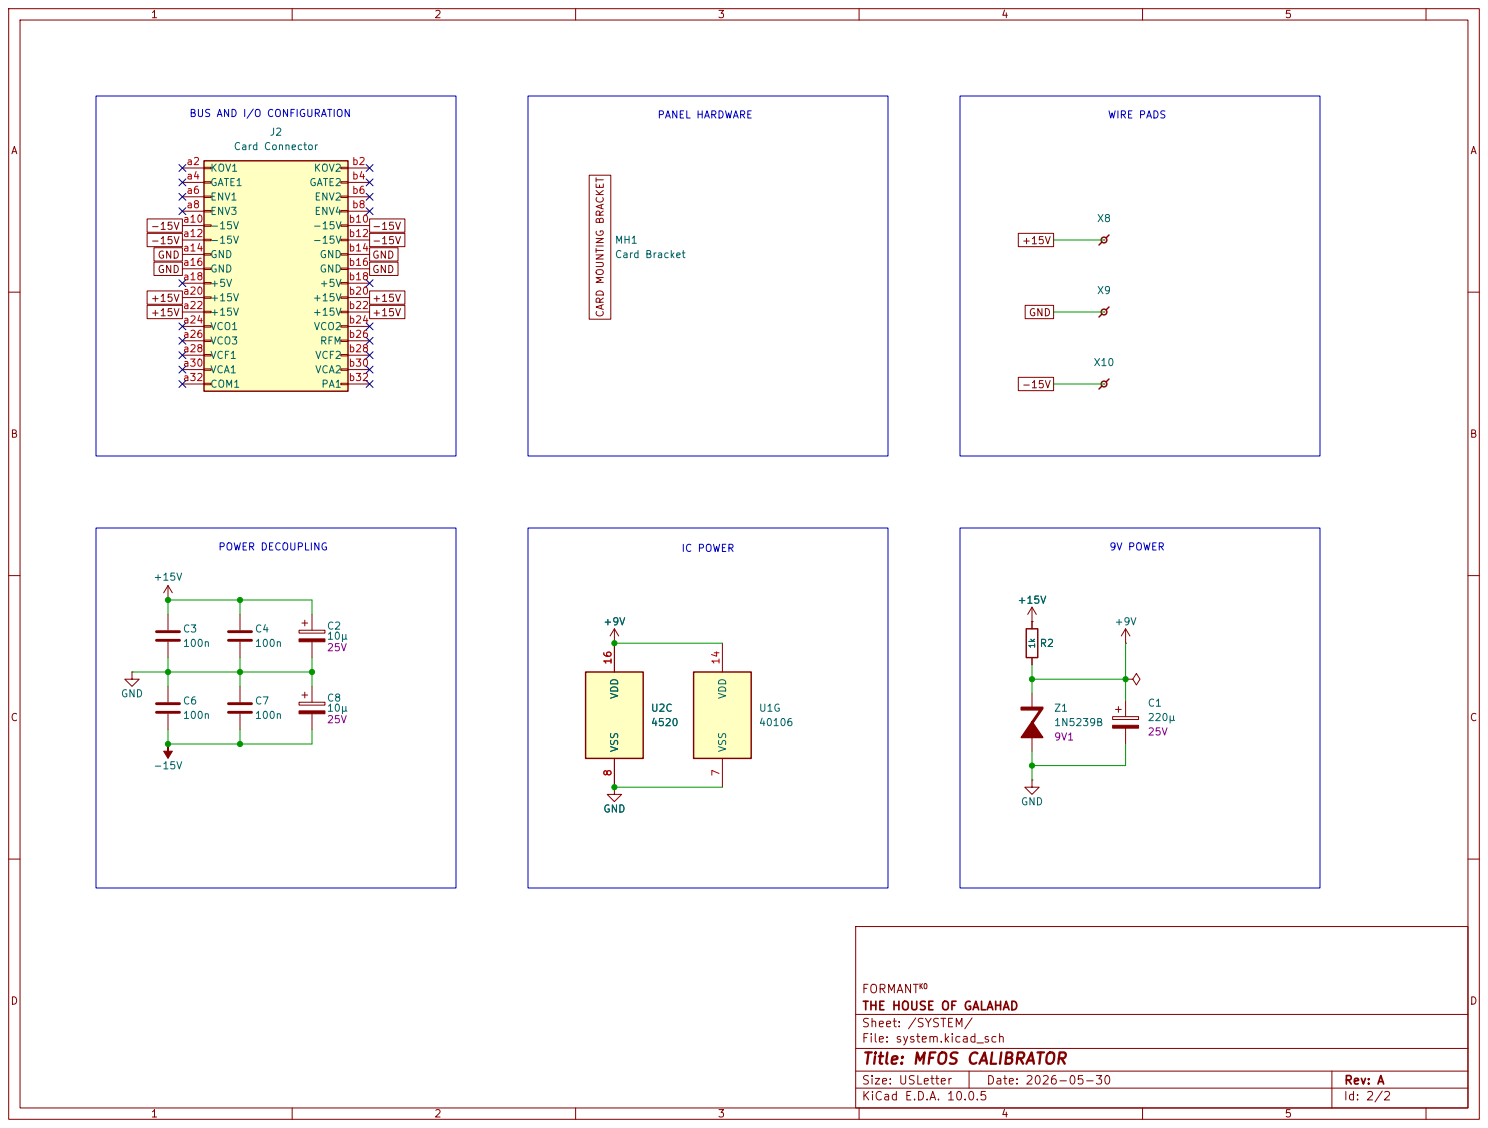
[picture p319: page 2]

THE HOUSE OF GALAHAD
Sheet: /SYSTEM/
File: system.kicad_sch
Title: MFOS CALIBRATOR

Size: USLetter | Rev: A
KiCad E.D.A. 10.0.5 | Id: 2/2
