Desval27/FormantKO/modules/POWER_SUPPLIES/BIPOLAR_PSU/doc/assembly.pdf

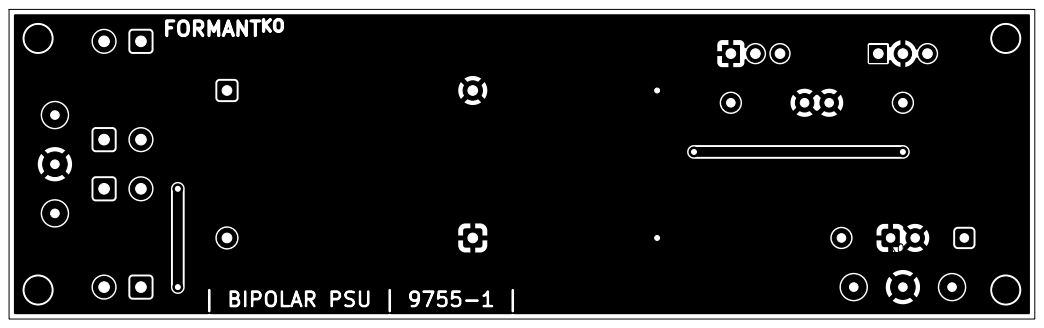
[picture p320: page 1]

KO mailto:paul.f.burdette@gmail.com

Do Not Fold, Spindle or Mutiliate
https://github.com/Desval27/FormantKO/

FORMANT
THE HOUSE OF GALAHAD
Sheet:
File: BIPOLAR_PSU.kicad_pcb
Title: BIPOLAR PSU

Size: A4 | Rev: A
KiCad E.D.A. 10.0.4 | Id: 1/6

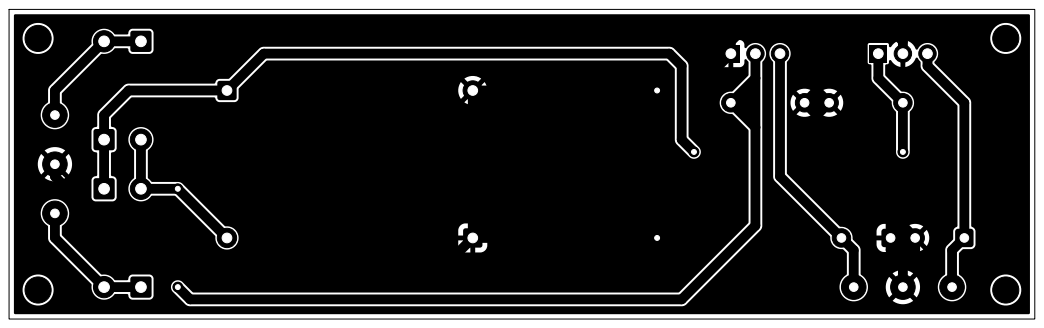
[picture p321: page 2]

KO mailto:paul.f.burdette@gmail.com

Do Not Fold, Spindle or Mutiliate
https://github.com/Desval27/FormantKO/

FORMANT
THE HOUSE OF GALAHAD
Sheet:
File: BIPOLAR_PSU.kicad_pcb
Title: BIPOLAR PSU

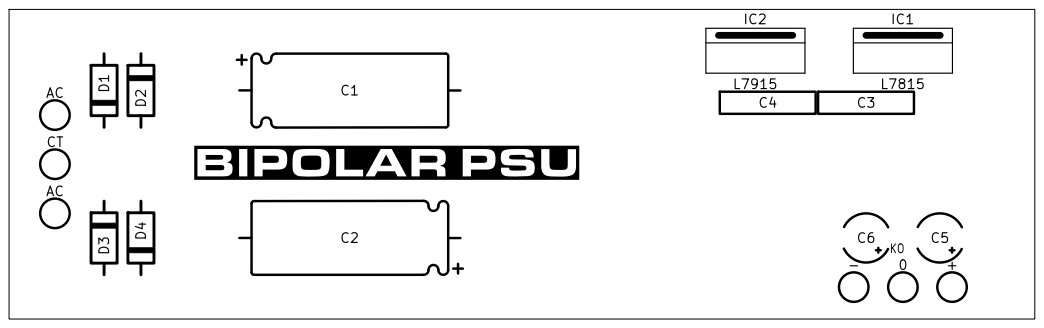
[picture p322: page 3]

KO mailto:paul.f.burdette@gmail.com

Do Not Fold, Spindle or Mutiliate
https://github.com/Desval27/FormantKO/

FORMANT
THE HOUSE OF GALAHAD
Sheet:
File: BIPOLAR_PSU.kicad_pcb
Title: BIPOLAR PSU

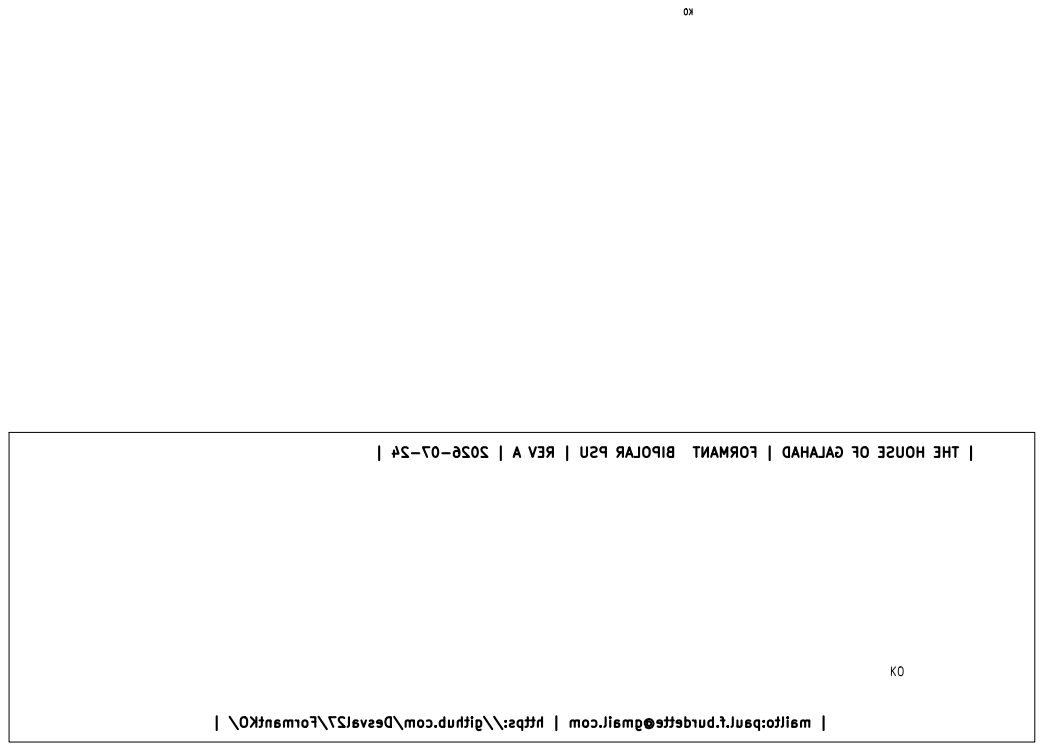
[picture p323: page 4]

KO mailto:paul.f.burdette@gmail.com

Do Not Fold, Spindle or Mutiliate
https://github.com/Desval27/FormantKO/

FORMANT
THE HOUSE OF GALAHAD
Sheet:
File: BIPOLAR_PSU.kicad_pcb
Title: BIPOLAR PSU

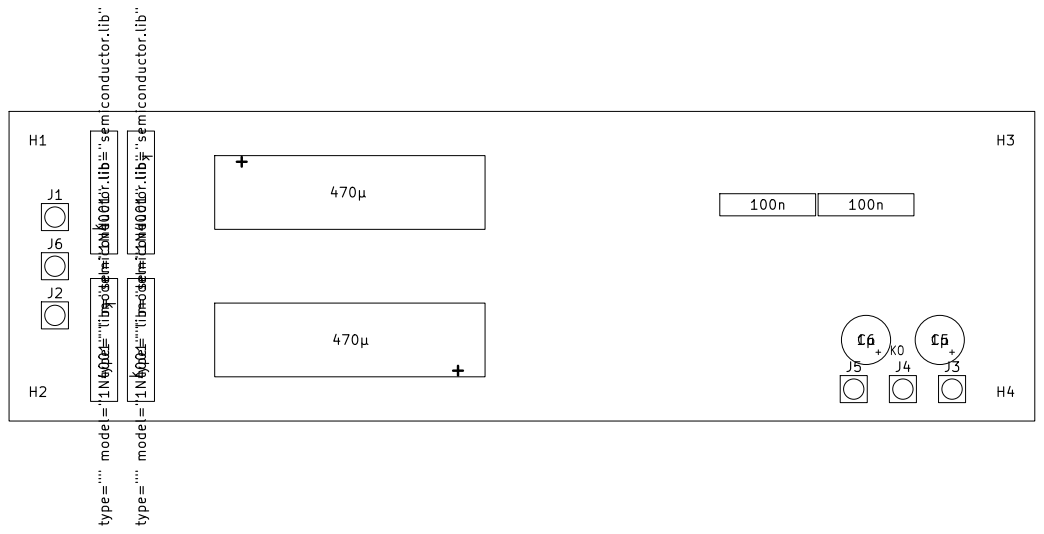
[picture p324: page 5]

KO mailto:paul.f.burdette@gmail.com

Do Not Fold, Spindle or Mutiliate
https://github.com/Desval27/FormantKO/

FORMANT
THE HOUSE OF GALAHAD
Sheet:
File: BIPOLAR_PSU.kicad_pcb
Title: BIPOLAR PSU

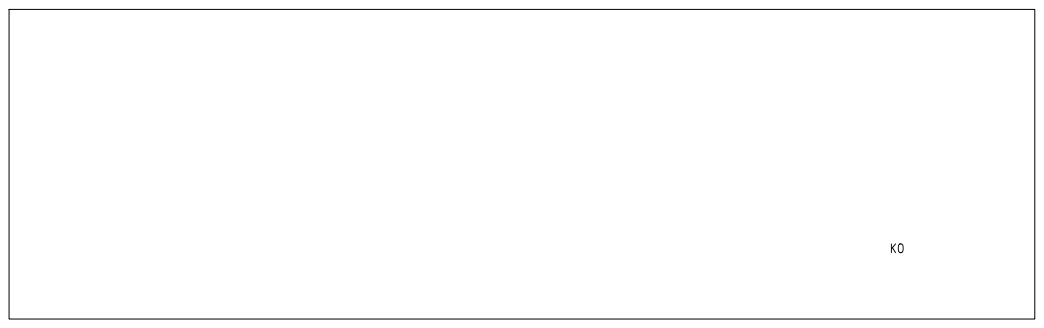
[picture p325: page 6]

KO mailto:paul.f.burdette@gmail.com

Do Not Fold, Spindle or Mutiliate
https://github.com/Desval27/FormantKO/

FORMANT
THE HOUSE OF GALAHAD
Sheet:
File: BIPOLAR_PSU.kicad_pcb
Title: BIPOLAR PSU
