Desval27/FormantKO/MFOS/panels/ANALOG/plots/ANALOG__Assembly.pdf

# H1 Dial_Scale** Dial_+_-

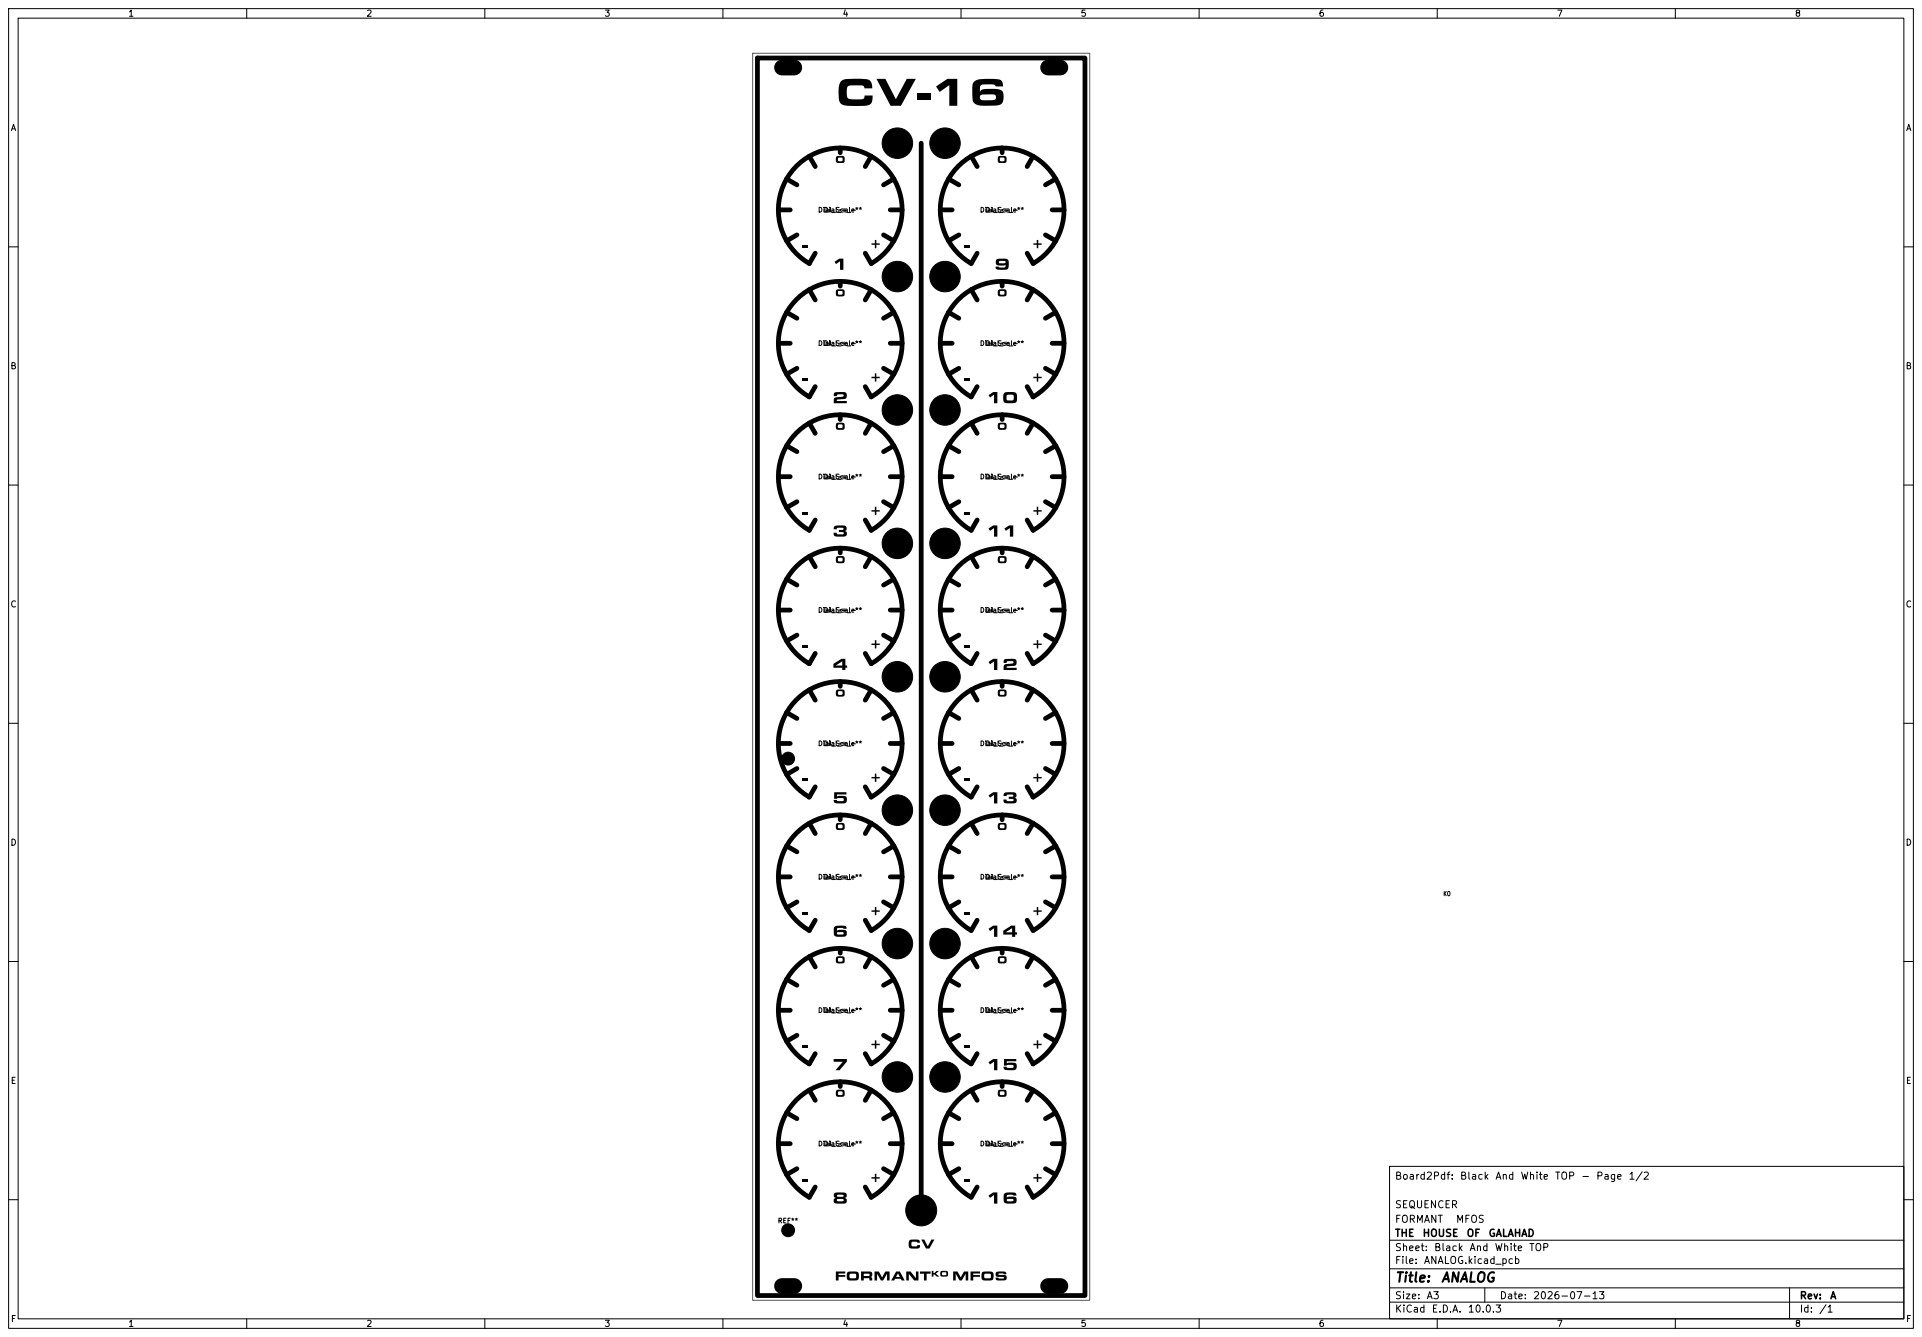
[picture p326: page 1]
F Date: 2026-07-13; Size: A3; Rev: A; KO MFOS; Dial_Scale** Dial_+_-; H3 REF**

Board2Pdf: Black And White TOP - Page 1/2

SEQUENCER
FORMANT
THE HOUSE OF GALAHAD
Sheet: Black And White TOP
File: ANALOG.kicad_pcb
Title: ANALOG
KiCad E.D.A. 10.0.3

## THE HOUSE OF GALAHAD NO ORGANIC GROUNDING

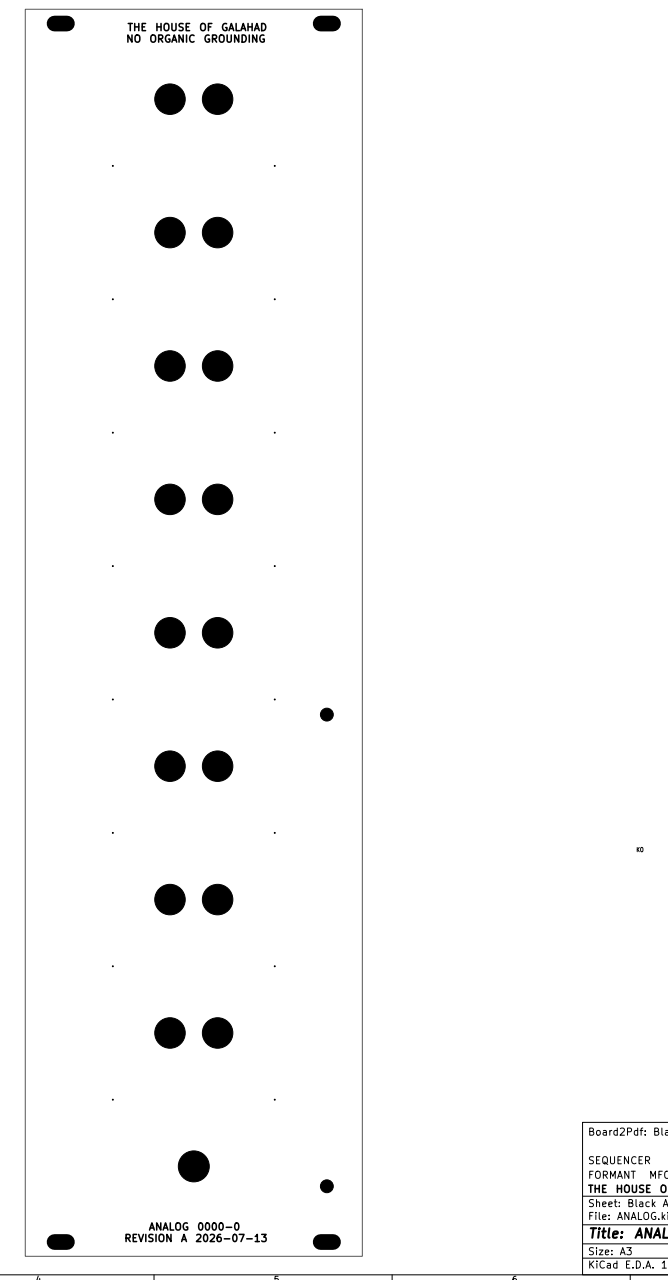
[picture p327: page 2]
ANALOG 0000-0 REVISION A 2026-07-13; F Date: 2026-07-13; Size: A3; Rev: A; KO MFOS

Board2Pdf: Black And White BOT - Page 2/2

SEQUENCER
FORMANT
THE HOUSE OF GALAHAD
Sheet: Black And White BOT
File: ANALOG.kicad_pcb
Title: ANALOG
KiCad E.D.A. 10.0.3
