Desval27/FormantKO/MFOS/modules/ANALOG/plots/ANALOG__schematic.pdf

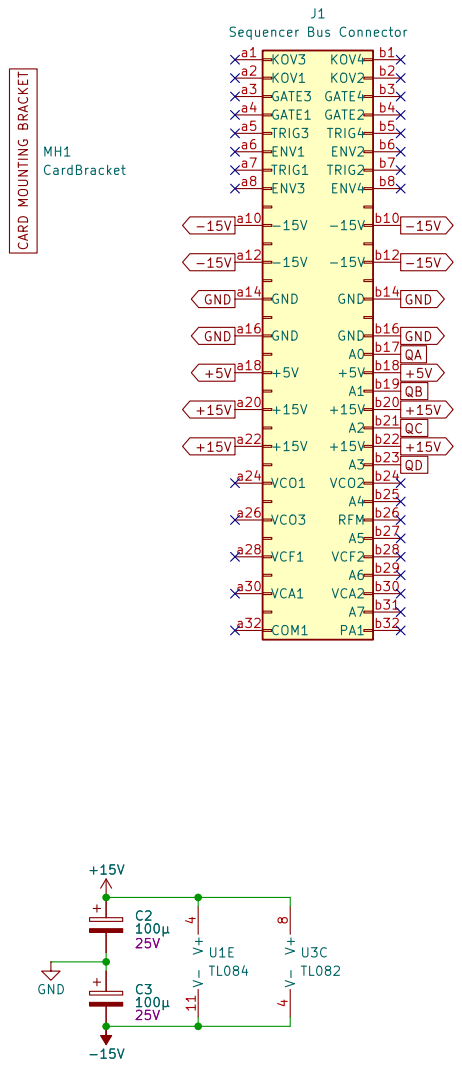
[picture p328: page 1]

SEQUENCER
FORMANTKO MFOS
THE HOUSE OF GALAHAD
Sheet: /SYSTEM/
File: system.kicad_sch
Title: ANALOG

Size: USLetter | Rev: A
KiCad E.D.A. 10.0.4 | Id: 1/4

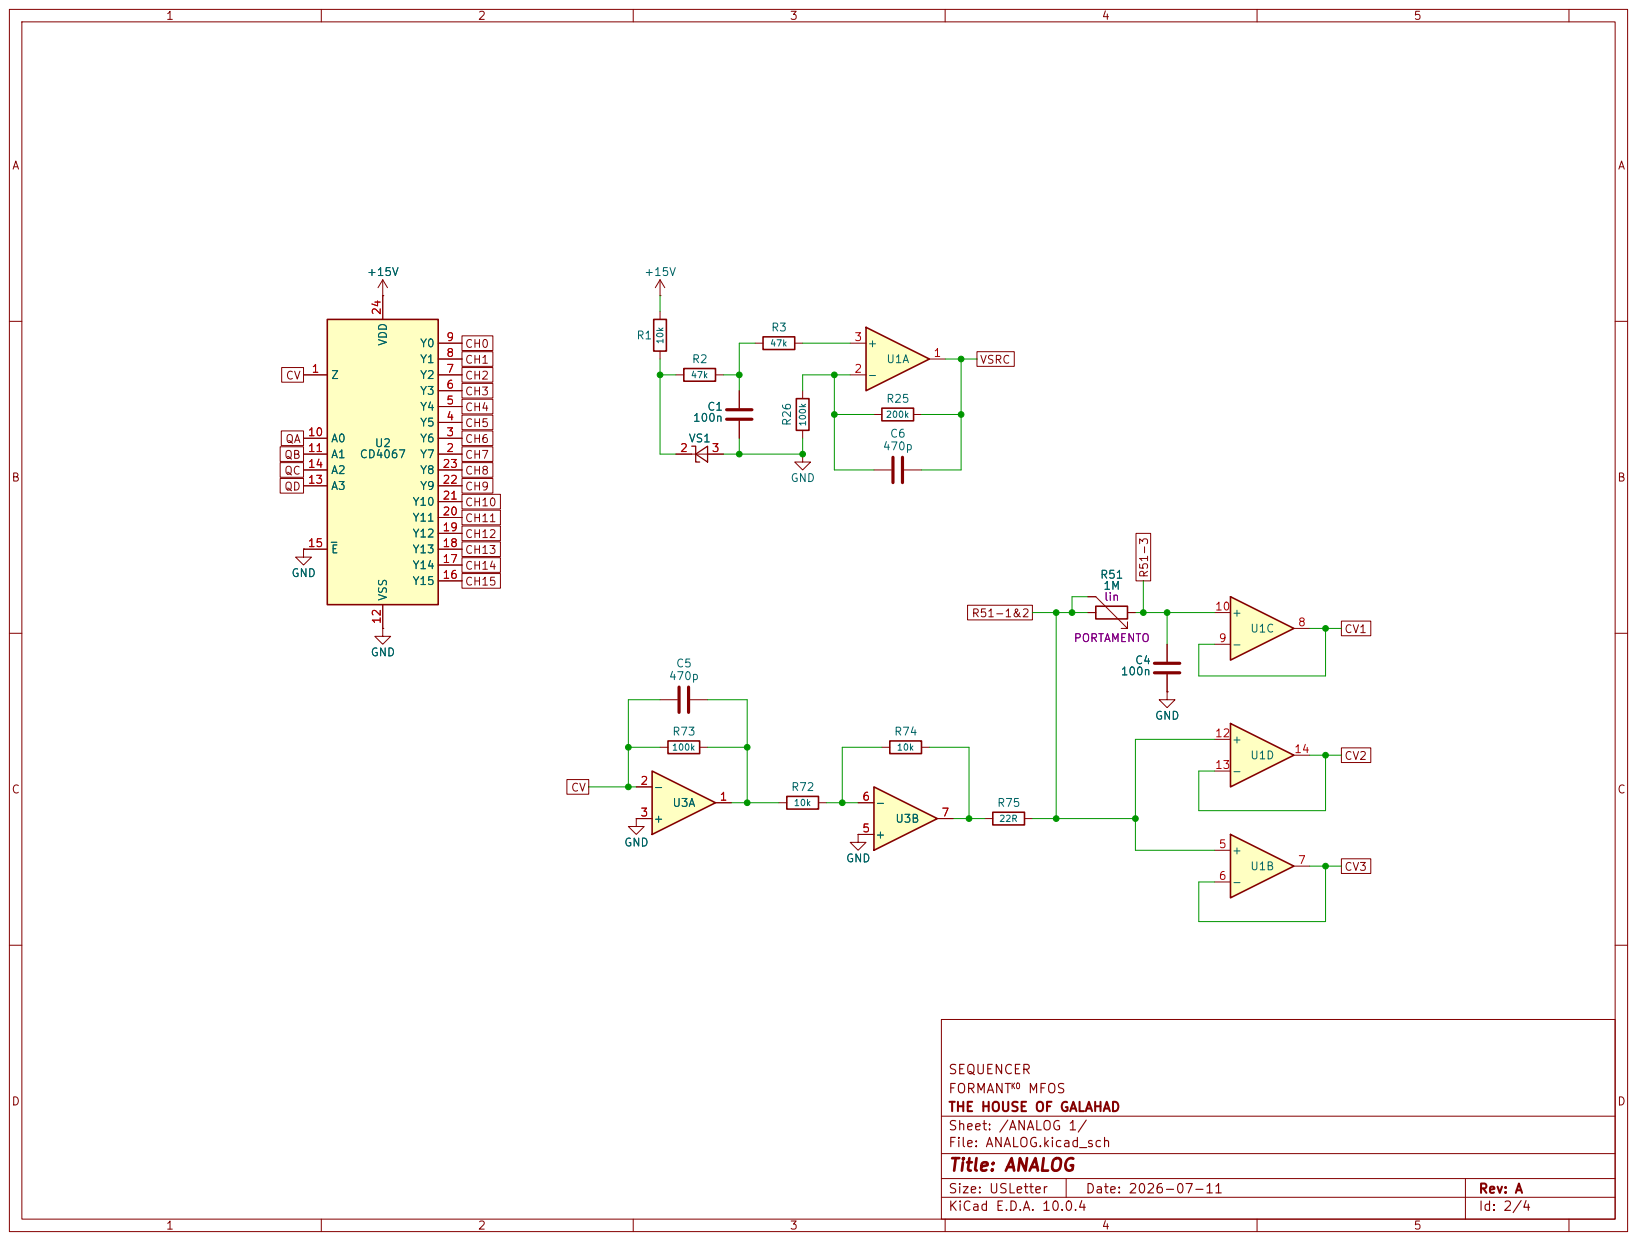
[picture p329: page 2]

SEQUENCER
FORMANTKO MFOS
THE HOUSE OF GALAHAD
Sheet: /ANALOG 1/
File: ANALOG.kicad_sch
Title: ANALOG

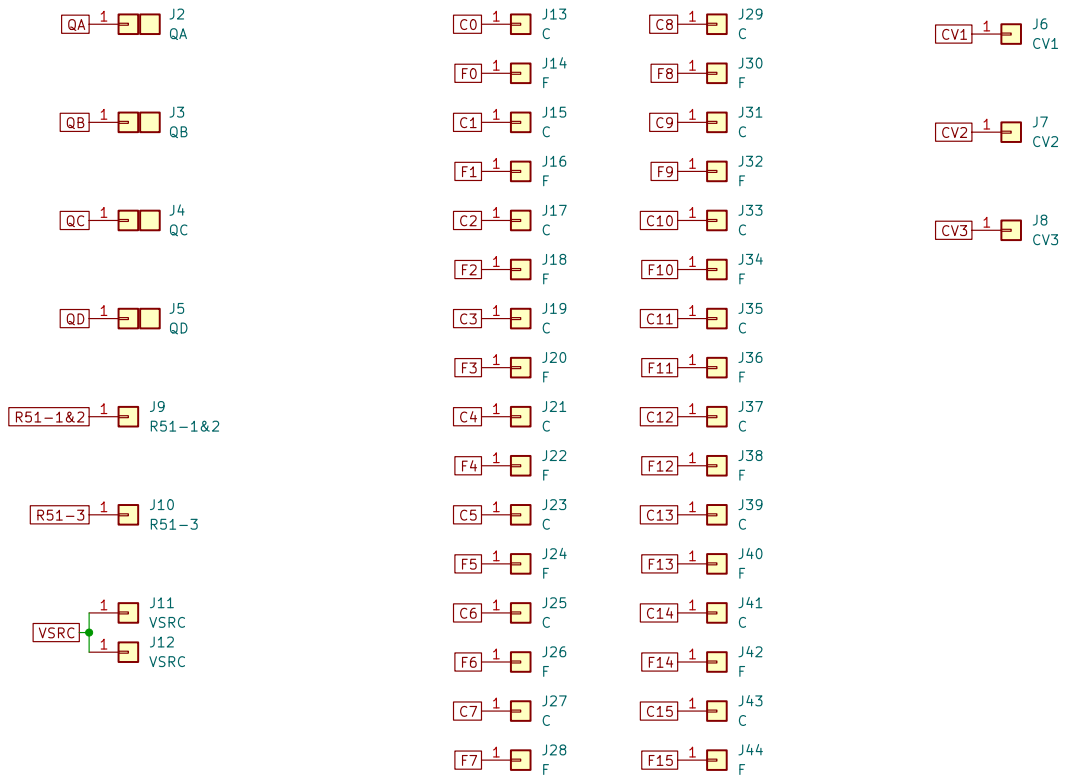
[picture p330: page 3]

FORMANTKO MFOS
THE HOUSE OF GALAHAD
Sheet: /WIRE PADS/
File: wire_pads.kicad_sch
Title: ANALOG

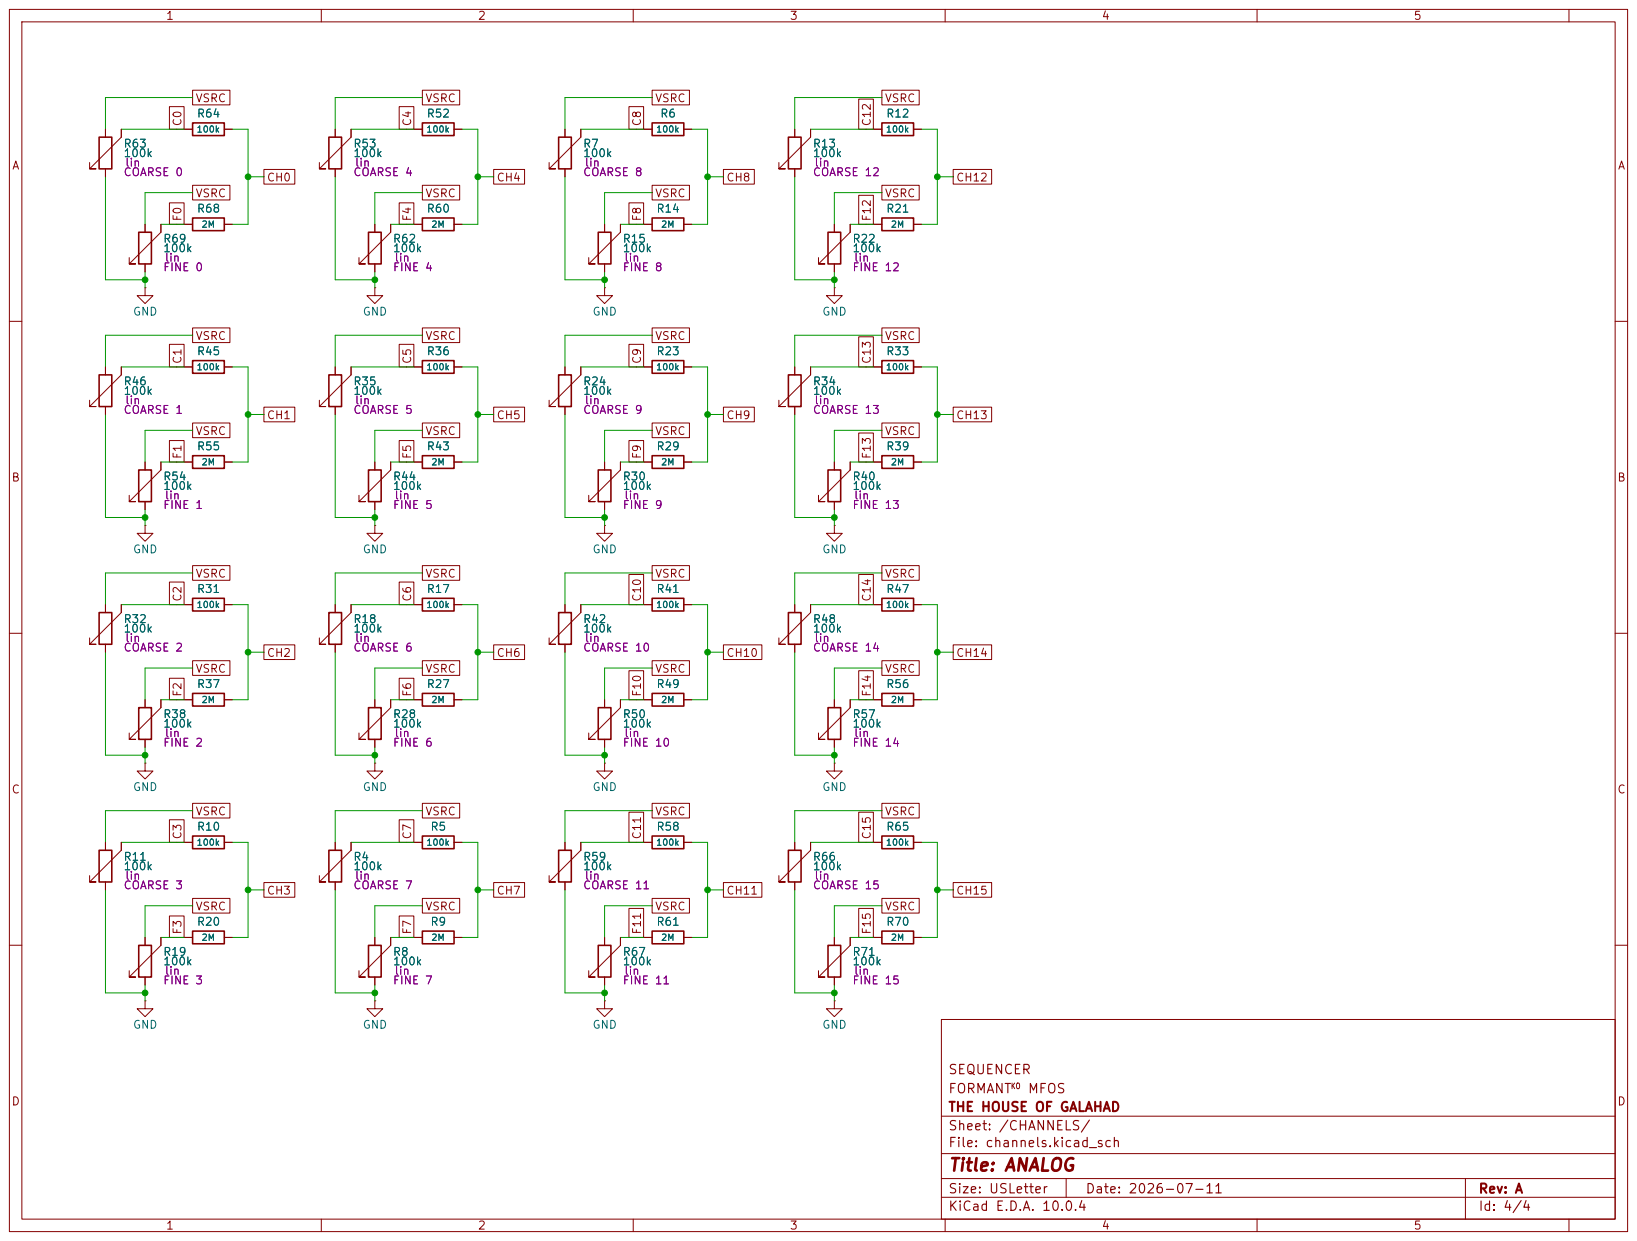
[picture p331: page 4]

100k R22 100k lin FINE 12 R57 100k lin FINE 14R56

100k R7100k lin COARSE 8 R15 100k lin FINE 8R14

R13 100k lin COARSE 12 R67 100k lin FINE 11 GND

2M R34 100k lin COARSE 13 R40 100k lin FINE 13R33

100k R28 100k lin FINE 6 R38 100k lin FINE 2R37

2M R19 100k lin FINE 3 R11 100k lin COARSE 3

2M R71 100k lin FINE 15 R66 100k lin COARSE 15 R8100k lin FINE 7R9

SEQUENCER
FORMANTKO MFOS
THE HOUSE OF GALAHAD
Sheet: /CHANNELS/
File: channels.kicad_sch
Title: ANALOG
