Desval27/FormantKO/modules/PHASE_SHIFTER/PHASE_SHIFTER.pdf

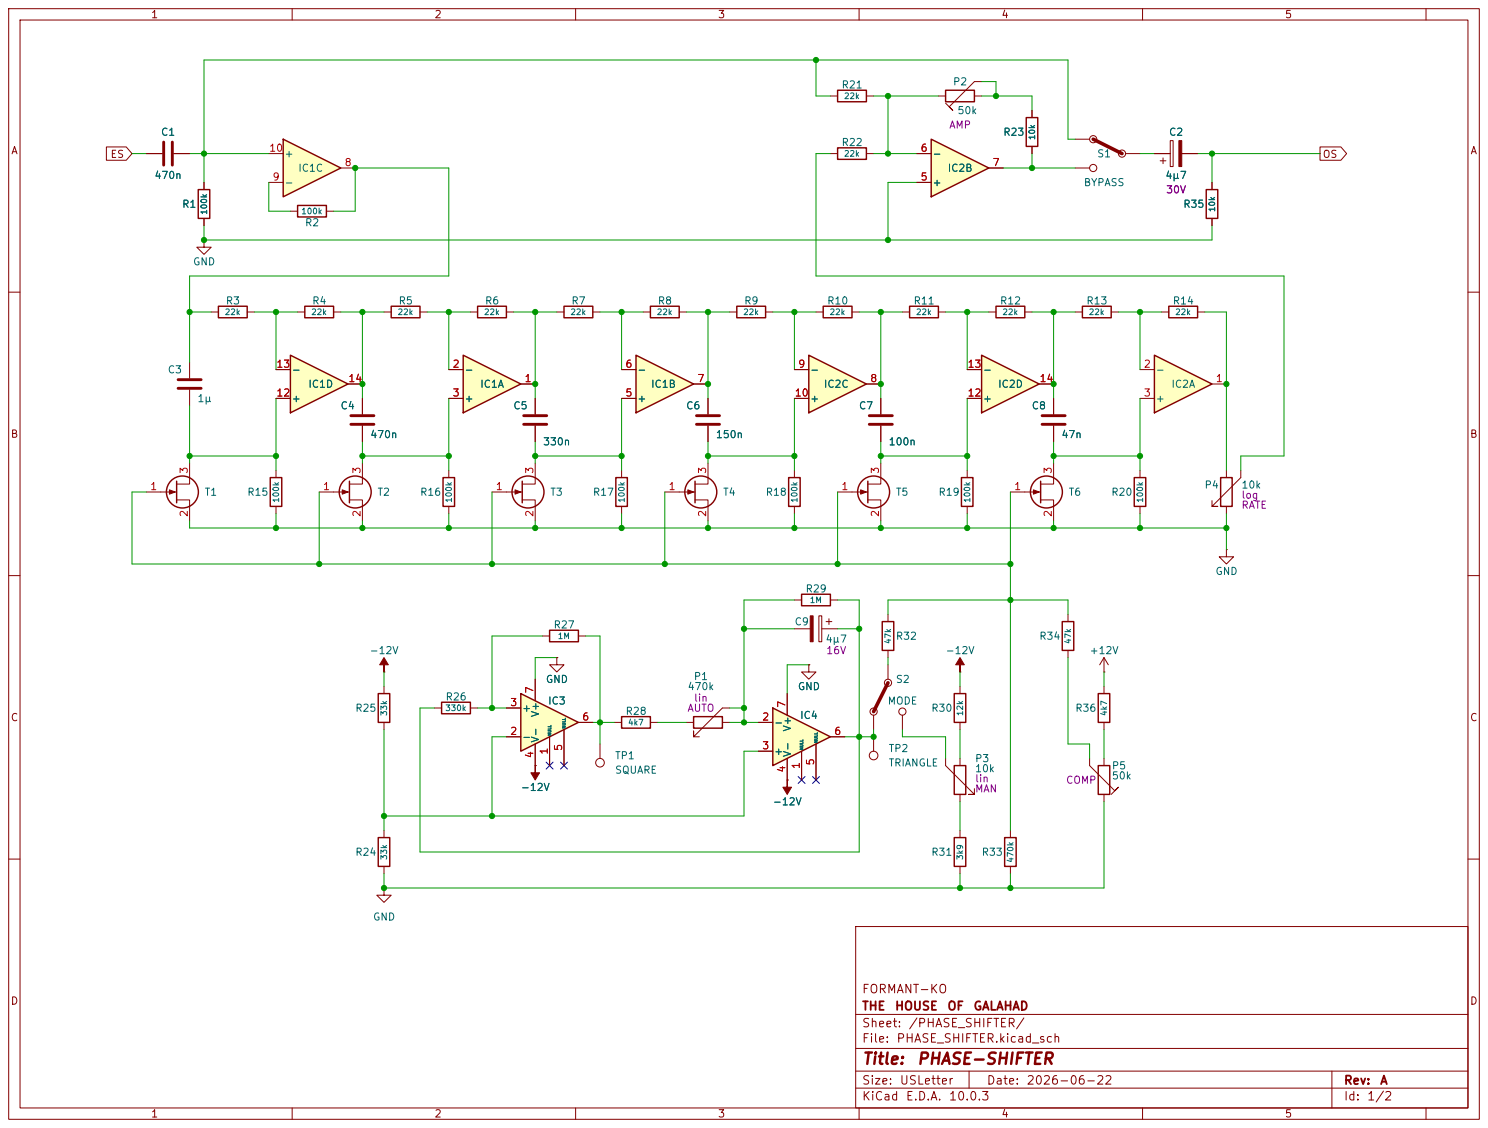
[picture p332: page 1]

FORMANT-KO
THE HOUSE OF GALAHAD
Sheet: /PHASE_SHIFTER/
File: PHASE_SHIFTER.kicad_sch
Title: PHASE-SHIFTER

Size: USLetter | Rev: A
KiCad E.D.A. 10.0.3 | Id: 1/2

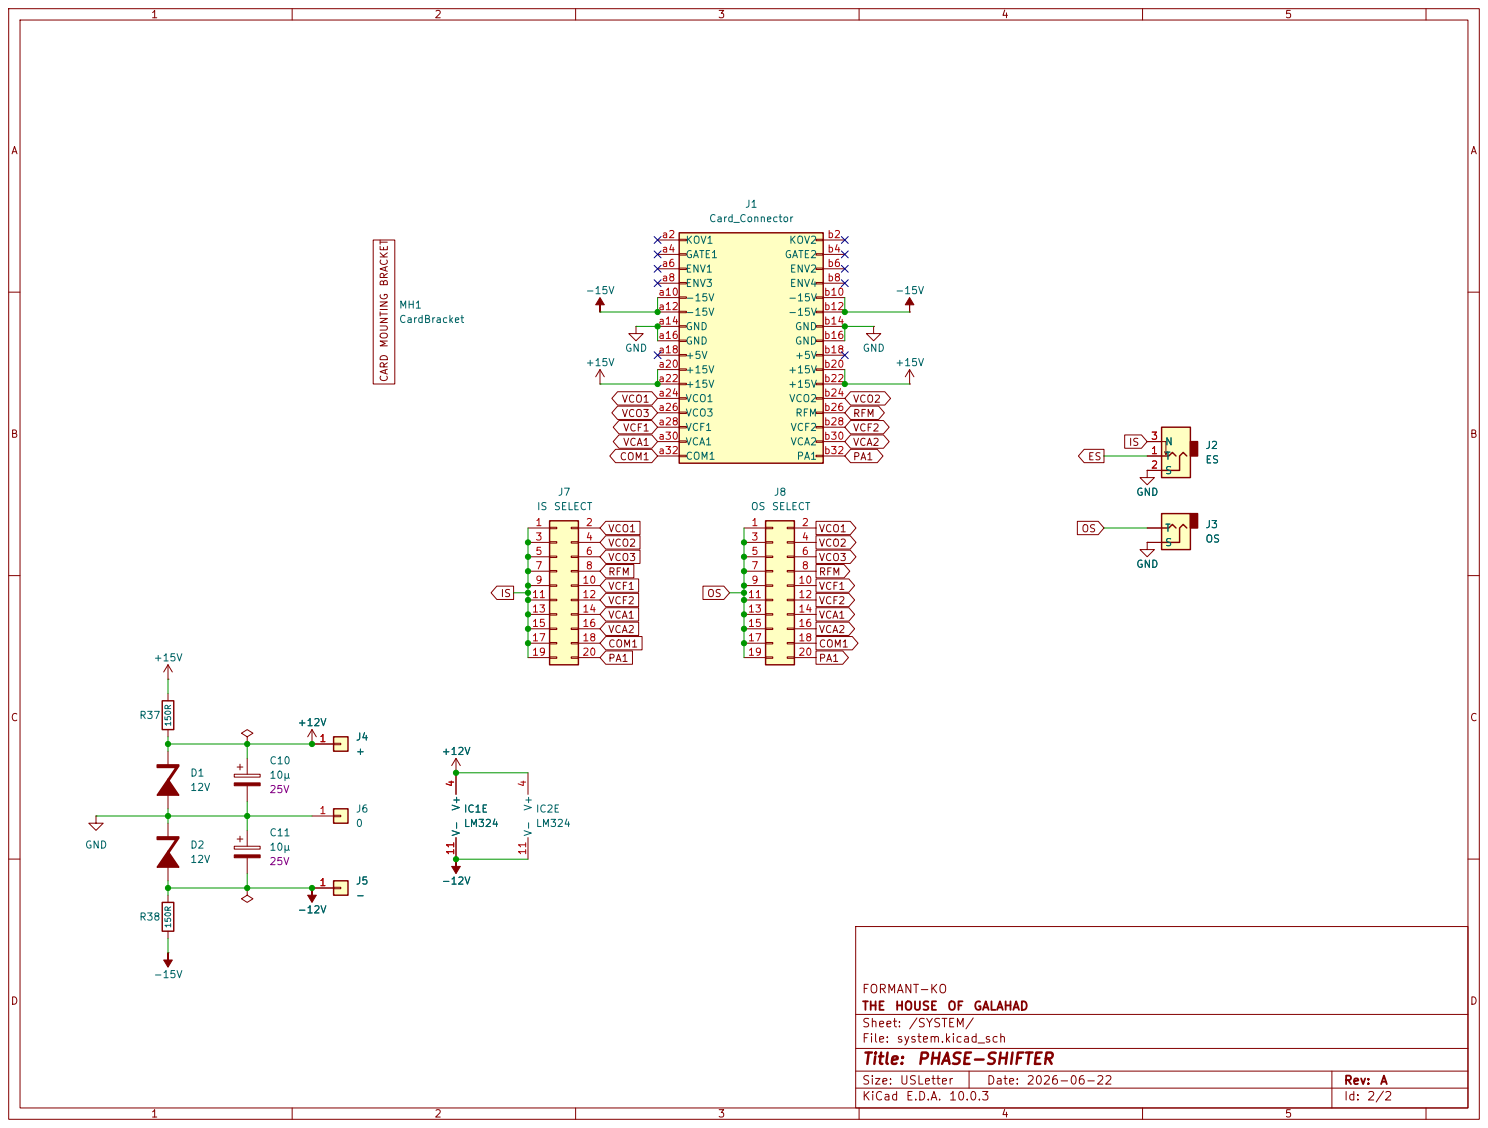
[picture p333: page 2]

9 | 10

13 | 14
15 | 16
17 | 18
19 | 20

THE HOUSE OF GALAHAD
Sheet: /SYSTEM/
File: system.kicad_sch
Title: PHASE-SHIFTER

Size: USLetter | Rev: A
KiCad E.D.A. 10.0.3 | Id: 2/2
