Desval27/FormantKO/modules/RING_MODULATOR/RING_MODULATOR.pdf

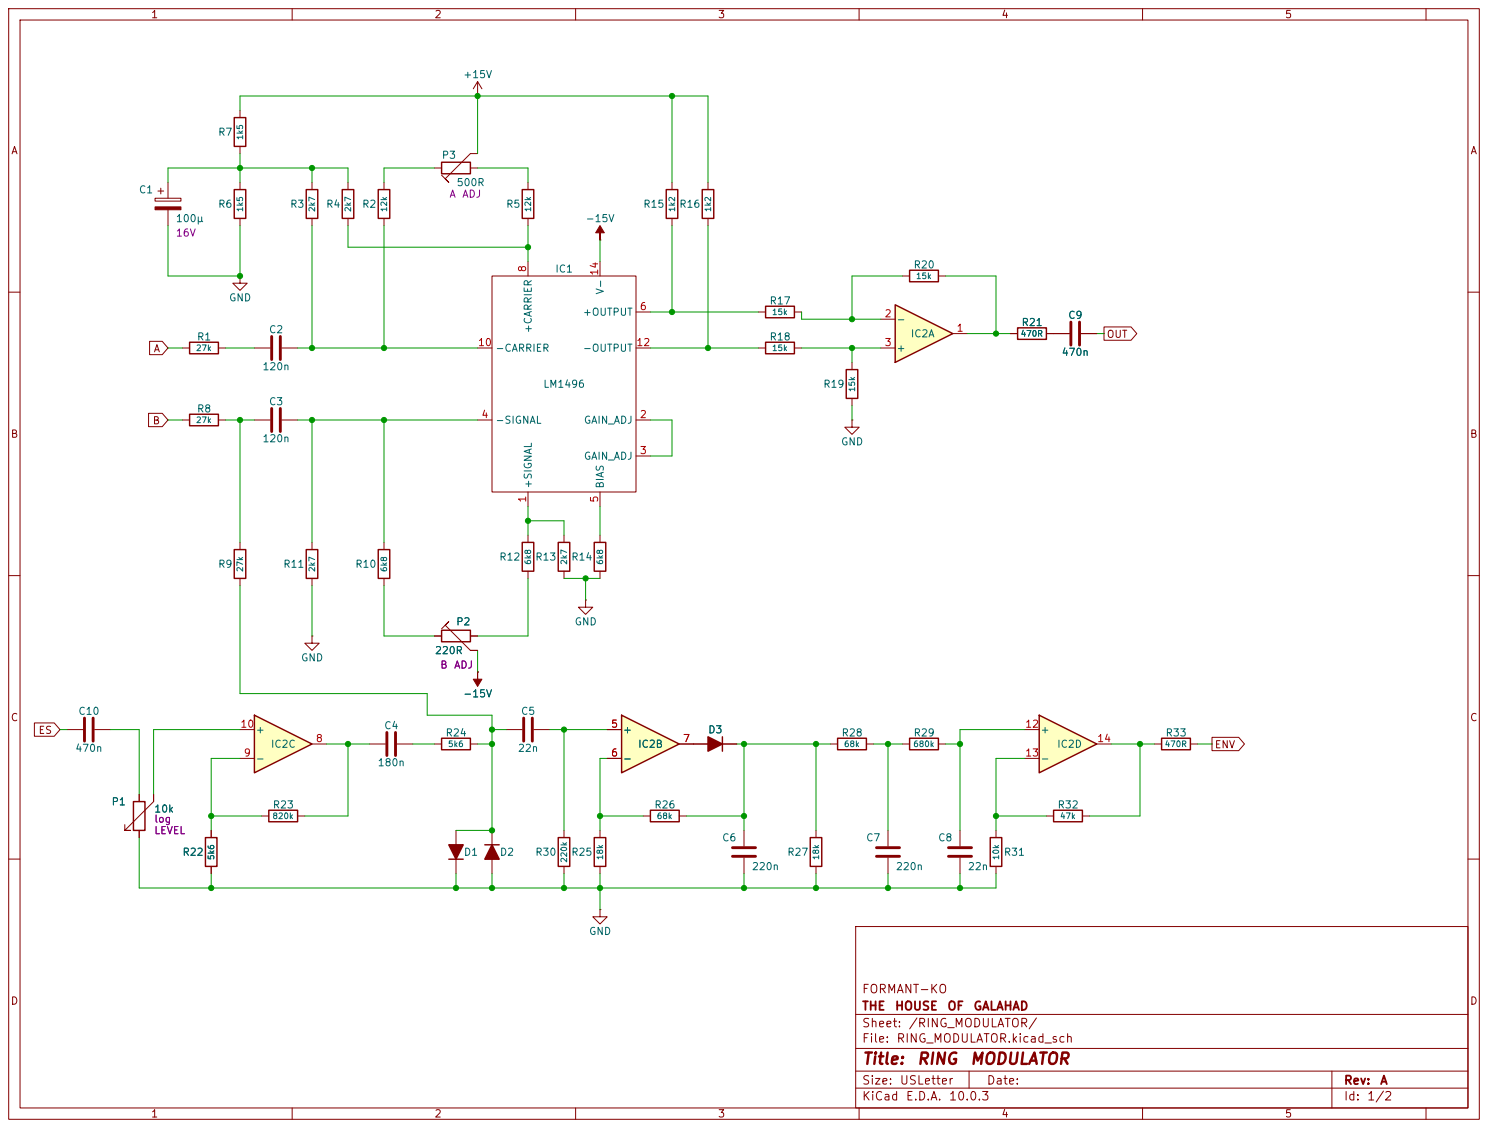
[picture p334: page 1]

THE HOUSE OF GALAHAD
Sheet: /RING_MODULATOR/
File: RING_MODULATOR.kicad_sch
Title: RING MODULATOR

Size: USLetter | Rev: A
KiCad E.D.A. 10.0.3 | Id: 1/2
