Desval27/FormantKO/modules/NOISE_CNC/NOISE_CNC.pdf

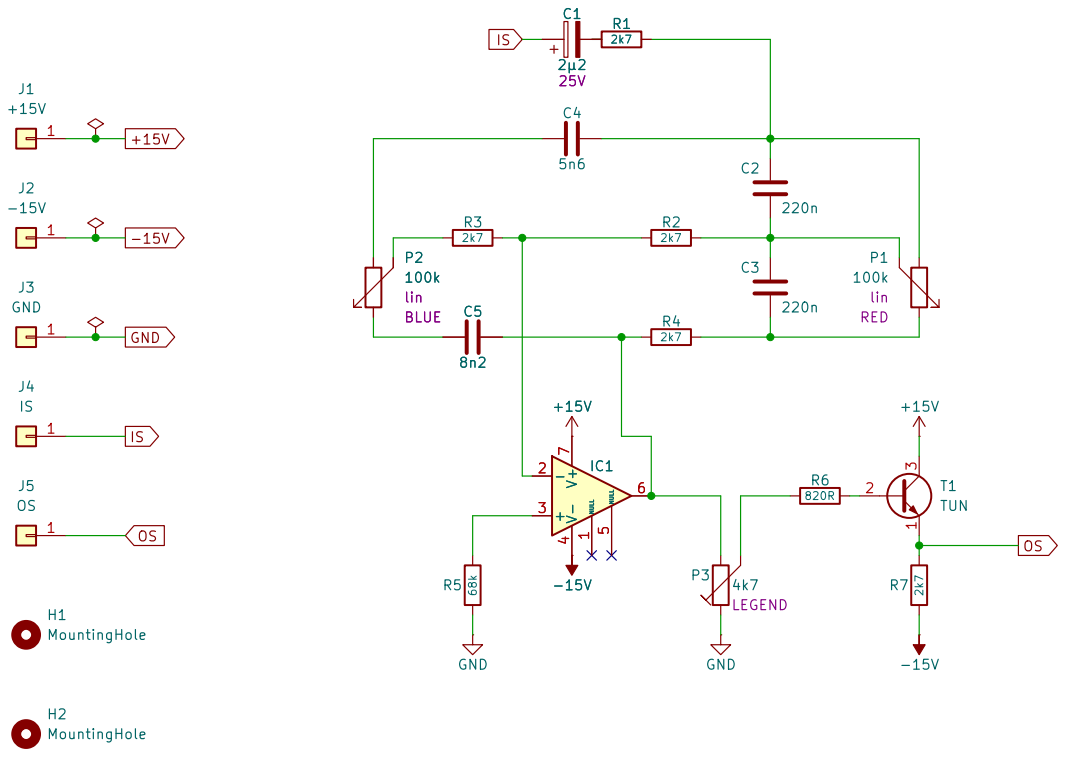
[picture p335: page 1]

FORMANT-KO
THE HOUSE OF GALAHAD
Sheet: /
File: NOISE_CNC.kicad_sch
Title: NOISE EXTENSION - COLOURED NOISE CONTROL

Size: USLetter | Rev: A
KiCad E.D.A. 10.0.3 | Id: 1/1
