Desval27/FormantKO/system/KB_DIV/KB_DIV.pdf

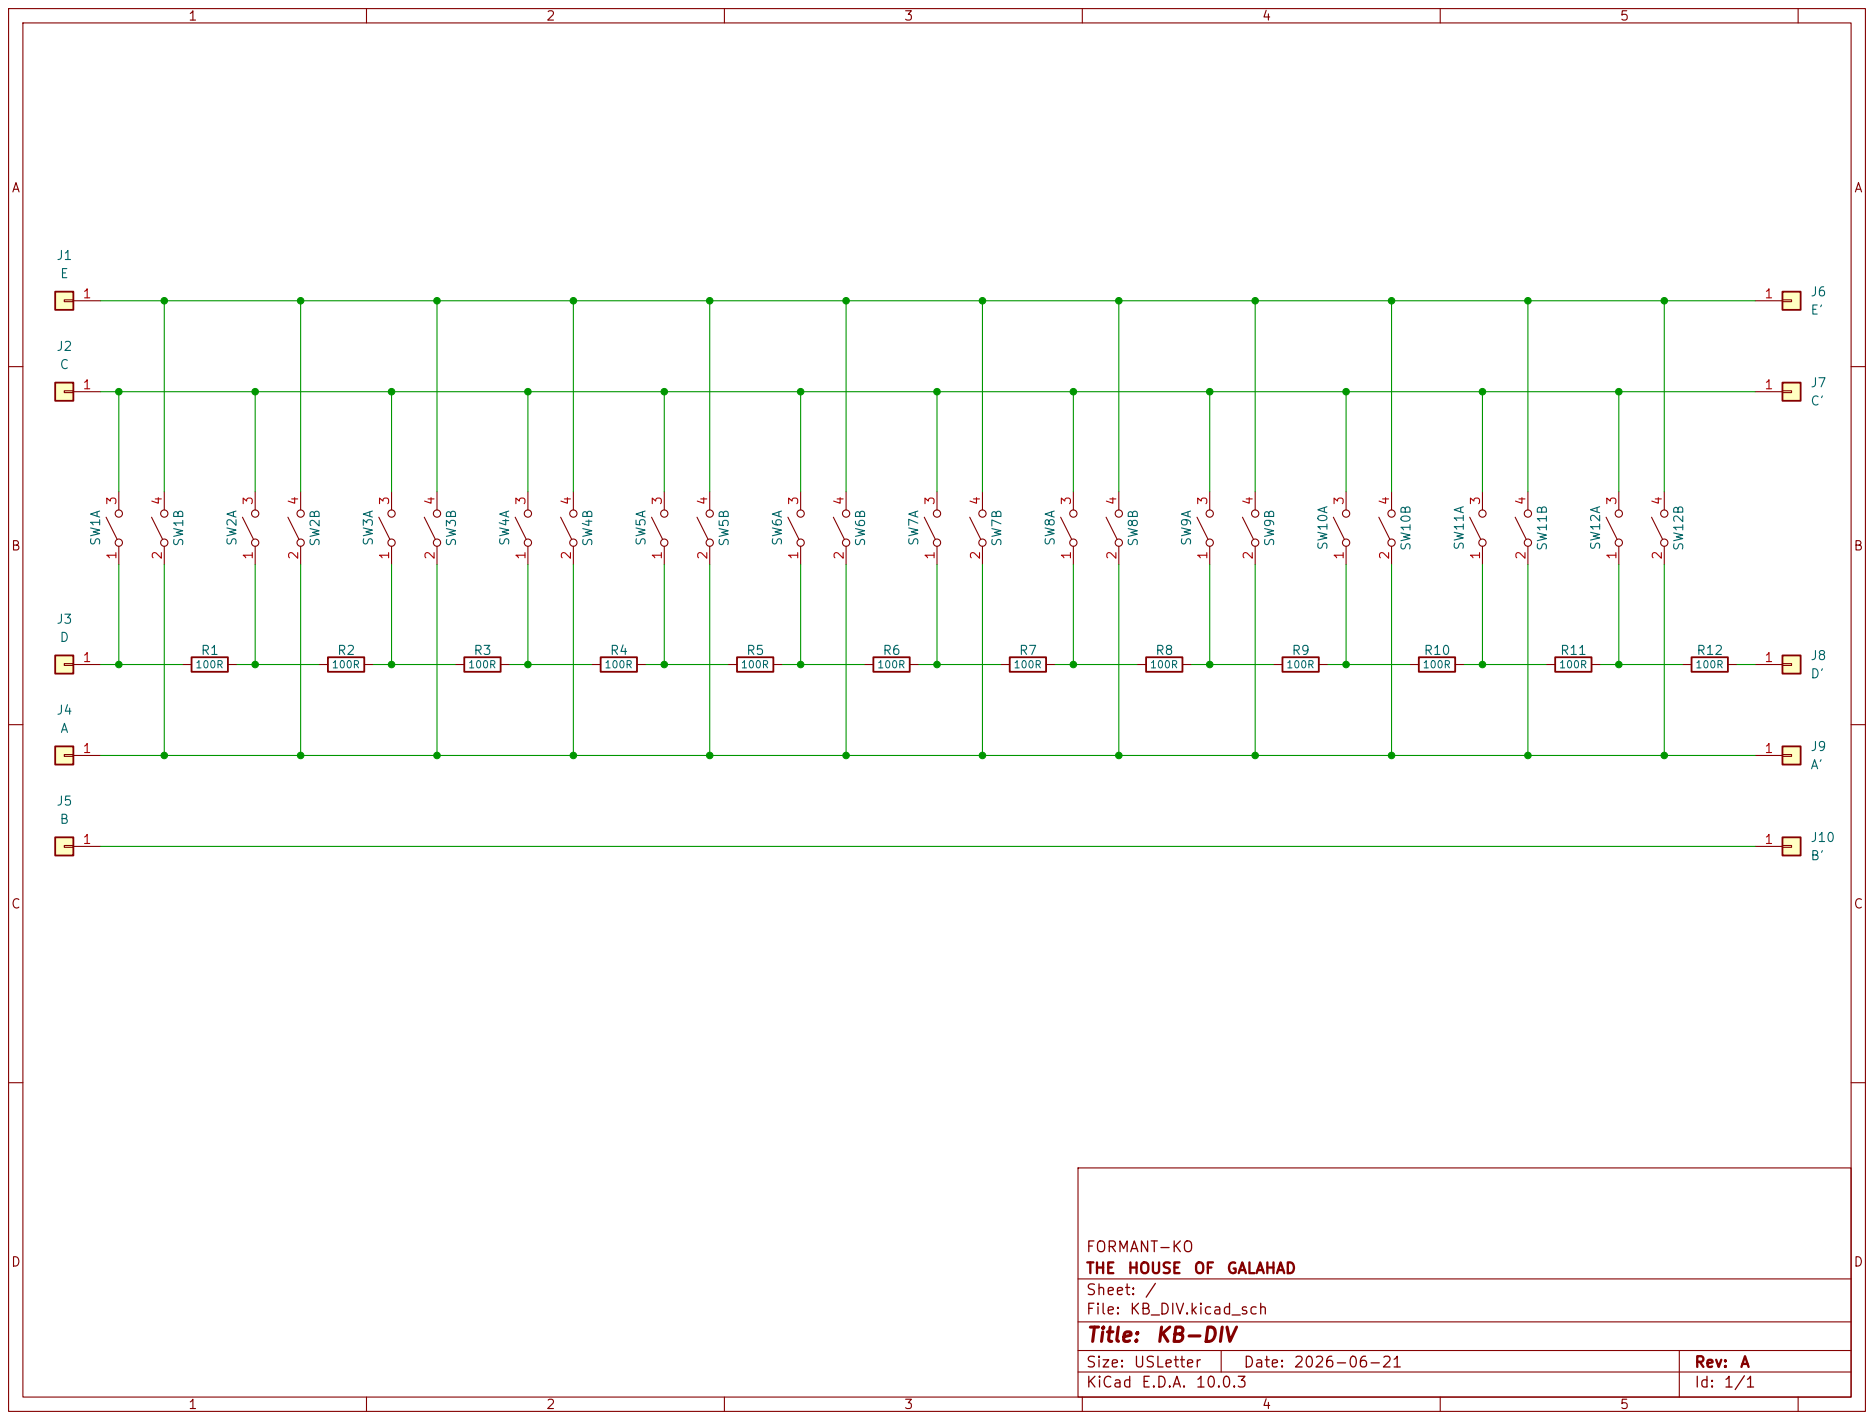
[picture p336: page 1]

FORMANT-KO
THE HOUSE OF GALAHAD
Sheet: /
File: KB_DIV.kicad_sch
Title: KB-DIV

Size: USLetter | Rev: A
KiCad E.D.A. 10.0.3 | Id: 1/1
