Desval27/FormantKO/MFOS/modules/CLOCK/CLOCK.pdf

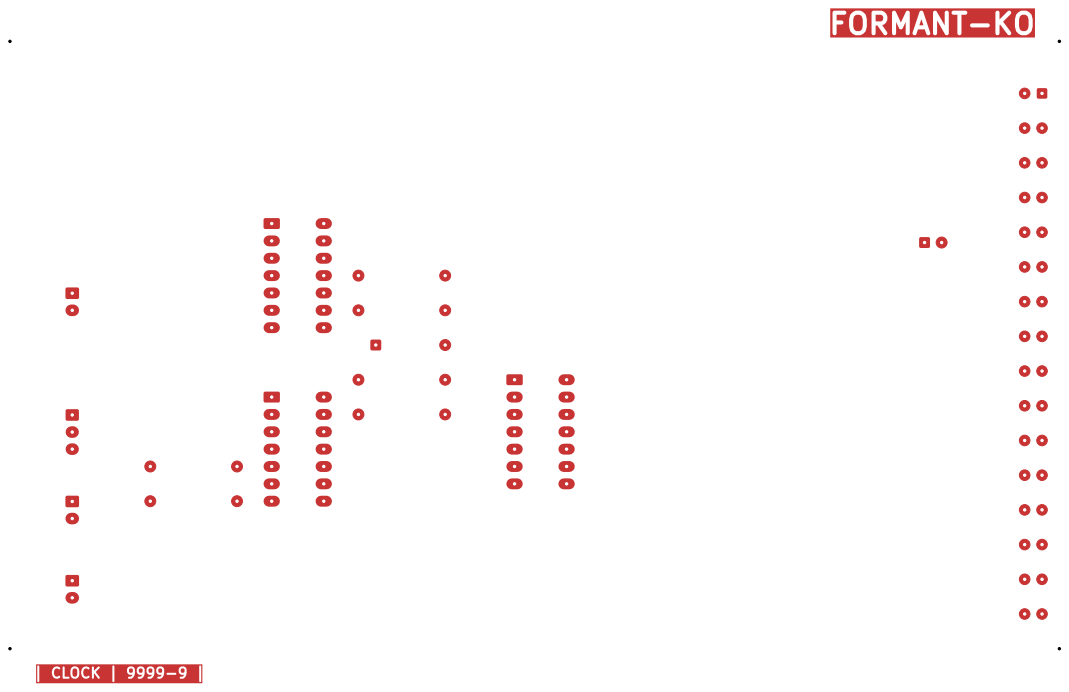
[picture p337: page 1]

SEQUENCER
FORMANT-KO
THE HOUSE OF GALAHAD
Sheet:
File: CLOCK.kicad_pcb
Title: CLOCK

Size: USLetter | Rev: A
KiCad E.D.A. 10.0.4 | Id: 1/4

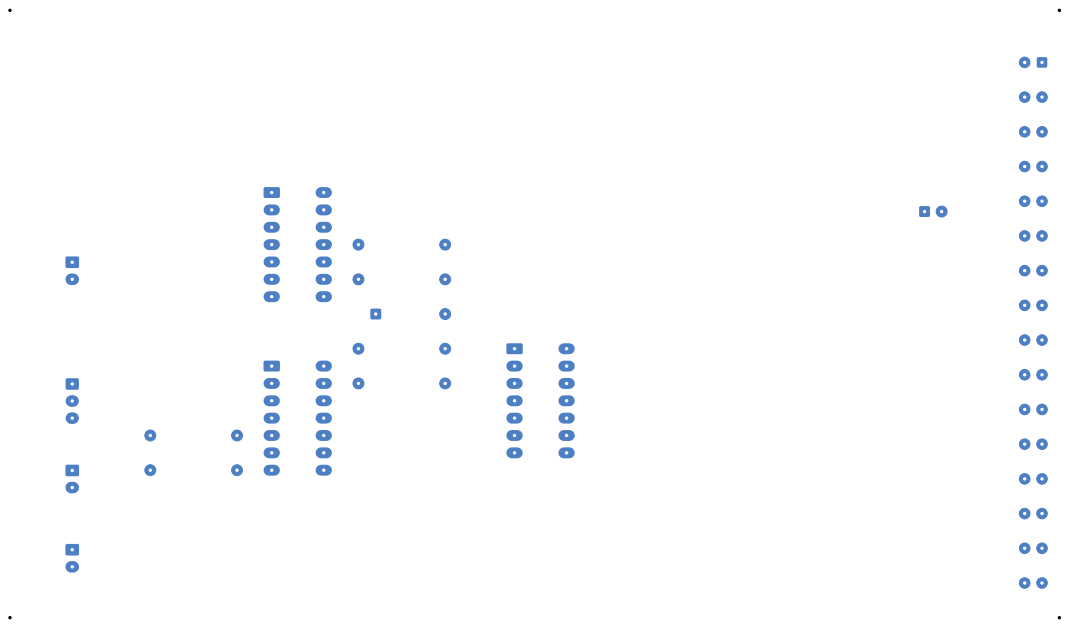
[picture p338: page 2]

SEQUENCER
FORMANT-KO
THE HOUSE OF GALAHAD
Sheet:
File: CLOCK.kicad_pcb
Title: CLOCK

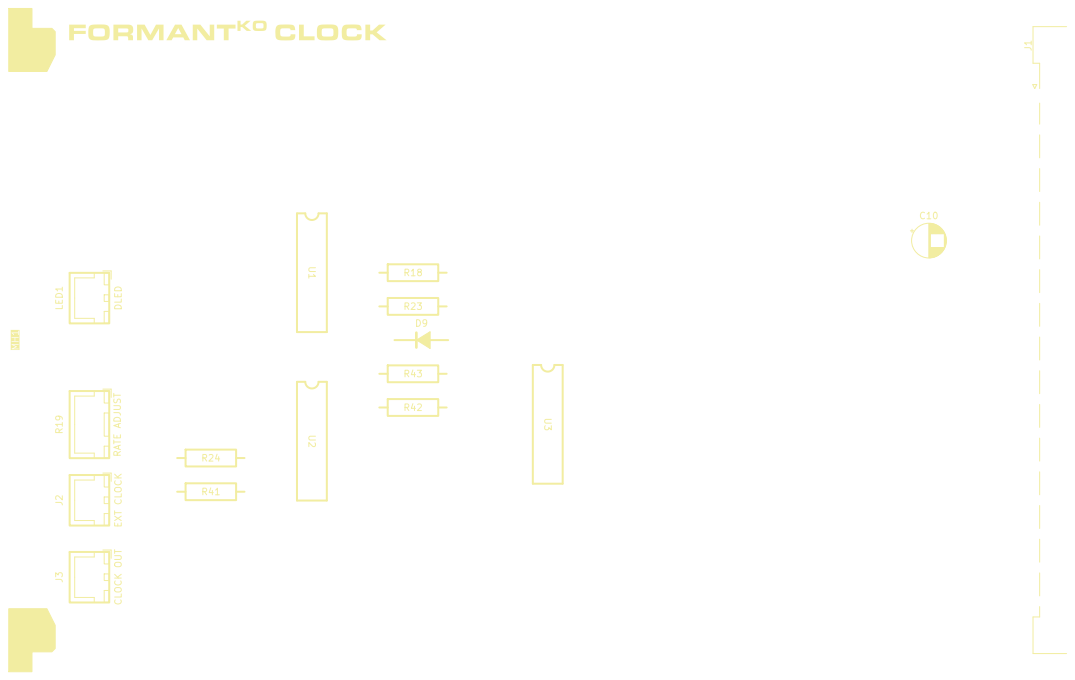
[picture p339: page 3]

FORMANT-KO
THE HOUSE OF GALAHAD
Sheet:
File: CLOCK.kicad_pcb
Title: CLOCK

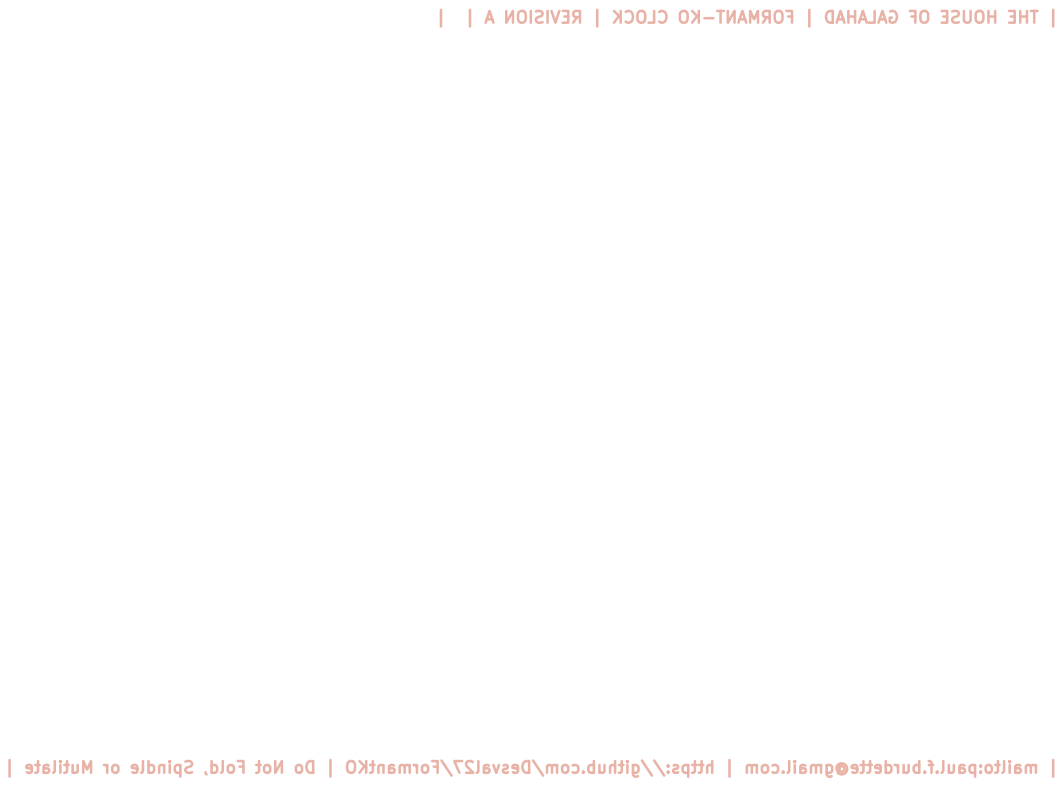
[picture p340: page 4]

SEQUENCER
FORMANT-KO
THE HOUSE OF GALAHAD
Sheet:
File: CLOCK.kicad_pcb
Title: CLOCK
